groverlab/disintegration-fingerprinting/data/aspirin.png

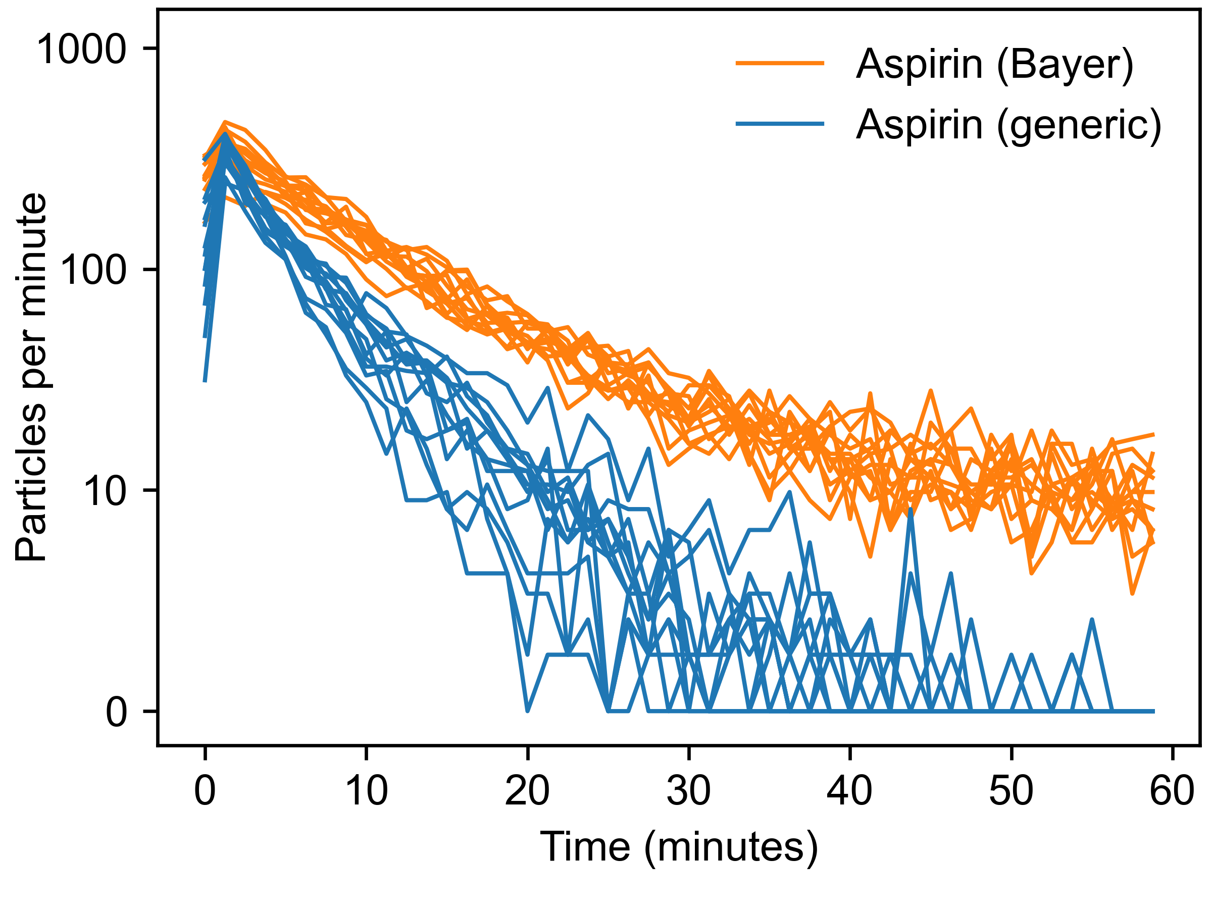
data/aspirin.png
