groverlab/disintegration-fingerprinting/data/aspirin_heatmap.png

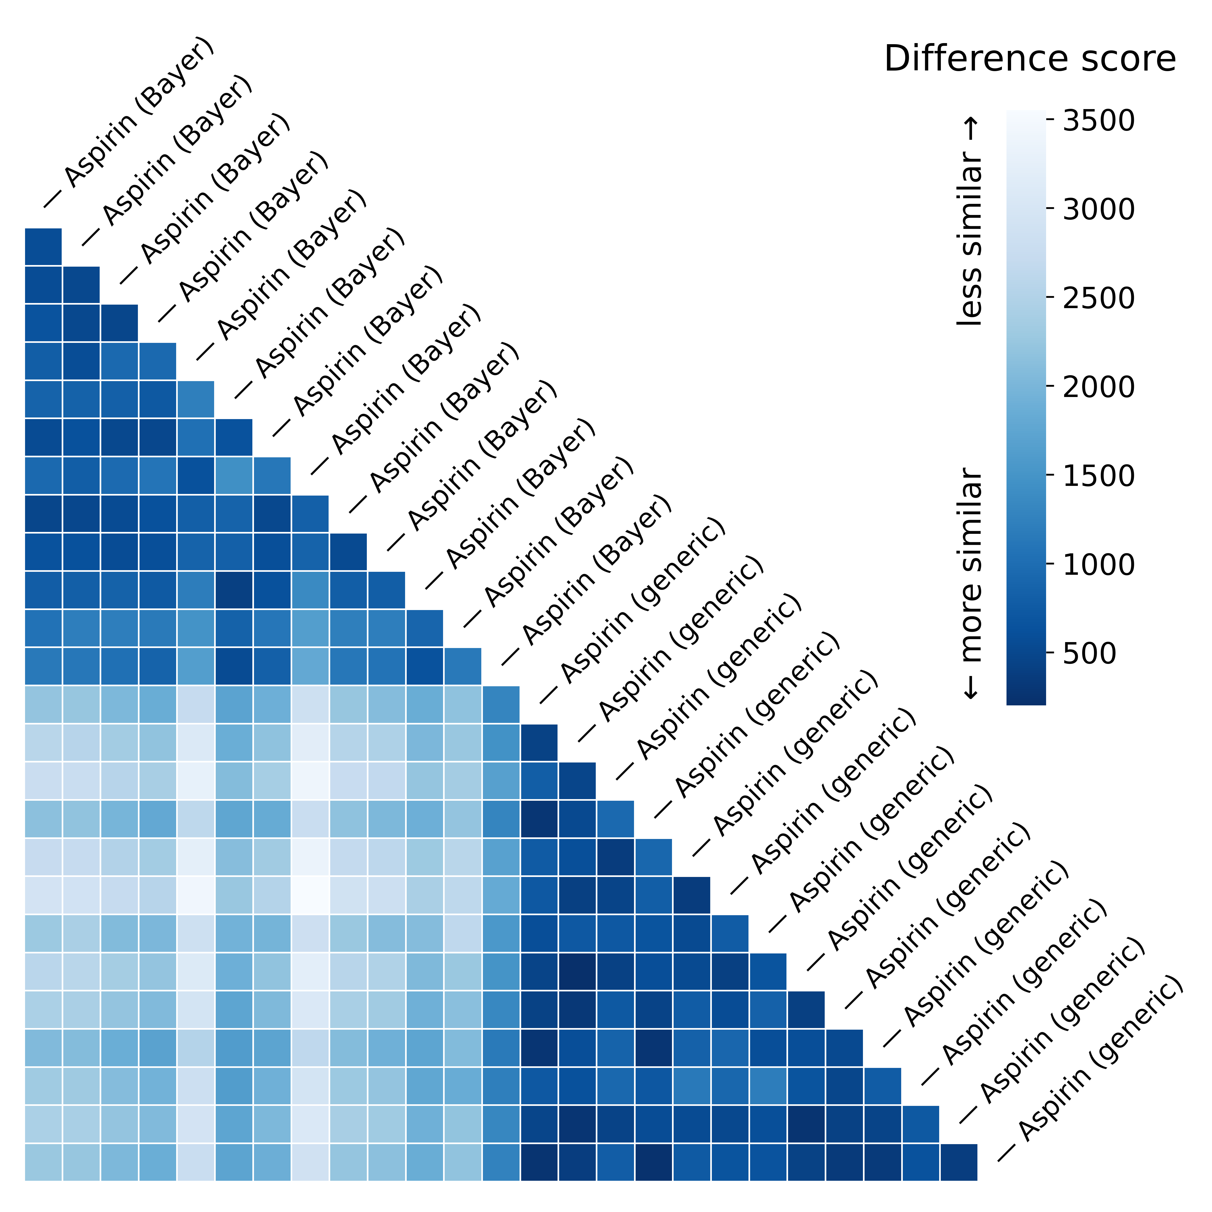
data/aspirin_heatmap.png
