groverlab/disintegration-fingerprinting/data/aspirin_significance.png

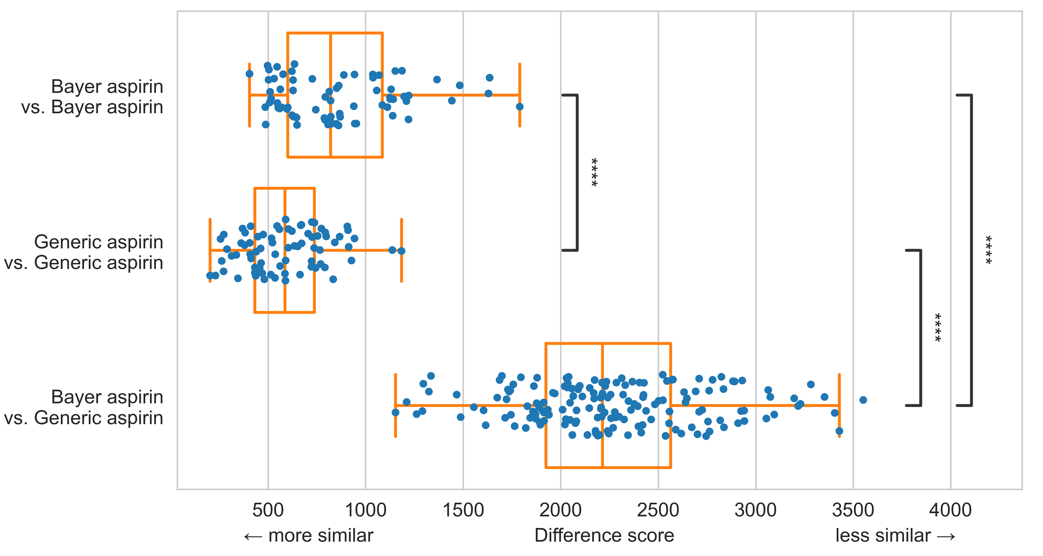
data/aspirin_significance.png
