groverlab/disintegration-fingerprinting/data/bayer_tylenol/101 20251124T124538_T16one TCANADA.json.gz.png

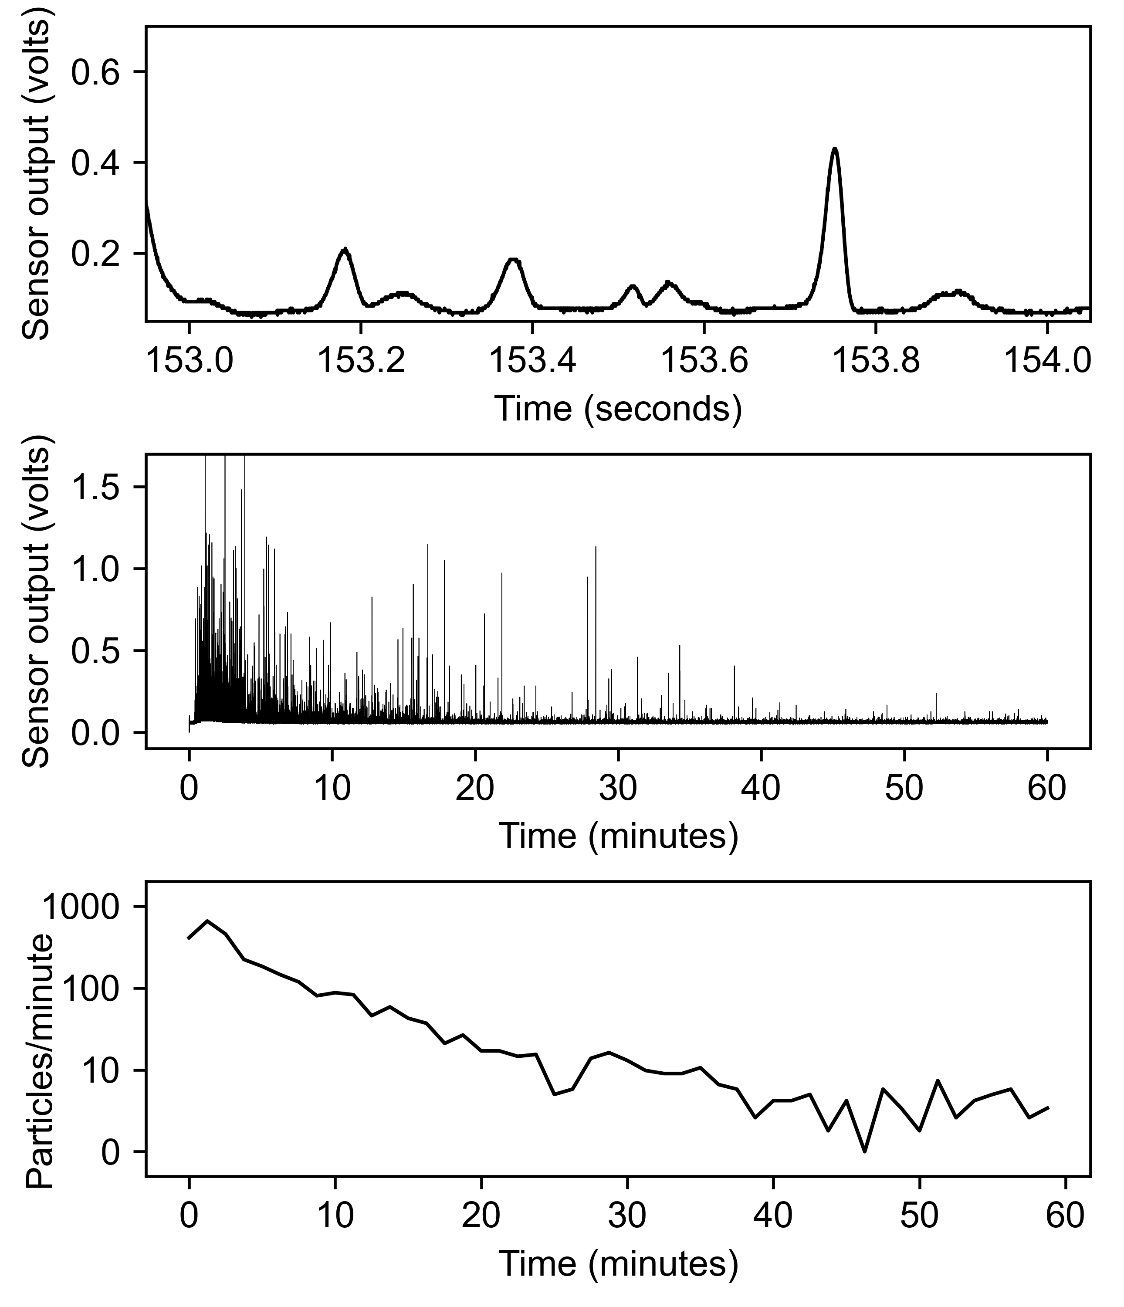
data/bayer_tylenol/101 20251124T124538_T16one TCANADA.json.gz.png
