groverlab/disintegration-fingerprinting/data/bayer_tylenol/102 20251113T170126_T02one TRT.json.gz.png

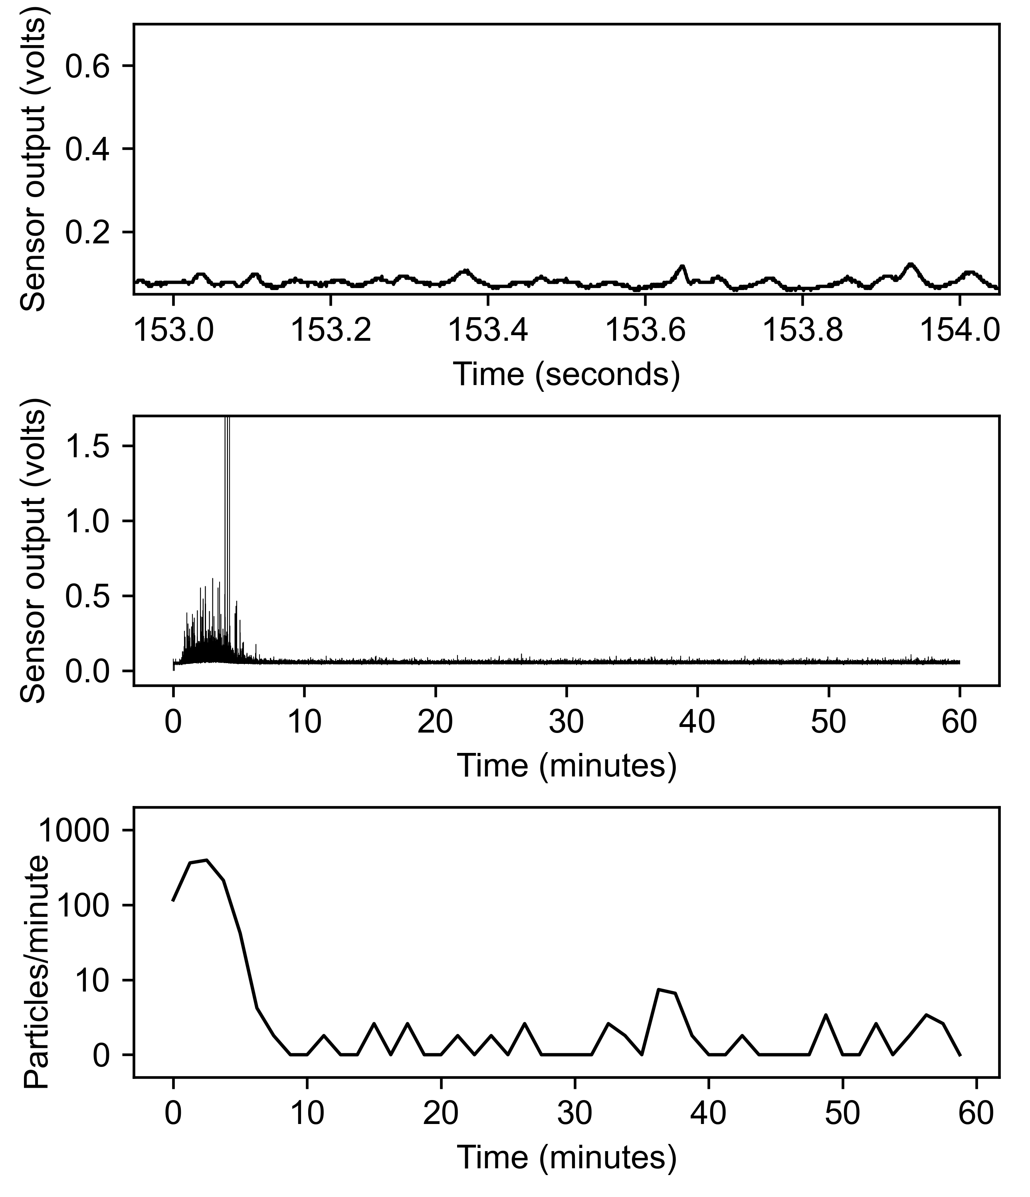
data/bayer_tylenol/102 20251113T170126_T02one TRT.json.gz.png
