groverlab/disintegration-fingerprinting/data/bayer_tylenol/103 20251124T112431_T15one TRT.json.gz.png

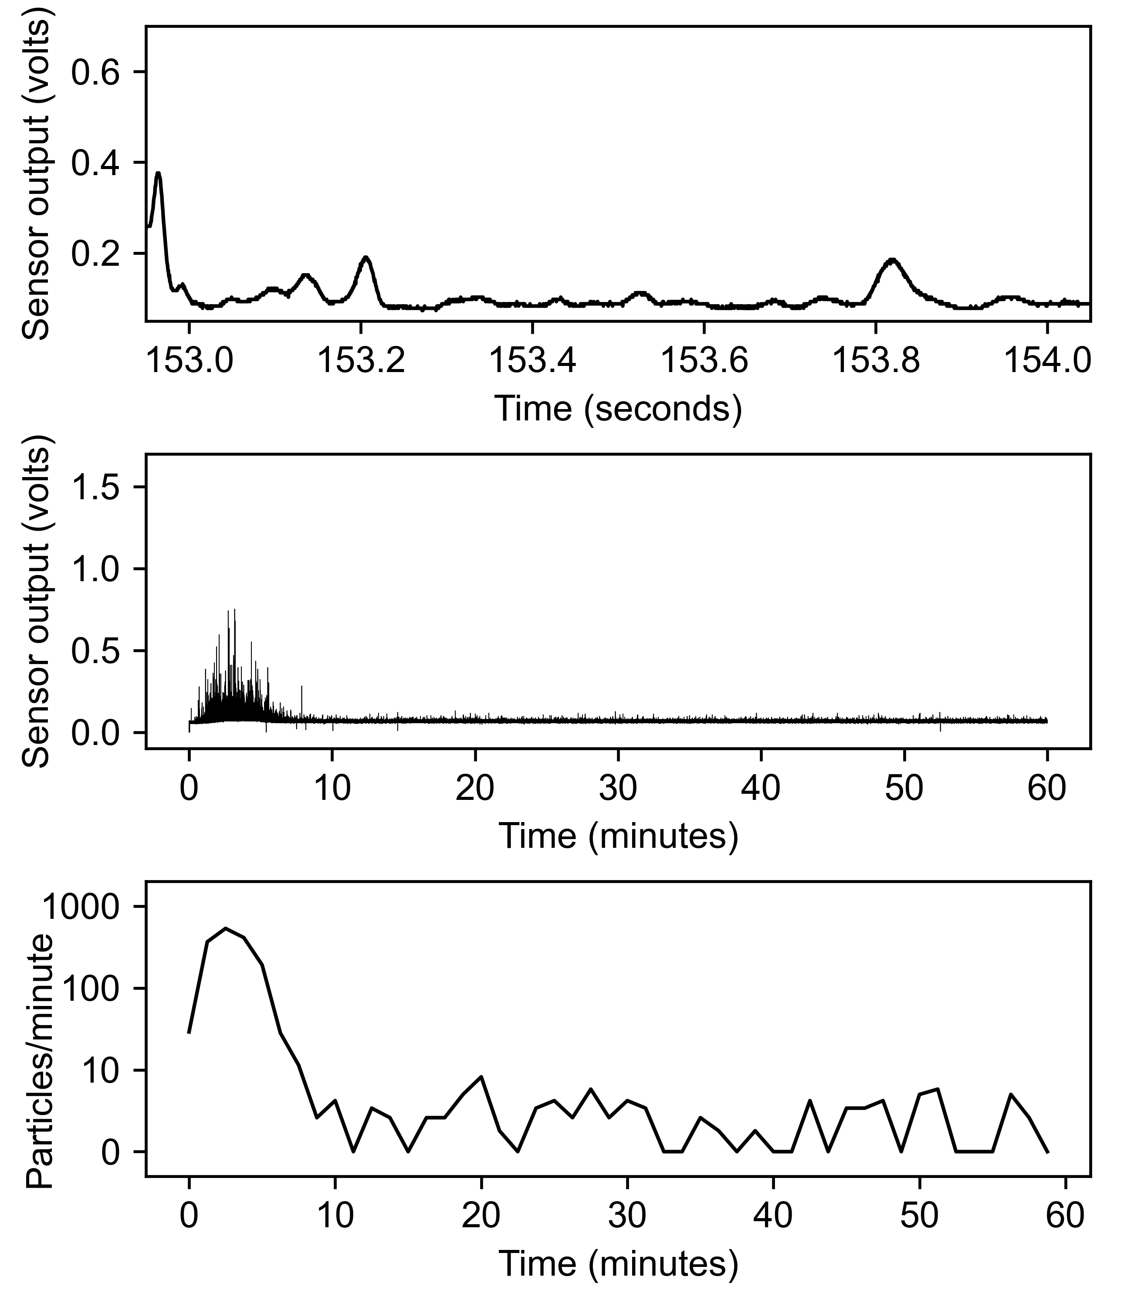
data/bayer_tylenol/103 20251124T112431_T15one TRT.json.gz.png
