groverlab/disintegration-fingerprinting/data/bayer_tylenol/104 20251118T150120_T08one TRT.json.gz.png

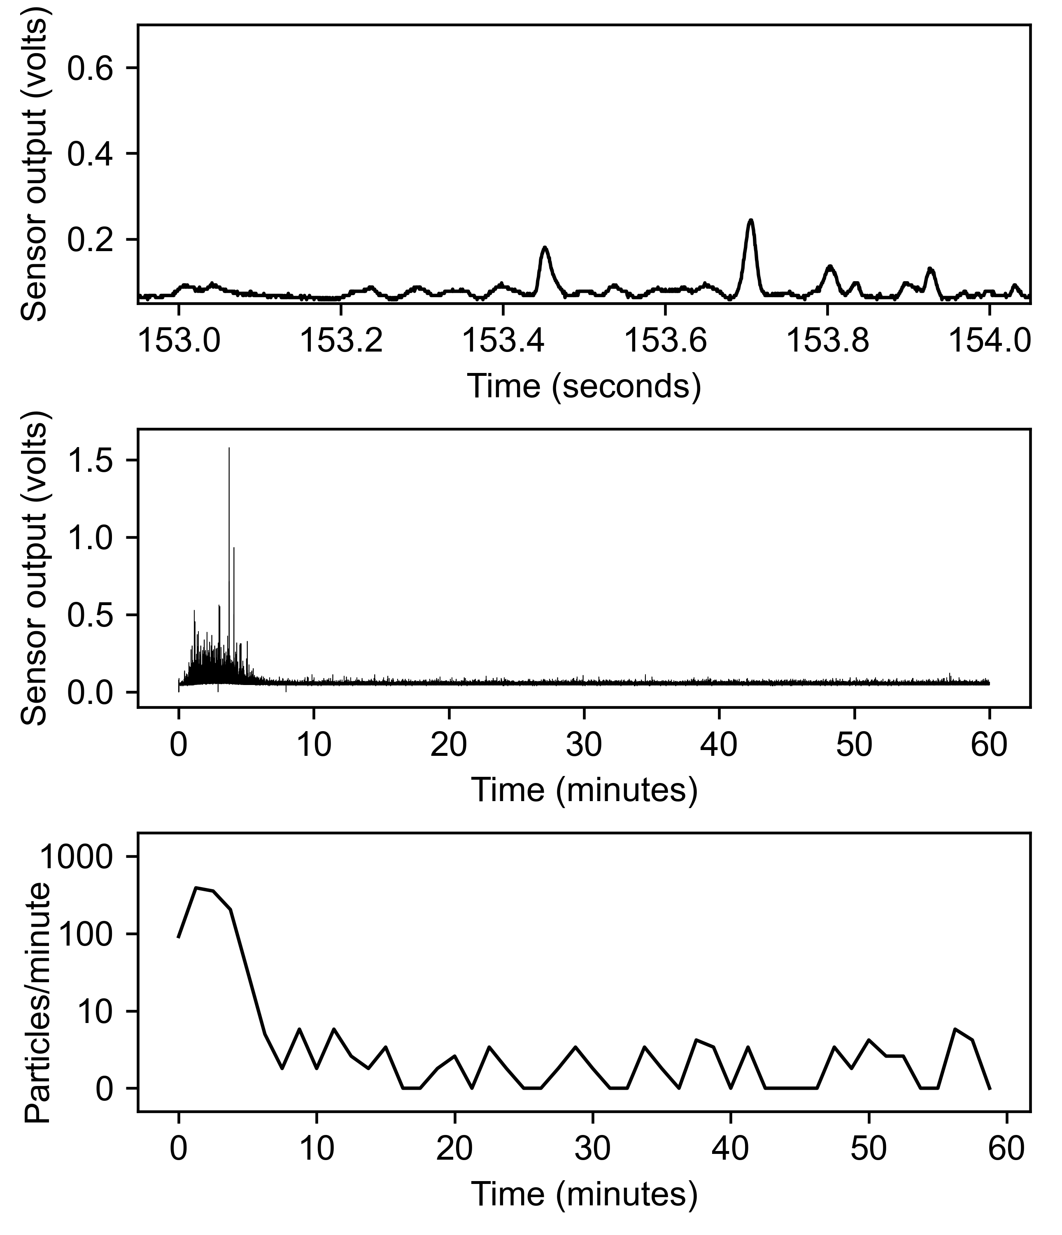
data/bayer_tylenol/104 20251118T150120_T08one TRT.json.gz.png
