groverlab/disintegration-fingerprinting/data/bayer_tylenol/105 20260107T104635_T13two TRT.json.gz.png

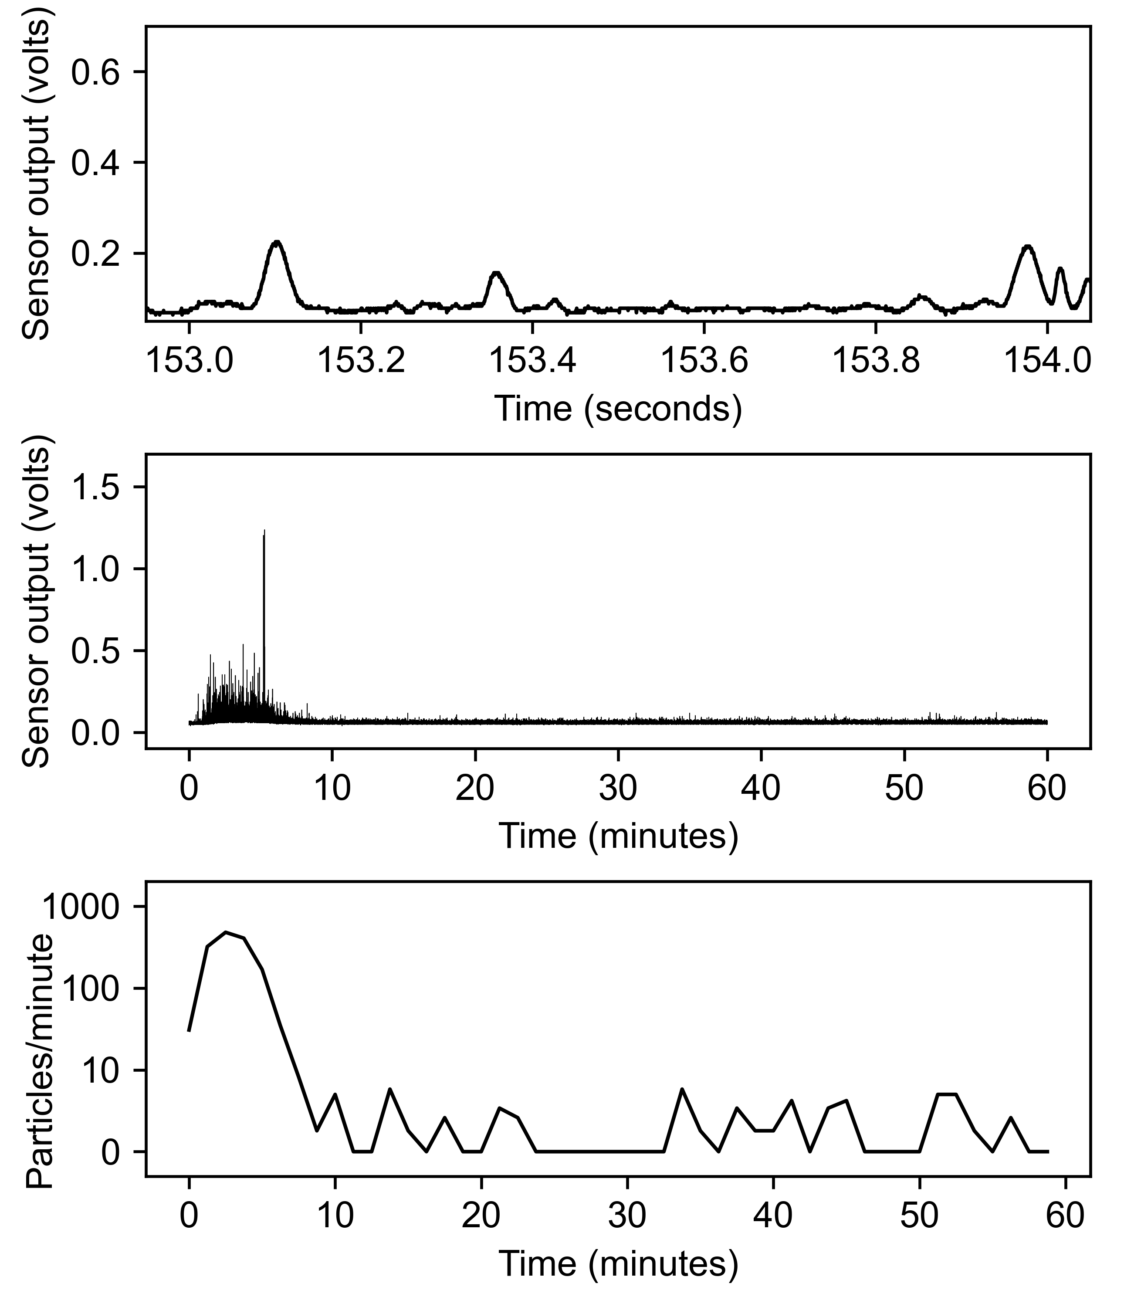
data/bayer_tylenol/105 20260107T104635_T13two TRT.json.gz.png
