groverlab/disintegration-fingerprinting/data/bayer_tylenol/106 20251117T124159_T05one TRT.json.gz.png

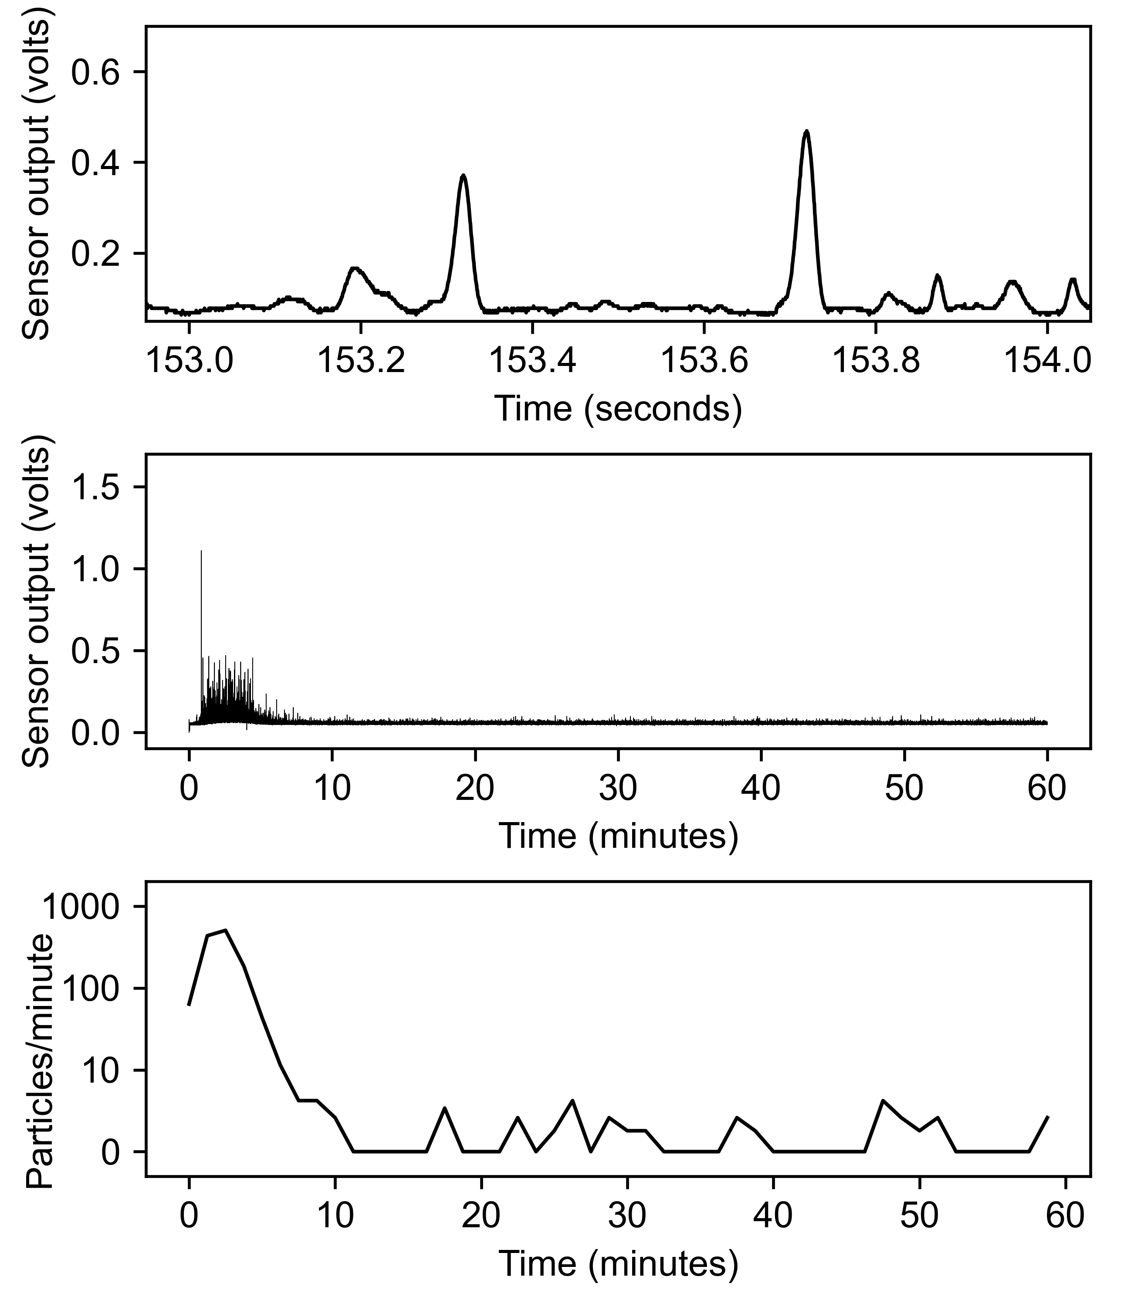
data/bayer_tylenol/106 20251117T124159_T05one TRT.json.gz.png
