groverlab/disintegration-fingerprinting/data/bayer_tylenol/107 20251118T134538_T07one TRT.json.gz.png

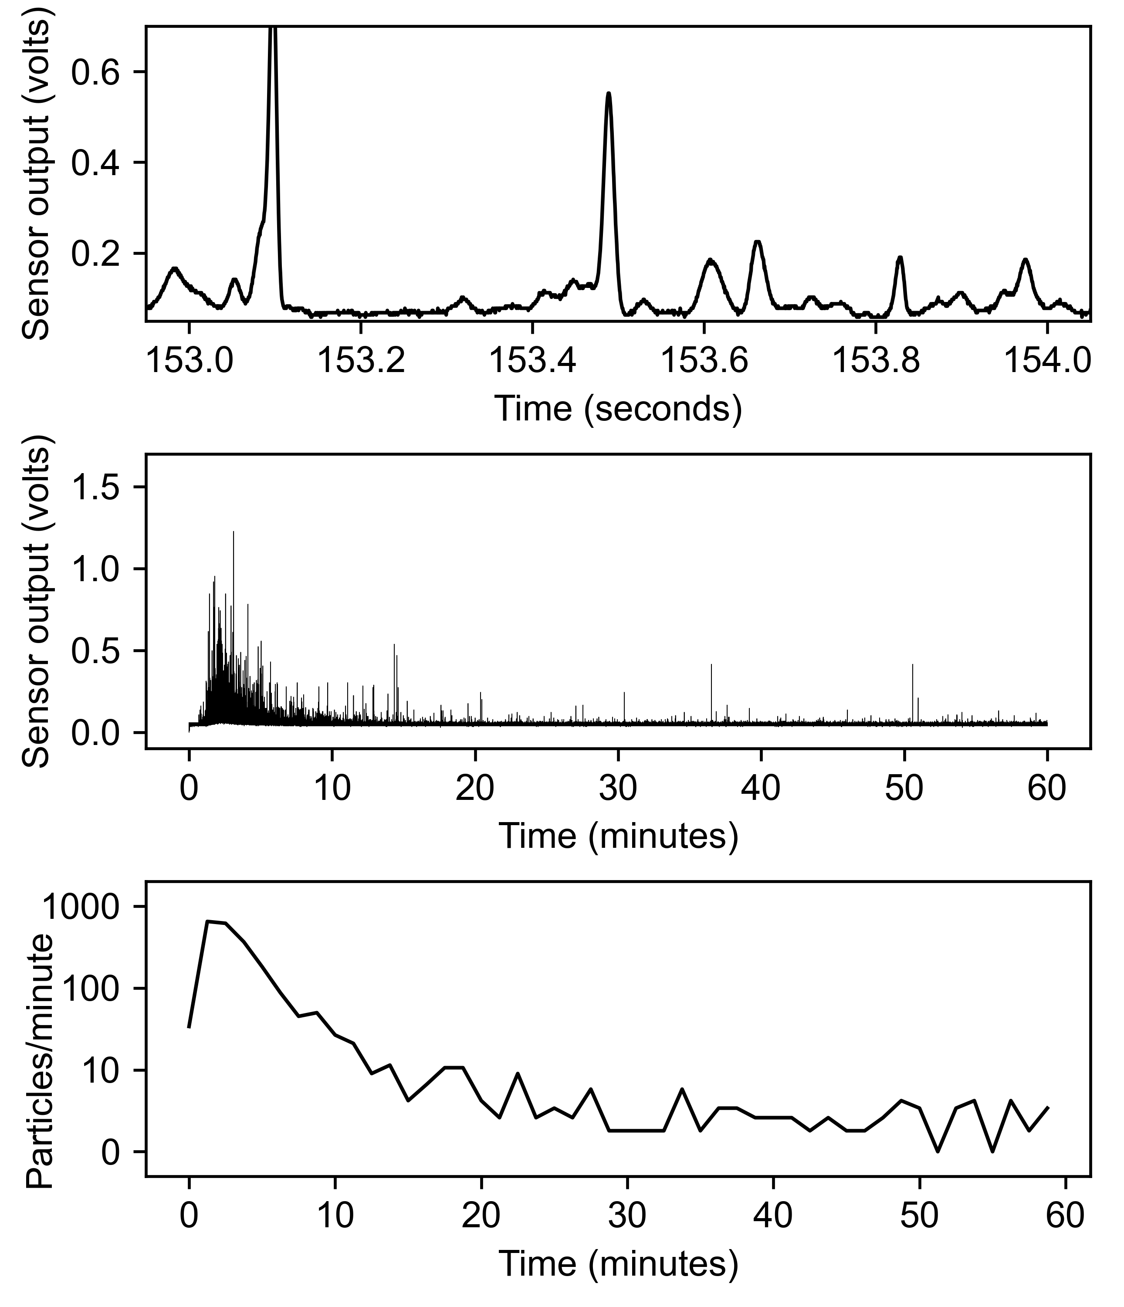
data/bayer_tylenol/107 20251118T134538_T07one TRT.json.gz.png
