groverlab/disintegration-fingerprinting/data/bayer_tylenol/108 20251124T135557_T17one TCANADA.json.gz.png

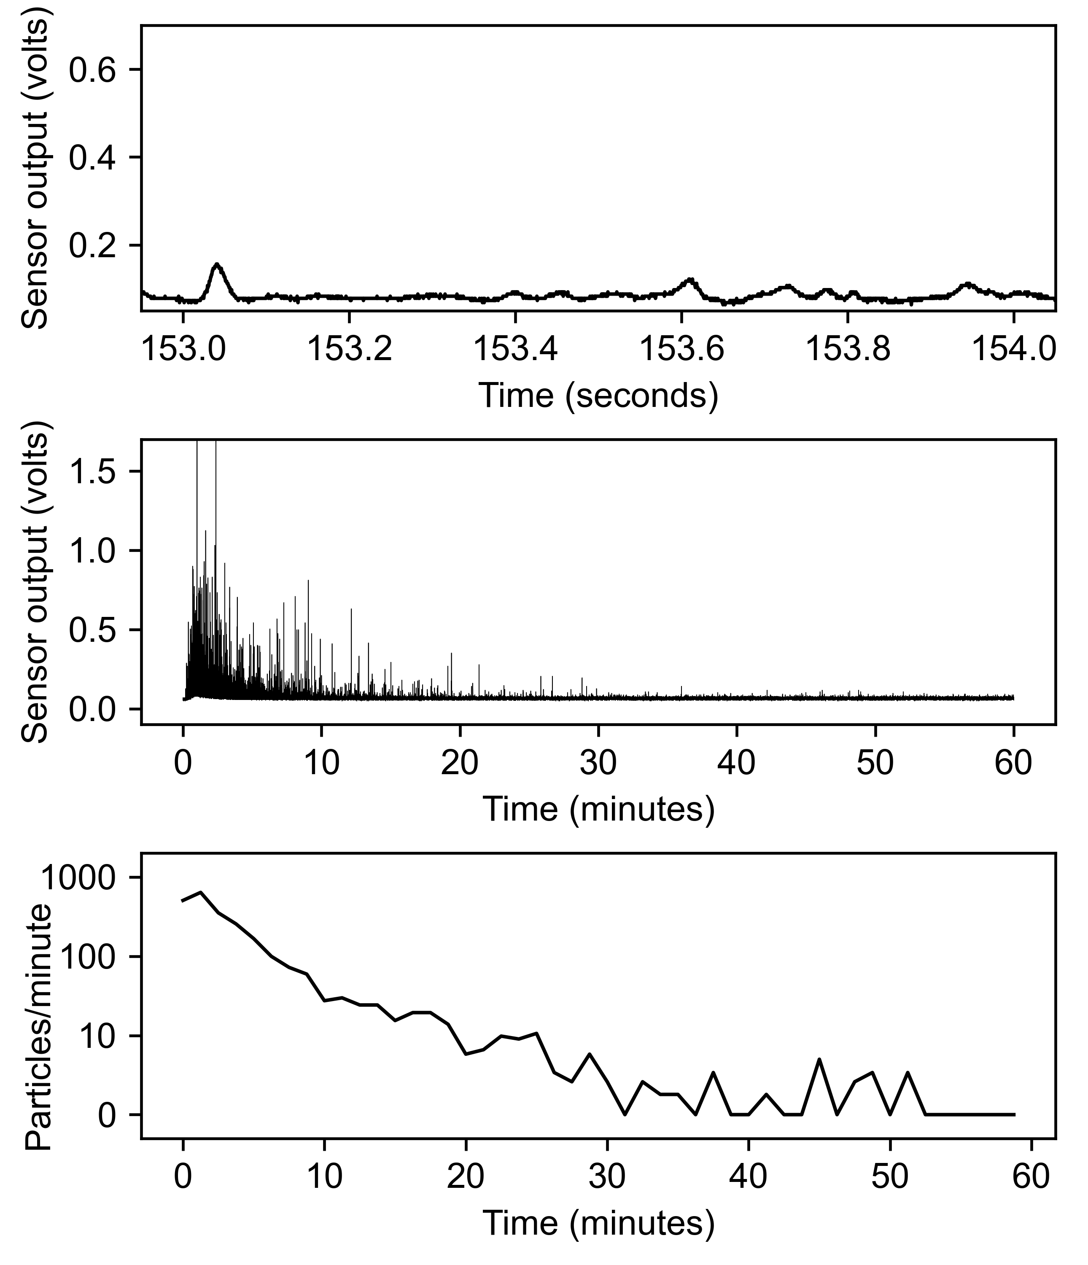
data/bayer_tylenol/108 20251124T135557_T17one TCANADA.json.gz.png
