groverlab/disintegration-fingerprinting/data/bayer_tylenol/109 20251118T123829_T06one TRT.json.gz.png

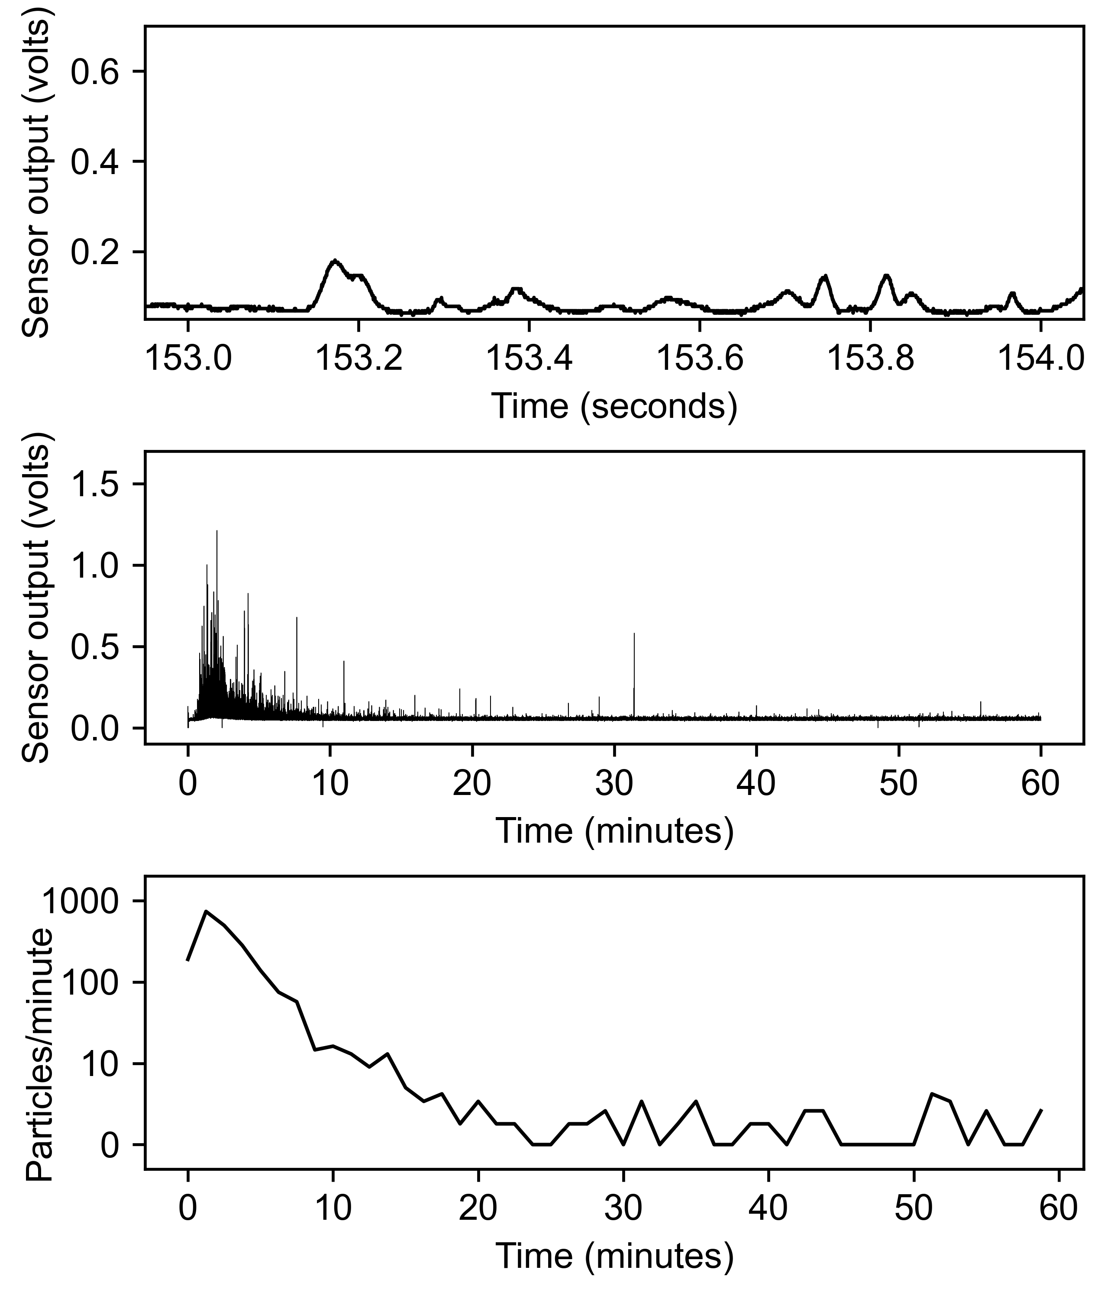
data/bayer_tylenol/109 20251118T123829_T06one TRT.json.gz.png
