groverlab/disintegration-fingerprinting/data/bayer_tylenol/110 20251117T112834_T04one TRT.json.gz.png

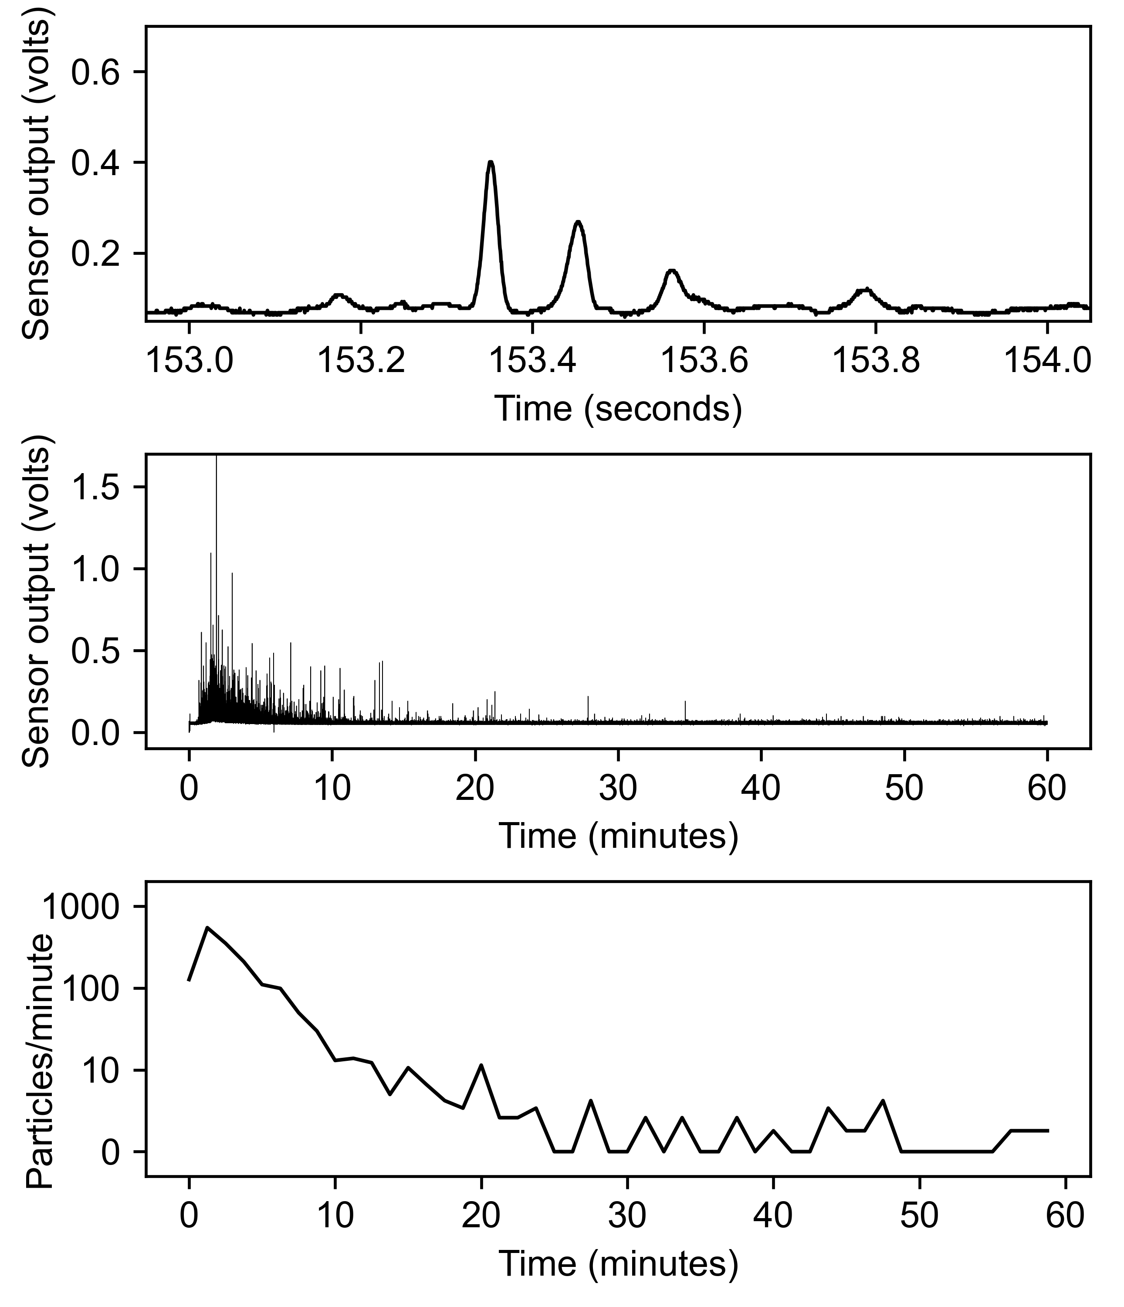
data/bayer_tylenol/110 20251117T112834_T04one TRT.json.gz.png
