groverlab/disintegration-fingerprinting/data/bayer_tylenol/111 20251120T111520_T14one TRT.json.gz.png

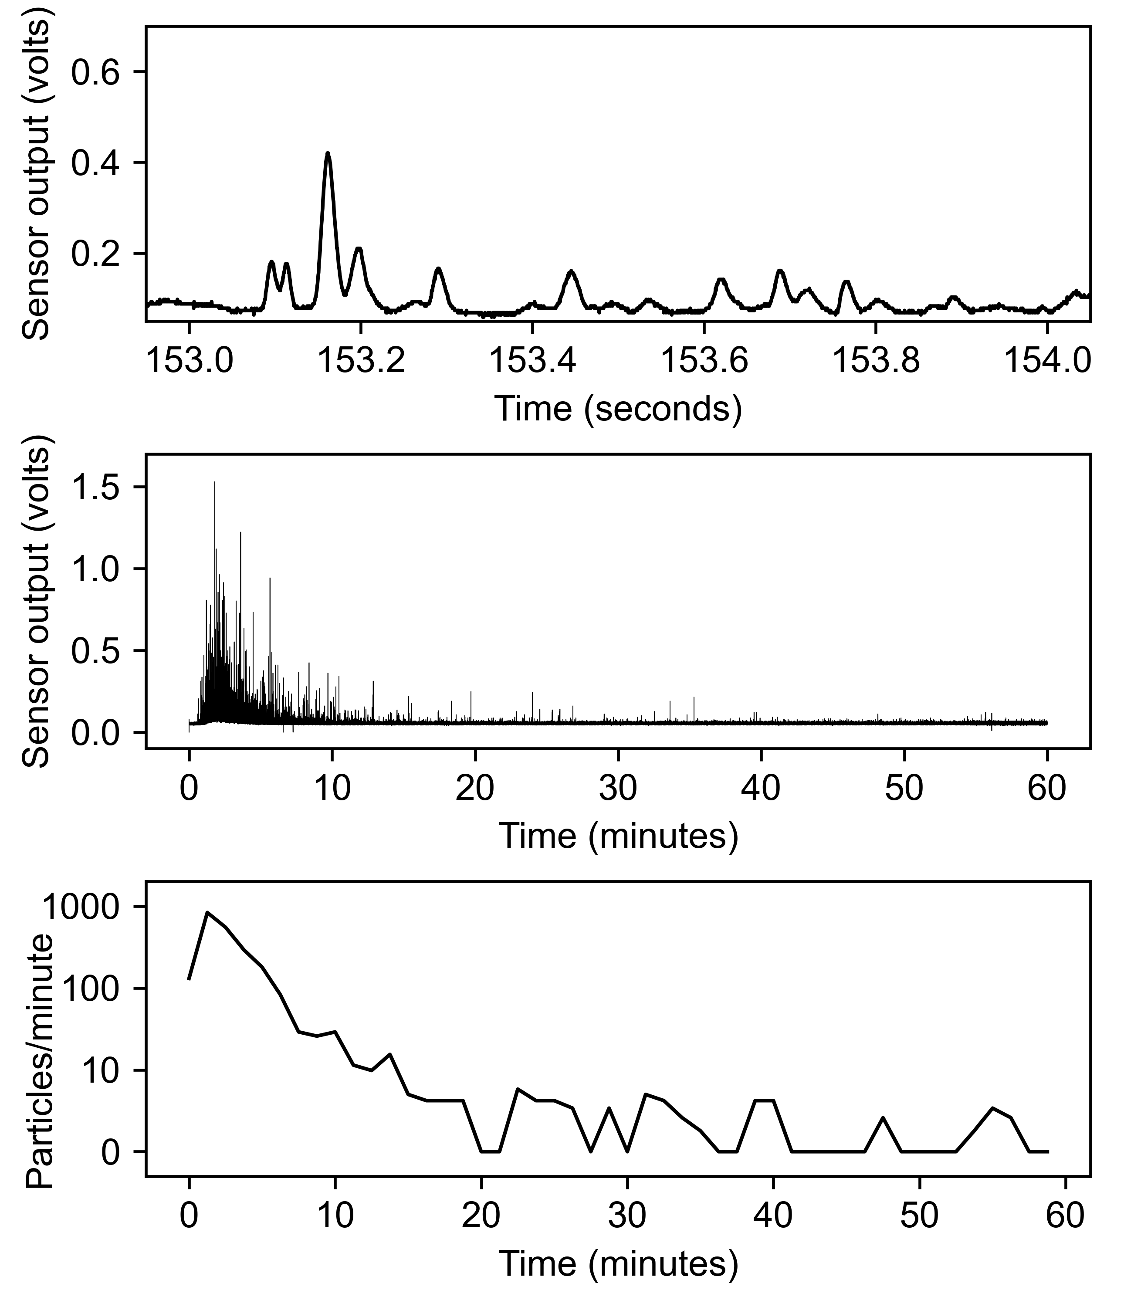
data/bayer_tylenol/111 20251120T111520_T14one TRT.json.gz.png
