groverlab/disintegration-fingerprinting/data/bayer_tylenol/112 20251119T131818_T11one TRT.json.gz.png

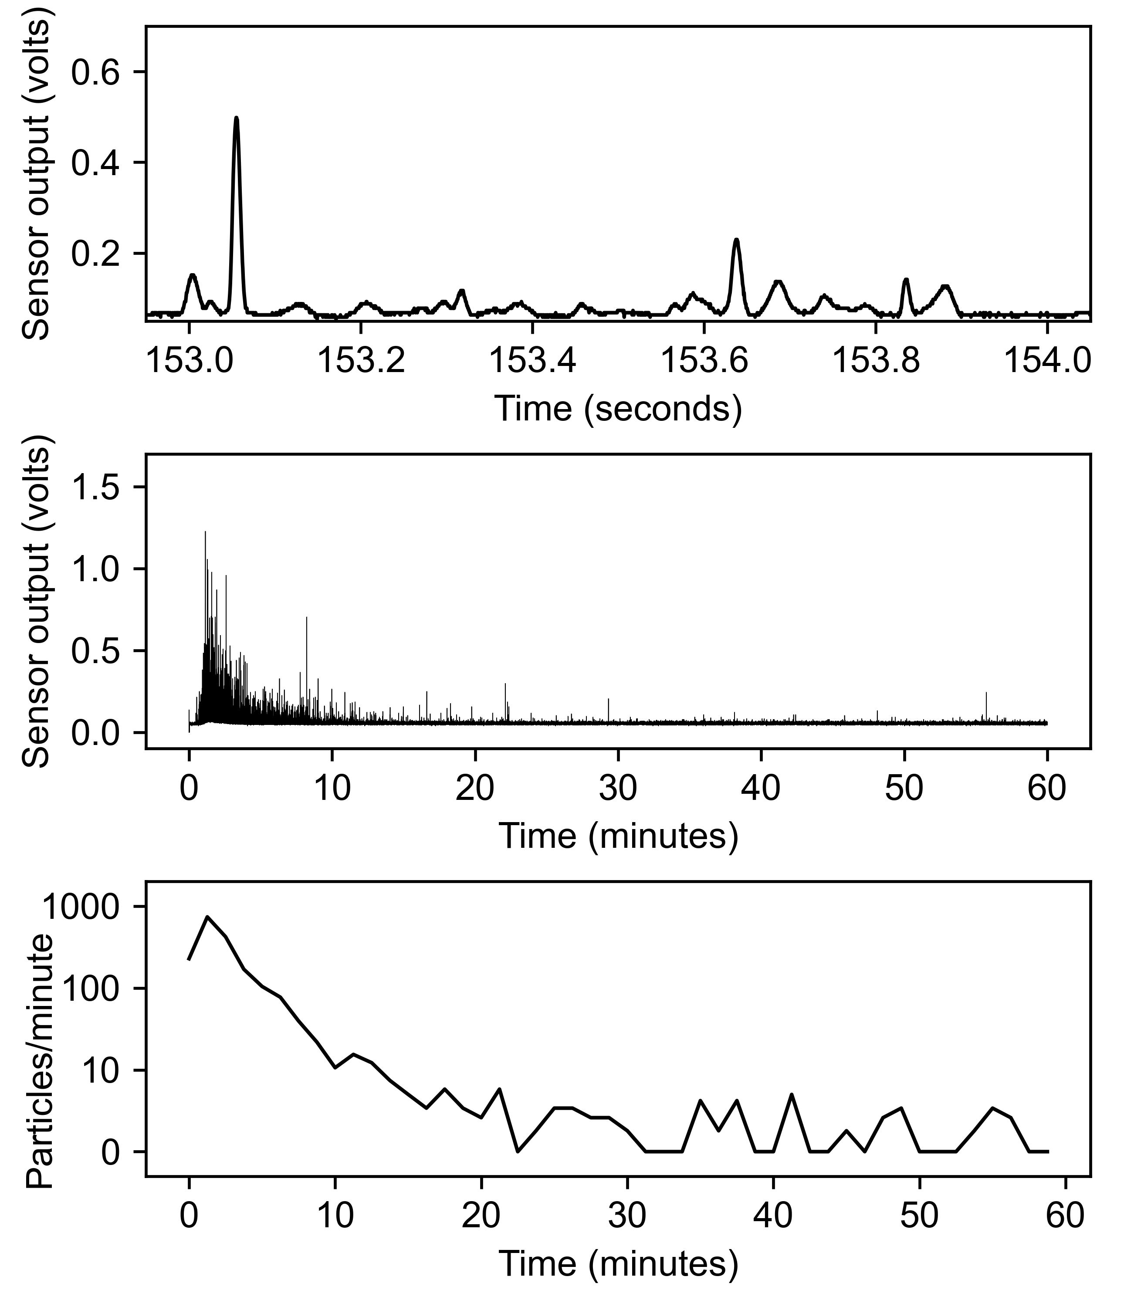
data/bayer_tylenol/112 20251119T131818_T11one TRT.json.gz.png
