groverlab/disintegration-fingerprinting/data/bayer_tylenol/113 20251117T101939_T03one TRT.json.gz.png

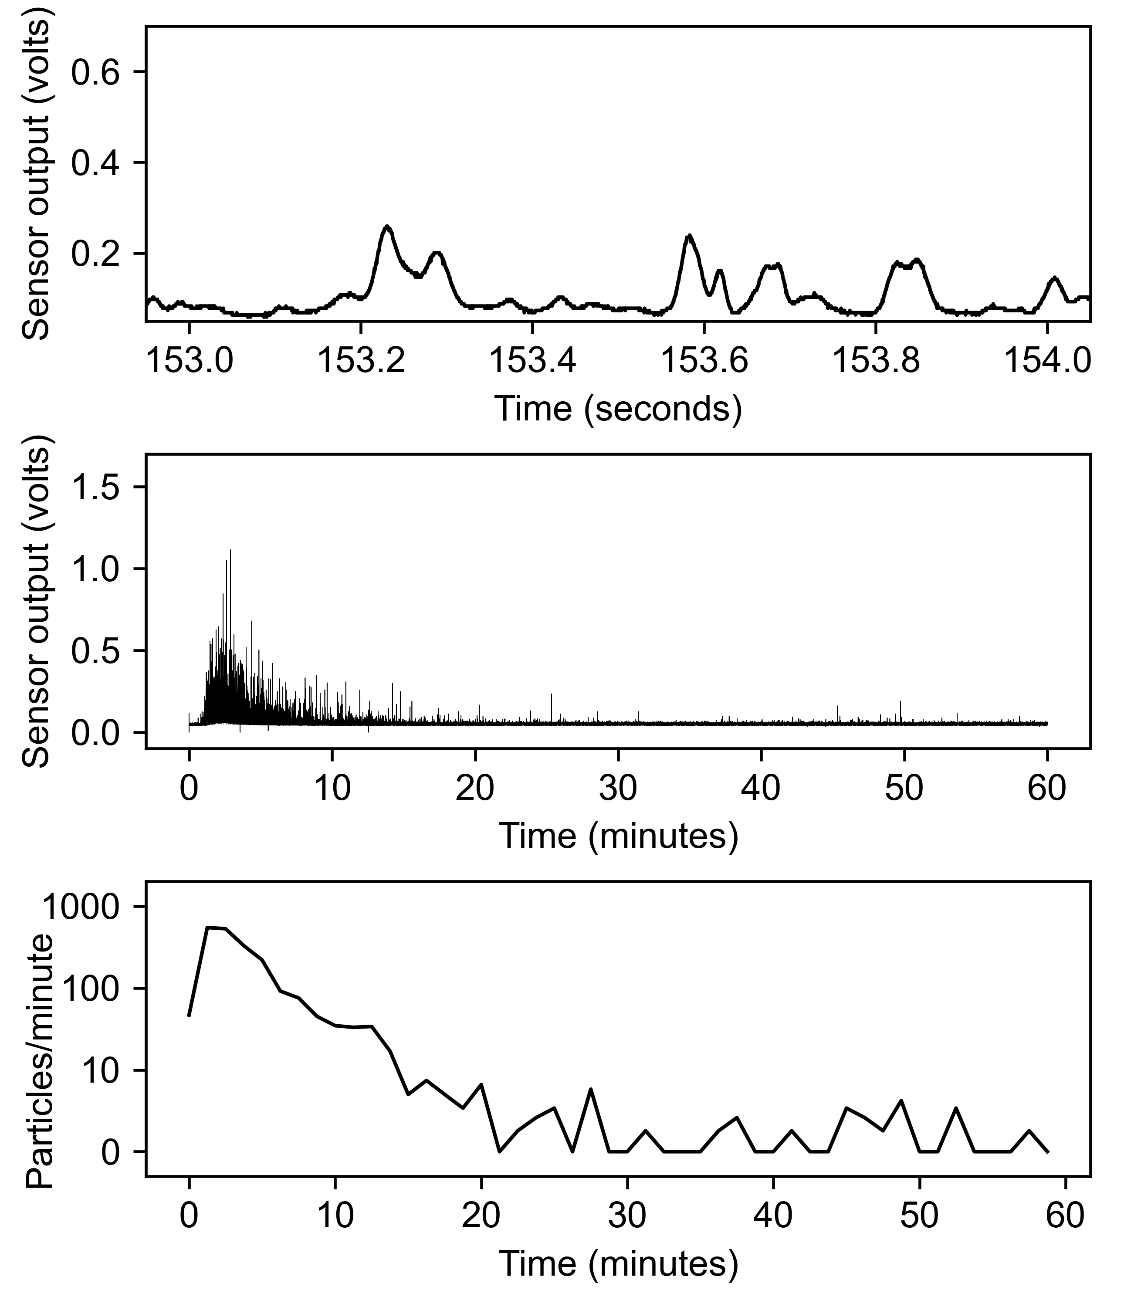
data/bayer_tylenol/113 20251117T101939_T03one TRT.json.gz.png
