groverlab/disintegration-fingerprinting/data/bayer_tylenol/115 20251118T160812_T09one TRT.json.gz.png

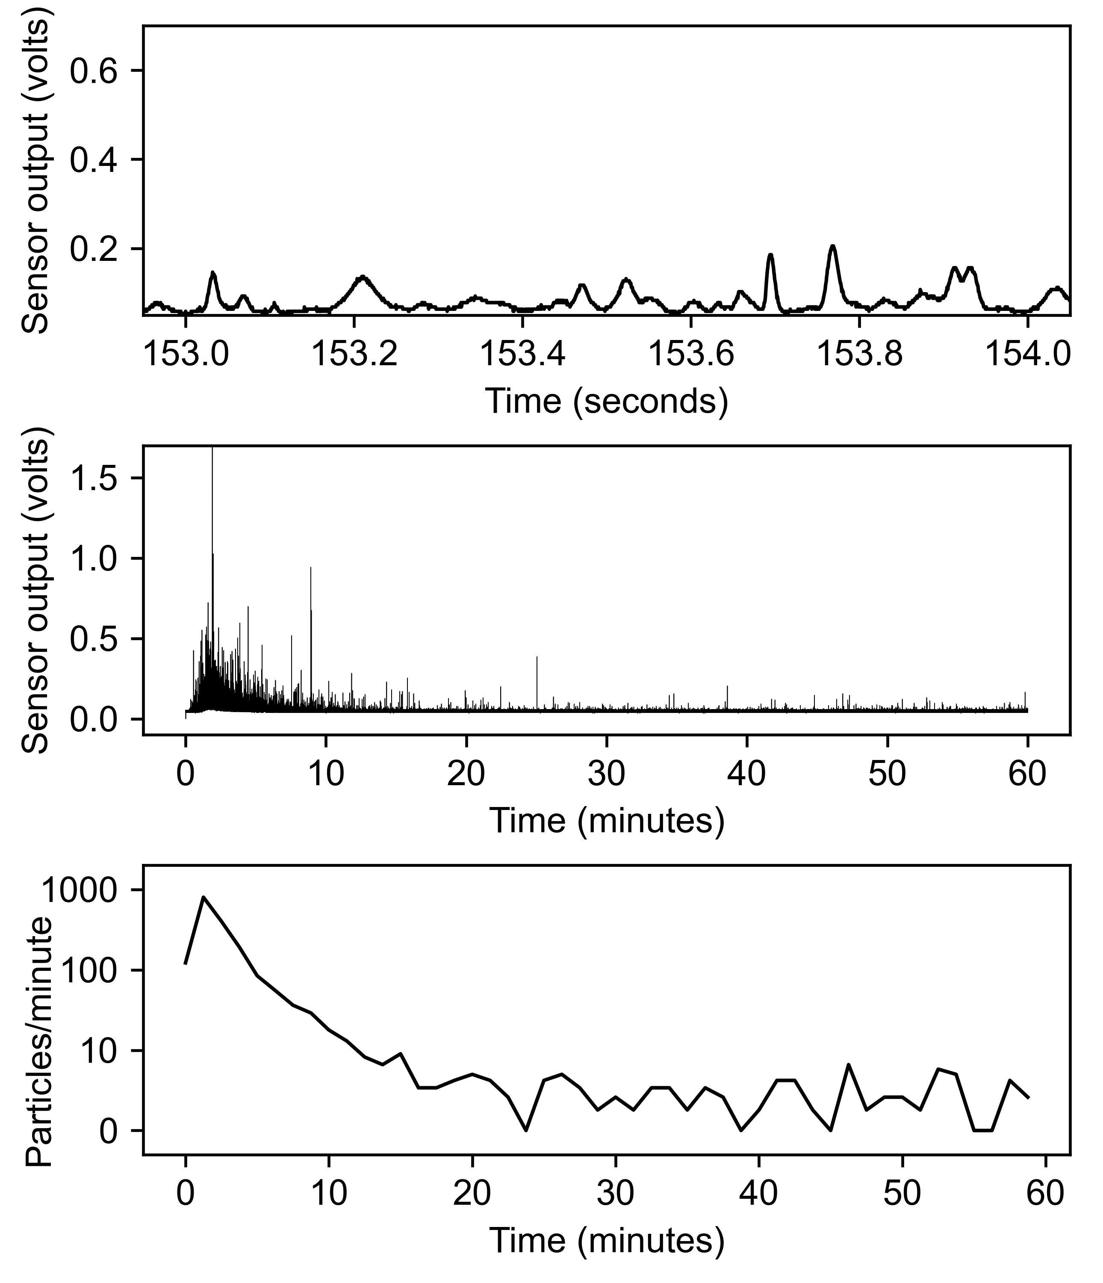
data/bayer_tylenol/115 20251118T160812_T09one TRT.json.gz.png
