groverlab/disintegration-fingerprinting/data/bayer_tylenol/116 20251119T121001_T10one TRT.json.gz.png

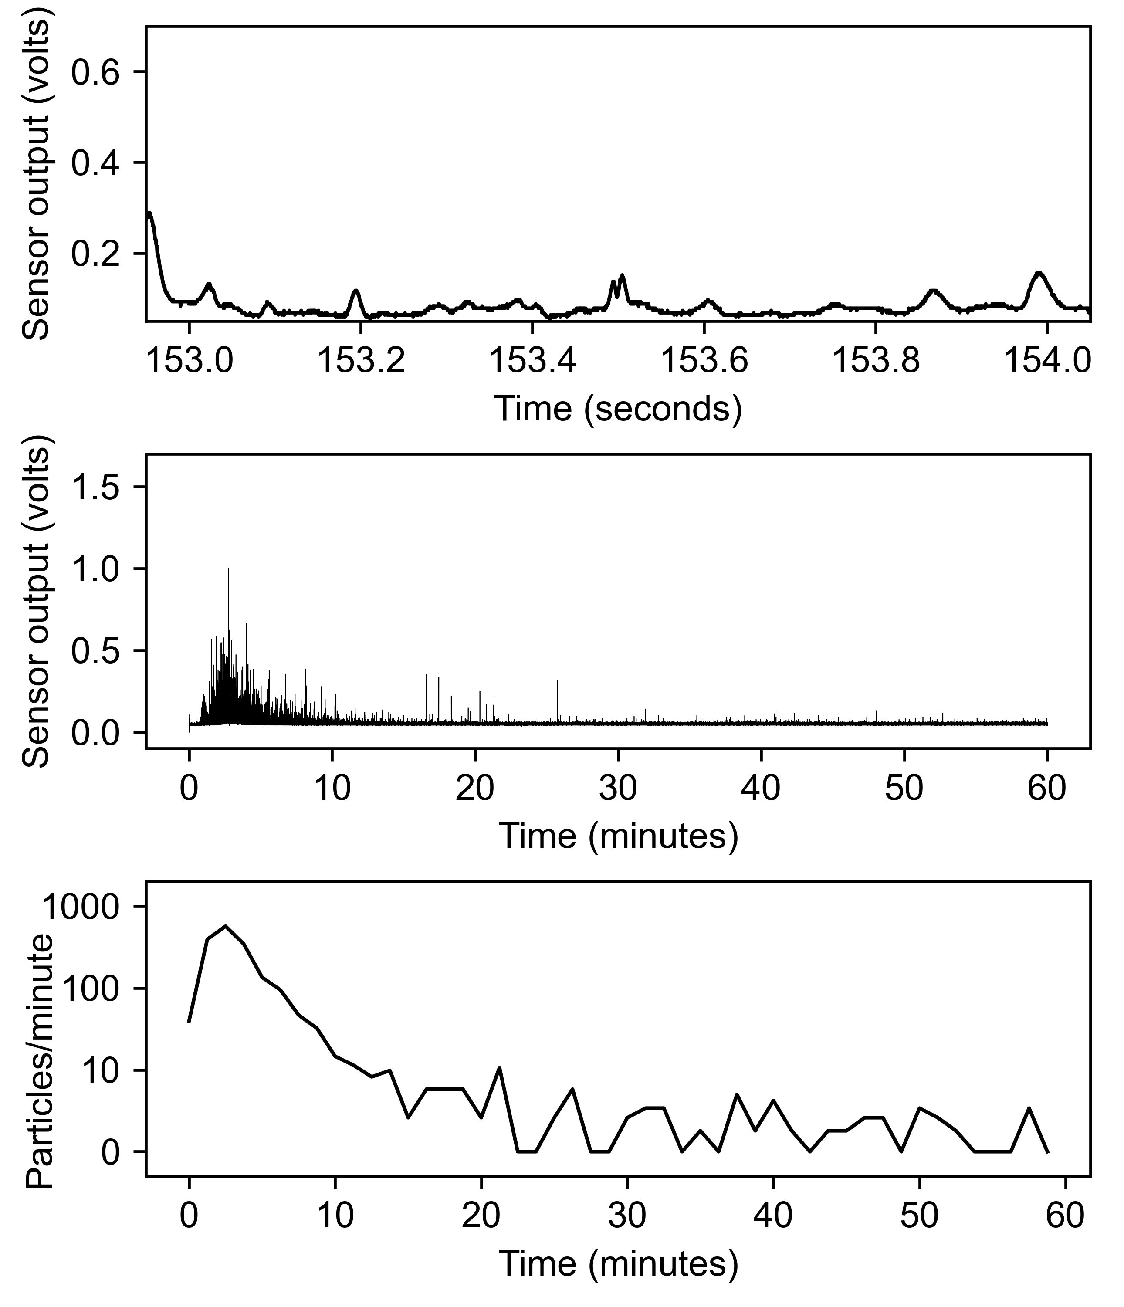
data/bayer_tylenol/116 20251119T121001_T10one TRT.json.gz.png
