groverlab/disintegration-fingerprinting/data/bayer_tylenol/118 20260114T121643_T18one TRT.json.gz.png

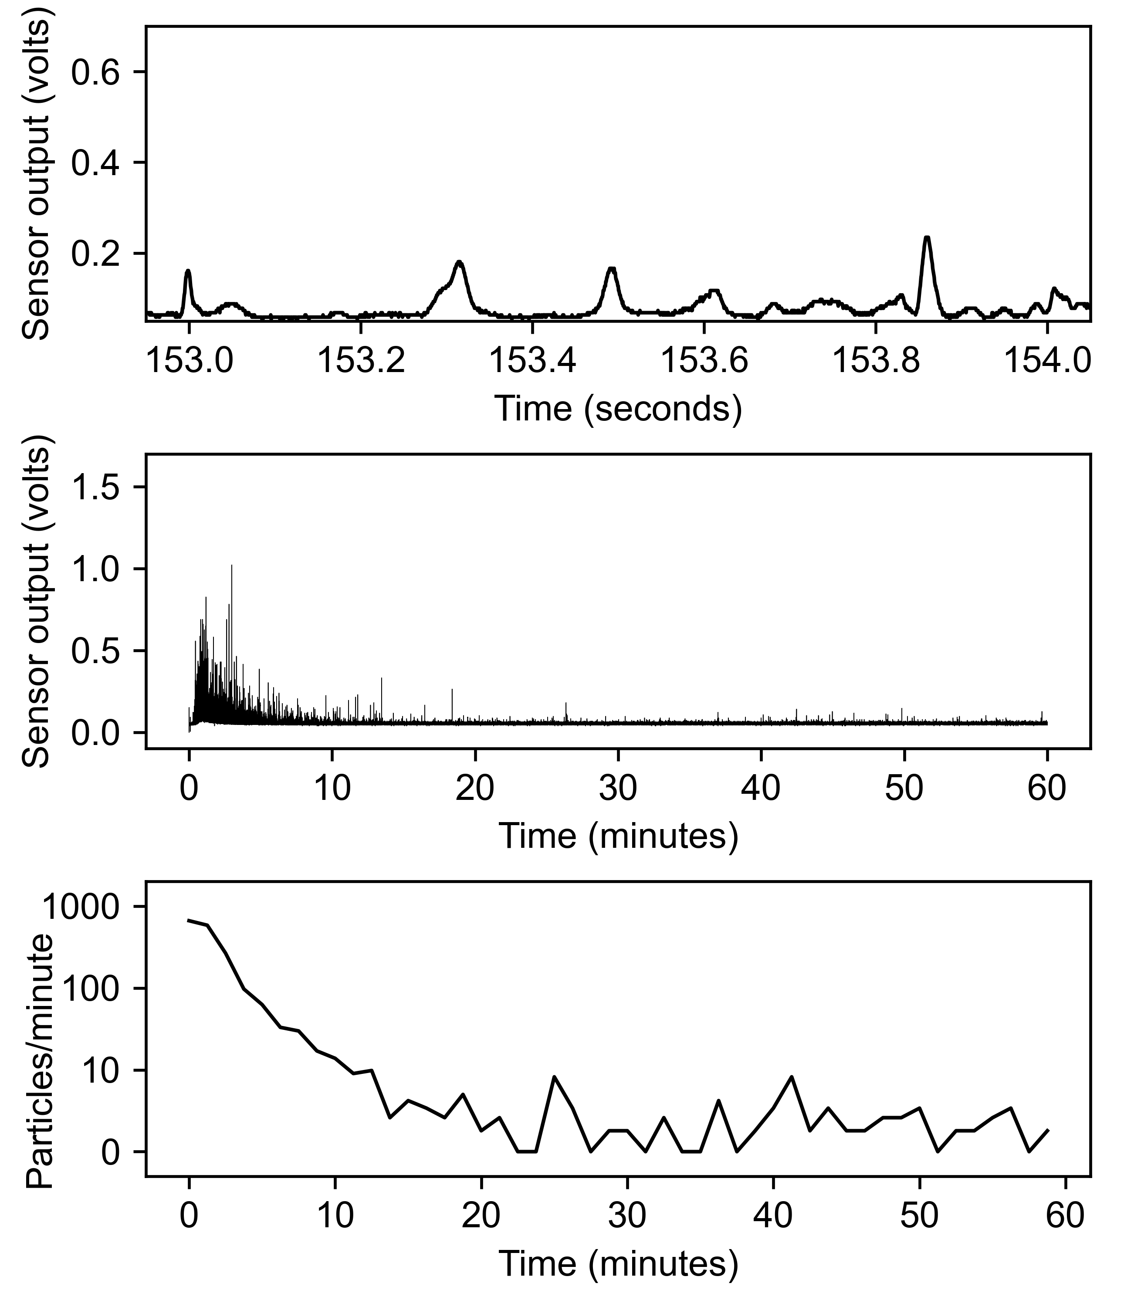
data/bayer_tylenol/118 20260114T121643_T18one TRT.json.gz.png
