groverlab/disintegration-fingerprinting/data/bayer_tylenol/150 20251210T103434_T06 THOT 1.json.gz.png

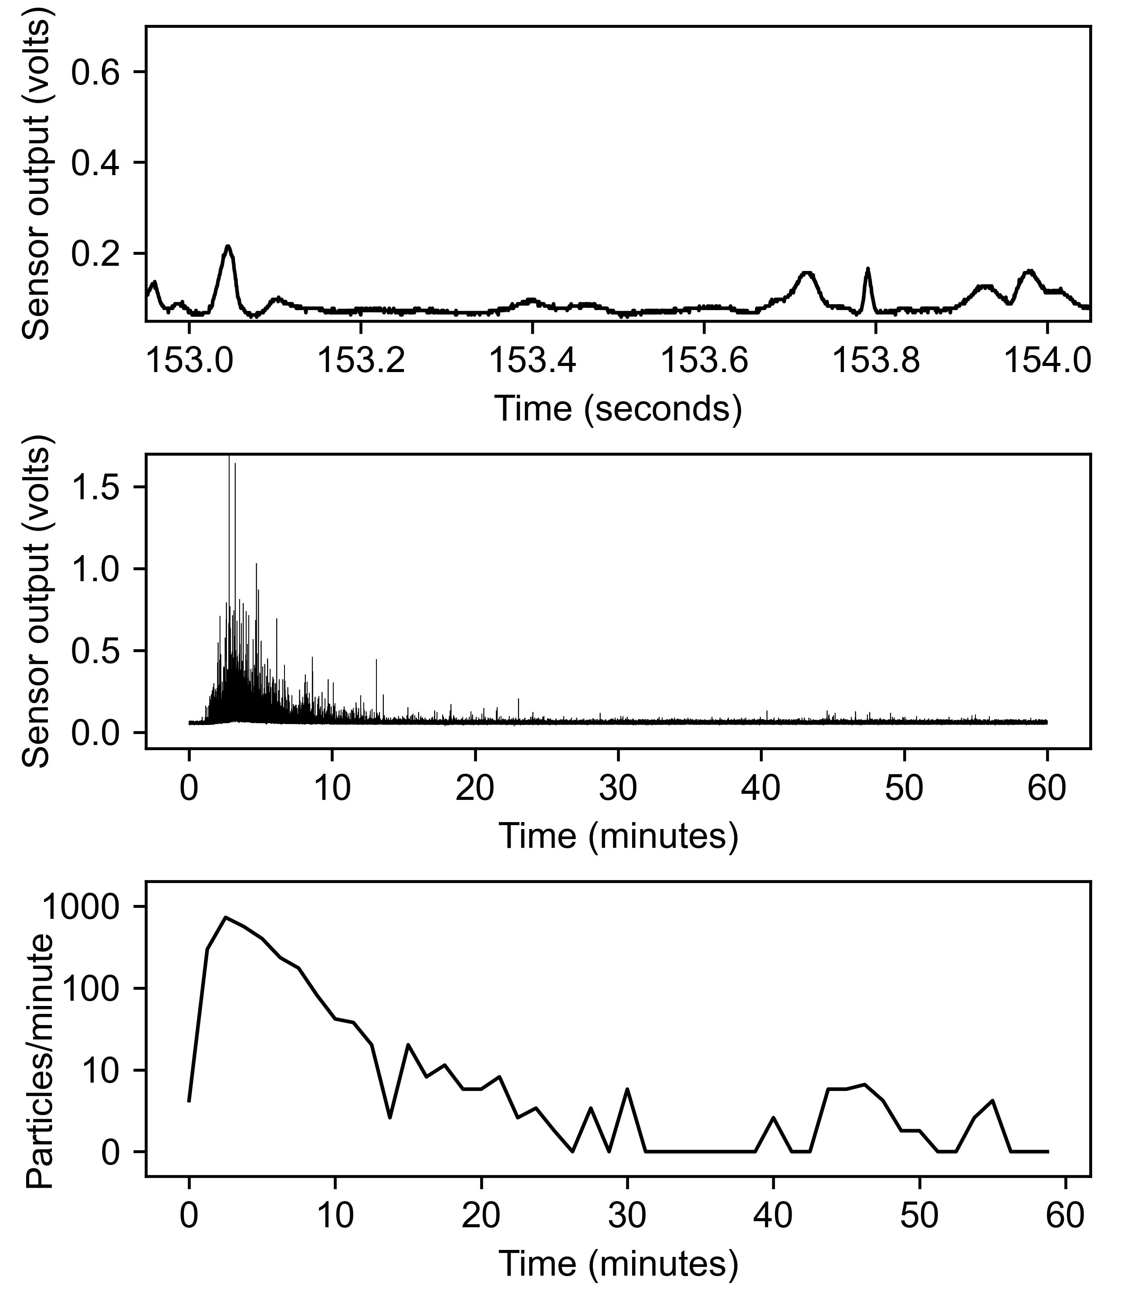
data/bayer_tylenol/150 20251210T103434_T06 THOT 1.json.gz.png
