groverlab/disintegration-fingerprinting/data/bayer_tylenol/151 20251210T114041_T06 THOT 2.json.gz.png

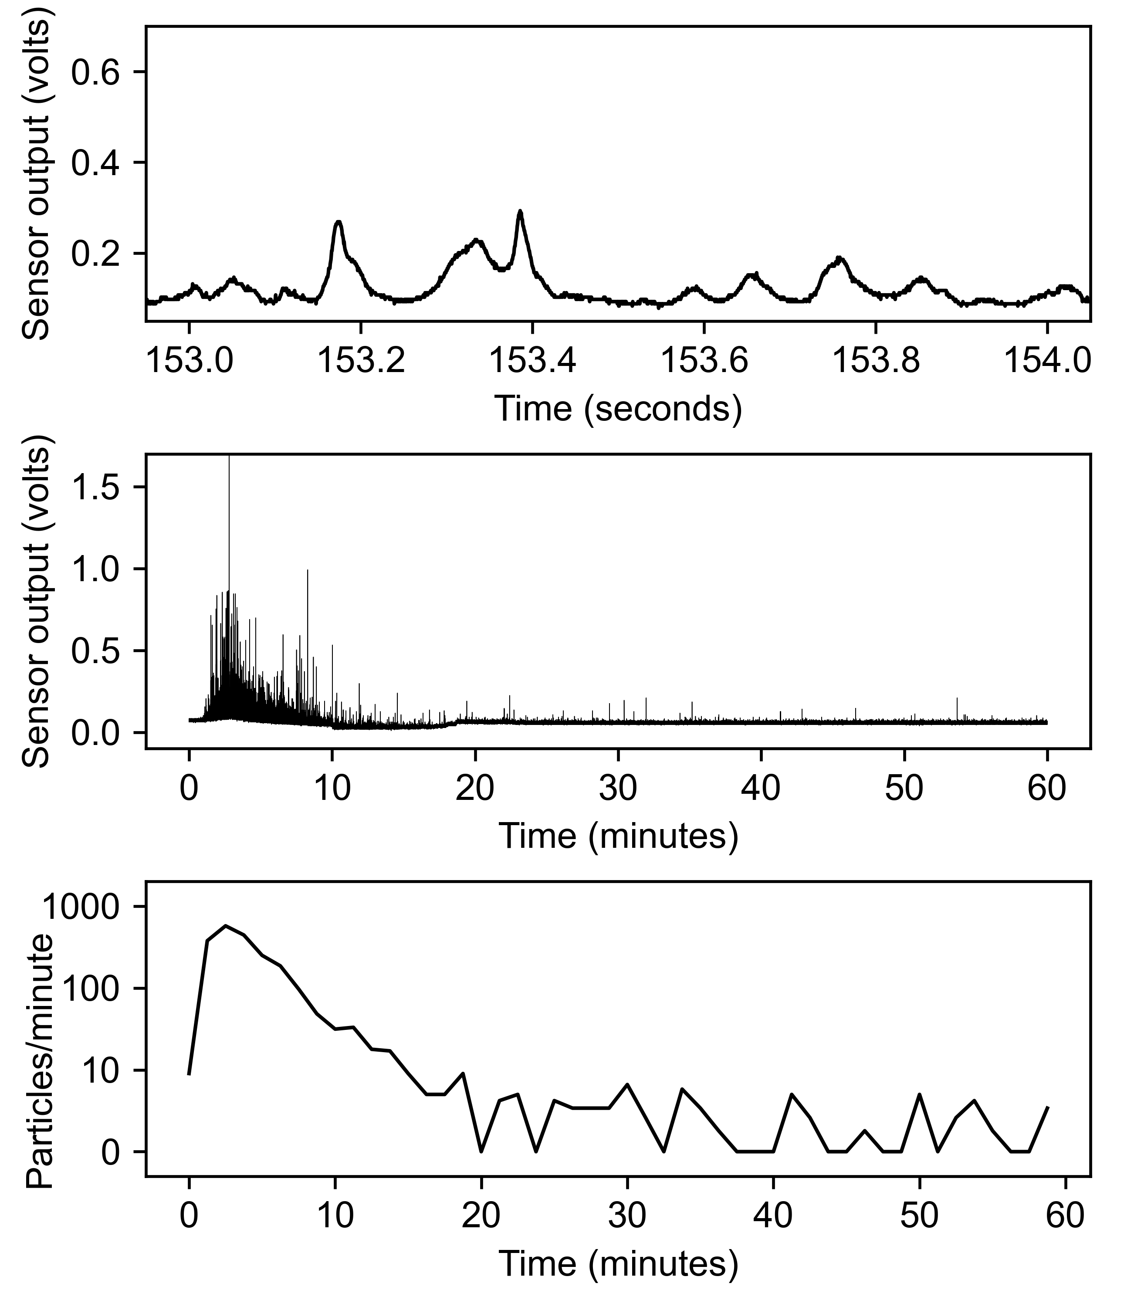
data/bayer_tylenol/151 20251210T114041_T06 THOT 2.json.gz.png
