groverlab/disintegration-fingerprinting/data/bayer_tylenol/152 20251210T124817_T06 THOT 3.json.gz.png

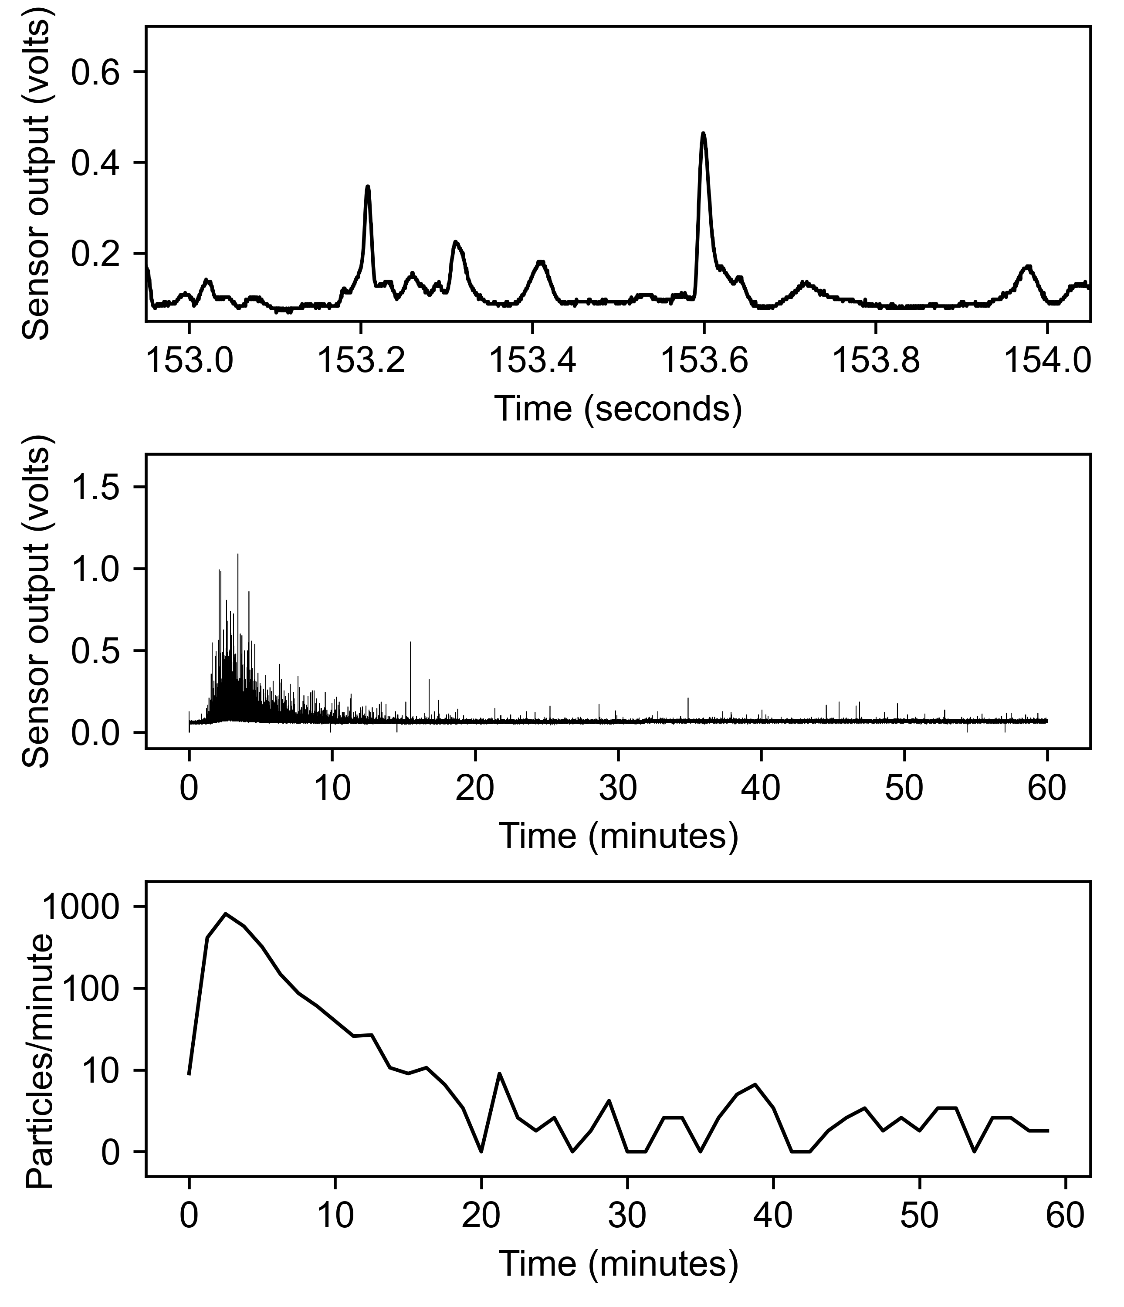
data/bayer_tylenol/152 20251210T124817_T06 THOT 3.json.gz.png
