groverlab/disintegration-fingerprinting/data/bayer_tylenol/153 20251210T135456_T06 TCOLD 1.json.gz.png

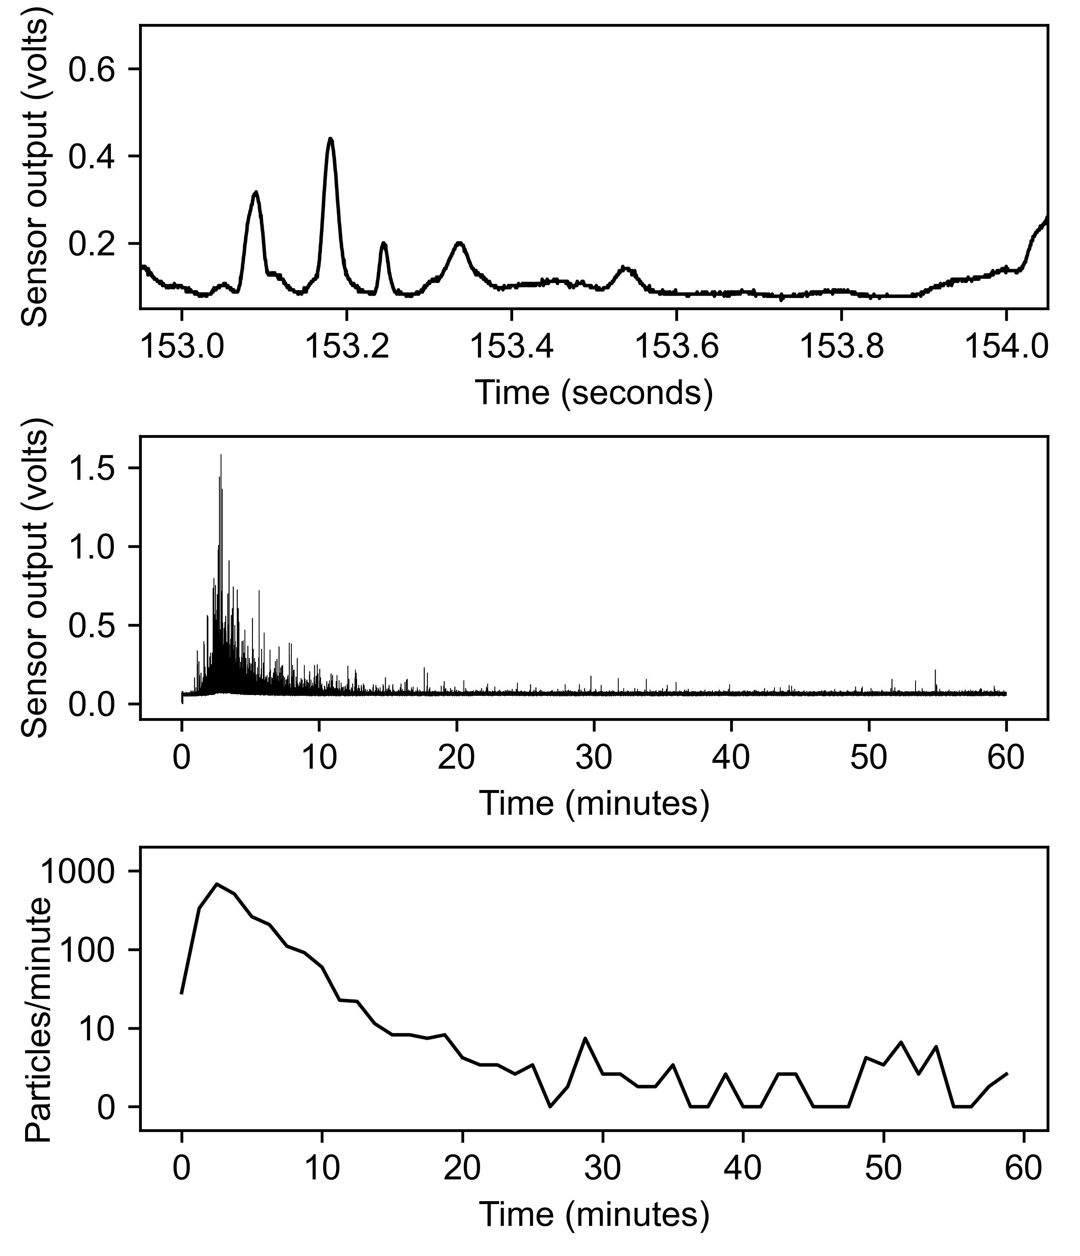
data/bayer_tylenol/153 20251210T135456_T06 TCOLD 1.json.gz.png
