groverlab/disintegration-fingerprinting/data/bayer_tylenol/154 20251210T150122_T06 TCOLD 2.json.gz.png

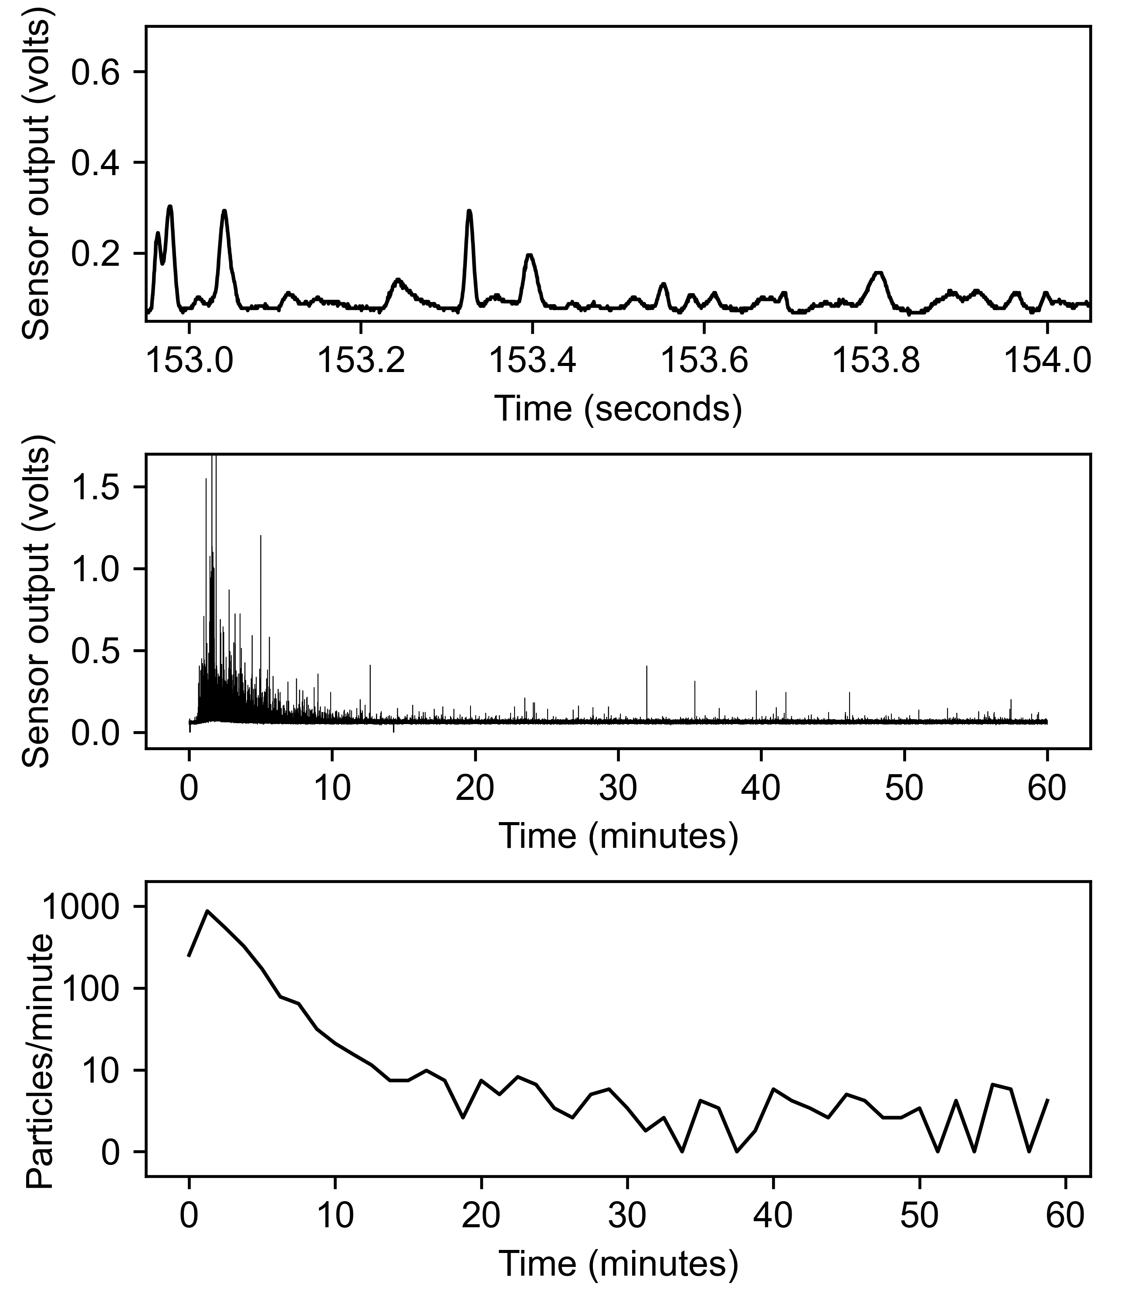
data/bayer_tylenol/154 20251210T150122_T06 TCOLD 2.json.gz.png
