groverlab/disintegration-fingerprinting/data/bayer_tylenol/155 20251210T160747_T06 TCOLD 3.json.gz.png

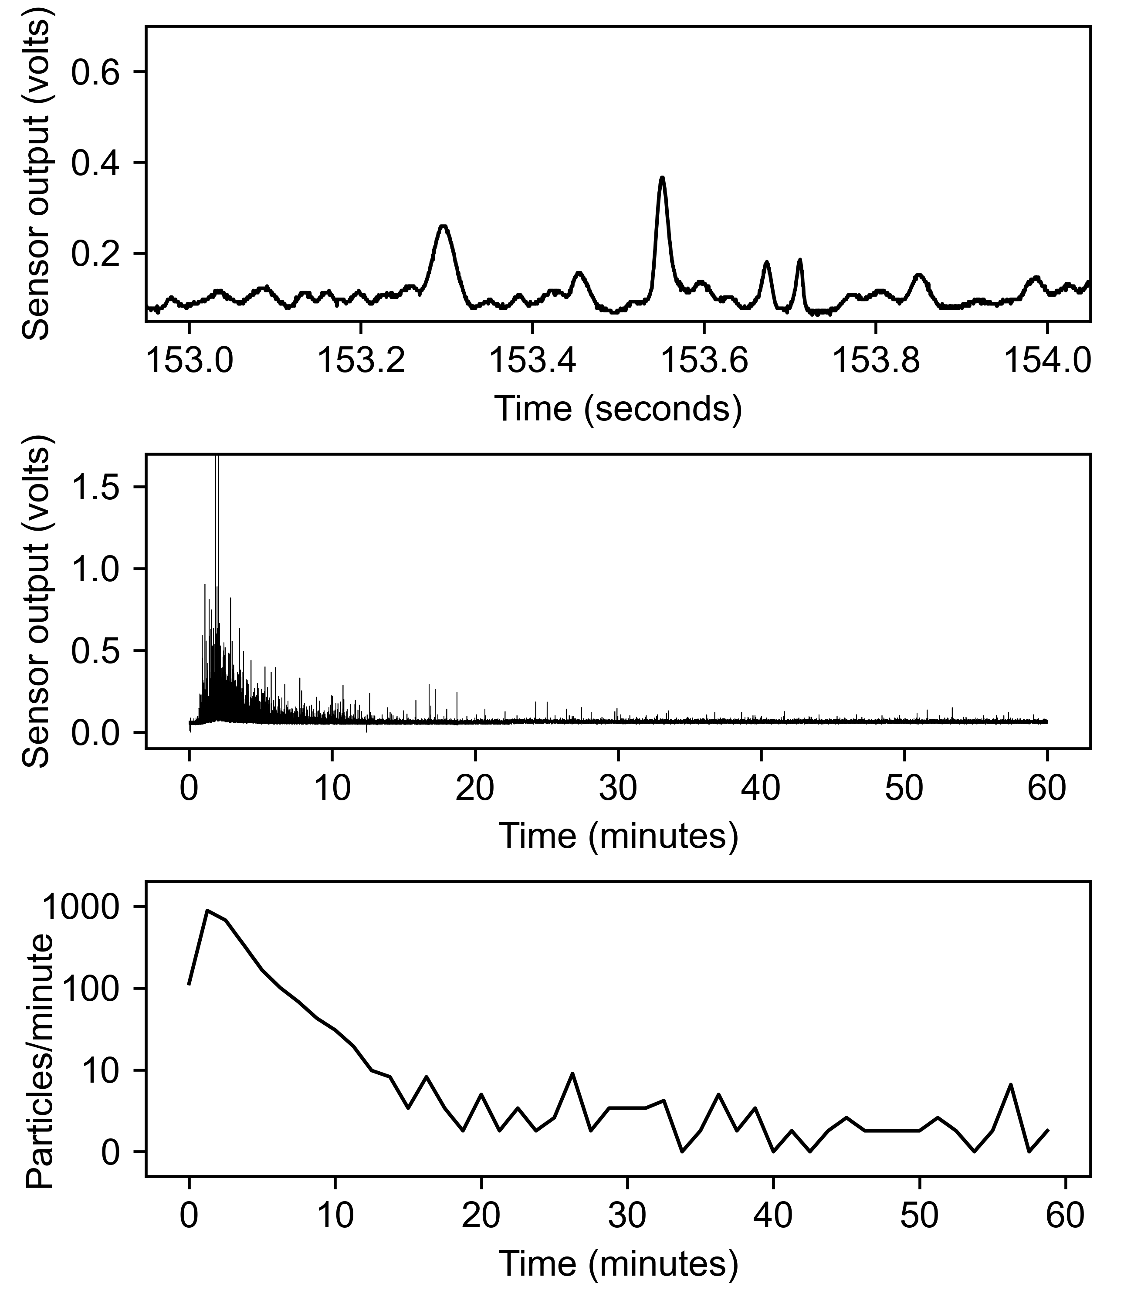
data/bayer_tylenol/155 20251210T160747_T06 TCOLD 3.json.gz.png
