groverlab/disintegration-fingerprinting/data/bayer_tylenol/501 20251112T162420_A12one ART.json.gz.png

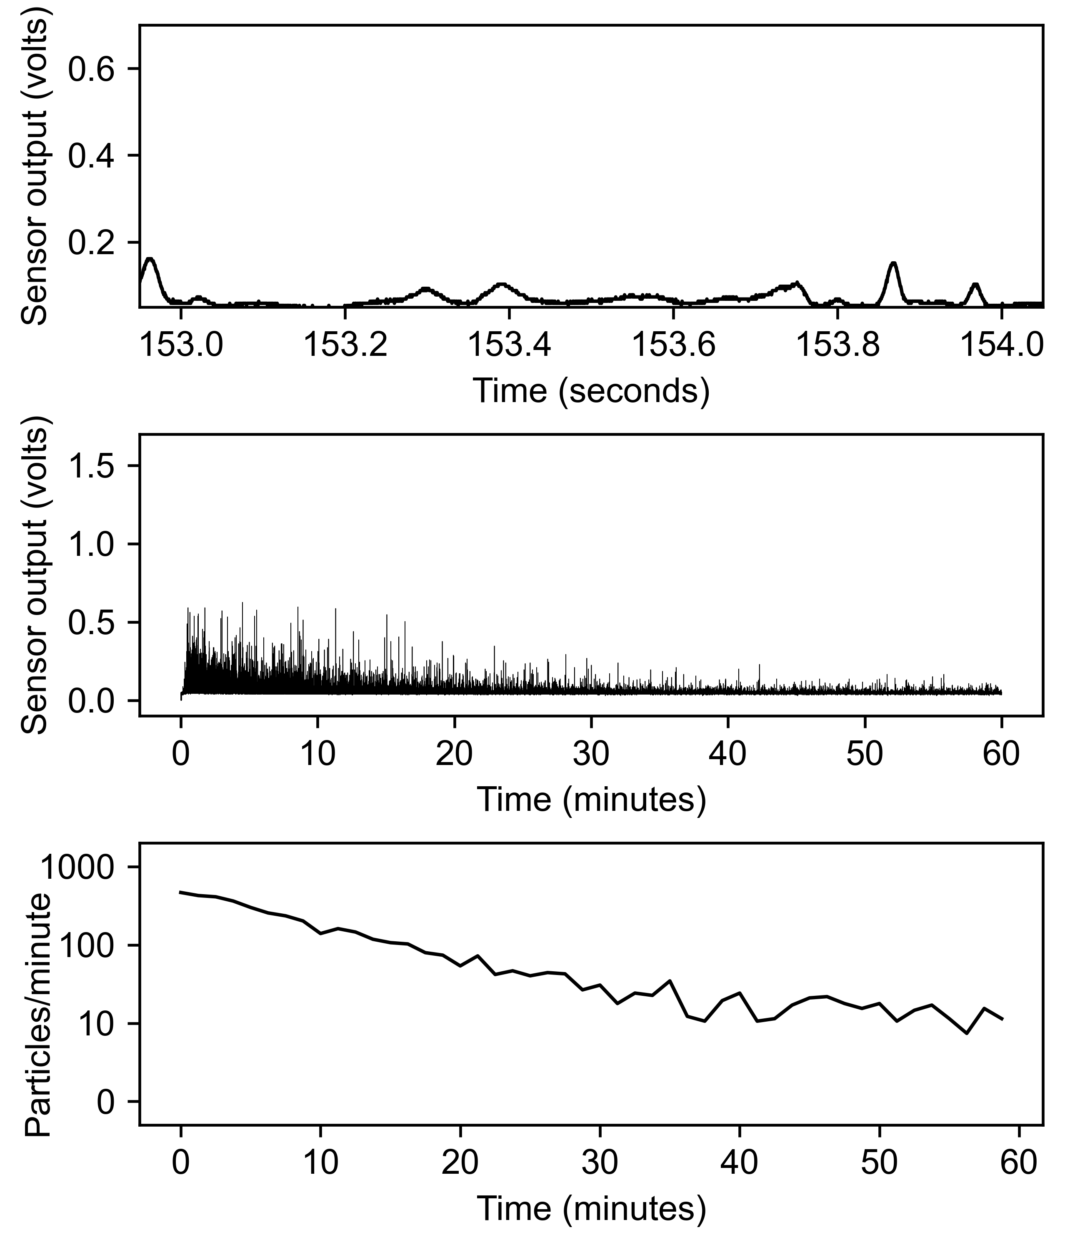
data/bayer_tylenol/501 20251112T162420_A12one ART.json.gz.png
