groverlab/disintegration-fingerprinting/data/bayer_tylenol/502 20251111T121444_A07one ART.json.gz.png

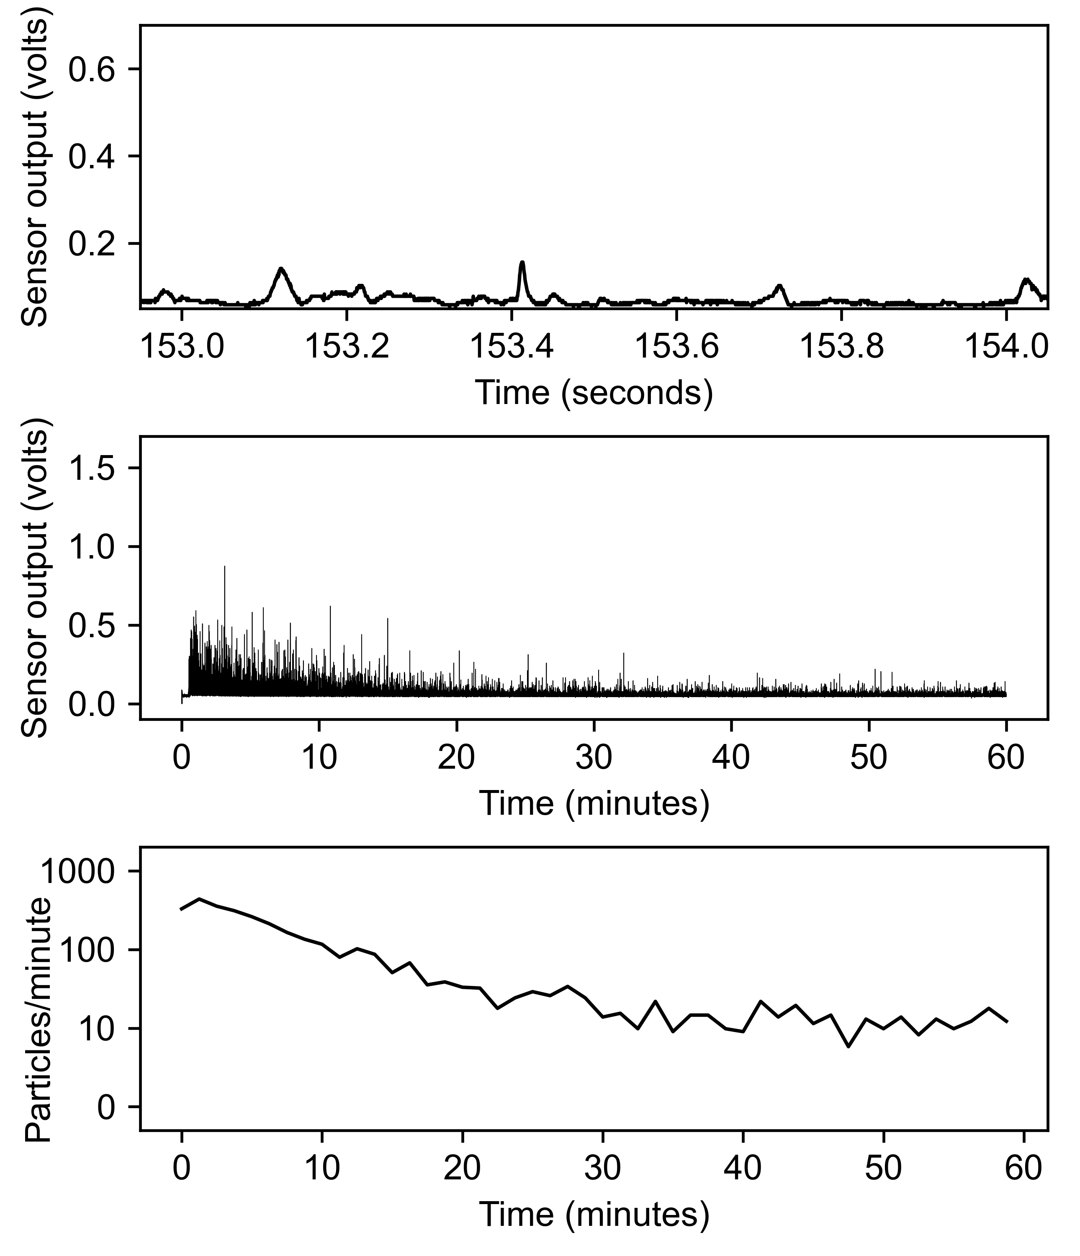
data/bayer_tylenol/502 20251111T121444_A07one ART.json.gz.png
