groverlab/disintegration-fingerprinting/data/bayer_tylenol/503 20251124T150228_A17one ACANADA.json.gz.png

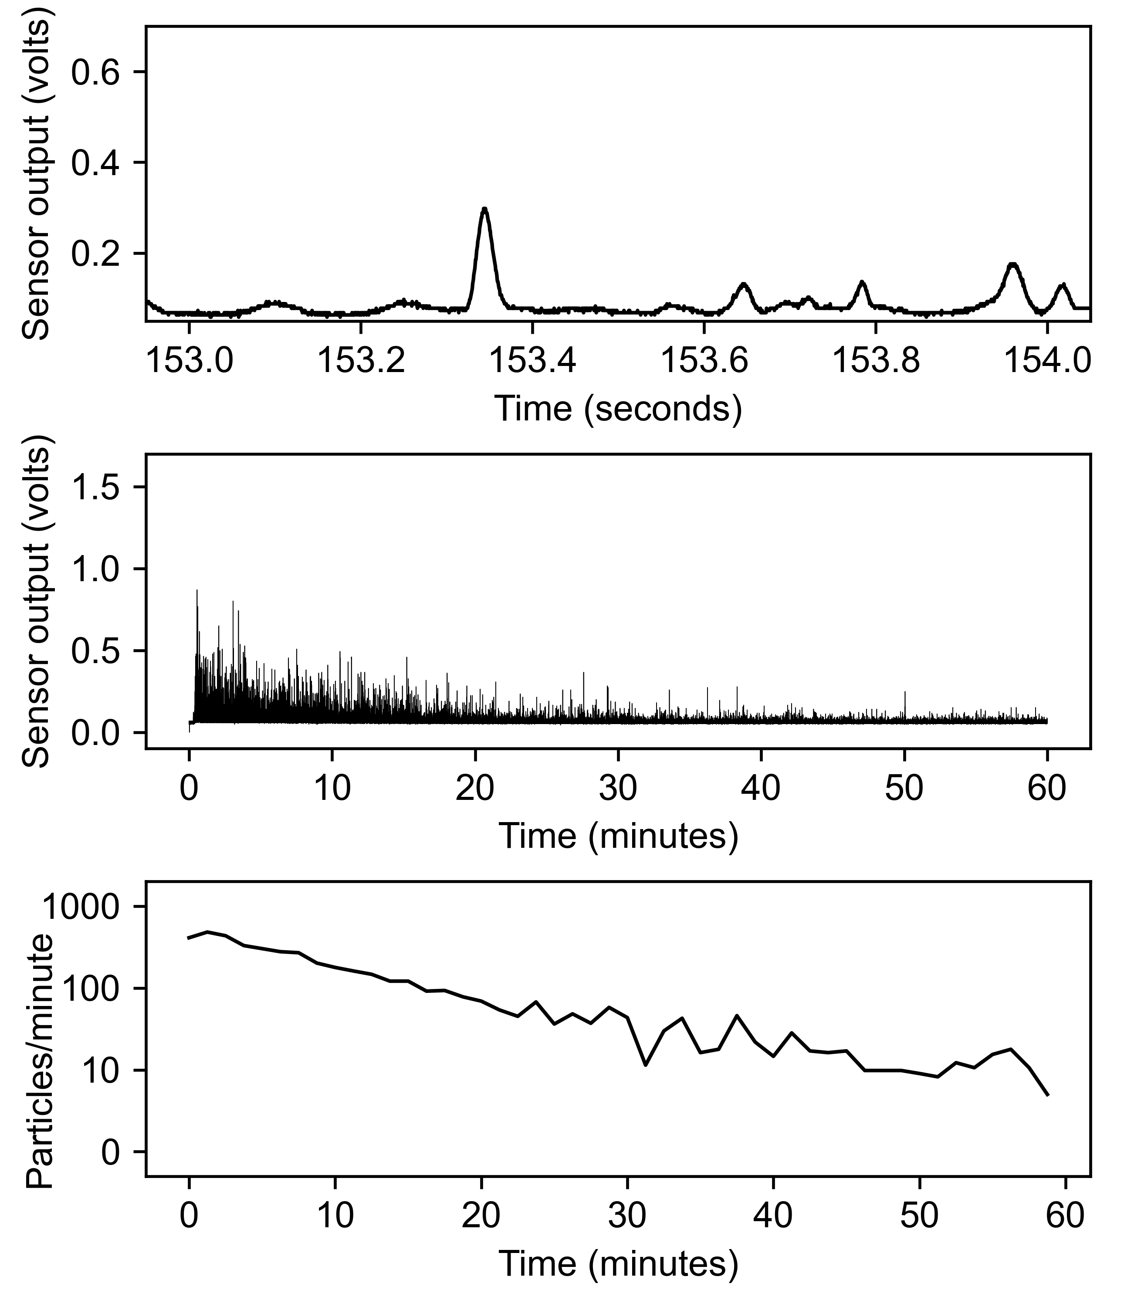
data/bayer_tylenol/503 20251124T150228_A17one ACANADA.json.gz.png
