groverlab/disintegration-fingerprinting/data/bayer_tylenol/505 20251110T134251_A03one ART.json.gz.png

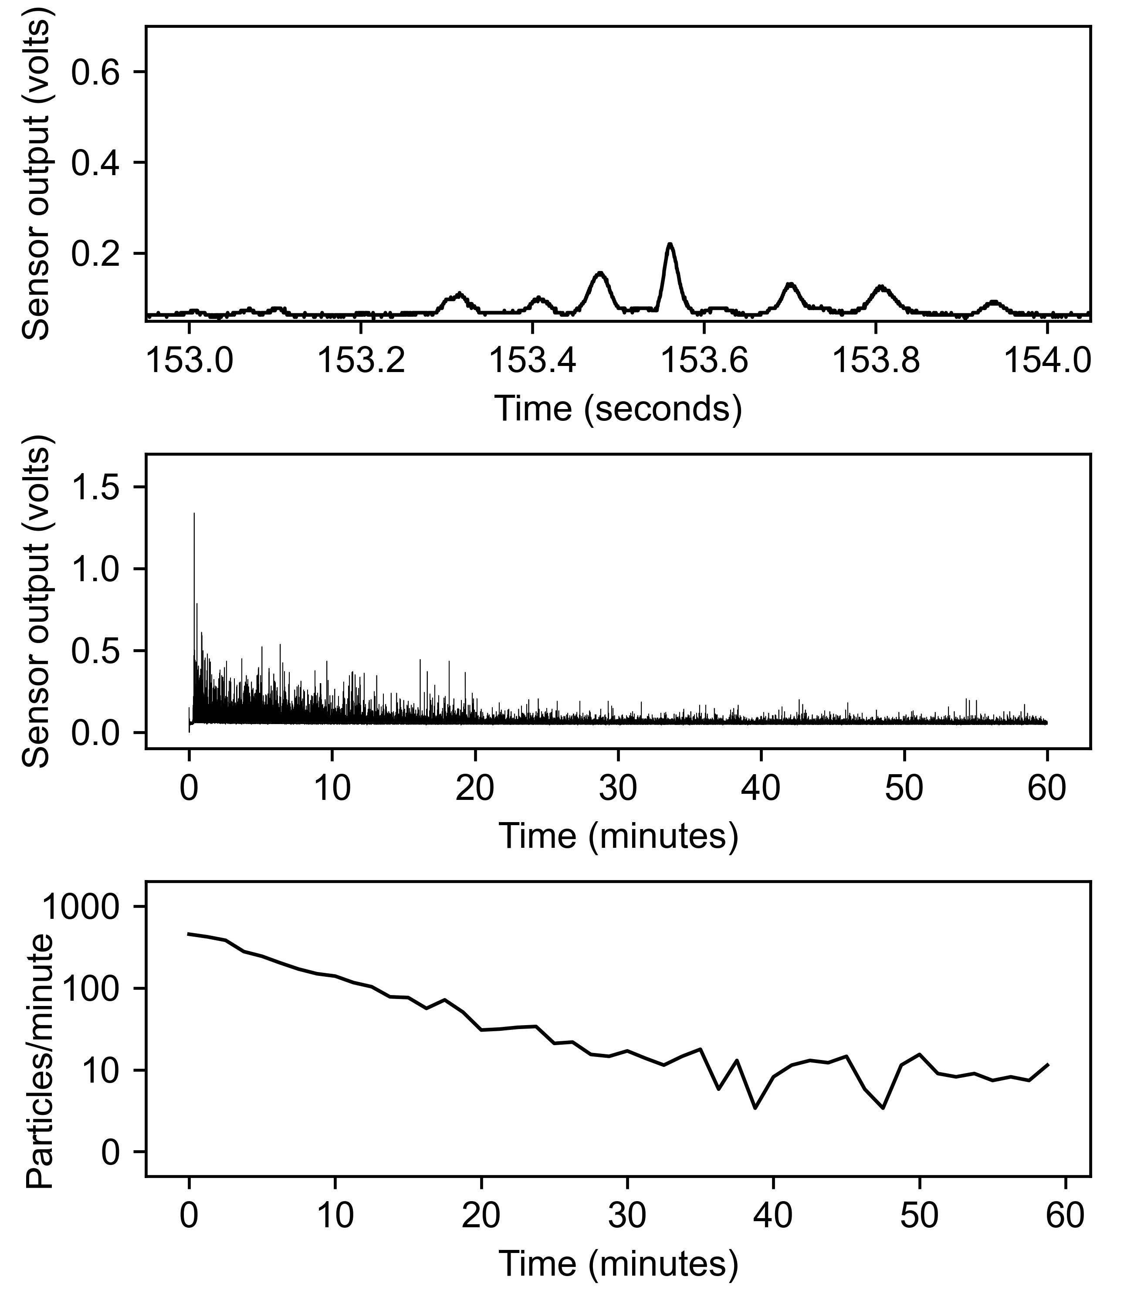
data/bayer_tylenol/505 20251110T134251_A03one ART.json.gz.png
