groverlab/disintegration-fingerprinting/data/bayer_tylenol/506 20251112T151658_A11one ART.json.gz.png

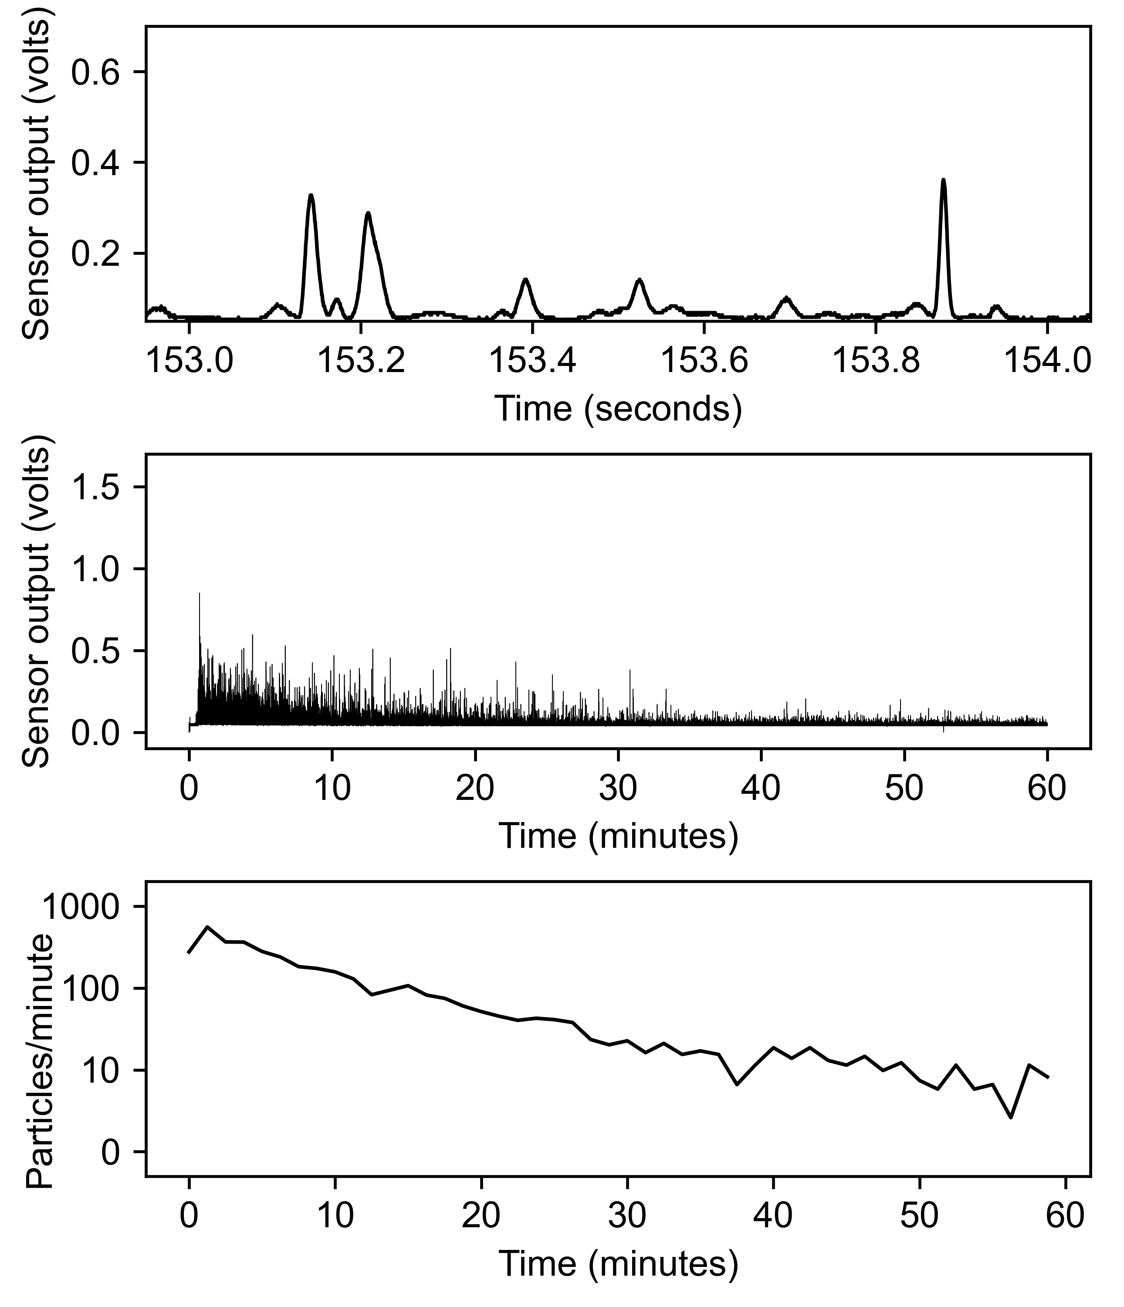
data/bayer_tylenol/506 20251112T151658_A11one ART.json.gz.png
