groverlab/disintegration-fingerprinting/data/bayer_tylenol/507 20251111T110351_A06one ART.json.gz.png

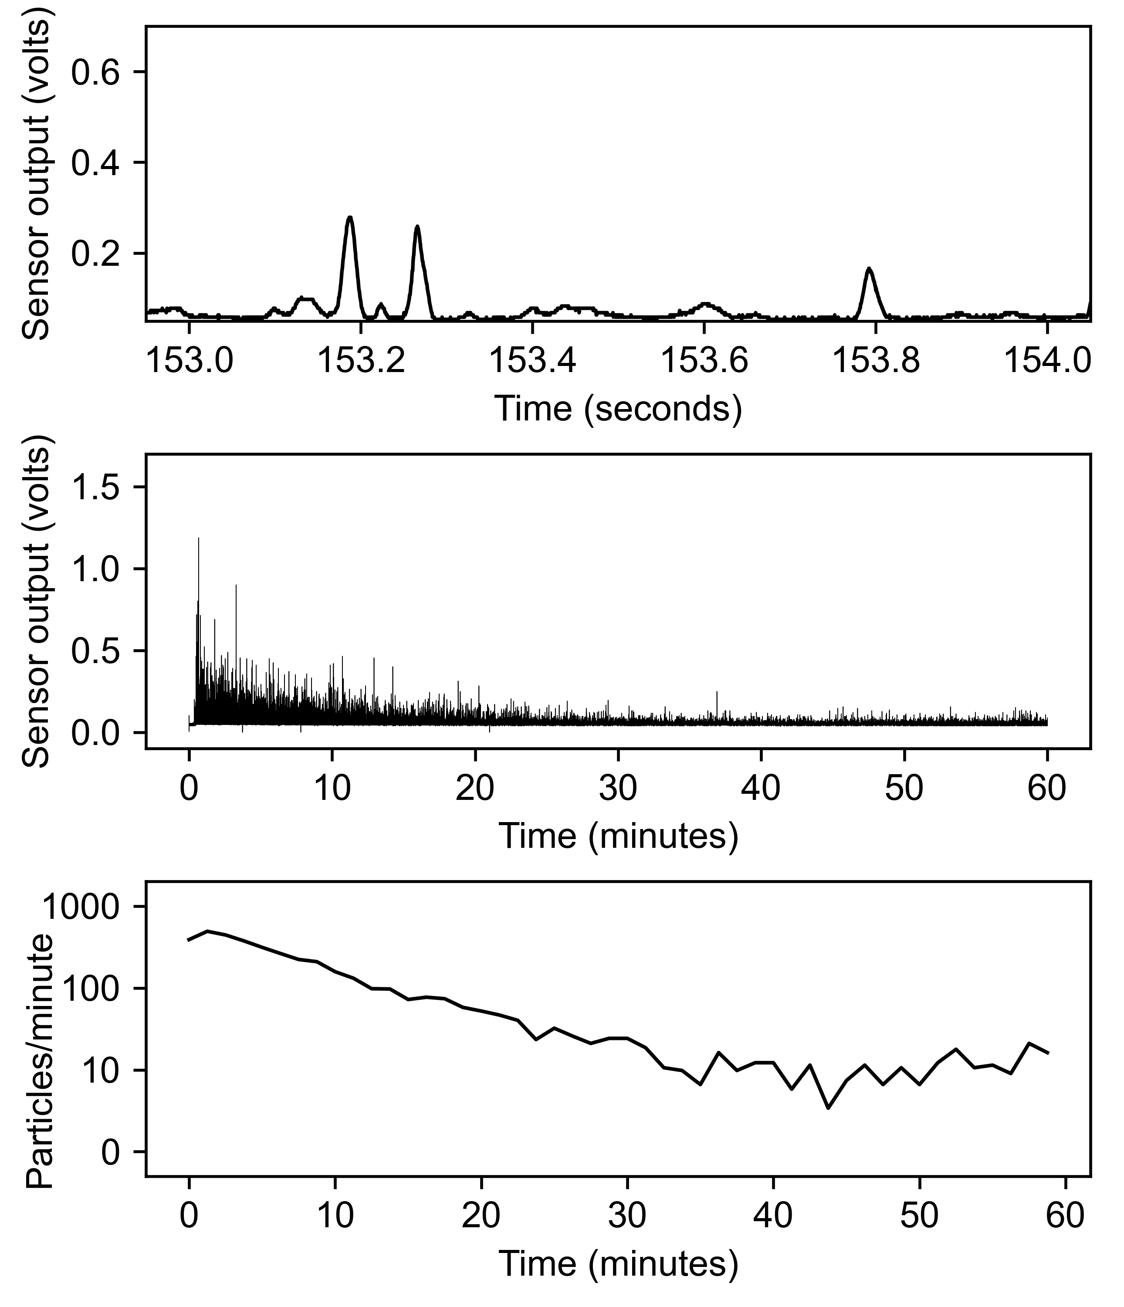
data/bayer_tylenol/507 20251111T110351_A06one ART.json.gz.png
