groverlab/disintegration-fingerprinting/data/bayer_tylenol/508 20251125T104844_A19one ACANADA.json.gz.png

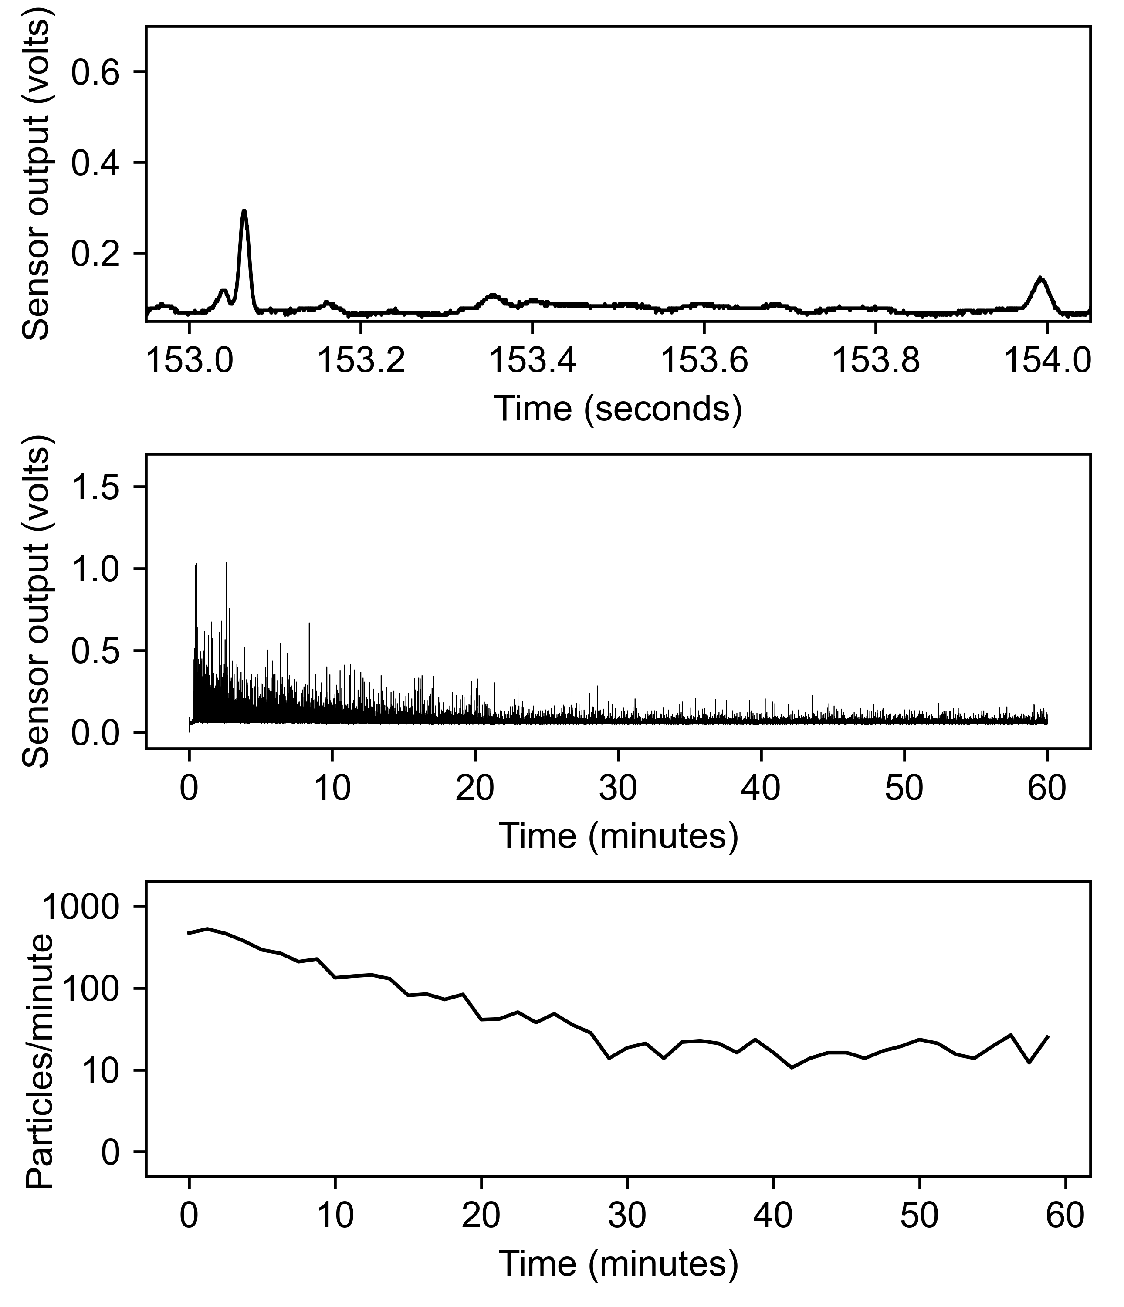
data/bayer_tylenol/508 20251125T104844_A19one ACANADA.json.gz.png
