groverlab/disintegration-fingerprinting/data/bayer_tylenol/509 20251110T161145_A04one ART.json.gz.png

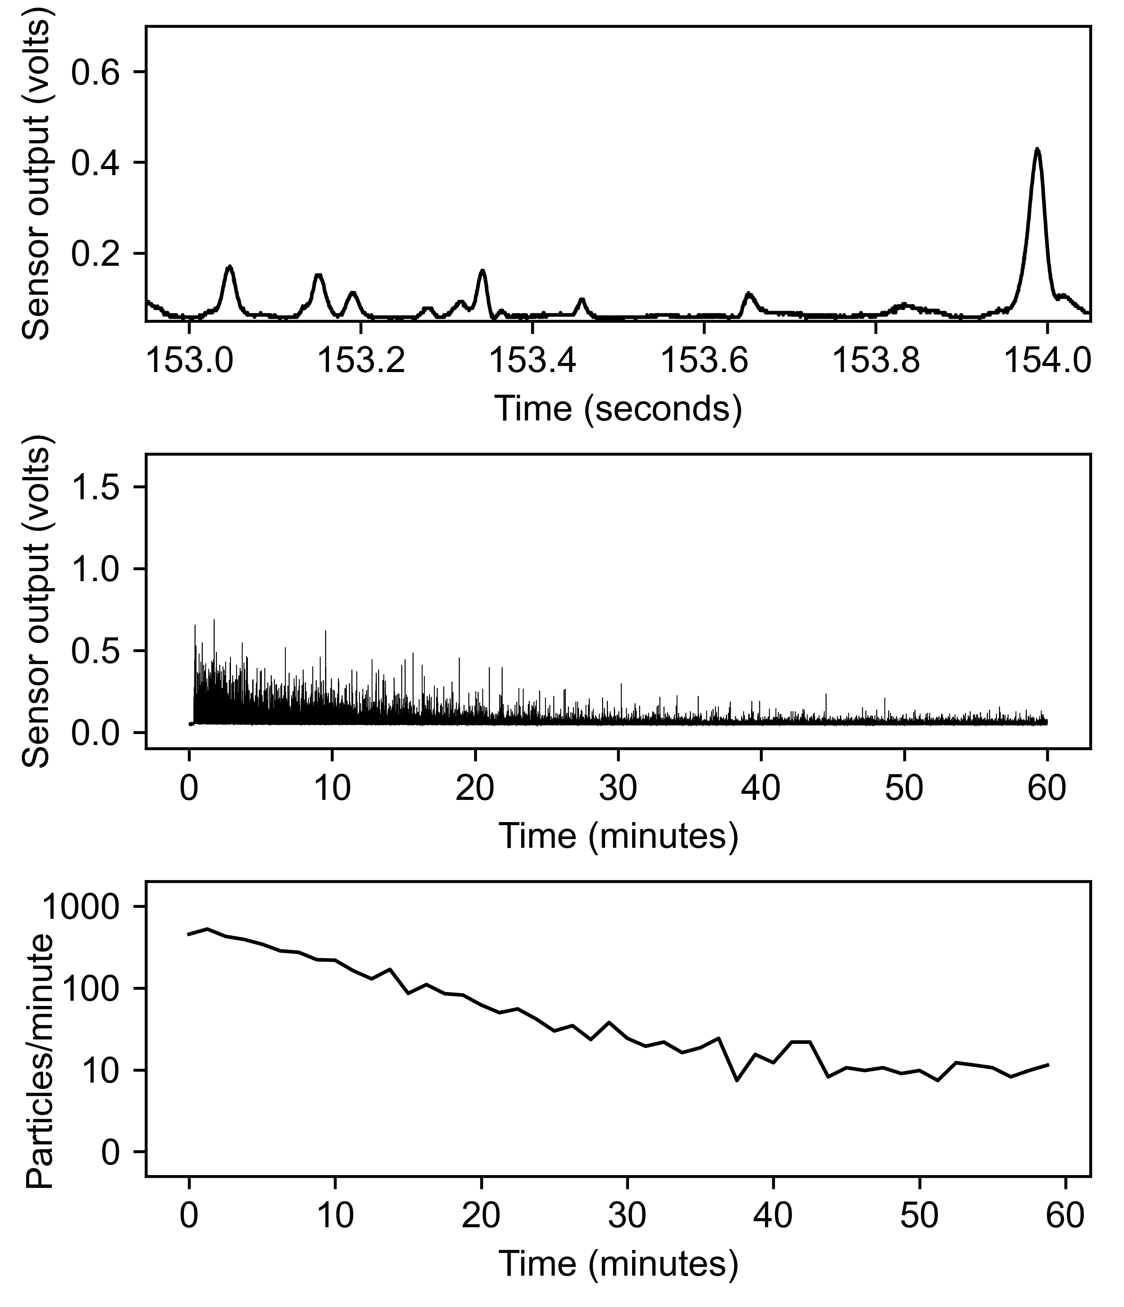
data/bayer_tylenol/509 20251110T161145_A04one ART.json.gz.png
