groverlab/disintegration-fingerprinting/data/bayer_tylenol/510 20251112T114510_A08one ART.json.gz.png

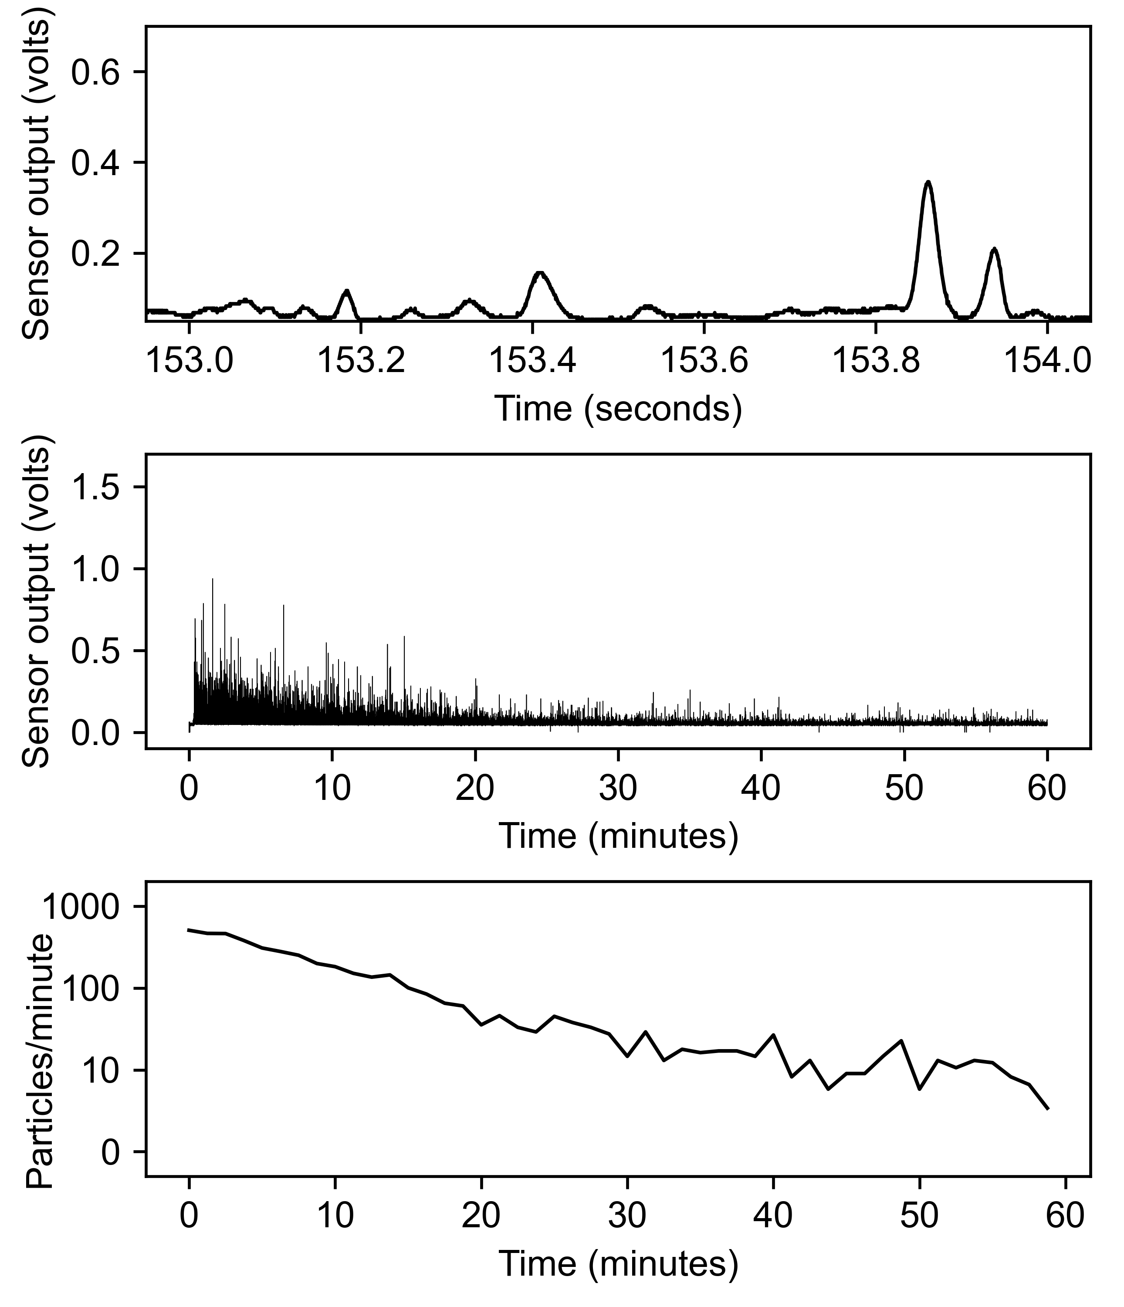
data/bayer_tylenol/510 20251112T114510_A08one ART.json.gz.png
