groverlab/disintegration-fingerprinting/data/bayer_tylenol/511 20251113T132033_A15one ART.json.gz.png

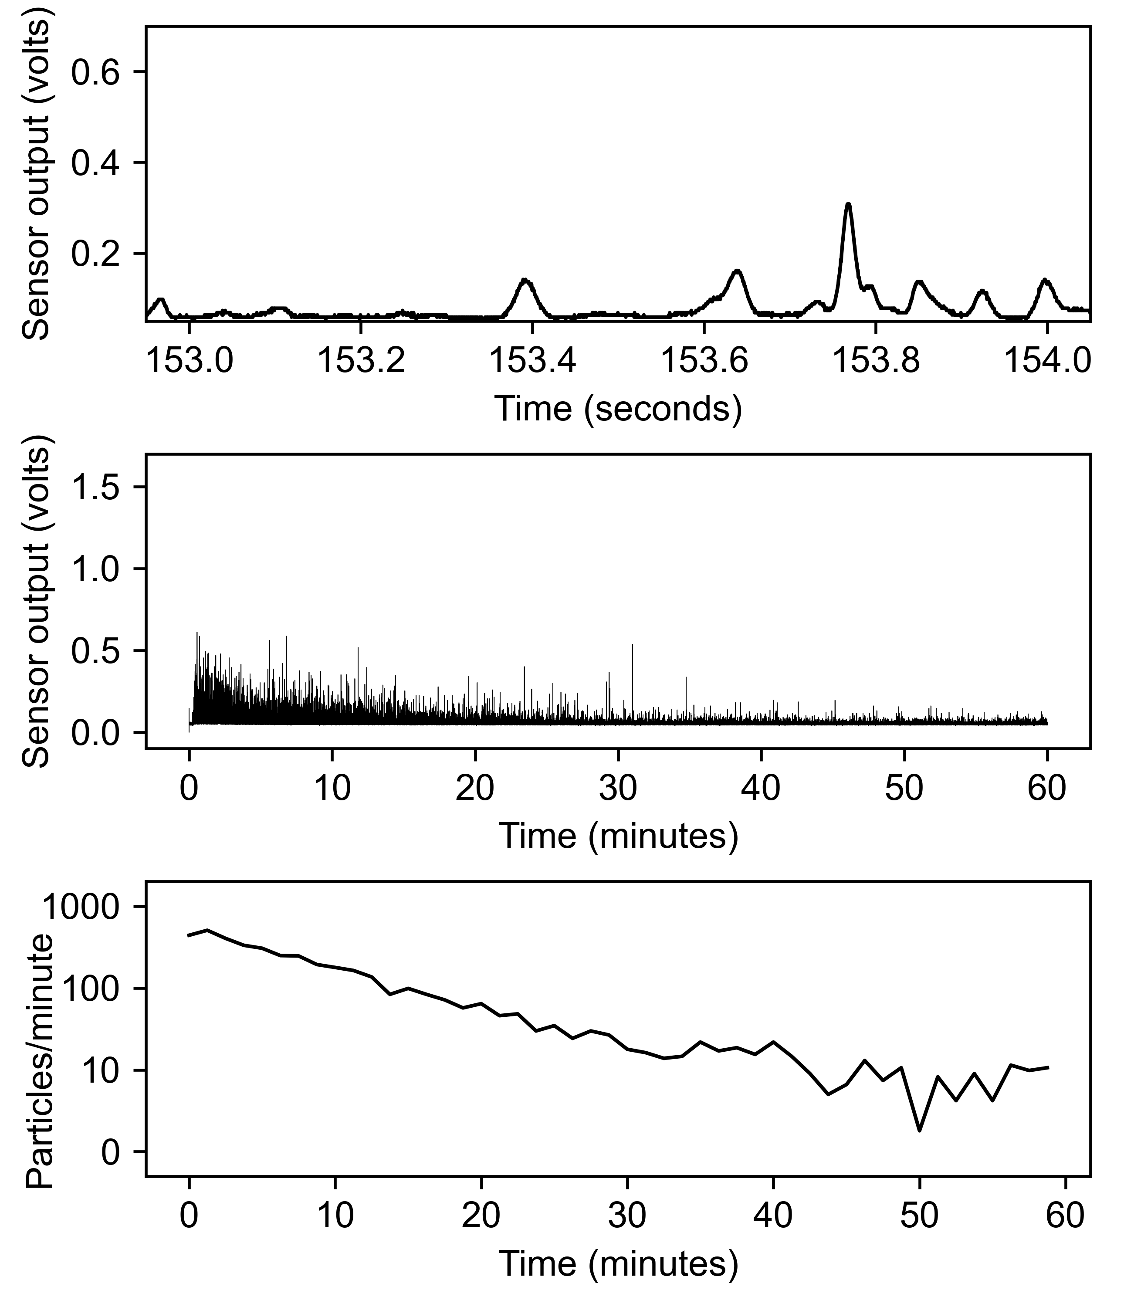
data/bayer_tylenol/511 20251113T132033_A15one ART.json.gz.png
