groverlab/disintegration-fingerprinting/data/bayer_tylenol/512 20251125T093826_A18one ART.json.gz.png

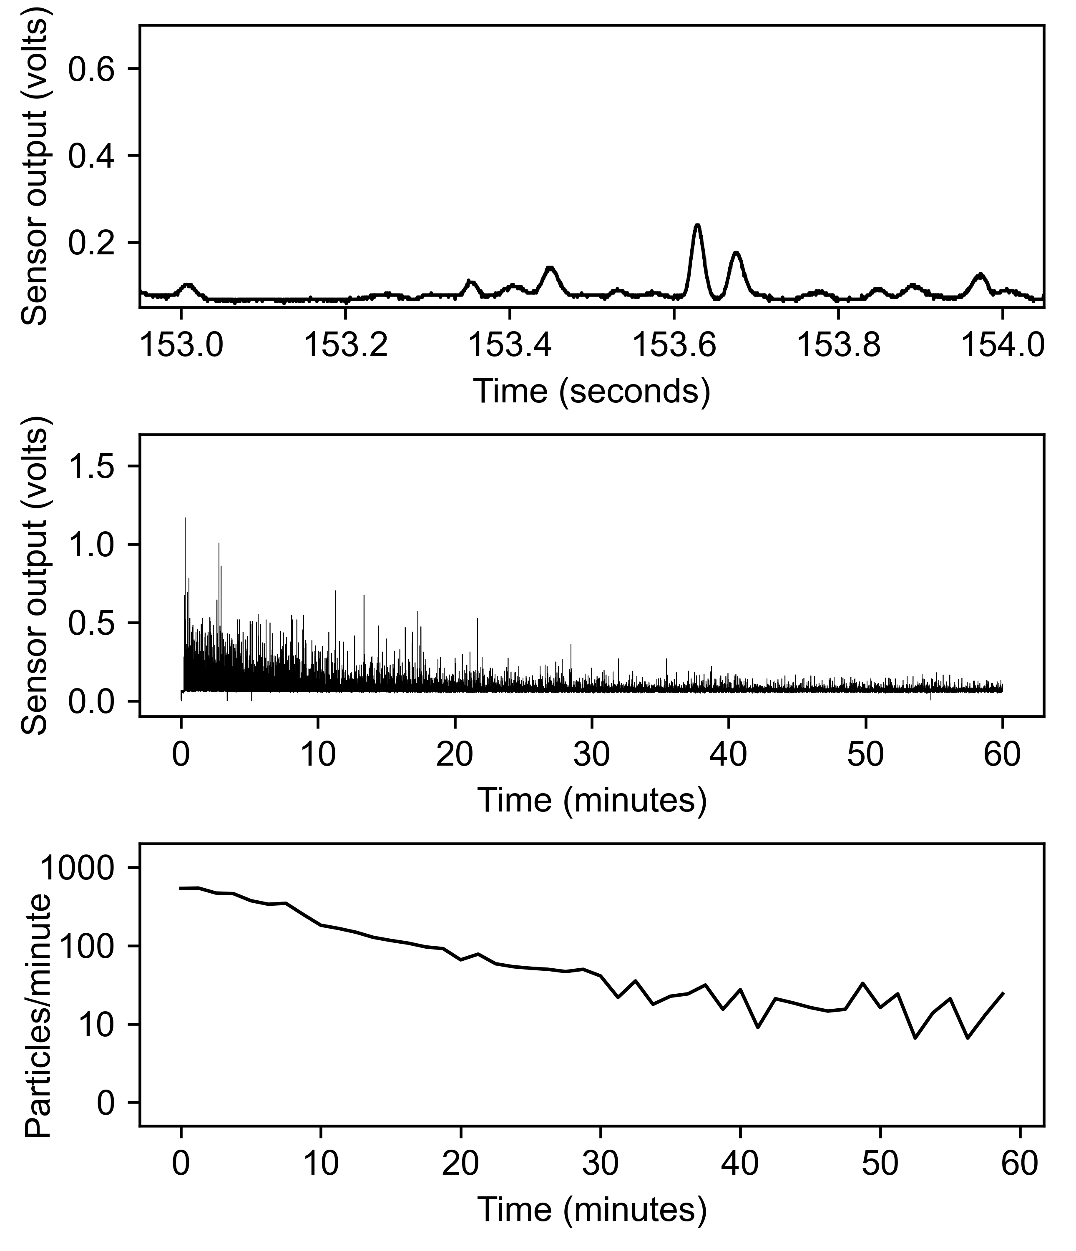
data/bayer_tylenol/512 20251125T093826_A18one ART.json.gz.png
