groverlab/disintegration-fingerprinting/data/bayer_tylenol/519 20251027T133114_A01one ART.json.gz.png

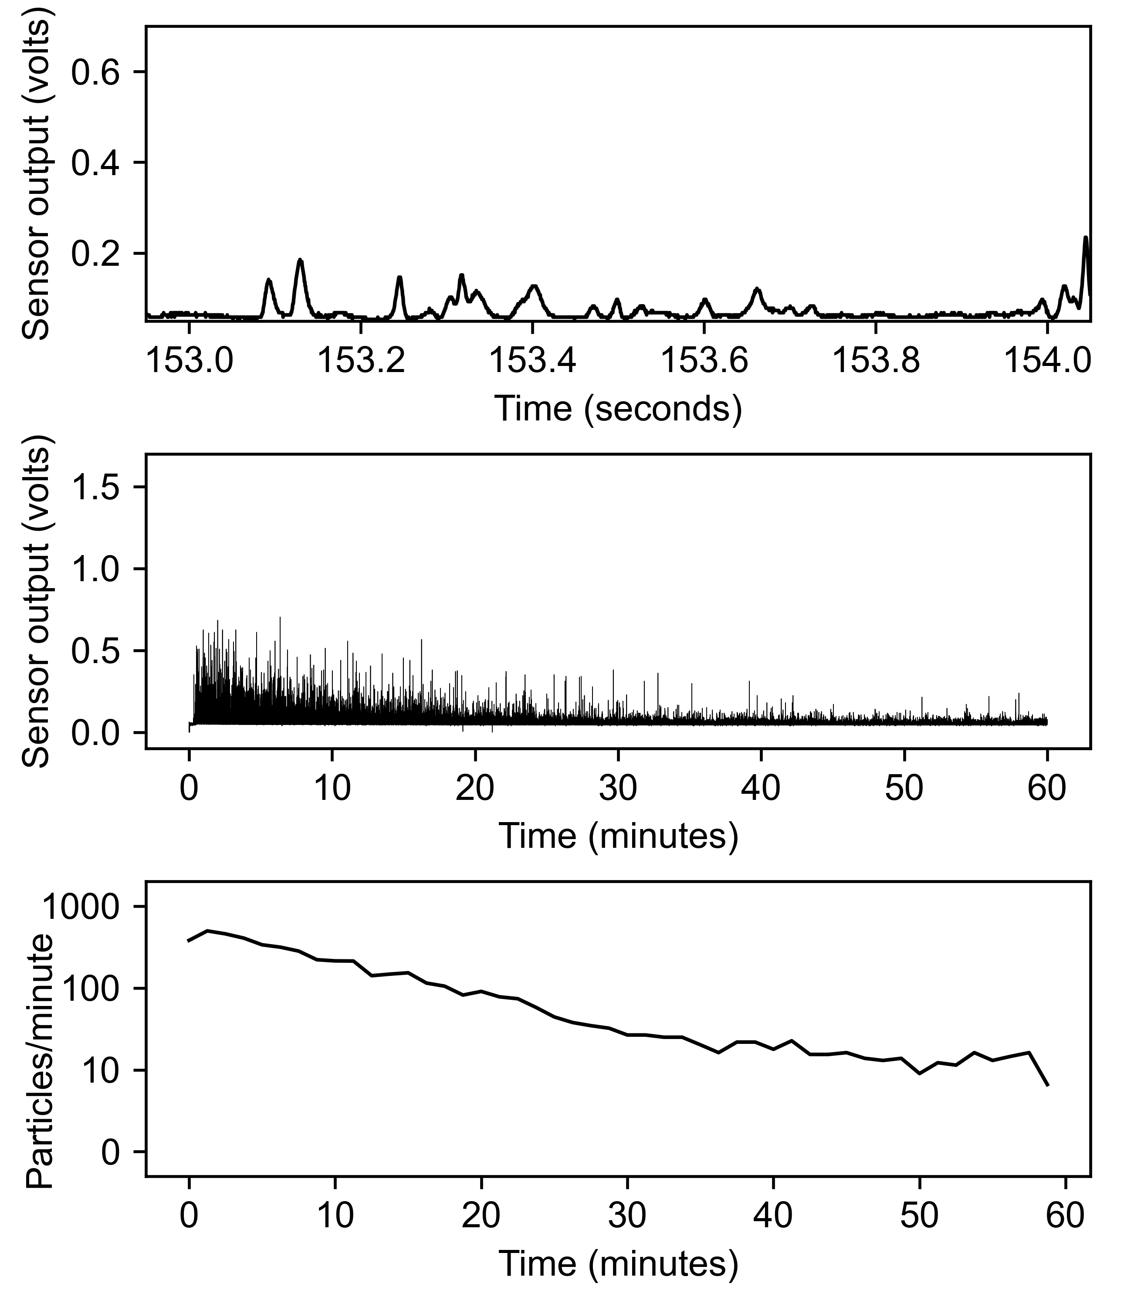
data/bayer_tylenol/519 20251027T133114_A01one ART.json.gz.png
