groverlab/disintegration-fingerprinting/data/bayer_tylenol/550 20251203T093716_A01 AHOT 1.json.gz.png

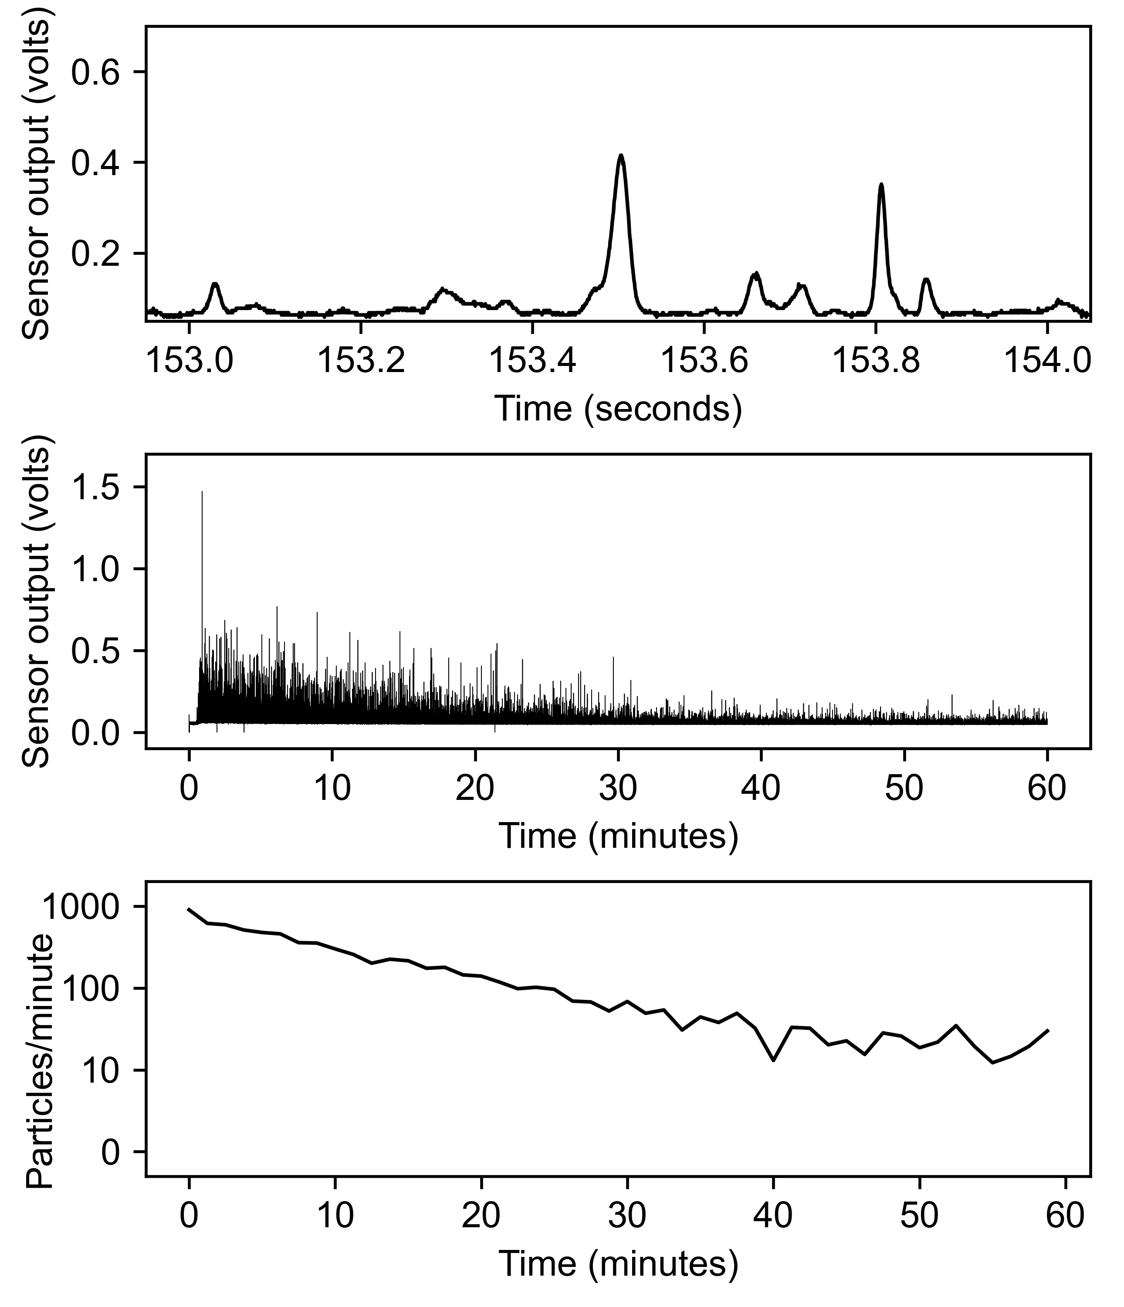
data/bayer_tylenol/550 20251203T093716_A01 AHOT 1.json.gz.png
