groverlab/disintegration-fingerprinting/data/bayer_tylenol/552 20251203T120239_A01 AHOT 3.json.gz.png

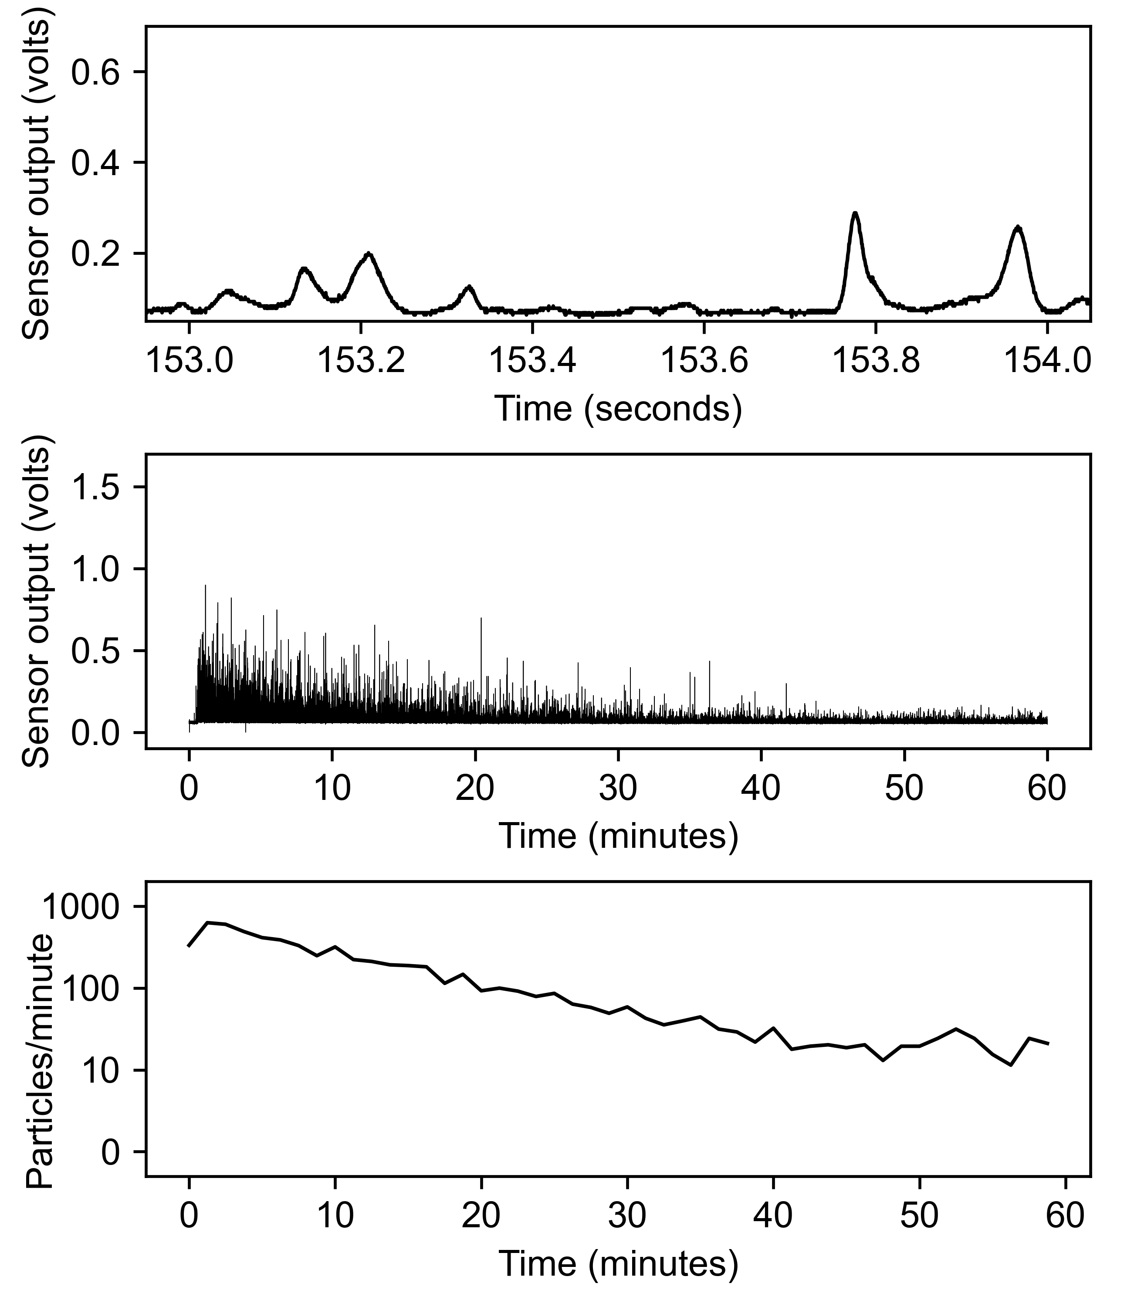
data/bayer_tylenol/552 20251203T120239_A01 AHOT 3.json.gz.png
