groverlab/disintegration-fingerprinting/data/bayer_tylenol/553 20251203T131110_A01 ACOLD 1.json.gz.png

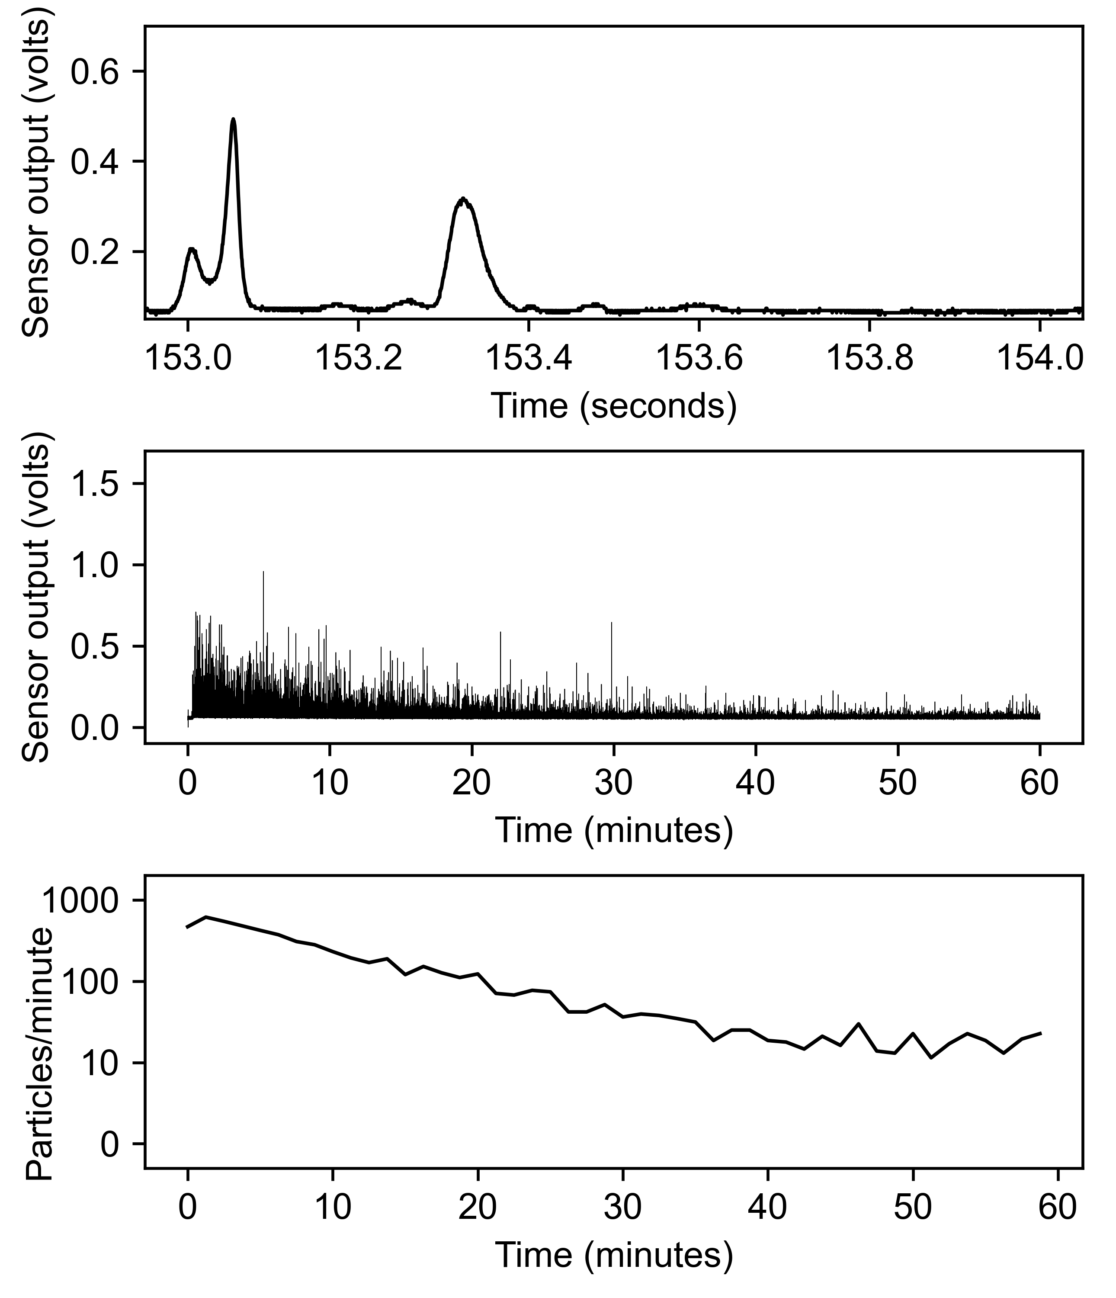
data/bayer_tylenol/553 20251203T131110_A01 ACOLD 1.json.gz.png
