groverlab/disintegration-fingerprinting/data/bayer_tylenol/554 20251203T143126_A01 ACOLD 2.json.gz.png

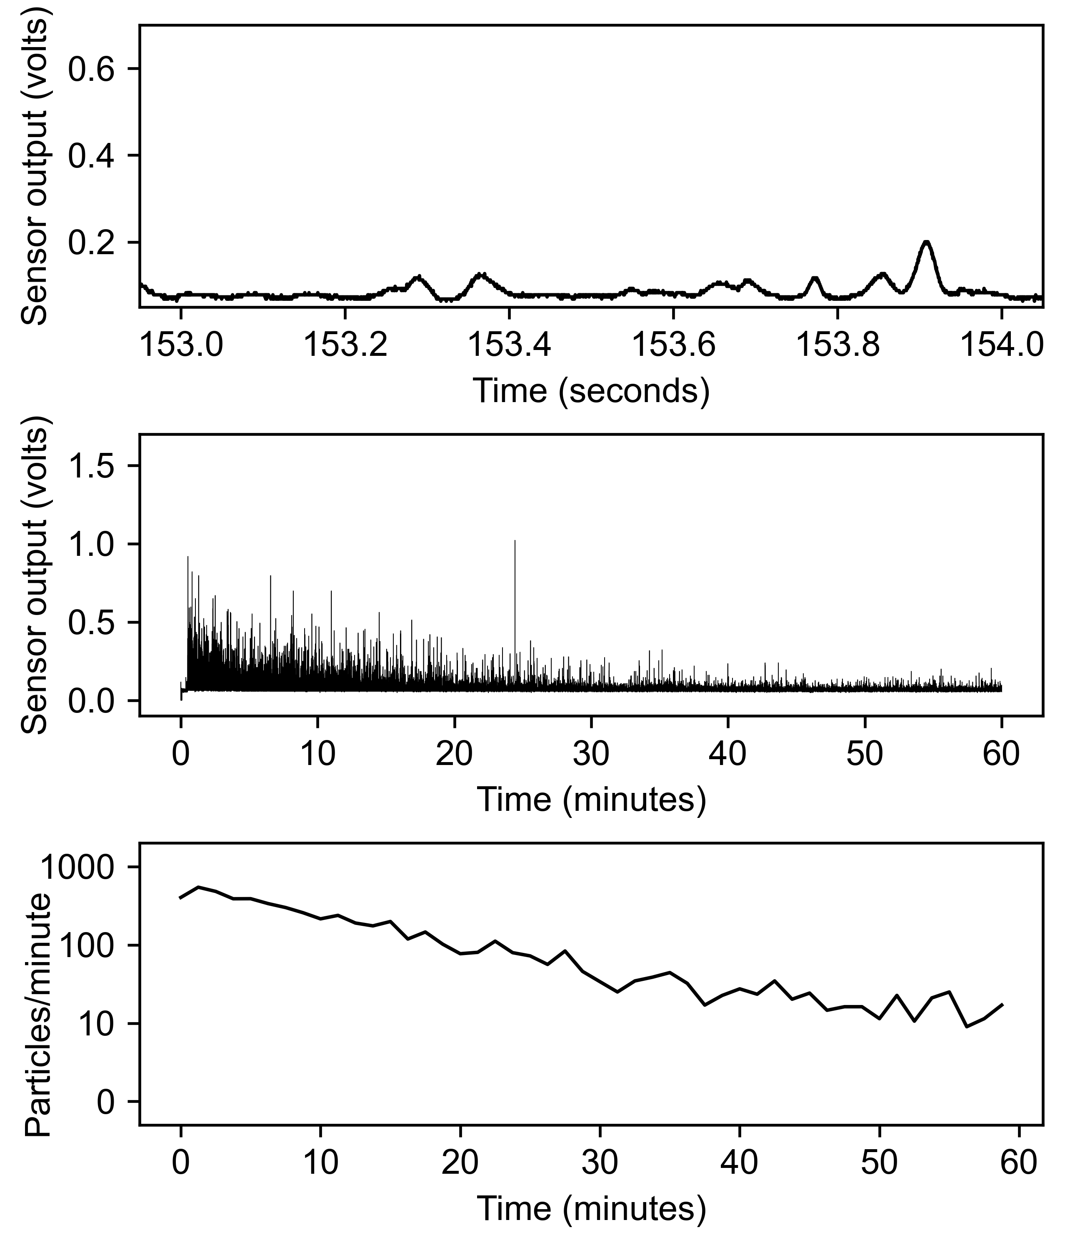
data/bayer_tylenol/554 20251203T143126_A01 ACOLD 2.json.gz.png
