groverlab/disintegration-fingerprinting/data/bayer_tylenol/20241112T125840_Bayer_Aspirin BAYERBOTTLE.json.gz.png

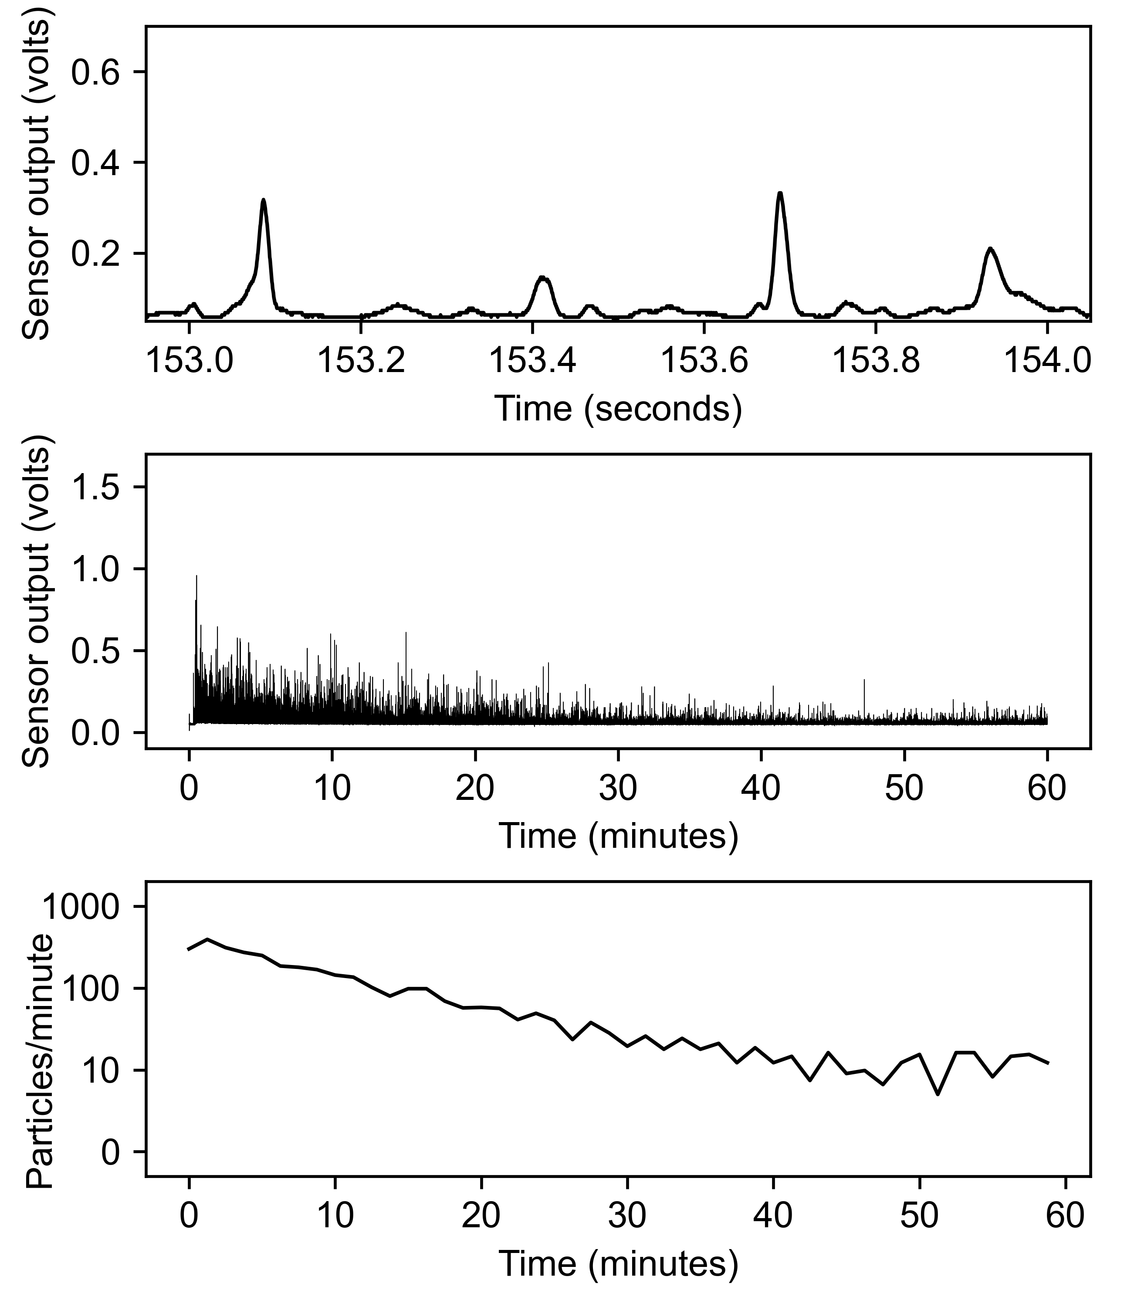
data/bayer_tylenol/20241112T125840_Bayer_Aspirin BAYERBOTTLE.json.gz.png
