groverlab/disintegration-fingerprinting/data/bayer_tylenol/20241113T120447_Generic_Aspirin GENERICBOTTLE.json.gz.png

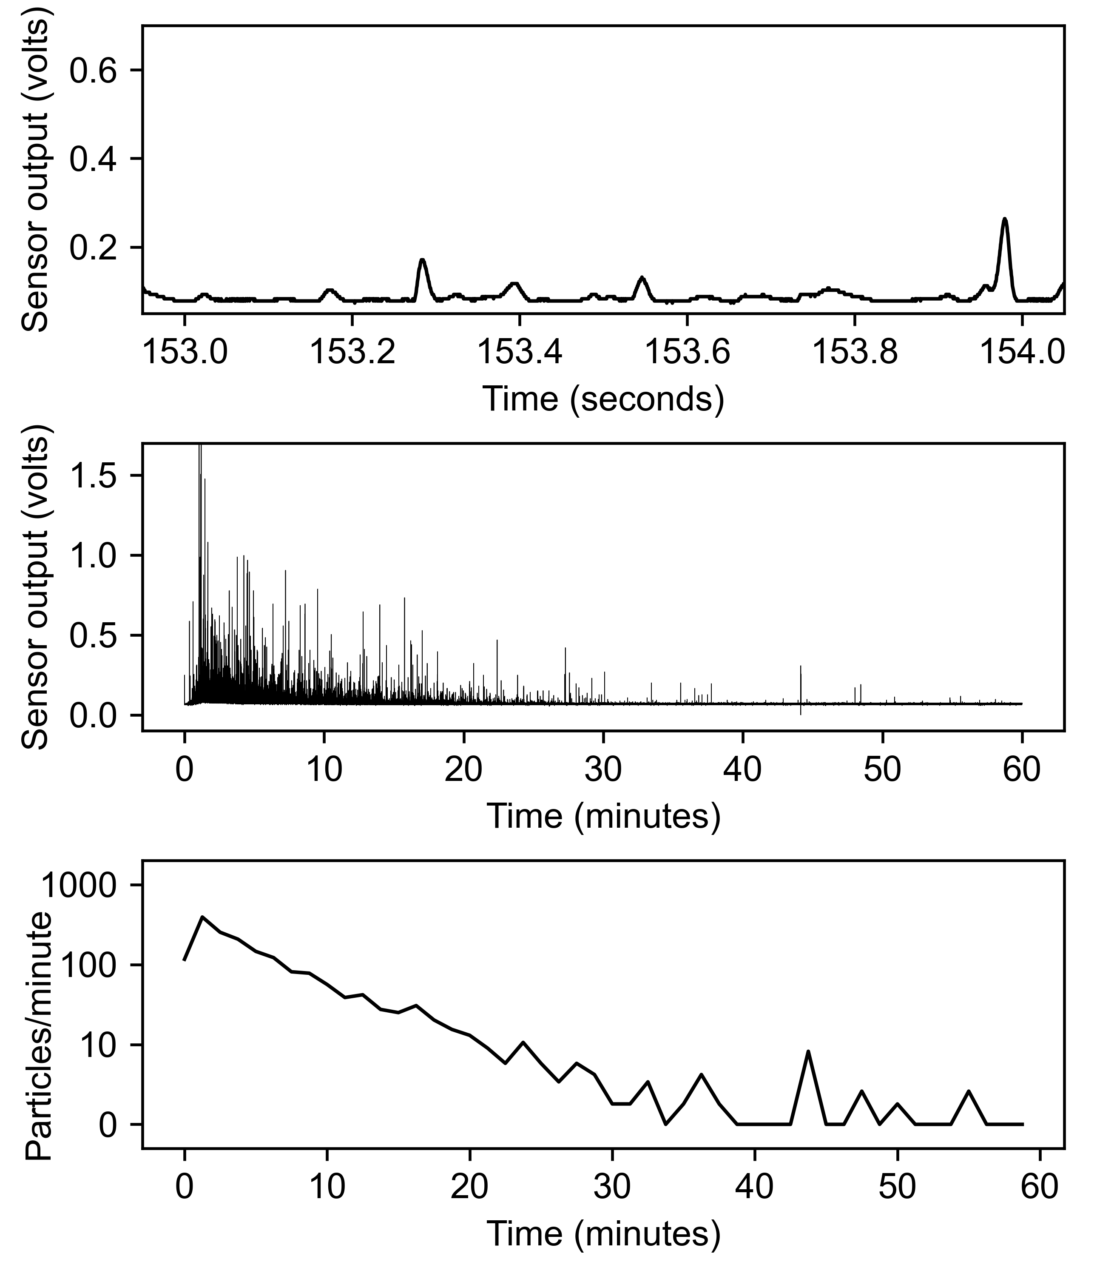
data/bayer_tylenol/20241113T120447_Generic_Aspirin GENERICBOTTLE.json.gz.png
