groverlab/disintegration-fingerprinting/data/bayer_tylenol/20241113T120556_Generic_Aspirin GENERICBOTTLE.json.gz.png

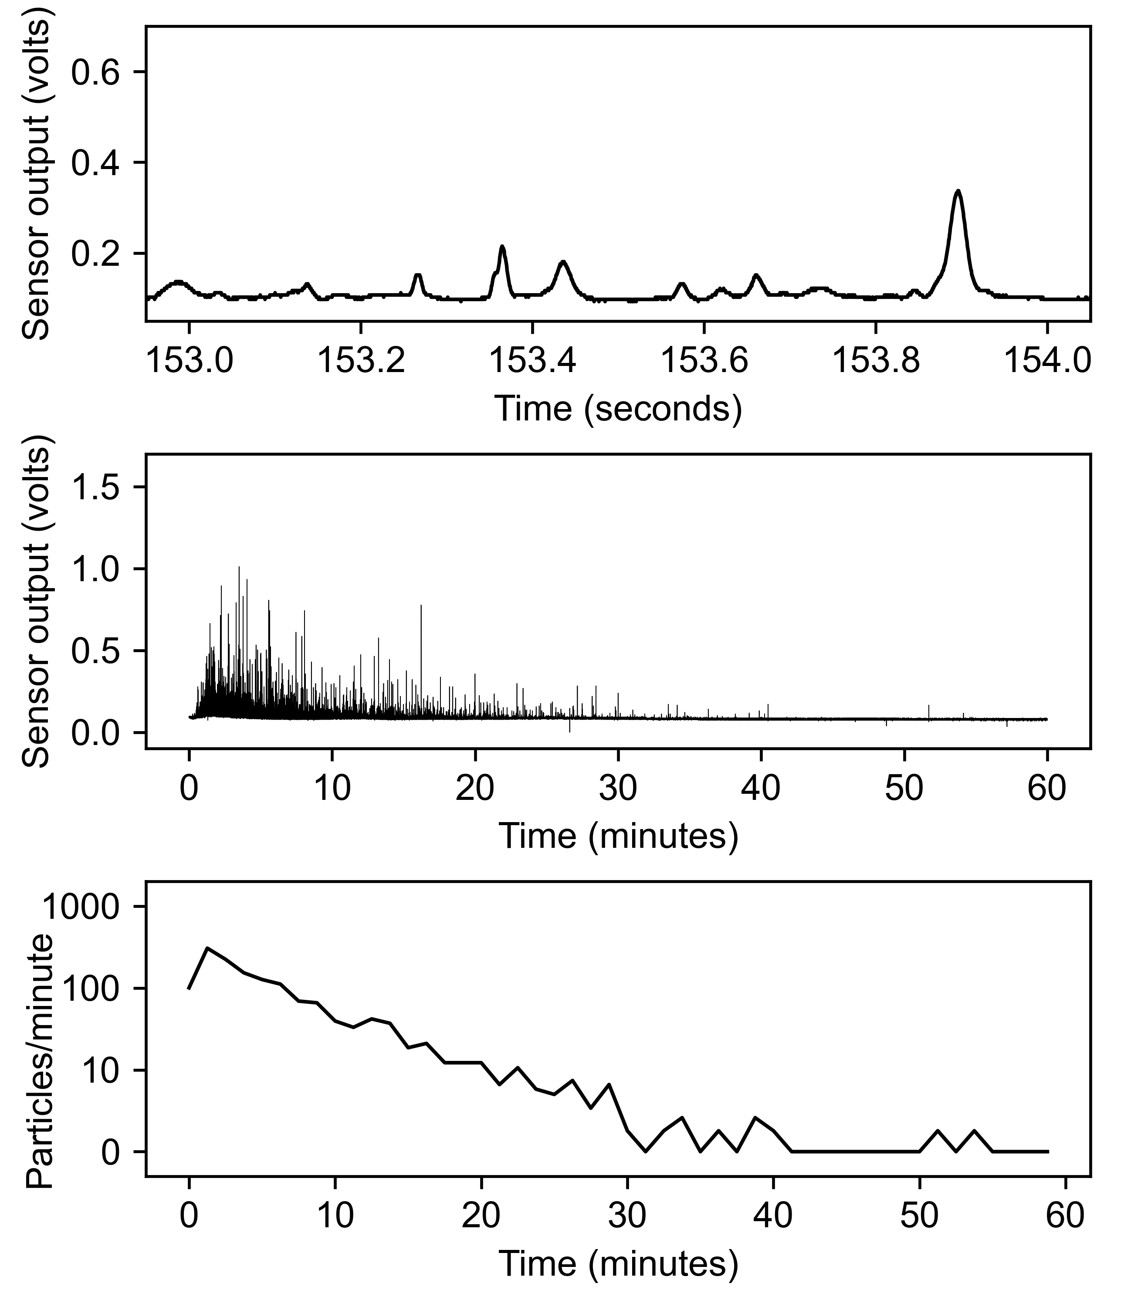
data/bayer_tylenol/20241113T120556_Generic_Aspirin GENERICBOTTLE.json.gz.png
