groverlab/disintegration-fingerprinting/data/bayer_tylenol/20241114T143102_Generic_Aspirin GENERICBOTTLE.json.gz.png

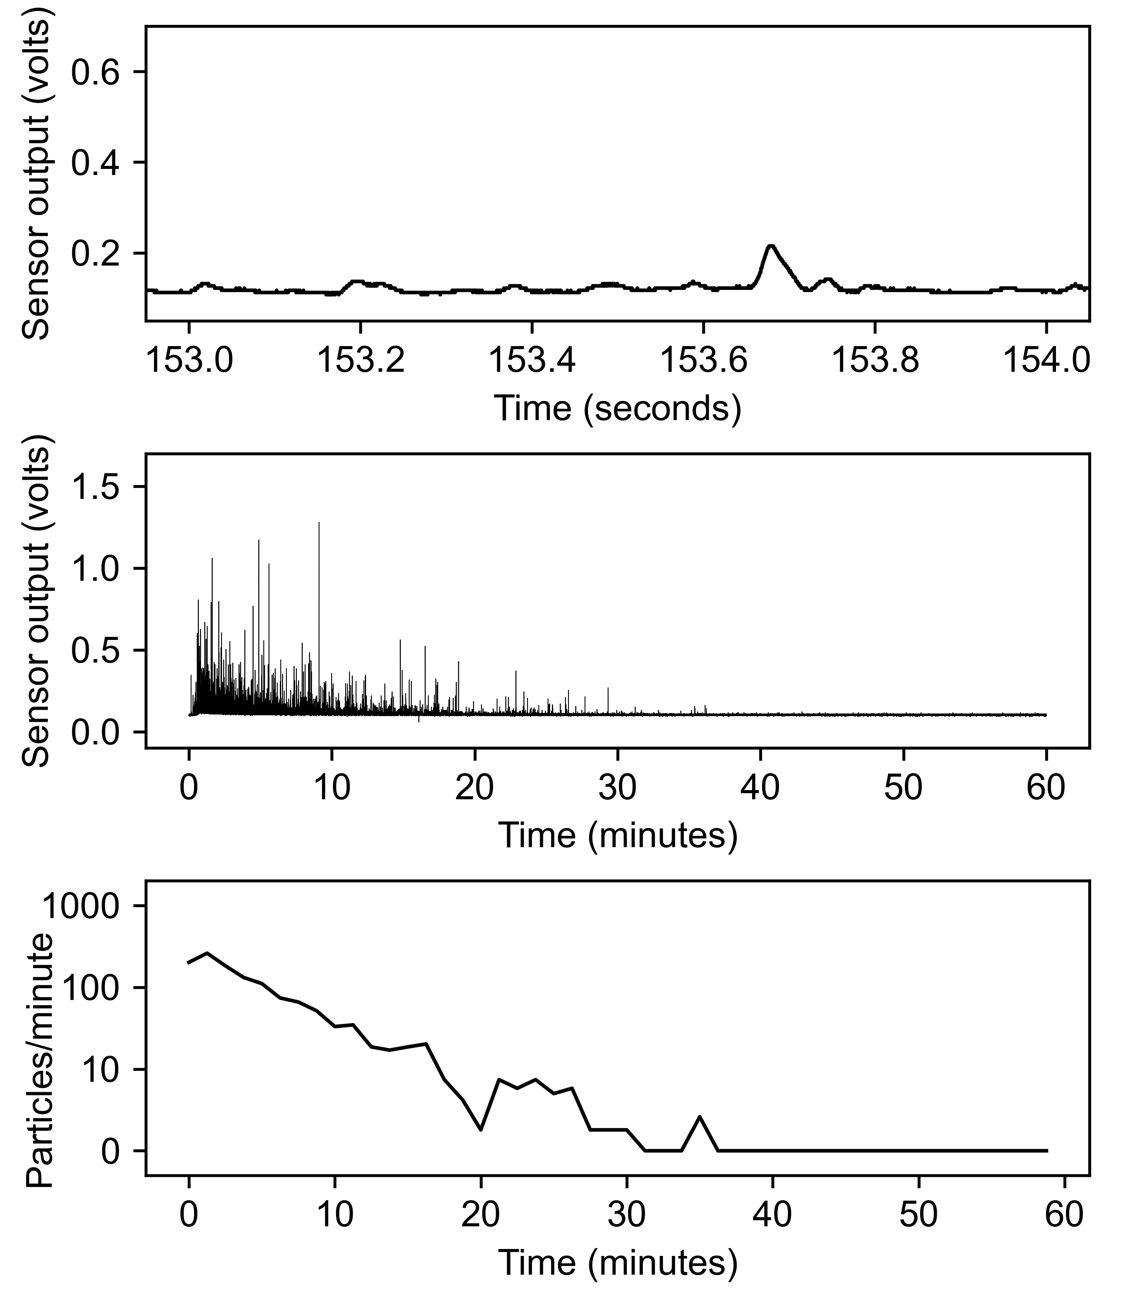
data/bayer_tylenol/20241114T143102_Generic_Aspirin GENERICBOTTLE.json.gz.png
