groverlab/disintegration-fingerprinting/data/bayer_tylenol/20241114T201703_generic_aspirin GENERICBOTTLE.json.gz.png

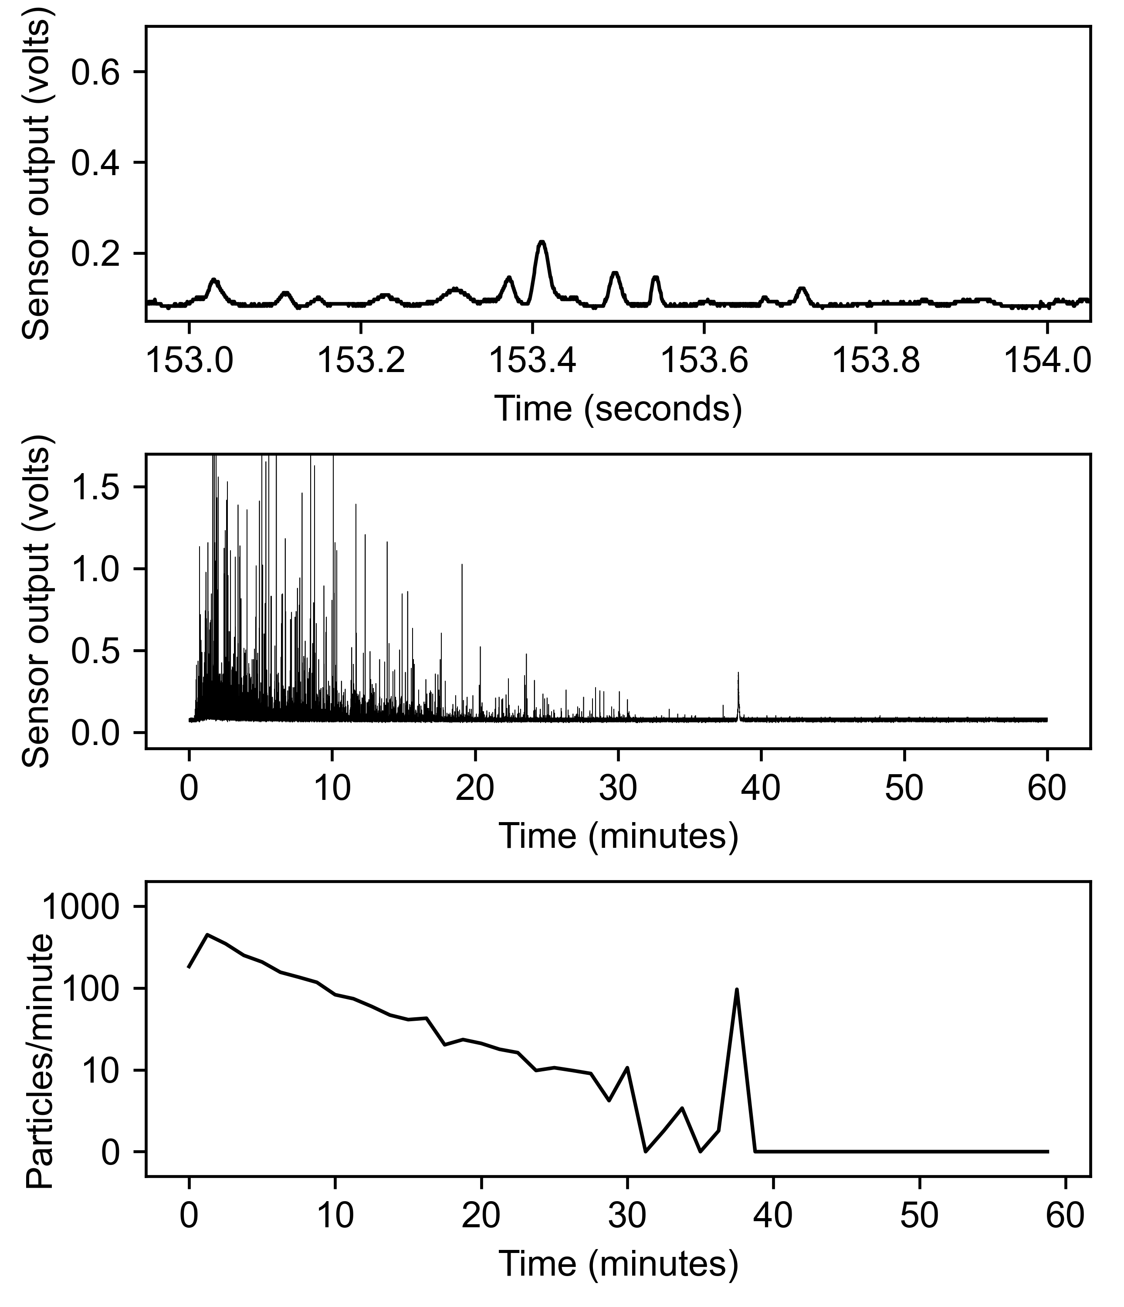
data/bayer_tylenol/20241114T201703_generic_aspirin GENERICBOTTLE.json.gz.png
