groverlab/disintegration-fingerprinting/data/bayer_tylenol/20241115T140108_generic_aspirin GENERICBOTTLE.json.gz.png

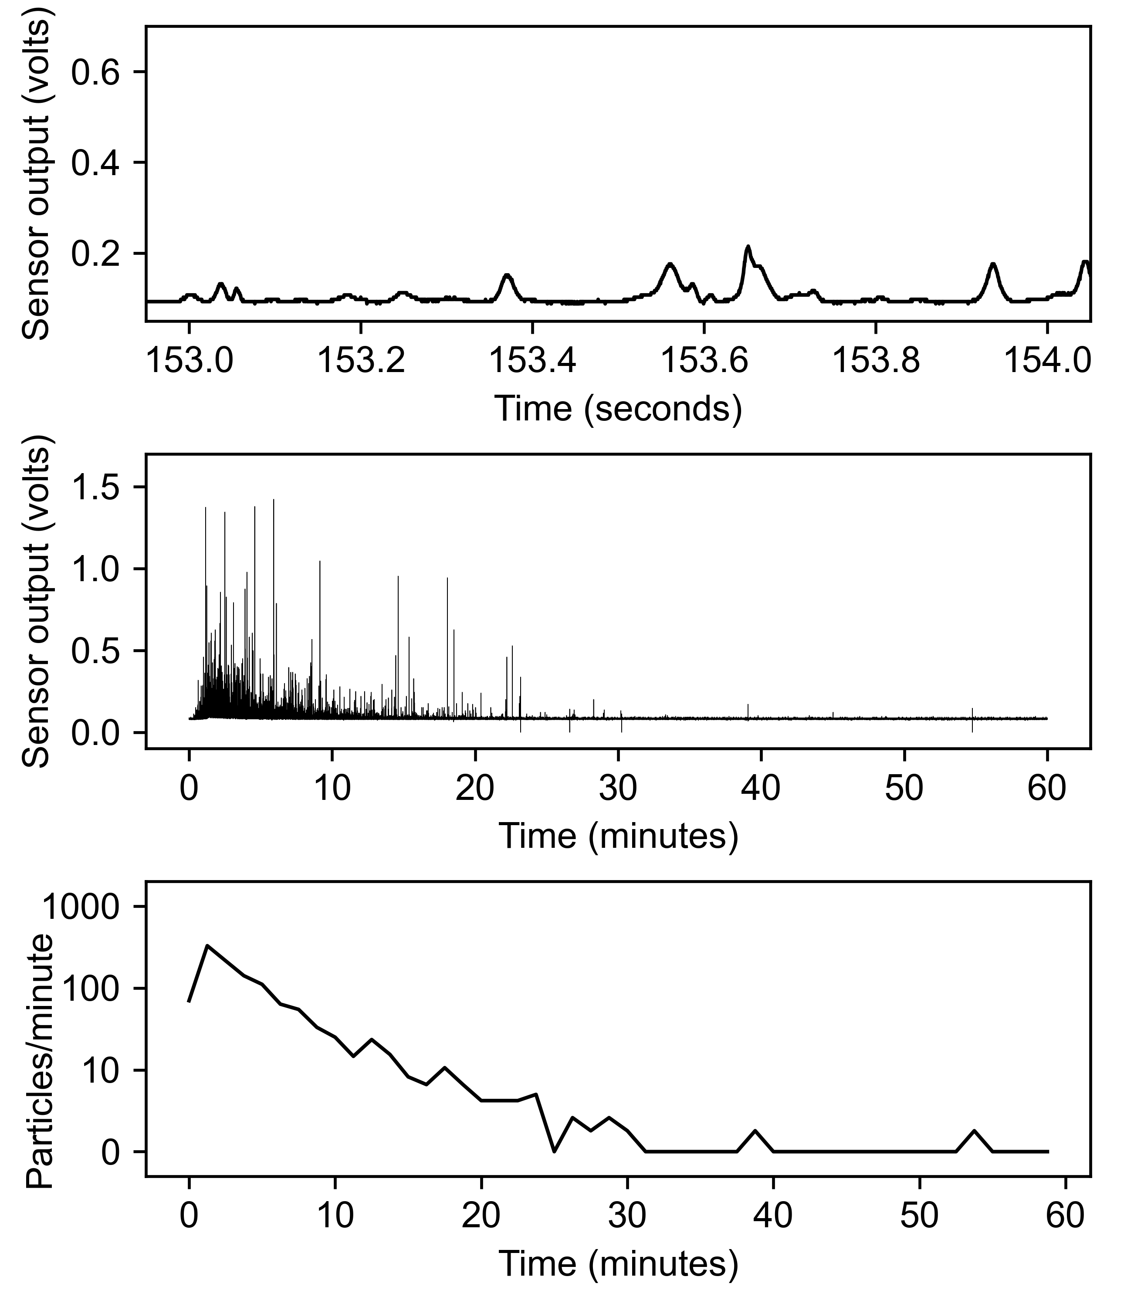
data/bayer_tylenol/20241115T140108_generic_aspirin GENERICBOTTLE.json.gz.png
