groverlab/disintegration-fingerprinting/data/bayer_tylenol/20241119T123655_generic_aspirin GENERICBOTTLE.json.gz.png

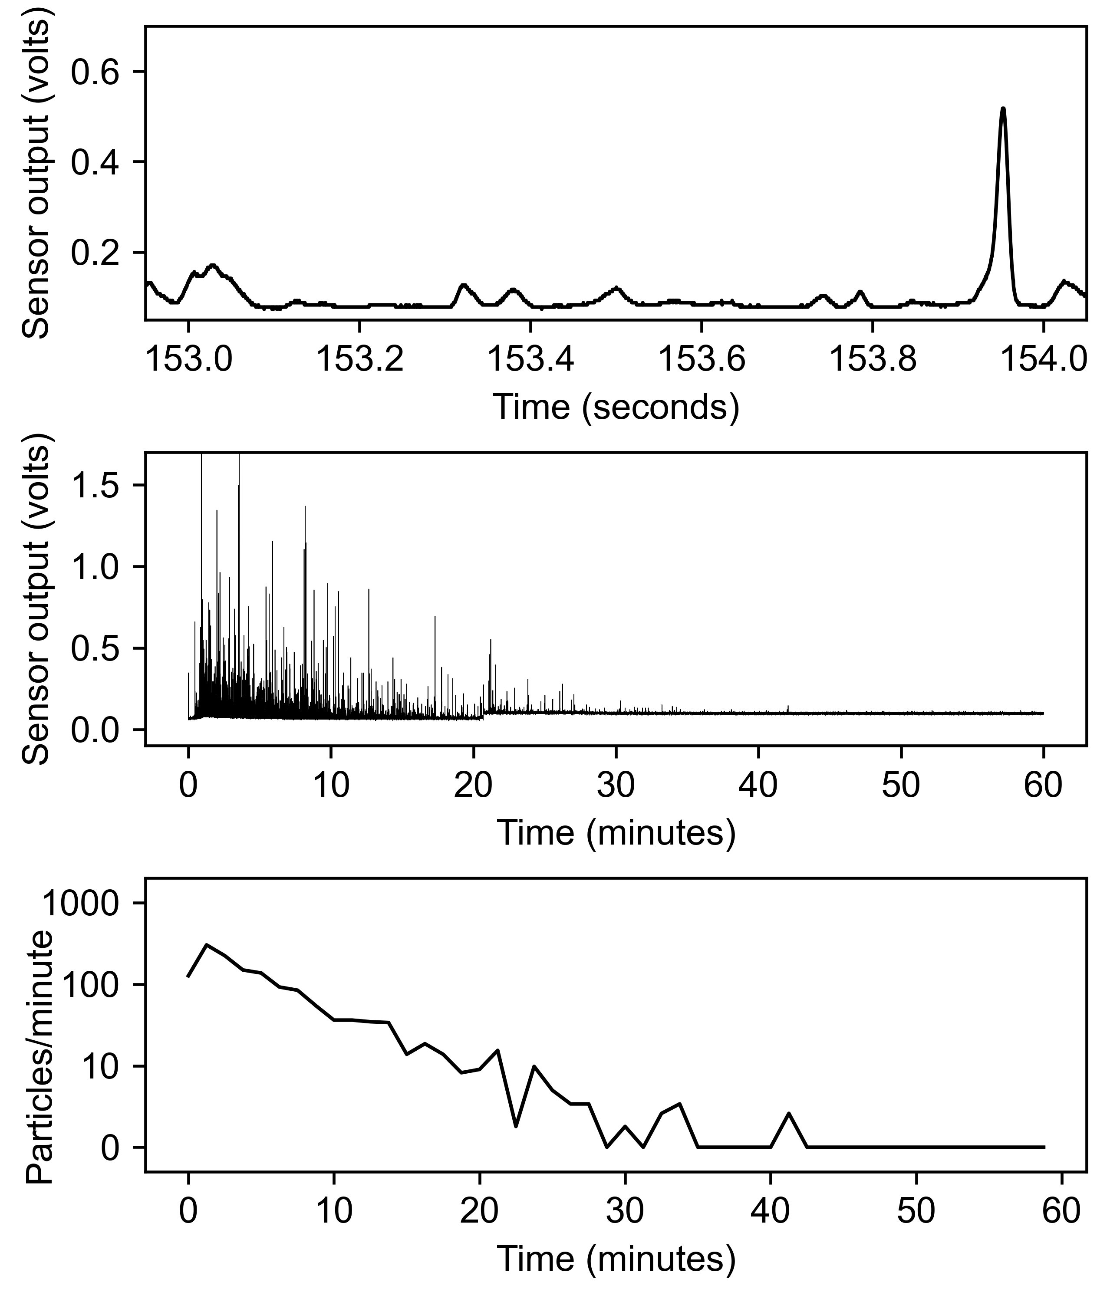
data/bayer_tylenol/20241119T123655_generic_aspirin GENERICBOTTLE.json.gz.png
