groverlab/disintegration-fingerprinting/data/bayer_tylenol/20241119T140627_Bayer_Aspirin BAYERBOTTLE.json.gz.png

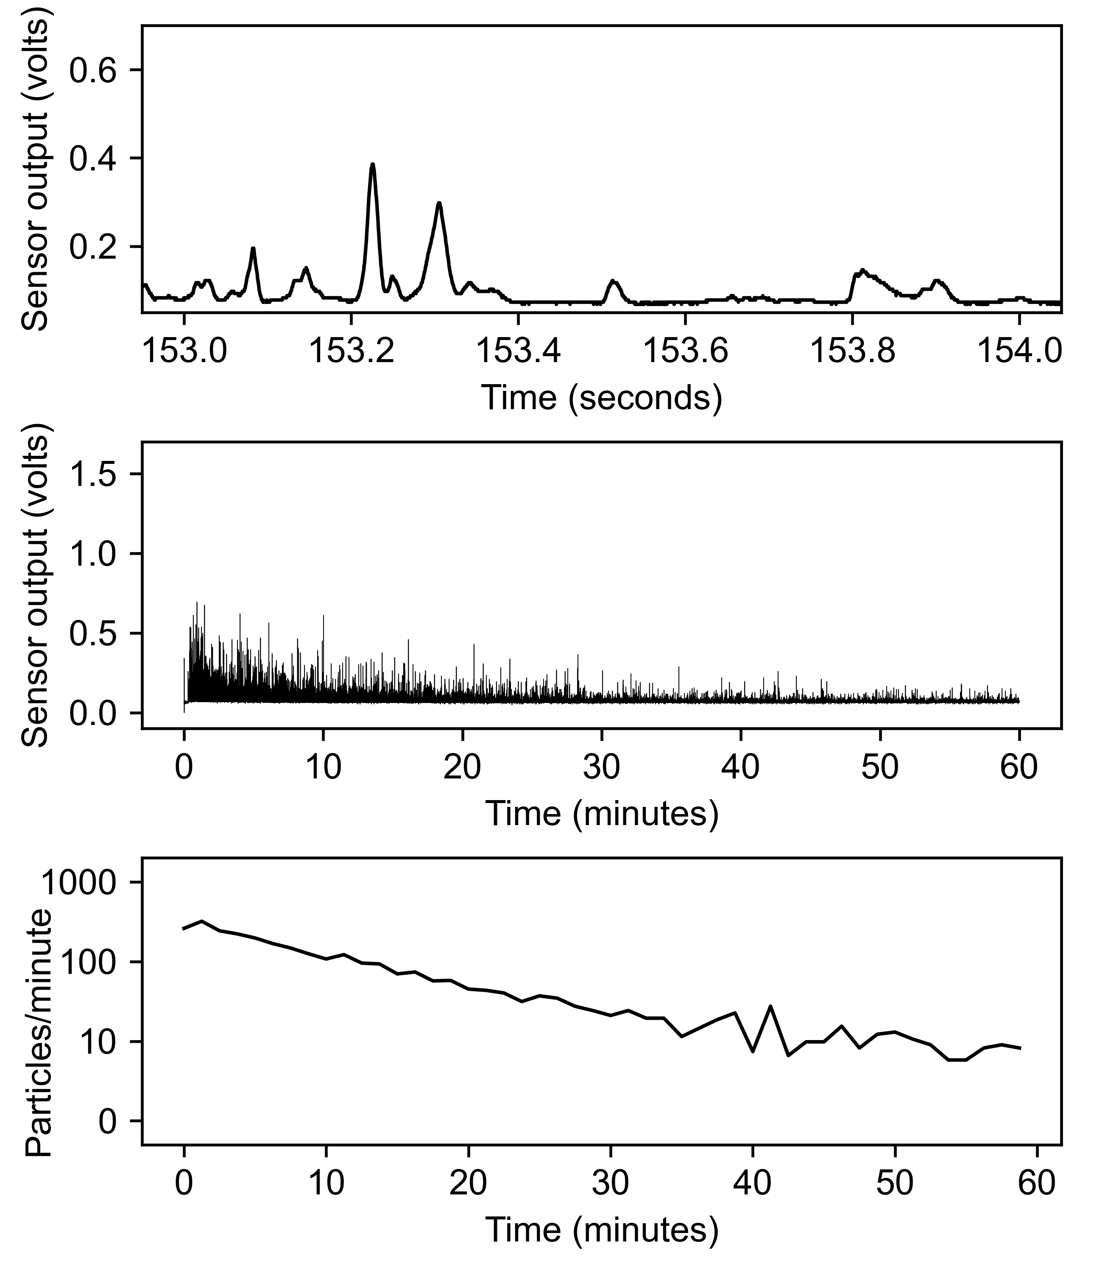
data/bayer_tylenol/20241119T140627_Bayer_Aspirin BAYERBOTTLE.json.gz.png
