groverlab/disintegration-fingerprinting/data/bayer_tylenol/20241119T153203_Generic_Aspirin GENERICBOTTLE.json.gz.png

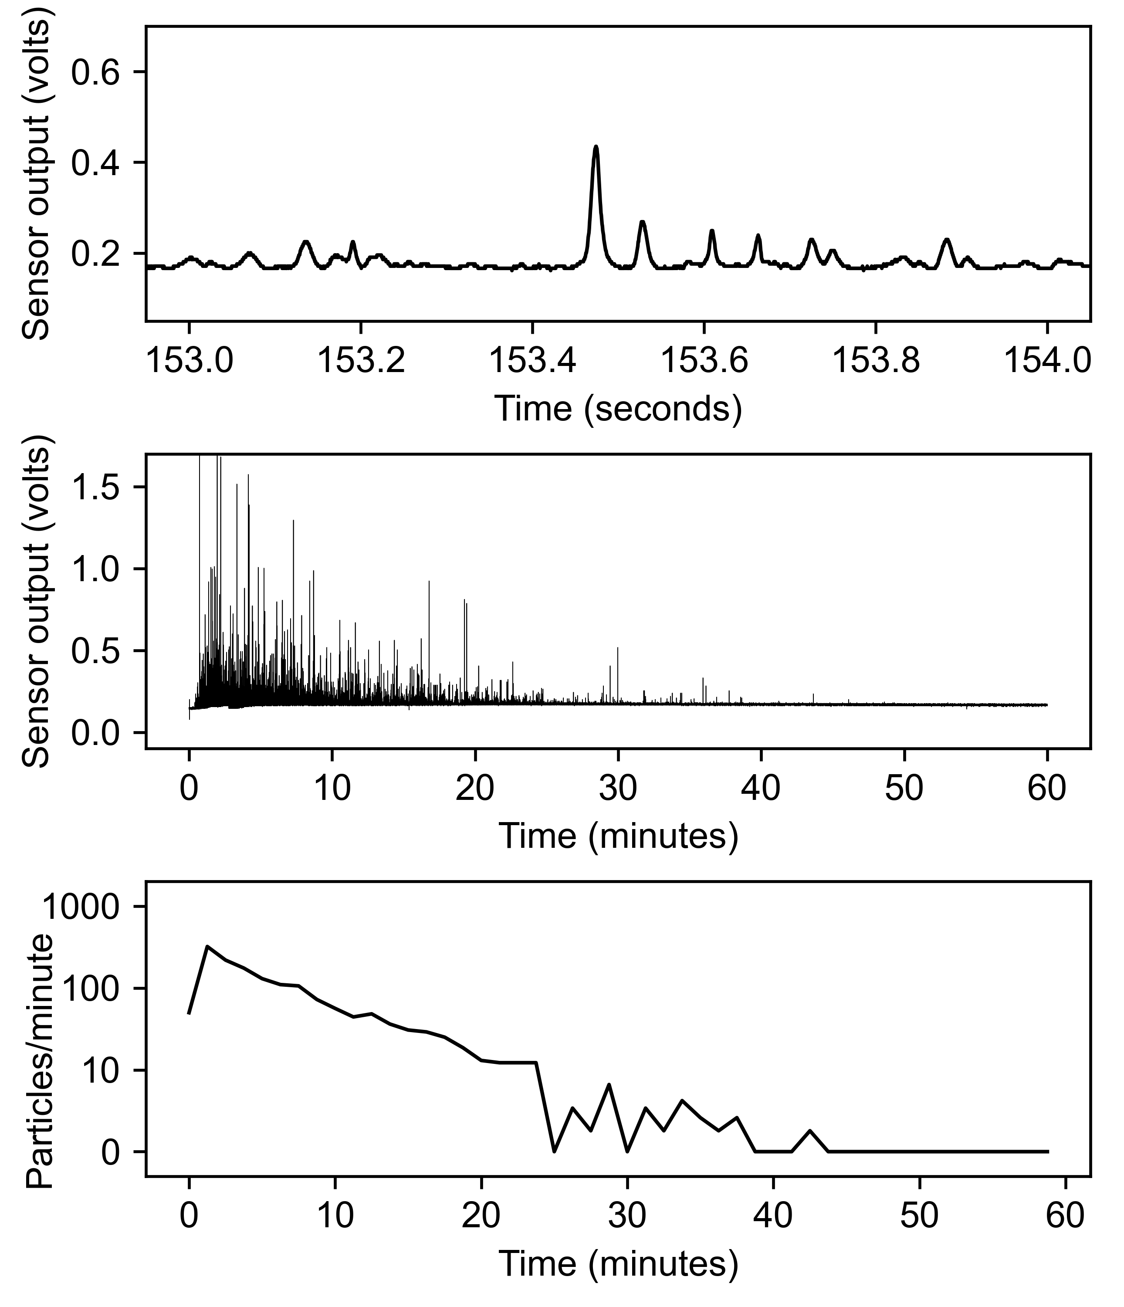
data/bayer_tylenol/20241119T153203_Generic_Aspirin GENERICBOTTLE.json.gz.png
