groverlab/disintegration-fingerprinting/data/bayer_tylenol/20241121T135122_Bayer_Aspirin BAYERBOTTLE.json.gz.png

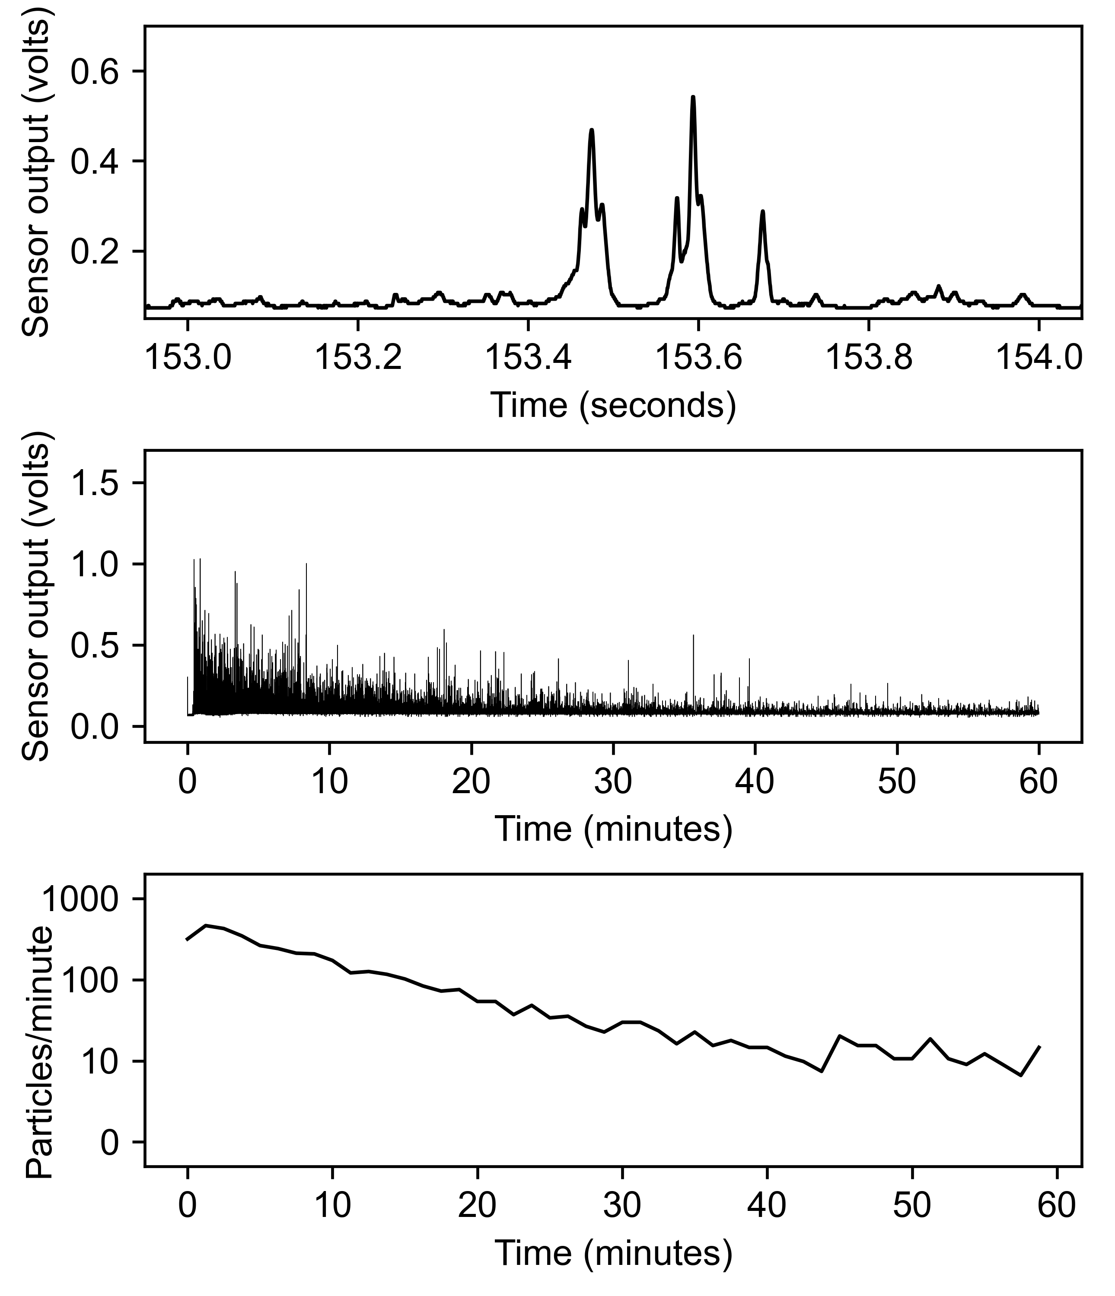
data/bayer_tylenol/20241121T135122_Bayer_Aspirin BAYERBOTTLE.json.gz.png
