groverlab/disintegration-fingerprinting/data/bayer_tylenol/20241121T150345_Generic_Aspirin GENERICBOTTLE.json.gz.png

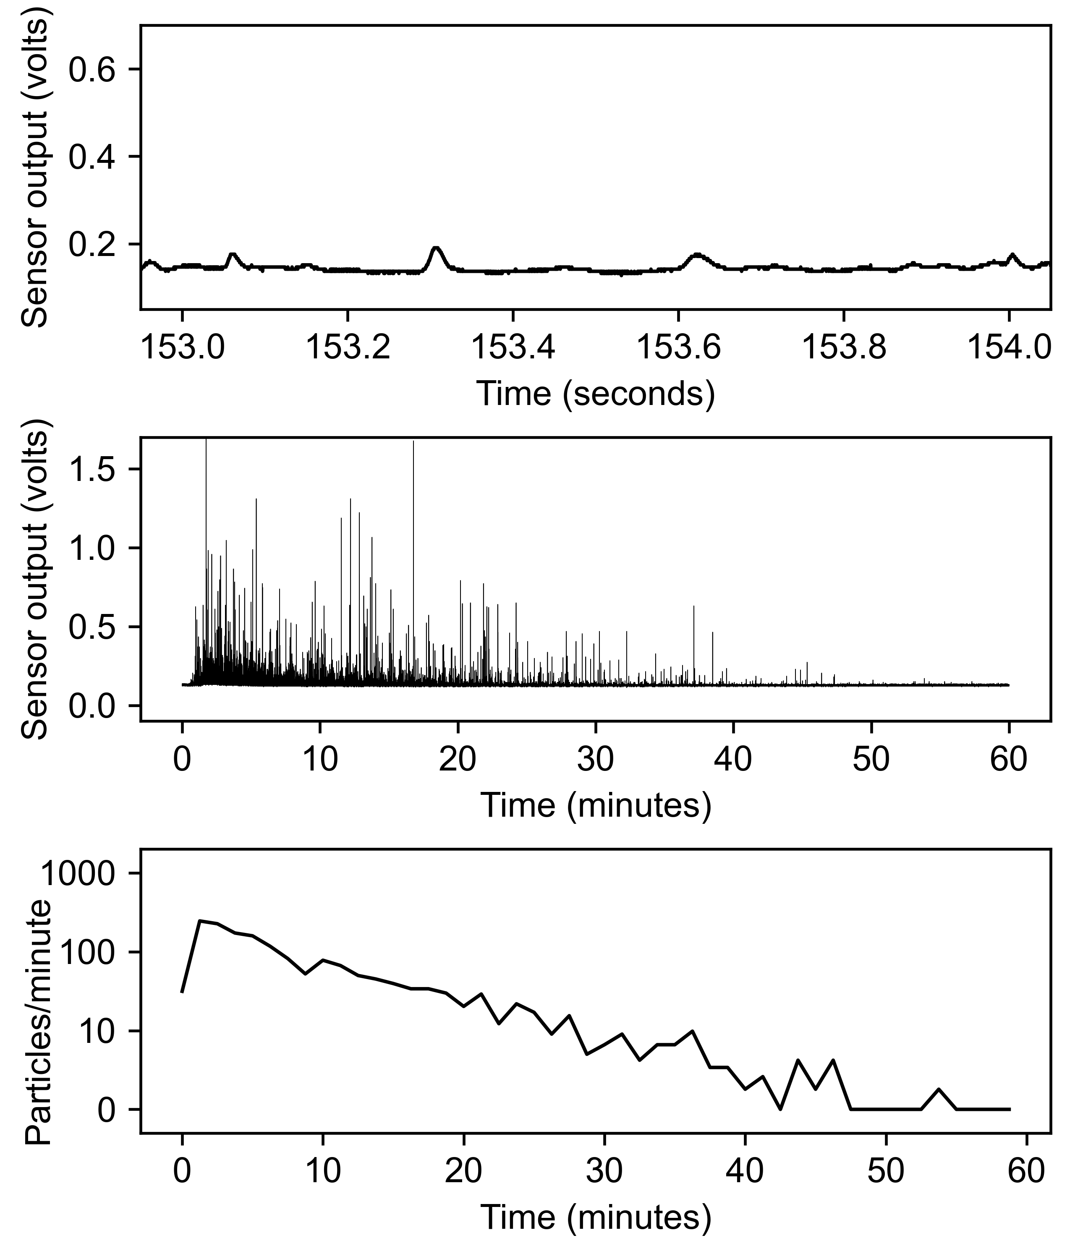
data/bayer_tylenol/20241121T150345_Generic_Aspirin GENERICBOTTLE.json.gz.png
