groverlab/disintegration-fingerprinting/data/bayer_tylenol/20241126T114333_Bayer_Aspirin BAYERBOTTLE.json.gz.png

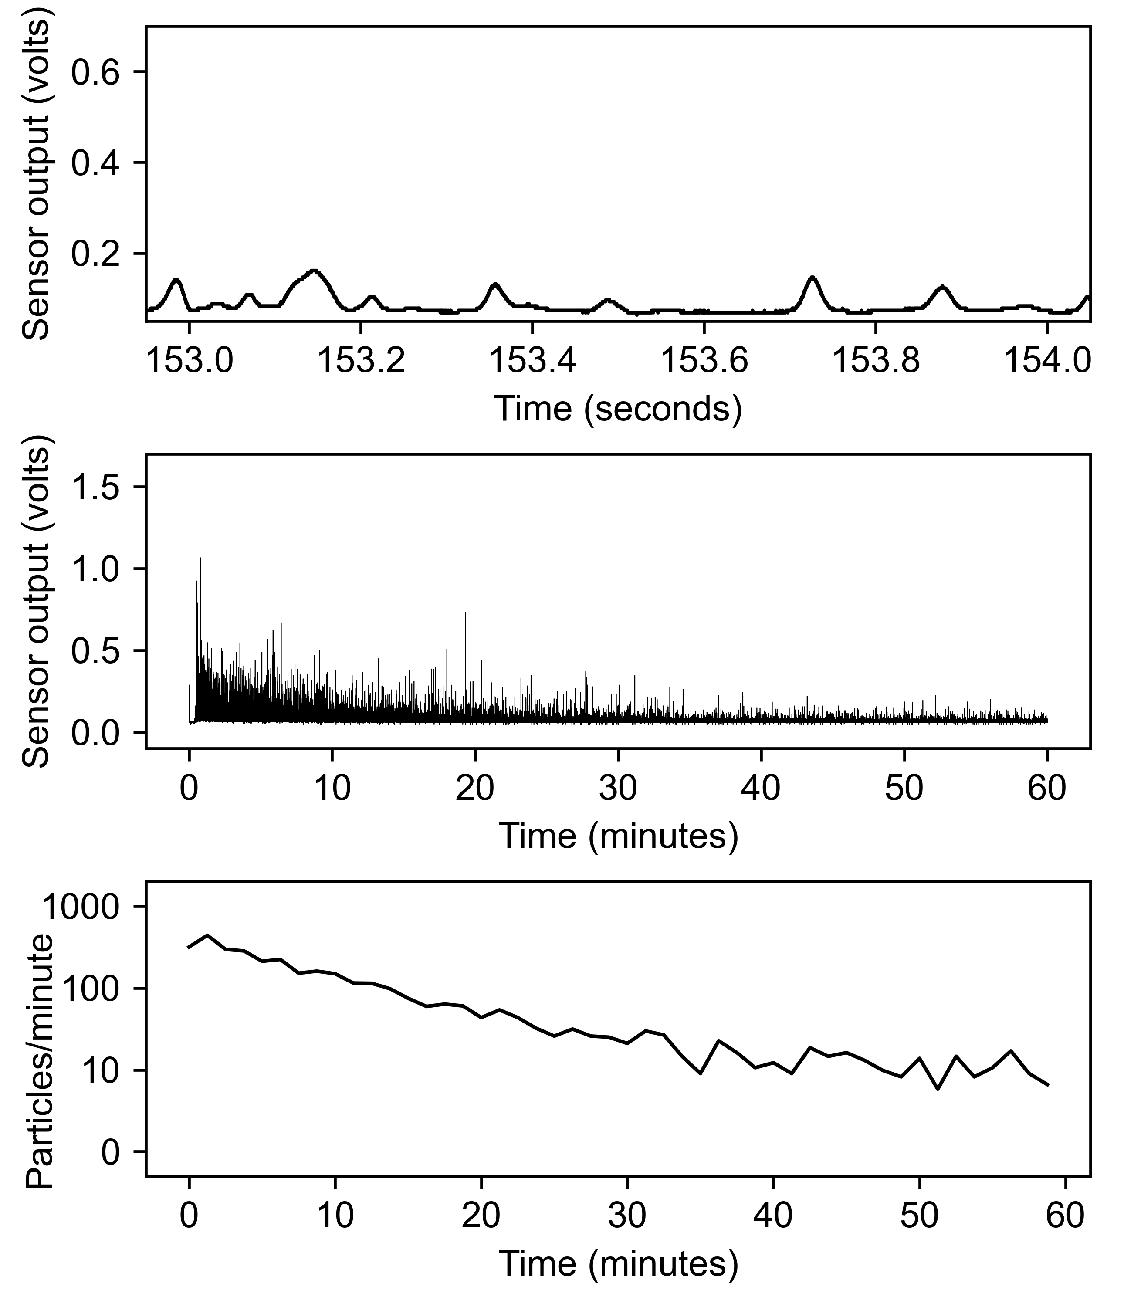
data/bayer_tylenol/20241126T114333_Bayer_Aspirin BAYERBOTTLE.json.gz.png
