groverlab/disintegration-fingerprinting/data/bayer_tylenol/20241203T115929_generic_aspirin GENERICBOTTLE.json.gz.png

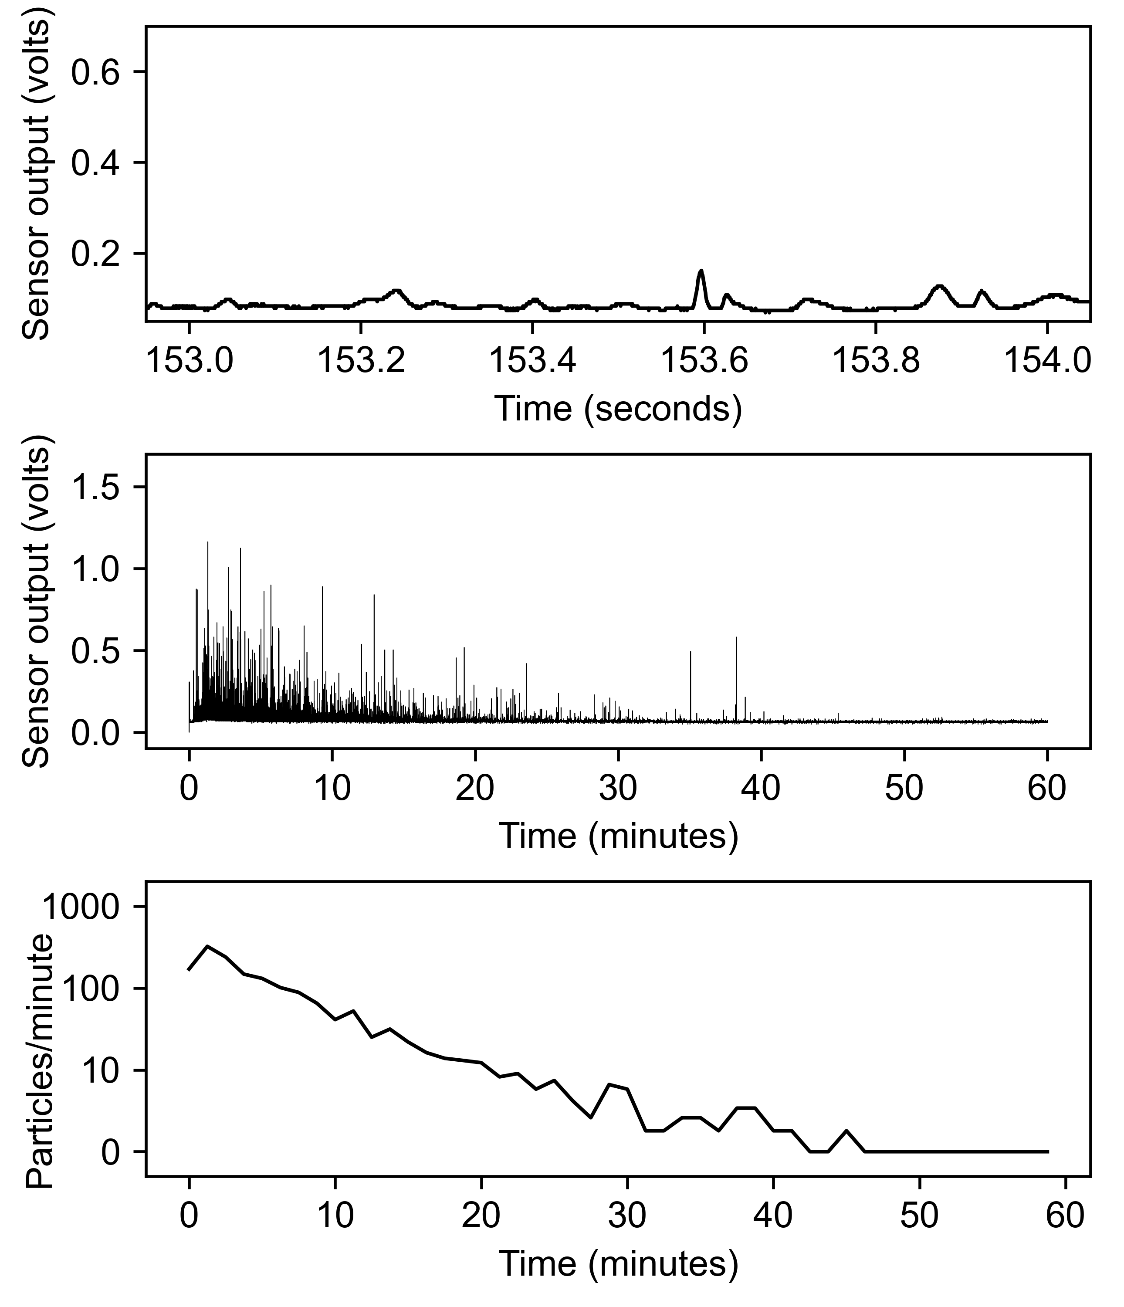
data/bayer_tylenol/20241203T115929_generic_aspirin GENERICBOTTLE.json.gz.png
