groverlab/disintegration-fingerprinting/data/bayer_tylenol/20241203T115945_Generic_Aspirin GENERICBOTTLE.json.gz.png

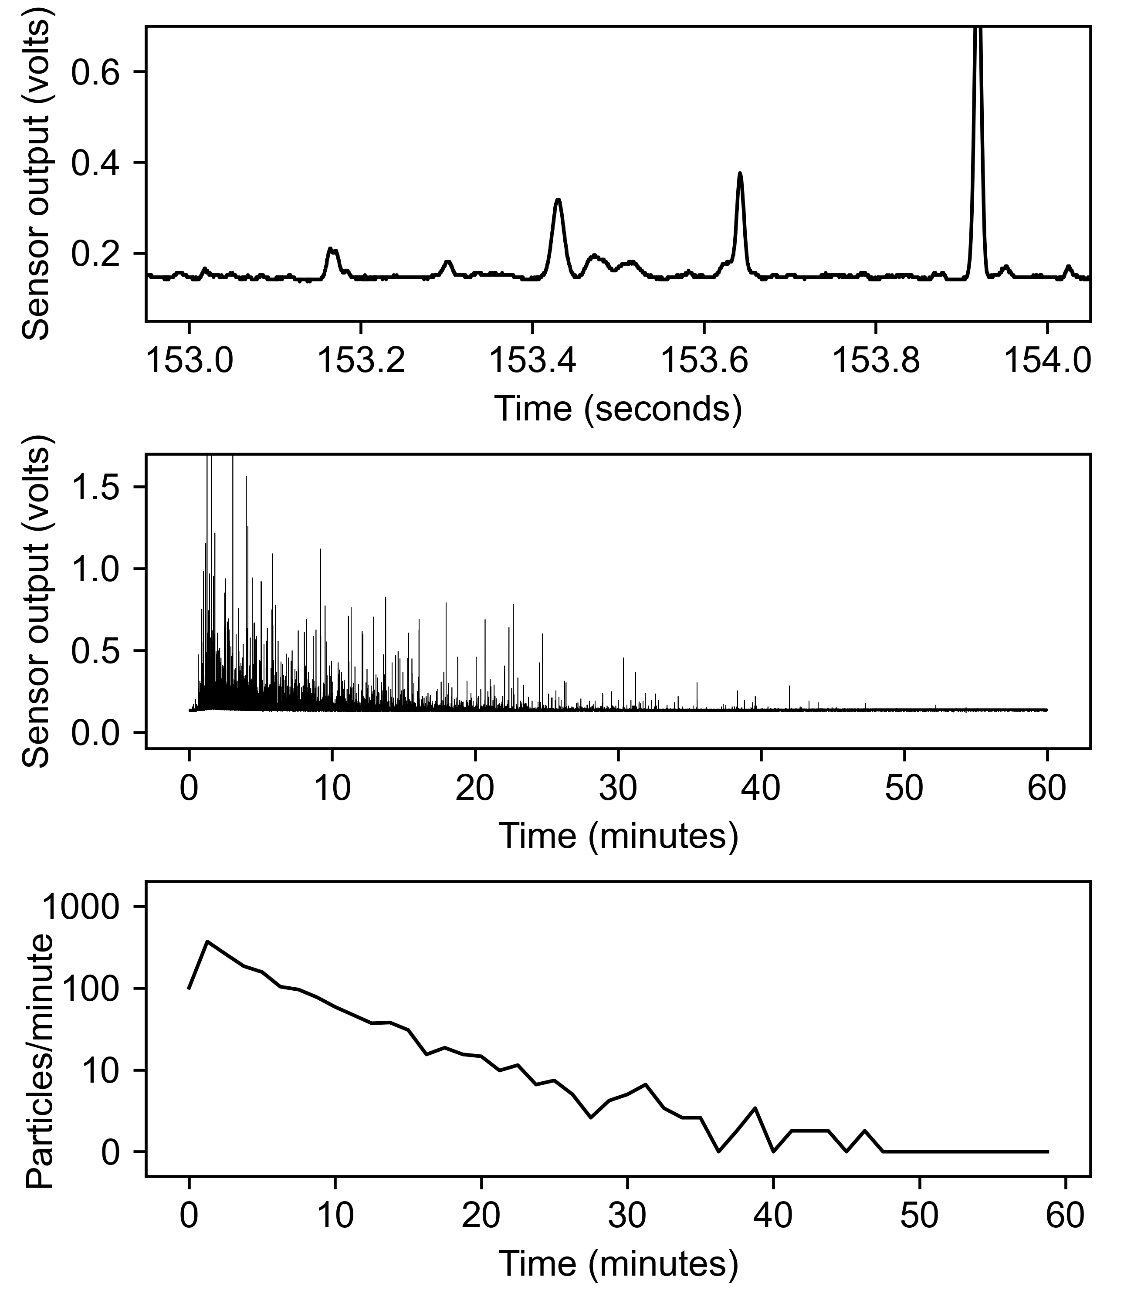
data/bayer_tylenol/20241203T115945_Generic_Aspirin GENERICBOTTLE.json.gz.png
