groverlab/disintegration-fingerprinting/data/bayer_tylenol/20241203T131113_Bayer_Aspirin BAYERBOTTLE.json.gz.png

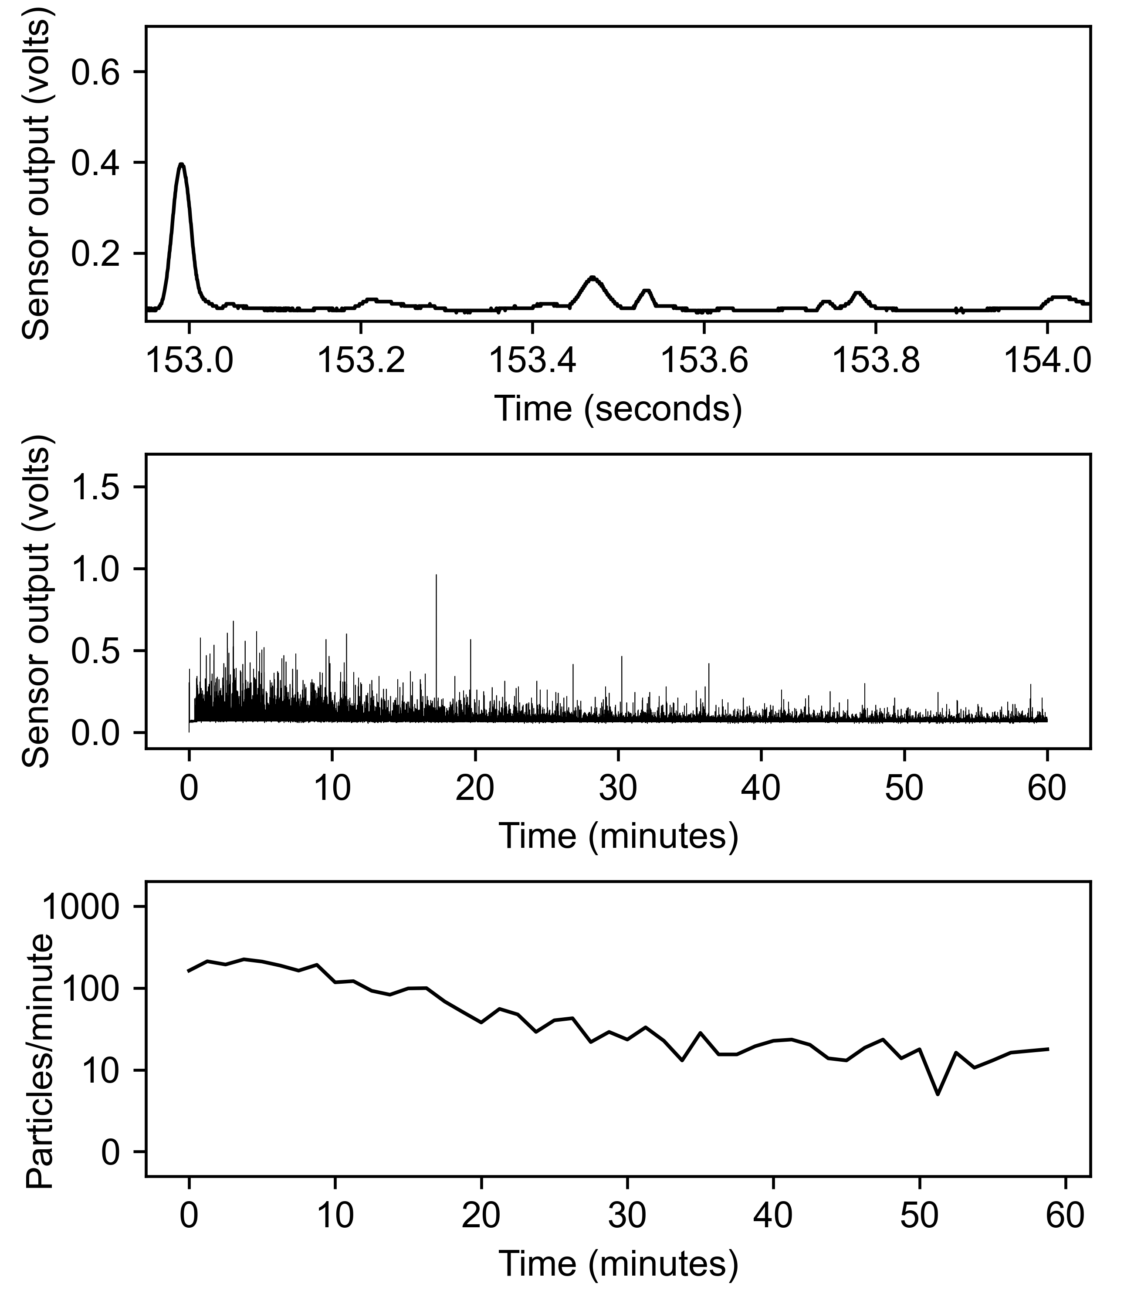
data/bayer_tylenol/20241203T131113_Bayer_Aspirin BAYERBOTTLE.json.gz.png
