groverlab/disintegration-fingerprinting/data/bayer_tylenol_only_heatmap.png

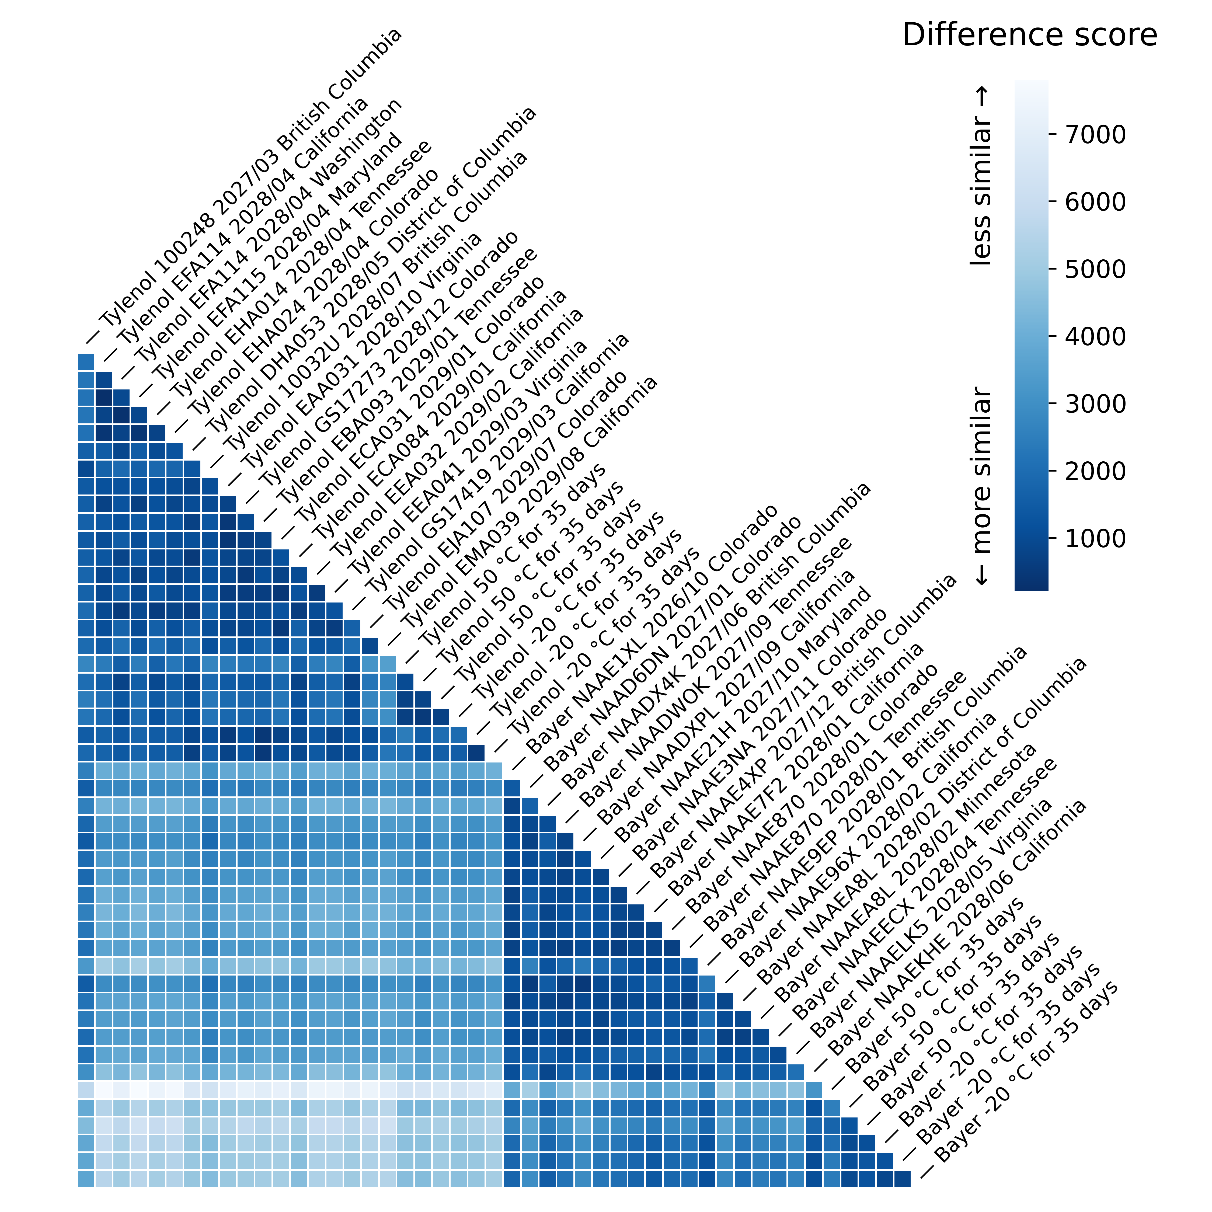
data/bayer_tylenol_only_heatmap.png
