groverlab/disintegration-fingerprinting/data/bayer_tylenol_only_subdirs.png

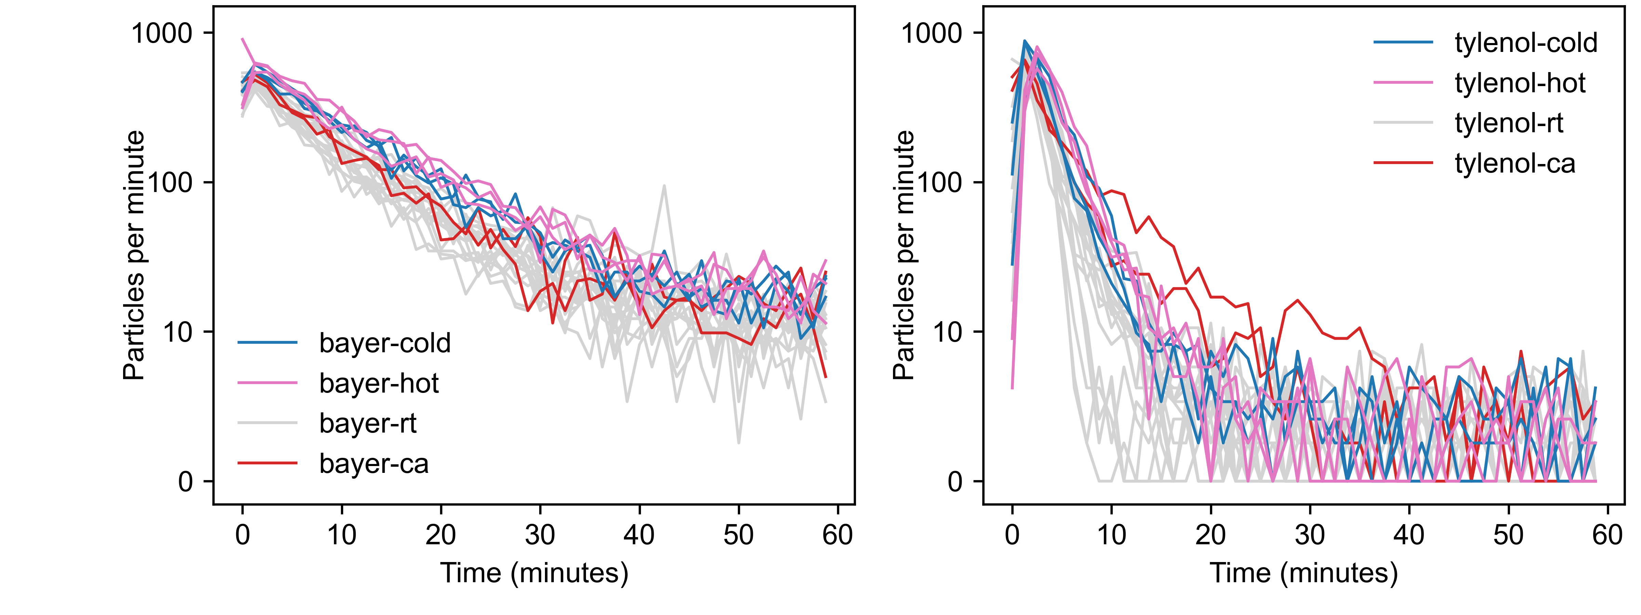
data/bayer_tylenol_only_subdirs.png
