groverlab/disintegration-fingerprinting/data/bayer_tylenol_only_subdirs/ART/518 20251112T125208_A09one ART.json.gz.png

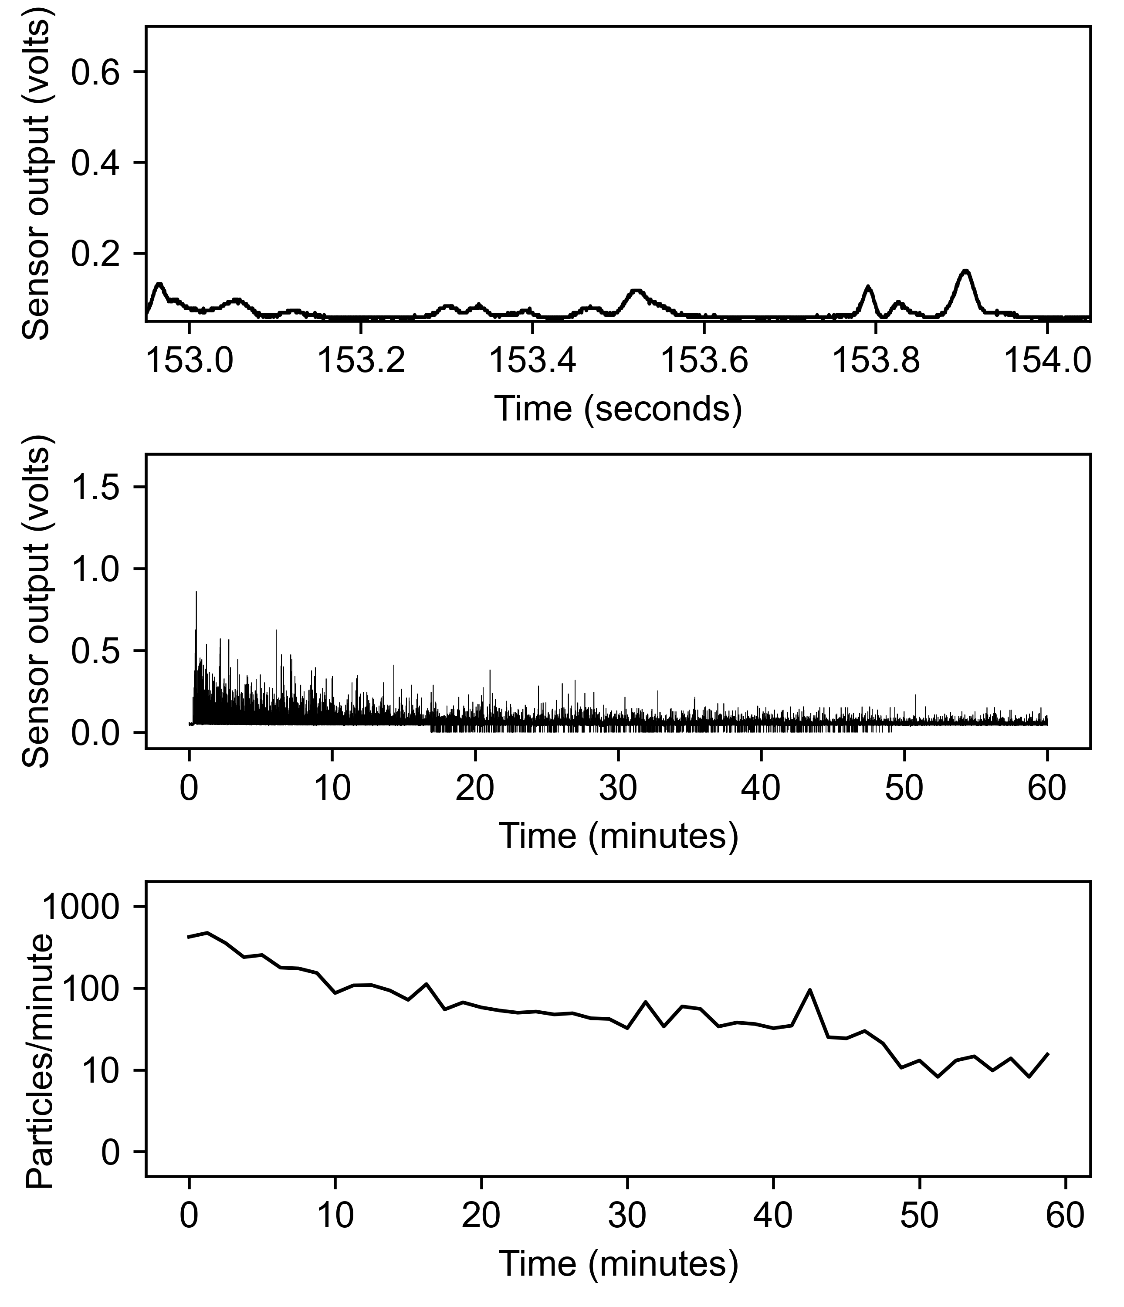
data/bayer_tylenol_only_subdirs/ART/518 20251112T125208_A09one ART.json.gz.png
