groverlab/disintegration-fingerprinting/data/bayer_tylenol_only_subdirs_bigplot.png

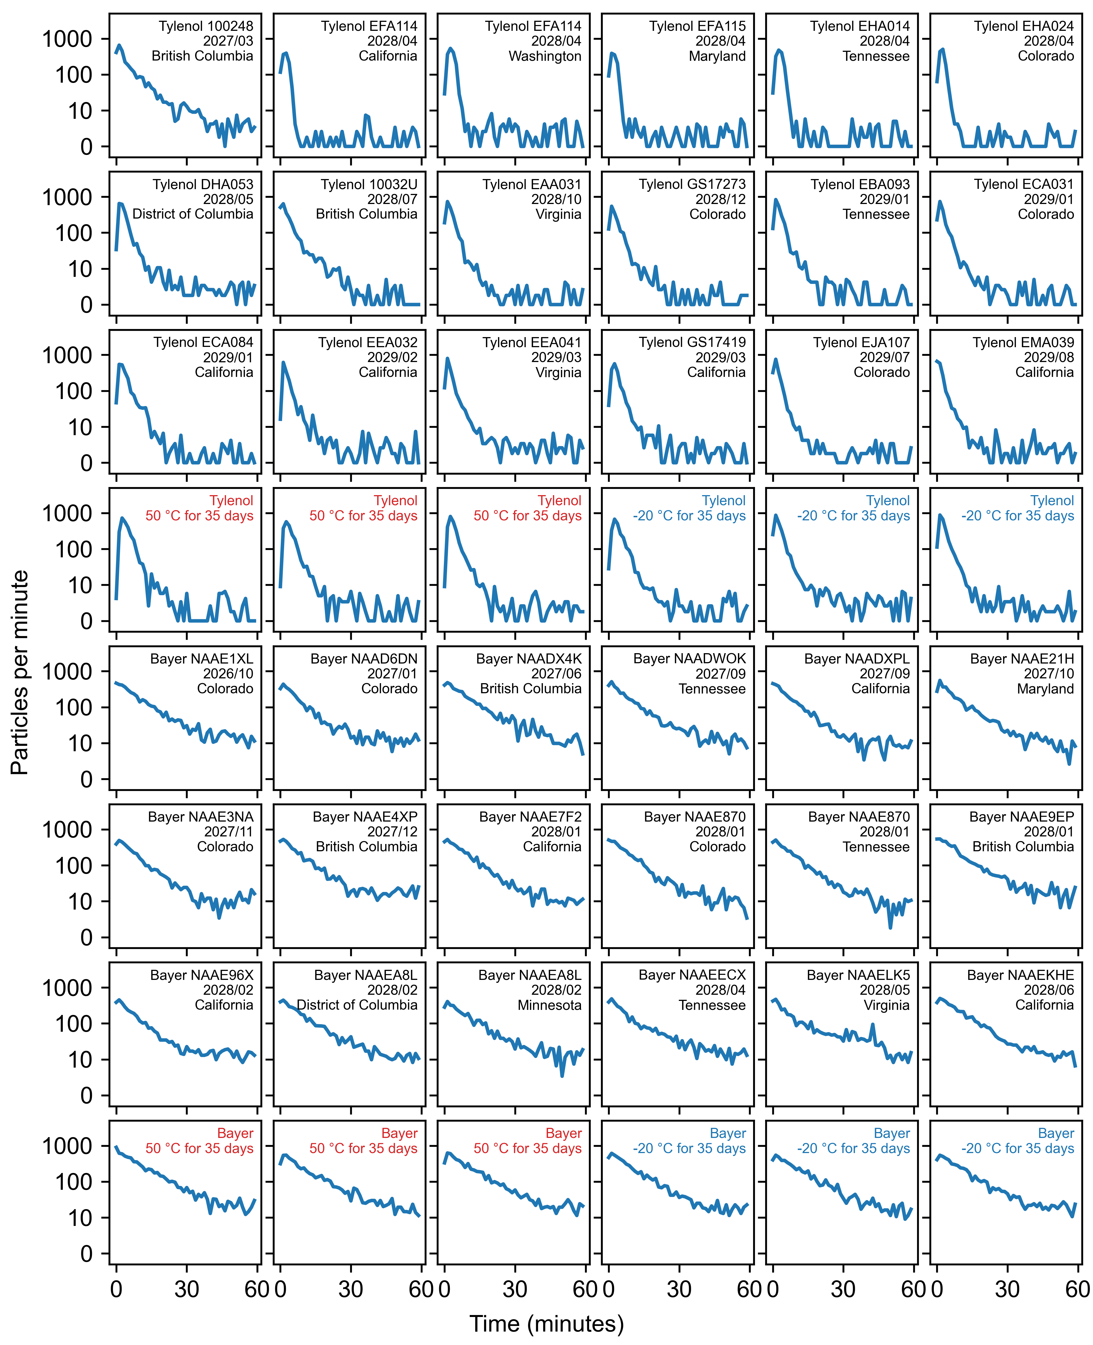
data/bayer_tylenol_only_subdirs_bigplot.png
