groverlab/disintegration-fingerprinting/data/bayer_tylenol_significance.png

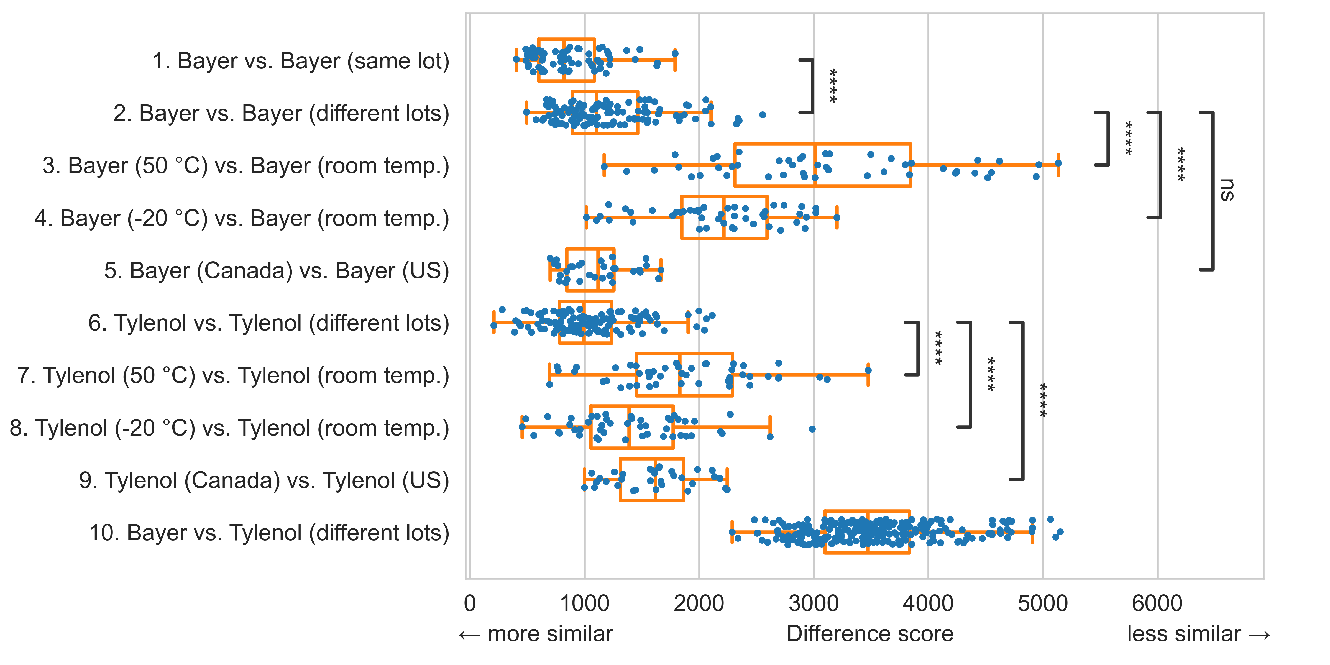
data/bayer_tylenol_significance.png
