groverlab/disintegration-fingerprinting/data/beads.png

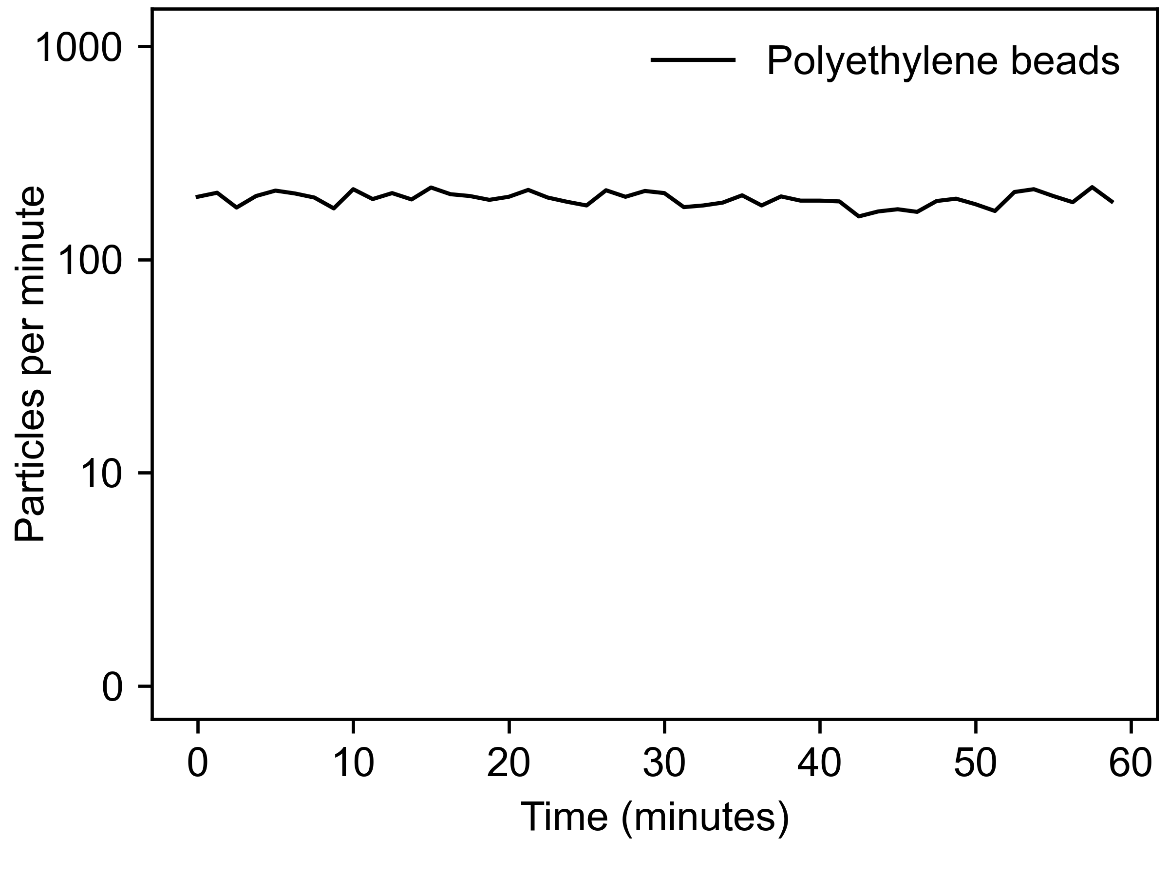
data/beads.png
