groverlab/disintegration-fingerprinting/data/beads/20250412T082900_425-500_um_red_polyethylene_beads_NaCl_detergent.json.gz.png

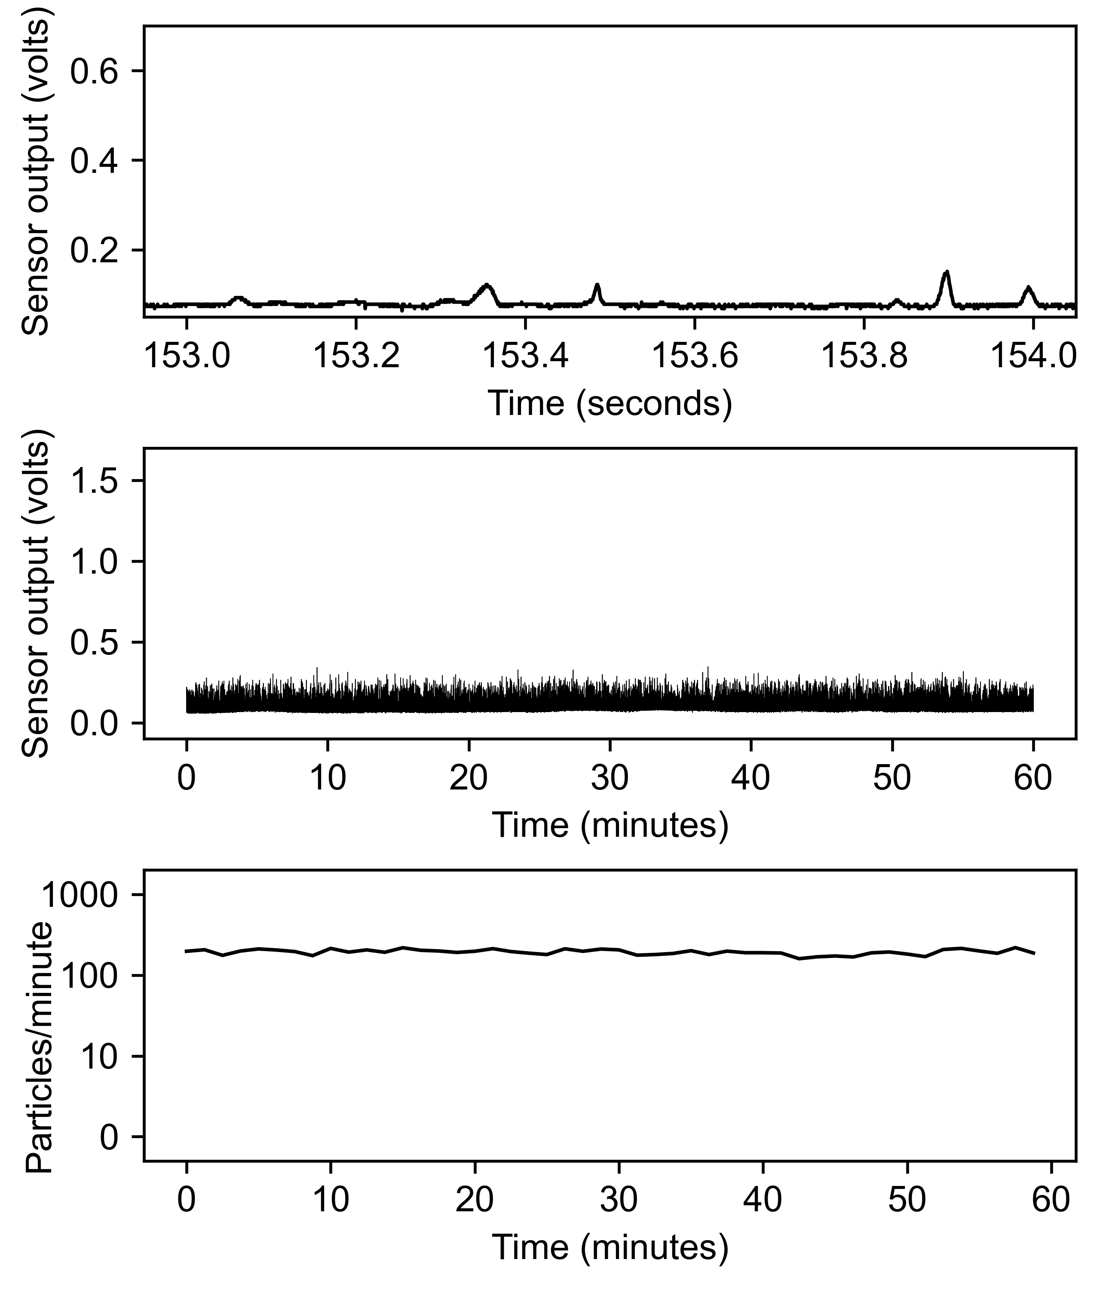
data/beads/20250412T082900_425-500_um_red_polyethylene_beads_NaCl_detergent.json.gz.png
