groverlab/disintegration-fingerprinting/data/difference_score.png

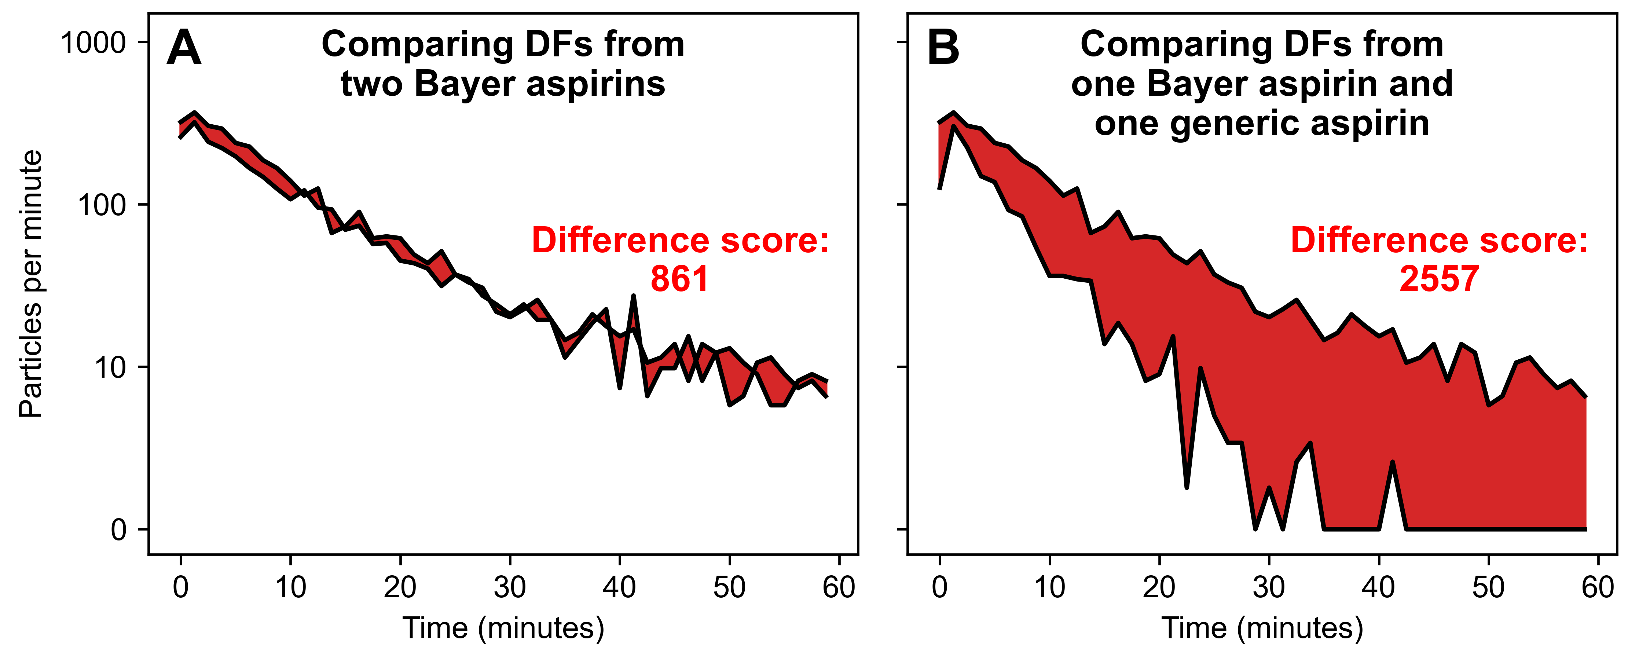
data/difference_score.png
