groverlab/disintegration-fingerprinting/data/long.png

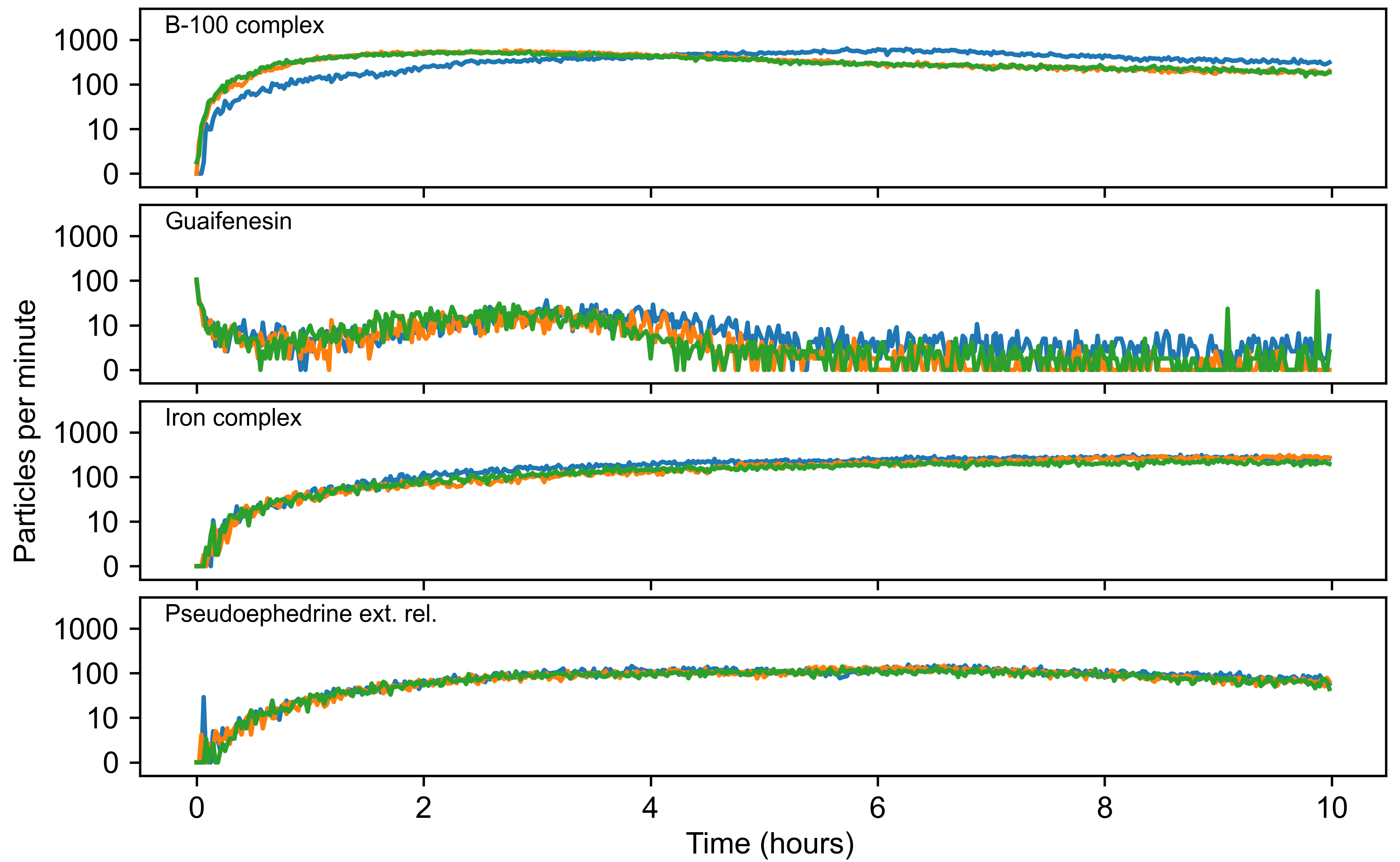
data/long.png
