groverlab/disintegration-fingerprinting/data/long/B-100 complex/20241126T093349_b-100_complex_long.json.gz.png

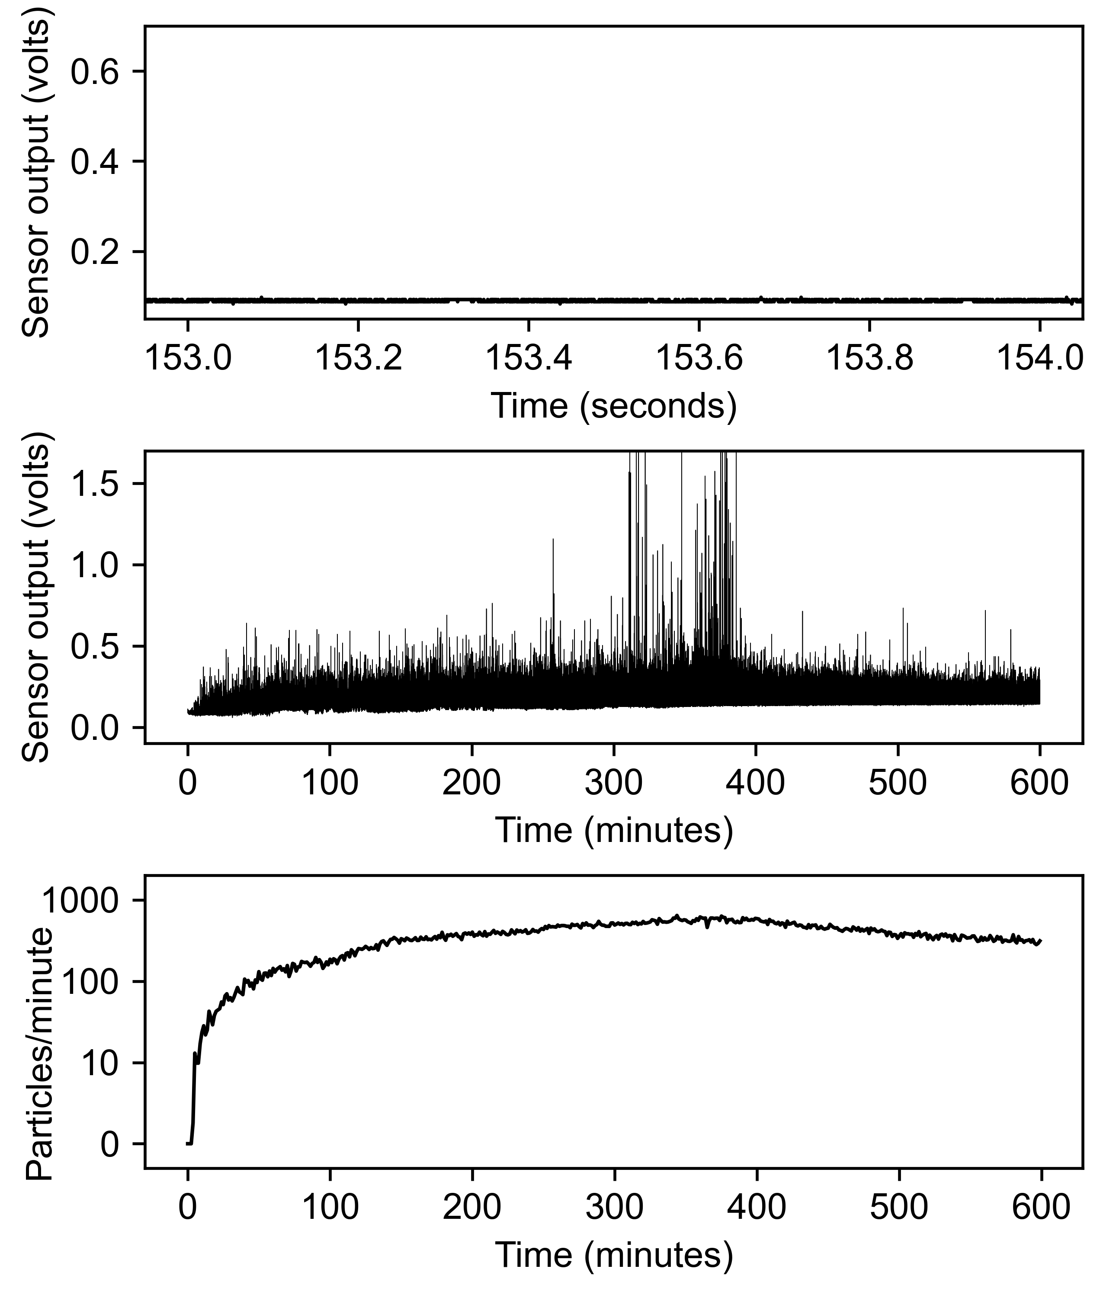
data/long/B-100 complex/20241126T093349_b-100_complex_long.json.gz.png
