groverlab/disintegration-fingerprinting/data/long/Guaifenesin/20241117T211932_guaifenesin_generic_12_hours.json.gz.png

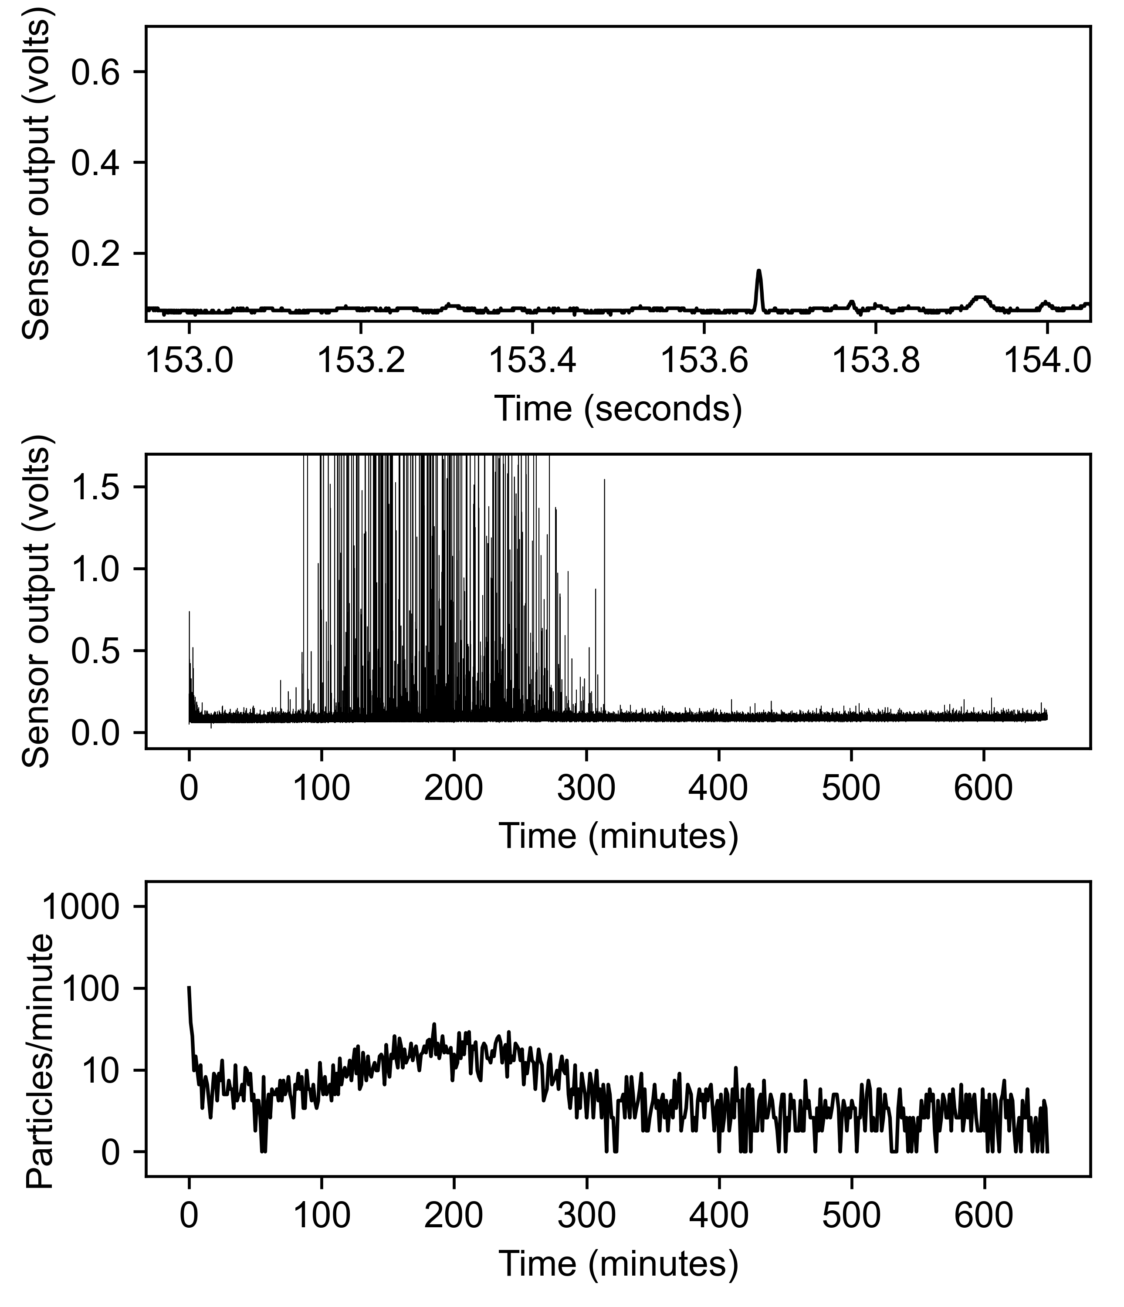
data/long/Guaifenesin/20241117T211932_guaifenesin_generic_12_hours.json.gz.png
