groverlab/disintegration-fingerprinting/data/long/Guaifenesin/20241209T211352_guaifenesin_generic_12_hours.json.gz.png

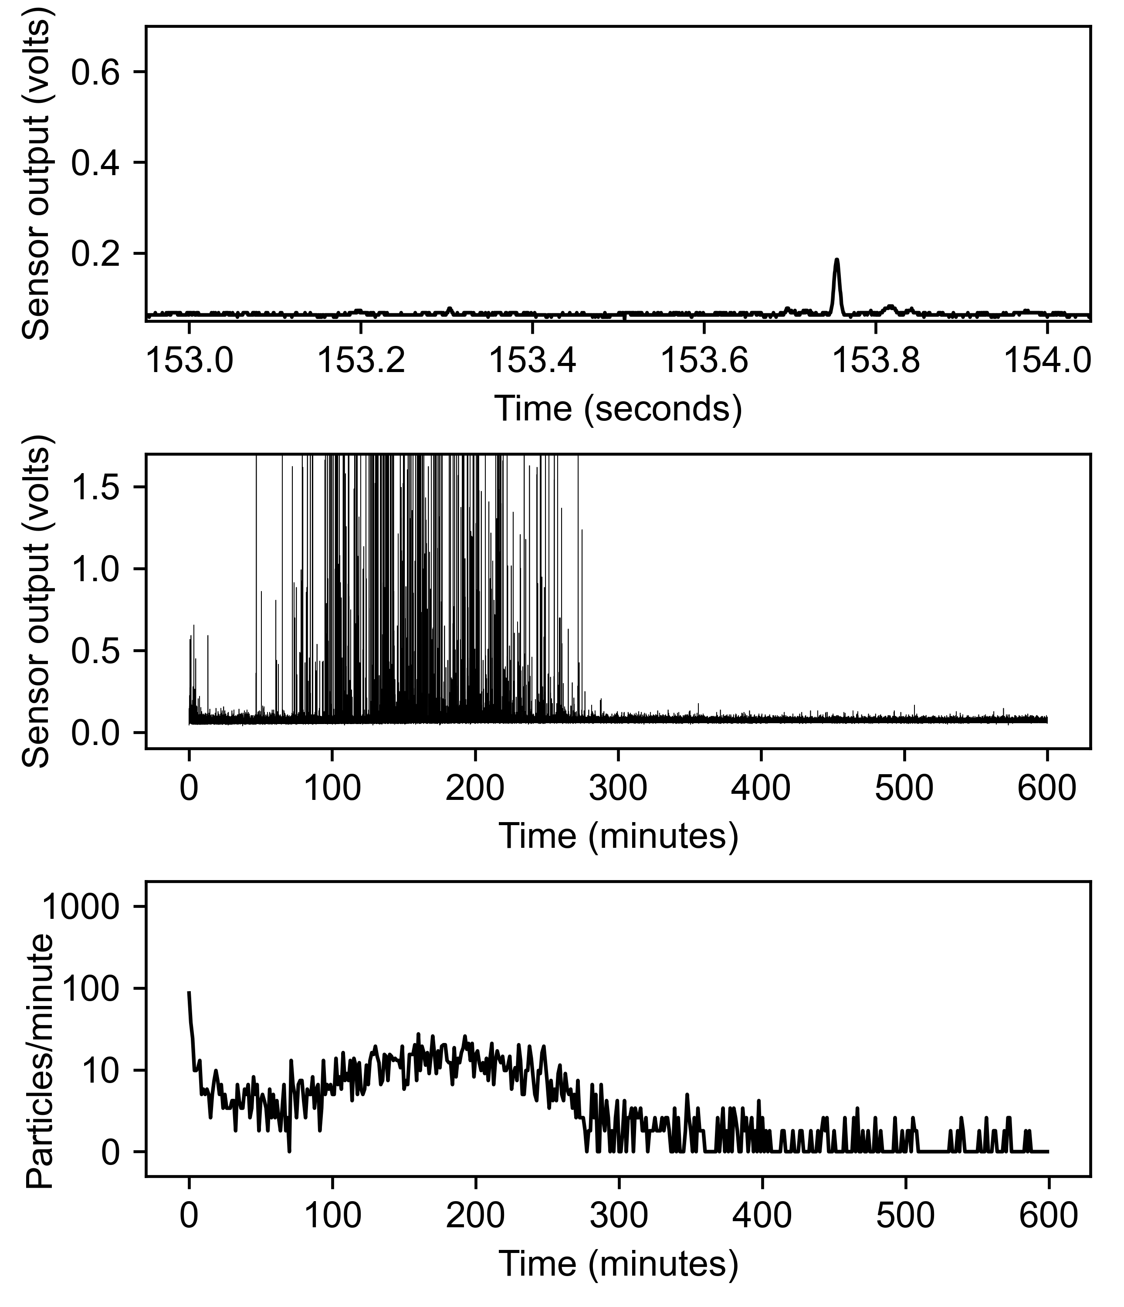
data/long/Guaifenesin/20241209T211352_guaifenesin_generic_12_hours.json.gz.png
