groverlab/disintegration-fingerprinting/data/long/Guaifenesin/20241210T215931_guaifenesin_generic_12_hours.json.gz.png

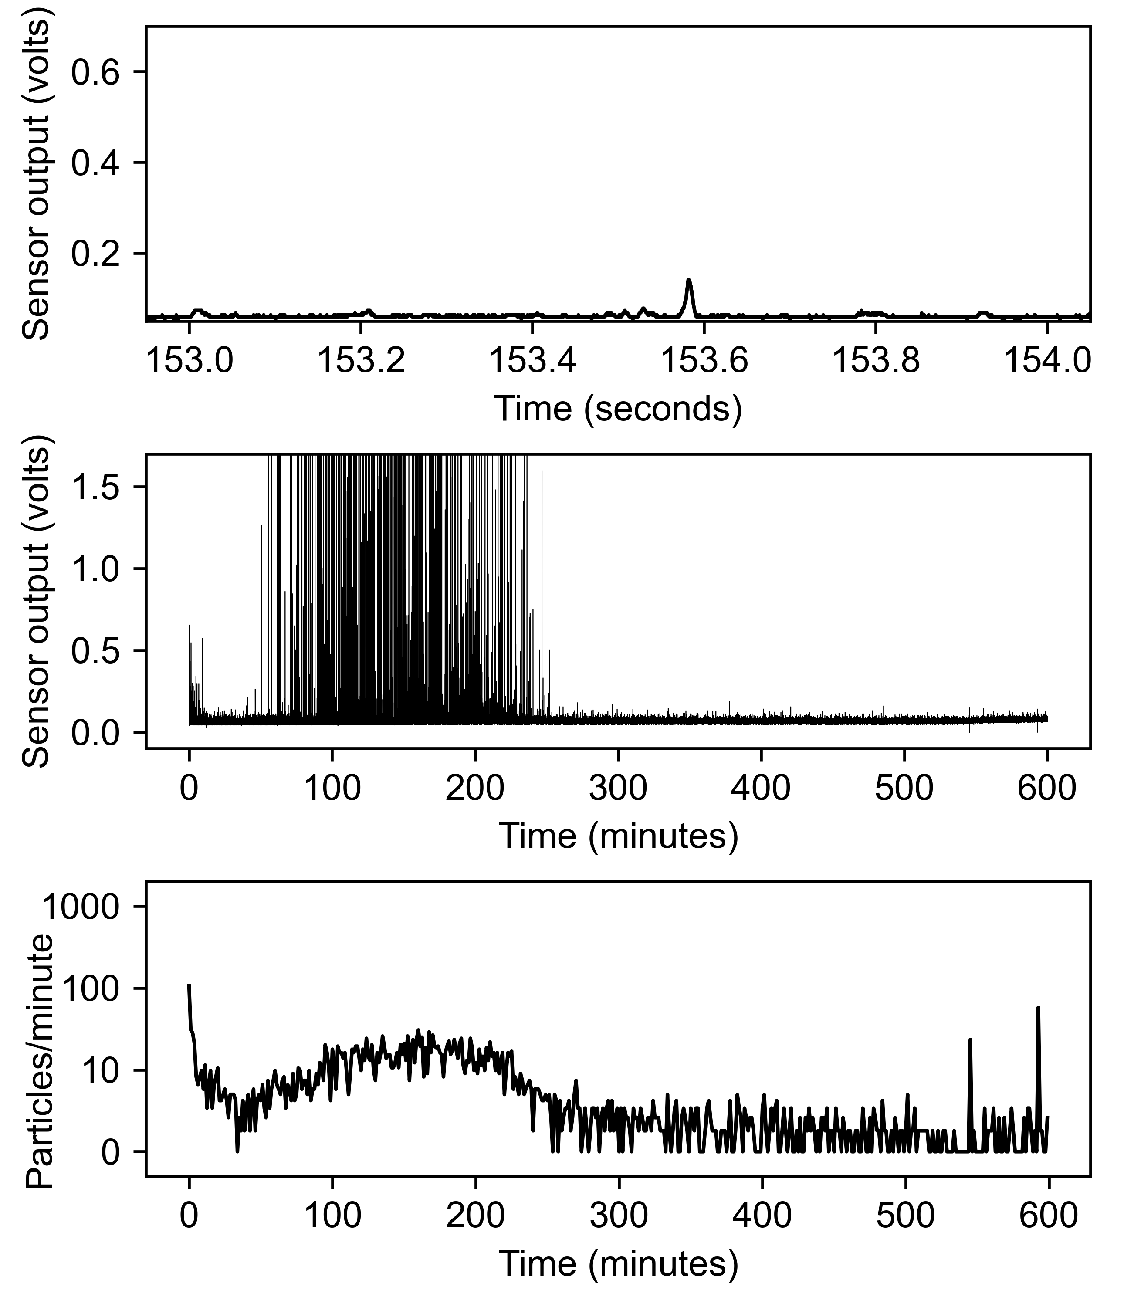
data/long/Guaifenesin/20241210T215931_guaifenesin_generic_12_hours.json.gz.png
