groverlab/disintegration-fingerprinting/data/long/Iron complex/20241125T220916_iron_complex_long.json.gz.png

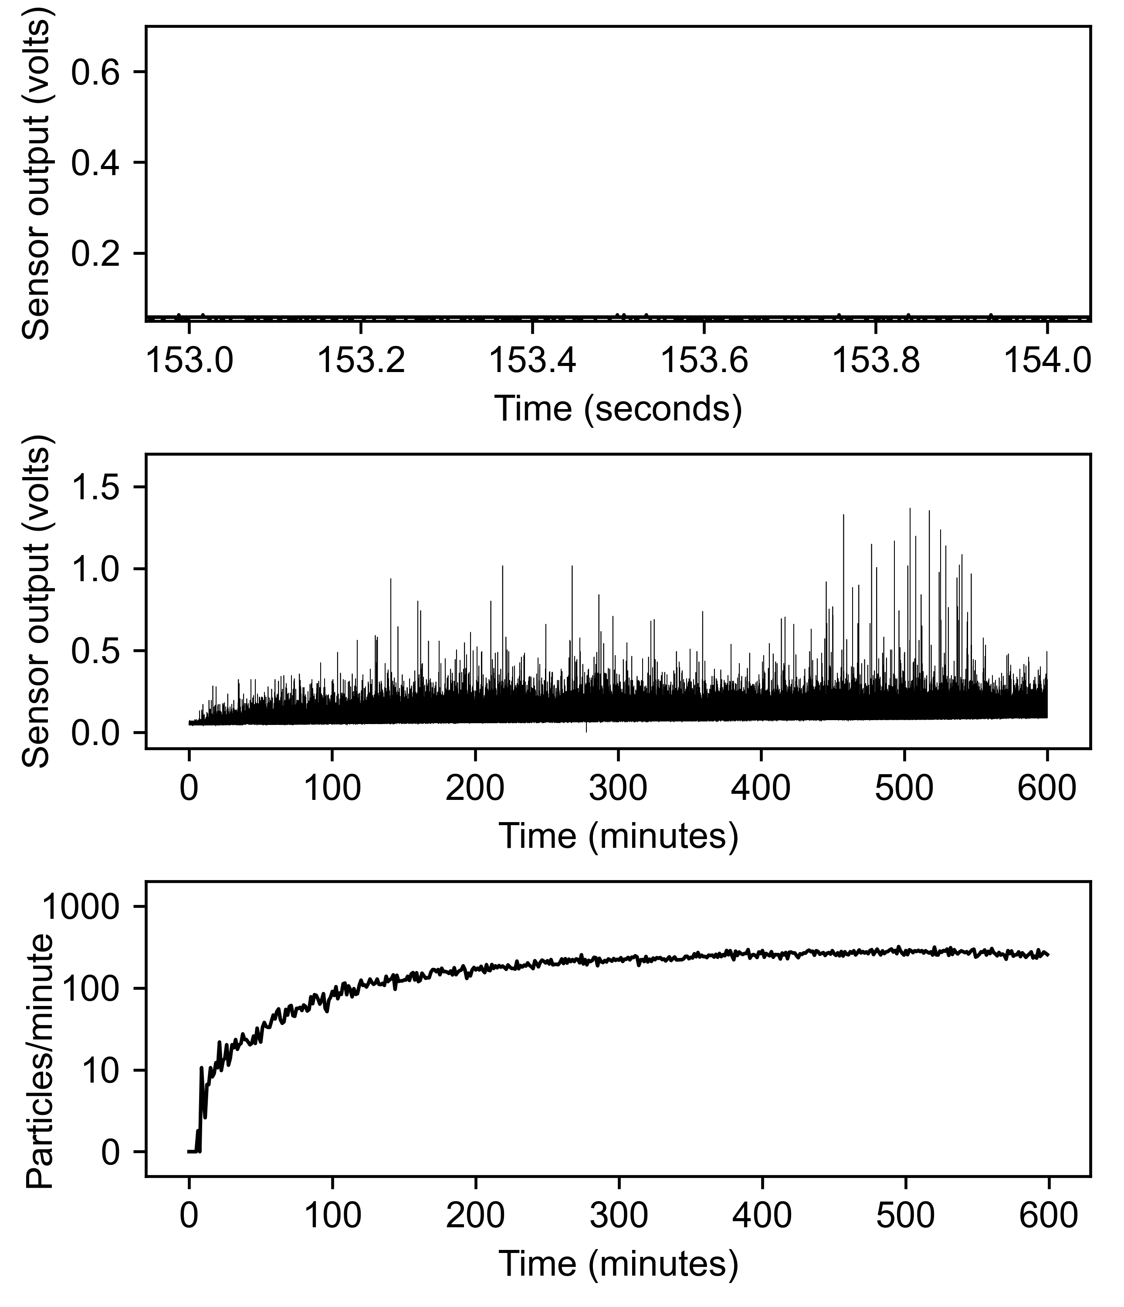
data/long/Iron complex/20241125T220916_iron_complex_long.json.gz.png
