groverlab/disintegration-fingerprinting/data/long/Iron complex/20241211T221002_iron_complex_long.json.gz.png

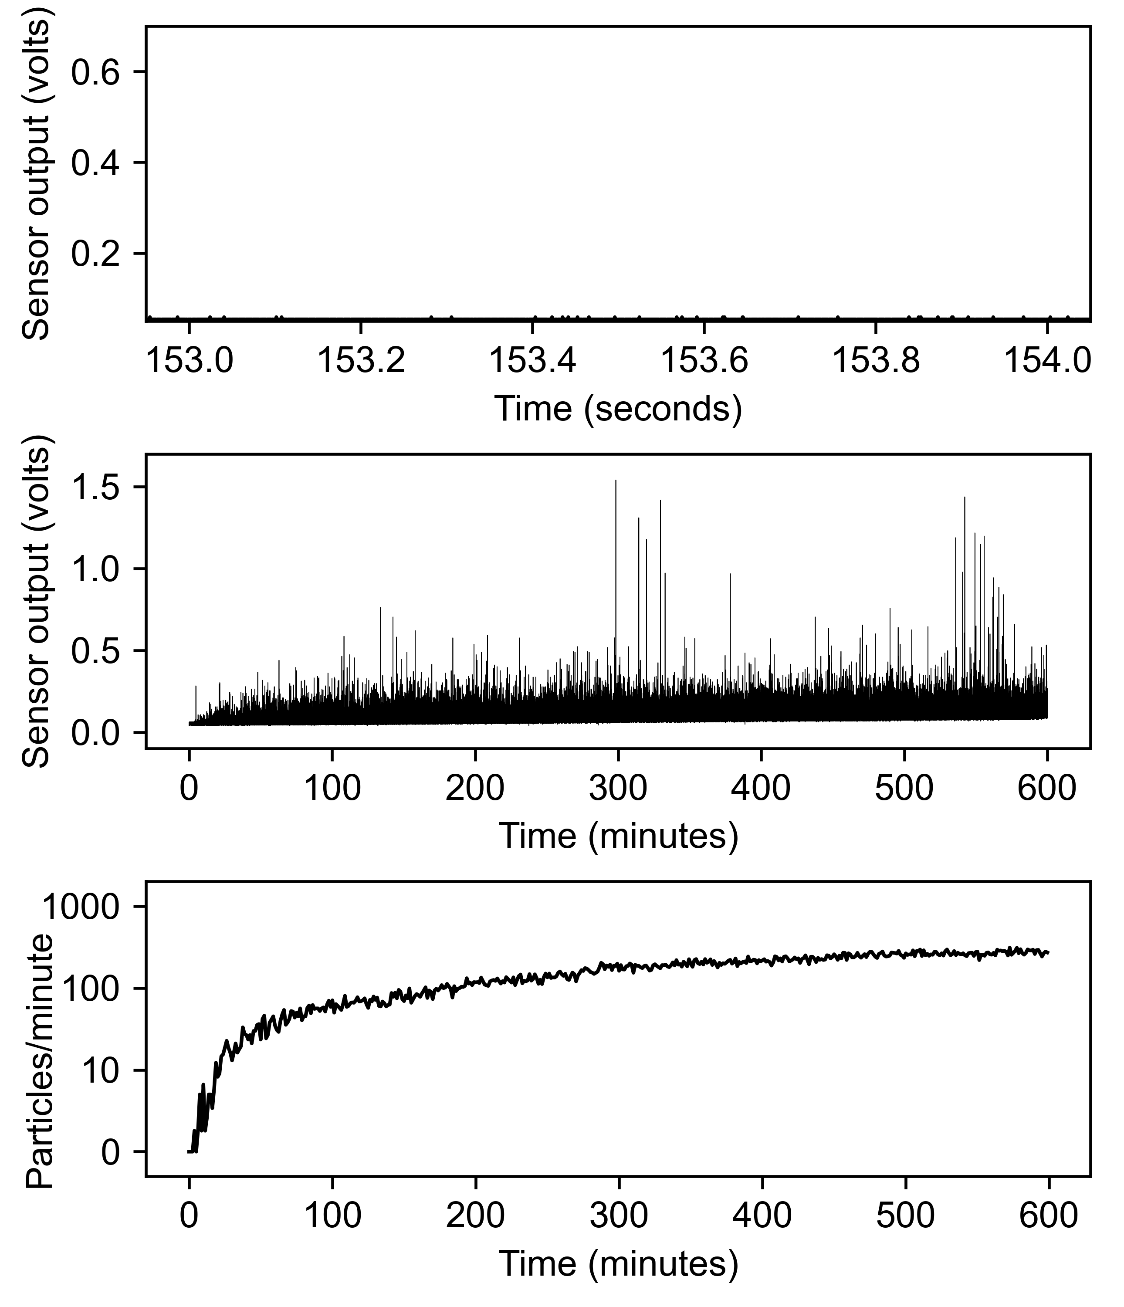
data/long/Iron complex/20241211T221002_iron_complex_long.json.gz.png
