groverlab/disintegration-fingerprinting/data/long/Iron complex/20241212T193348_iron_complex_long.json.gz.png

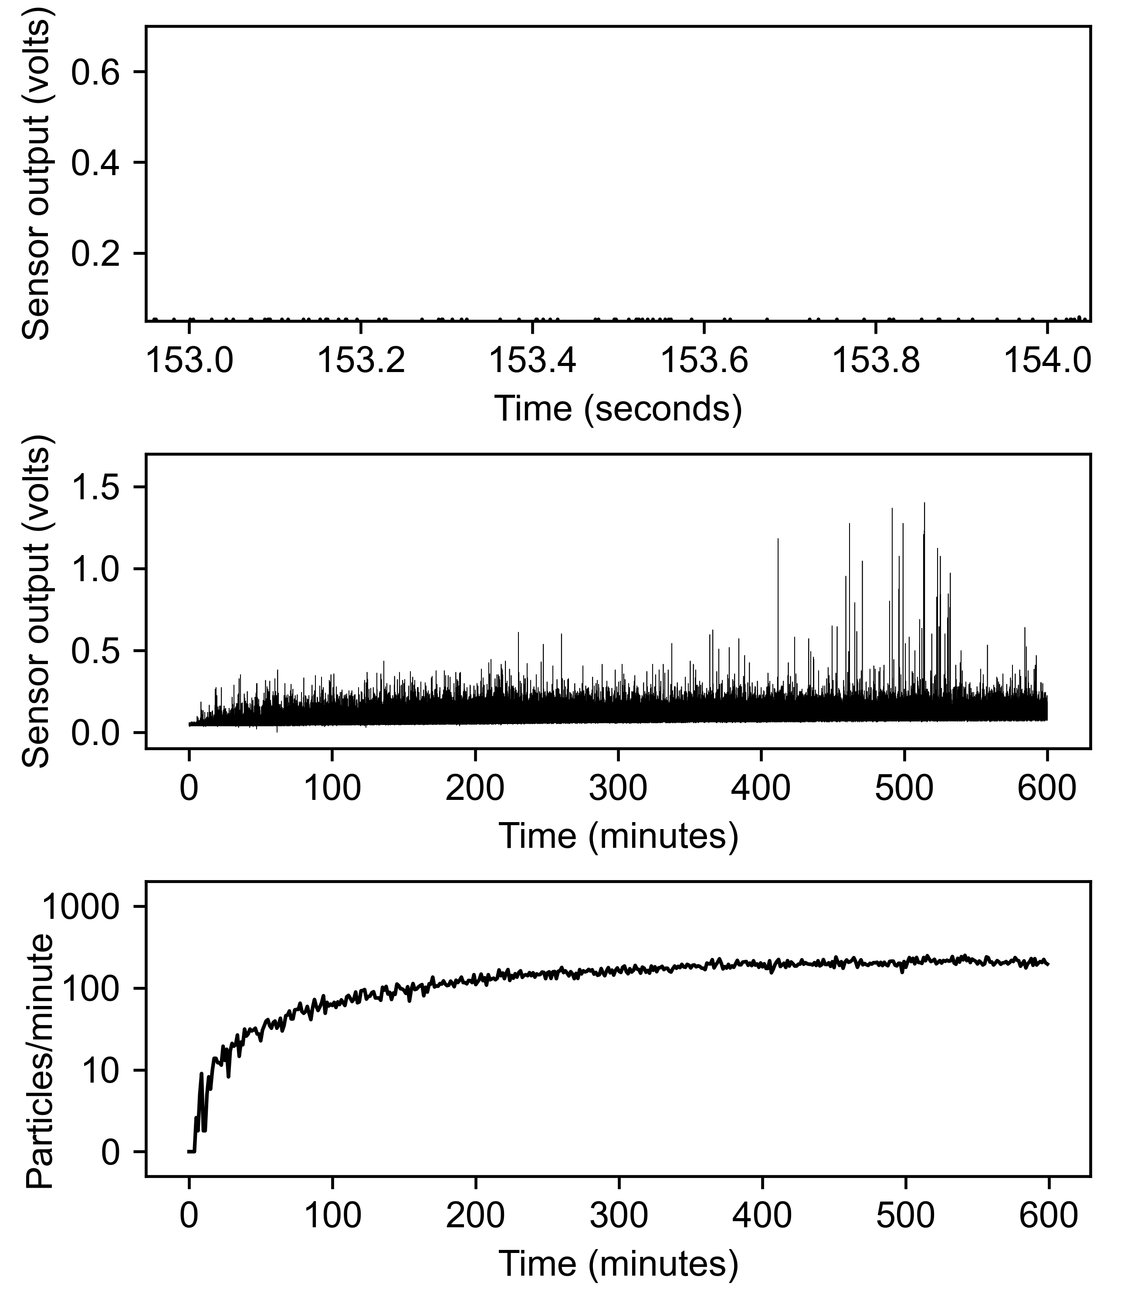
data/long/Iron complex/20241212T193348_iron_complex_long.json.gz.png
