groverlab/disintegration-fingerprinting/data/long/Pseudoephedrine ext. rel./20241123T221406_sudafed_sinus_long.json.gz.png

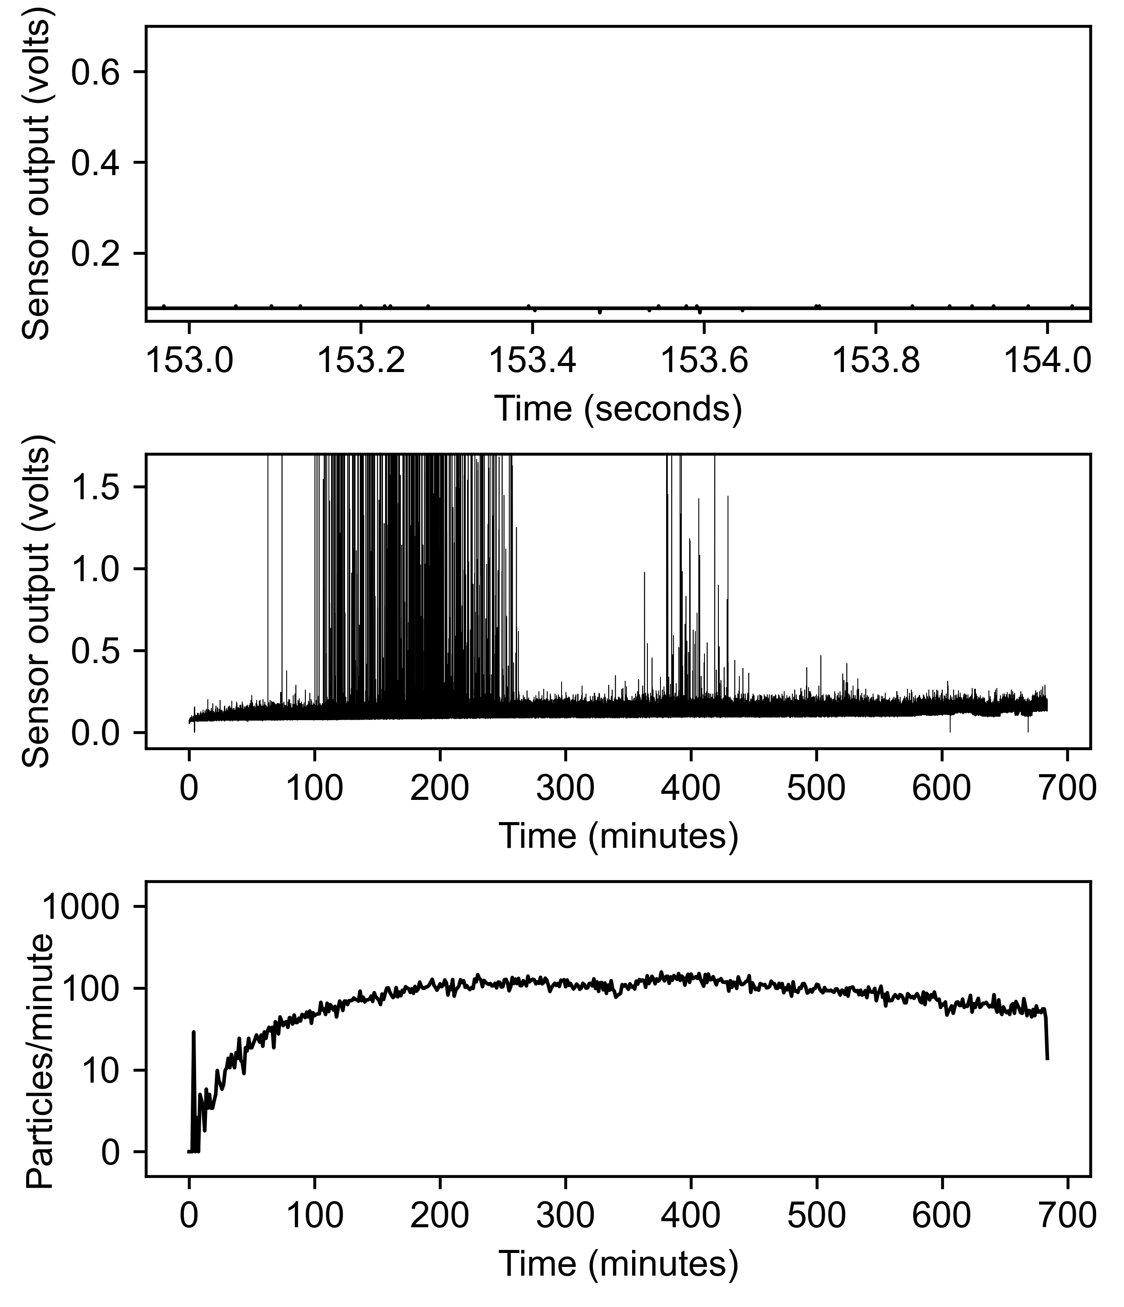
data/long/Pseudoephedrine ext. rel./20241123T221406_sudafed_sinus_long.json.gz.png
