groverlab/disintegration-fingerprinting/data/long/Pseudoephedrine ext. rel./20241124T101120_sudafed_sinus_long.json.gz.png

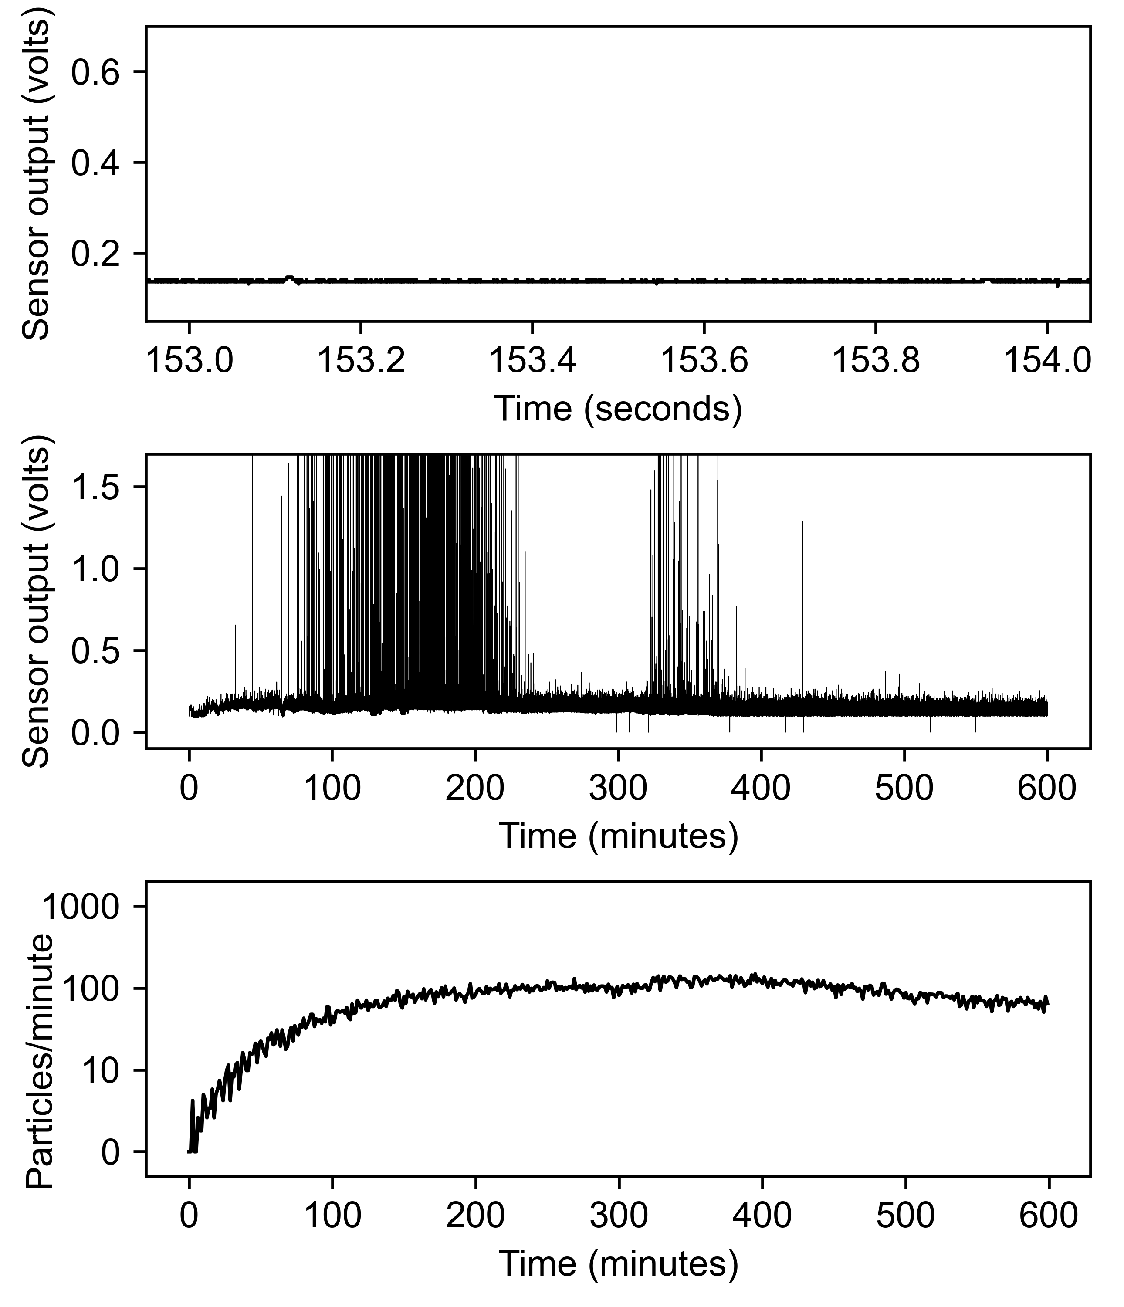
data/long/Pseudoephedrine ext. rel./20241124T101120_sudafed_sinus_long.json.gz.png
