groverlab/disintegration-fingerprinting/data/long/Pseudoephedrine ext. rel./20241124T202013_sudafed_sinus_long.json.gz.png

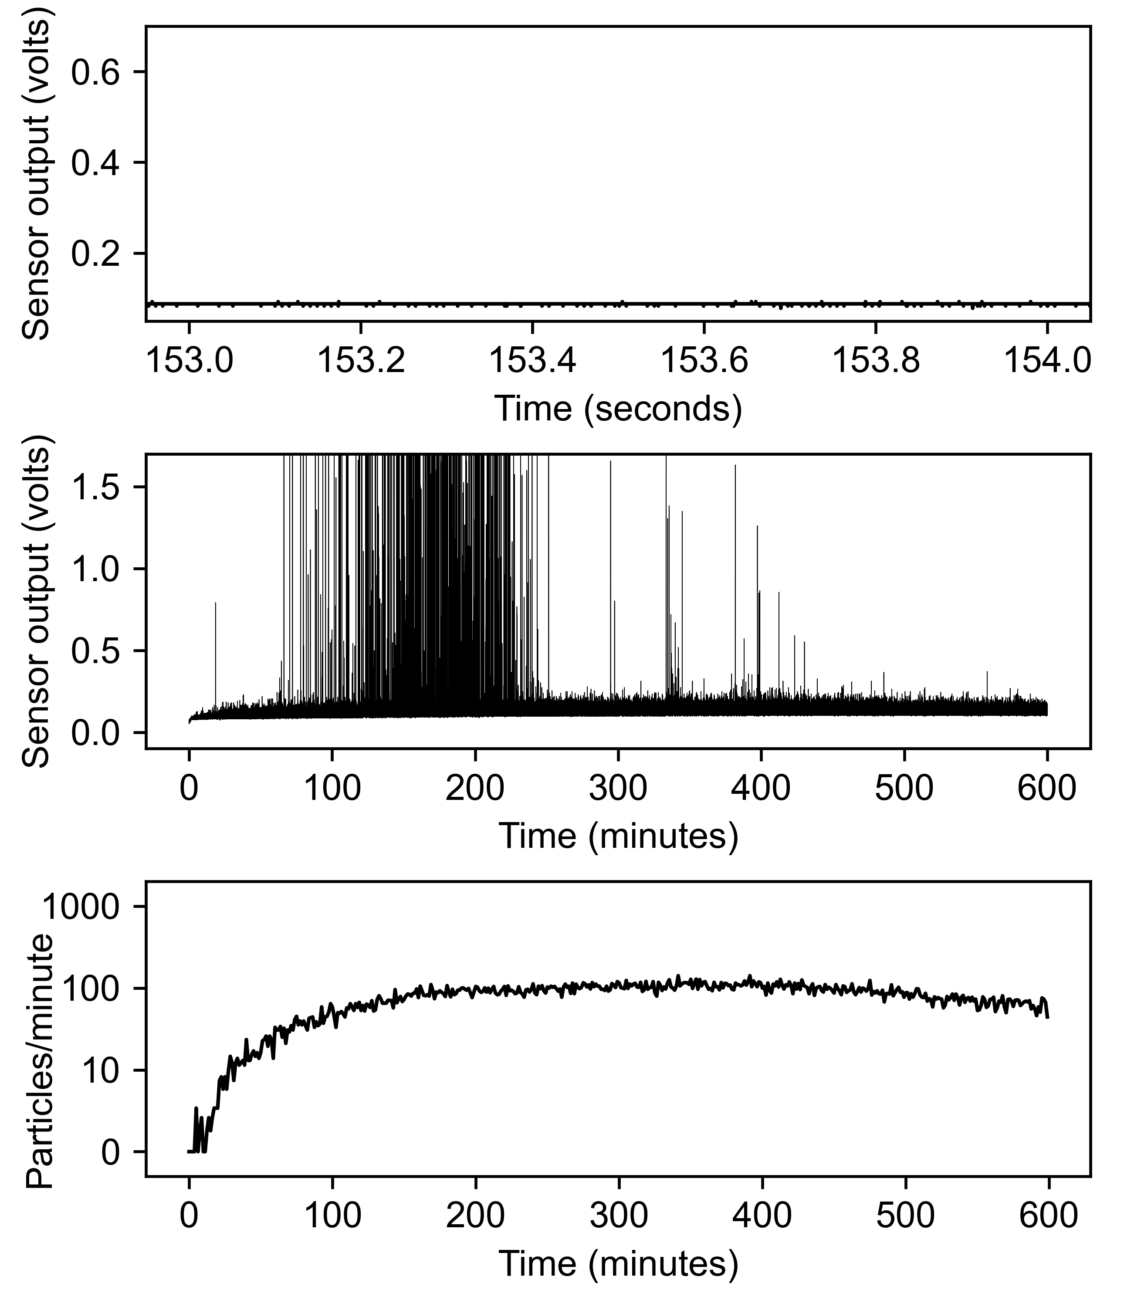
data/long/Pseudoephedrine ext. rel./20241124T202013_sudafed_sinus_long.json.gz.png
