groverlab/disintegration-fingerprinting/data/variety averages.png

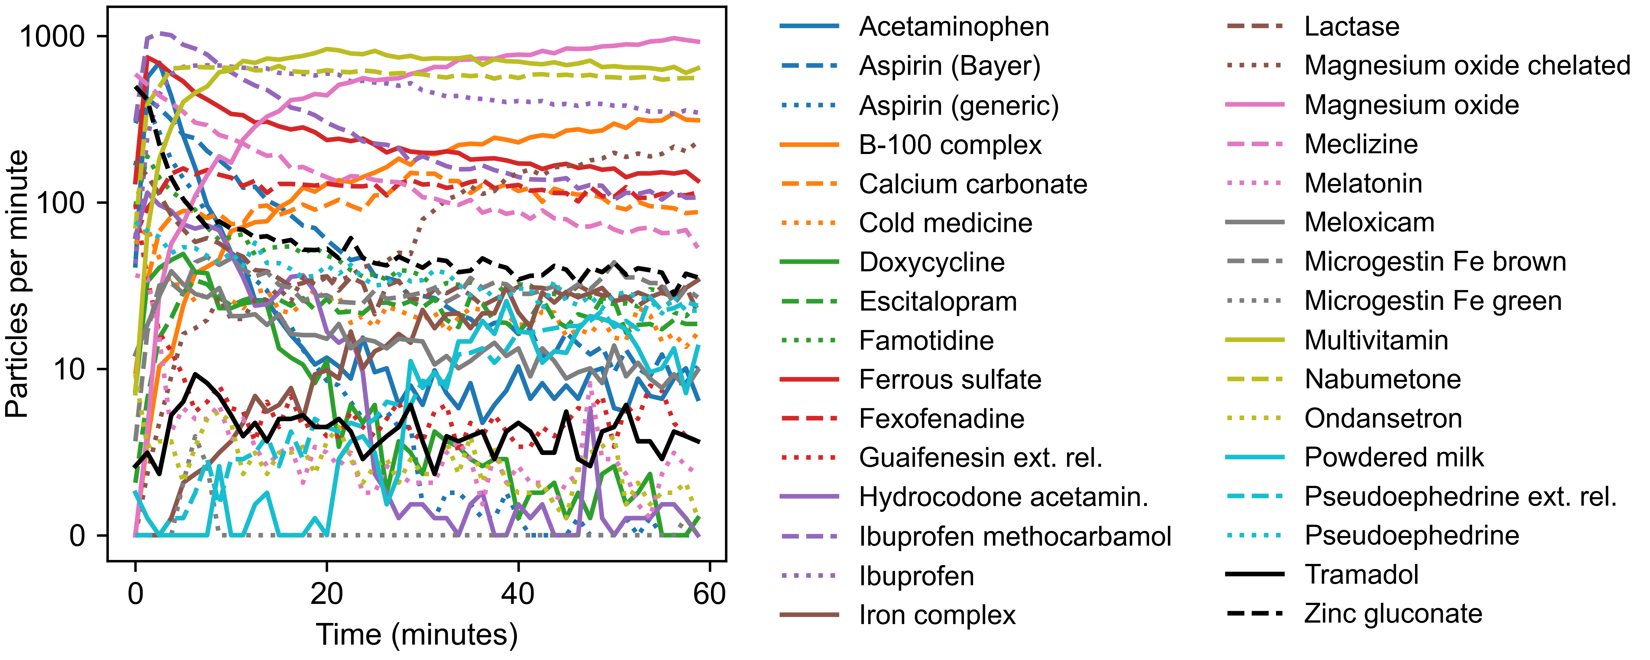
data/variety averages.png
