groverlab/disintegration-fingerprinting/data/variety.png

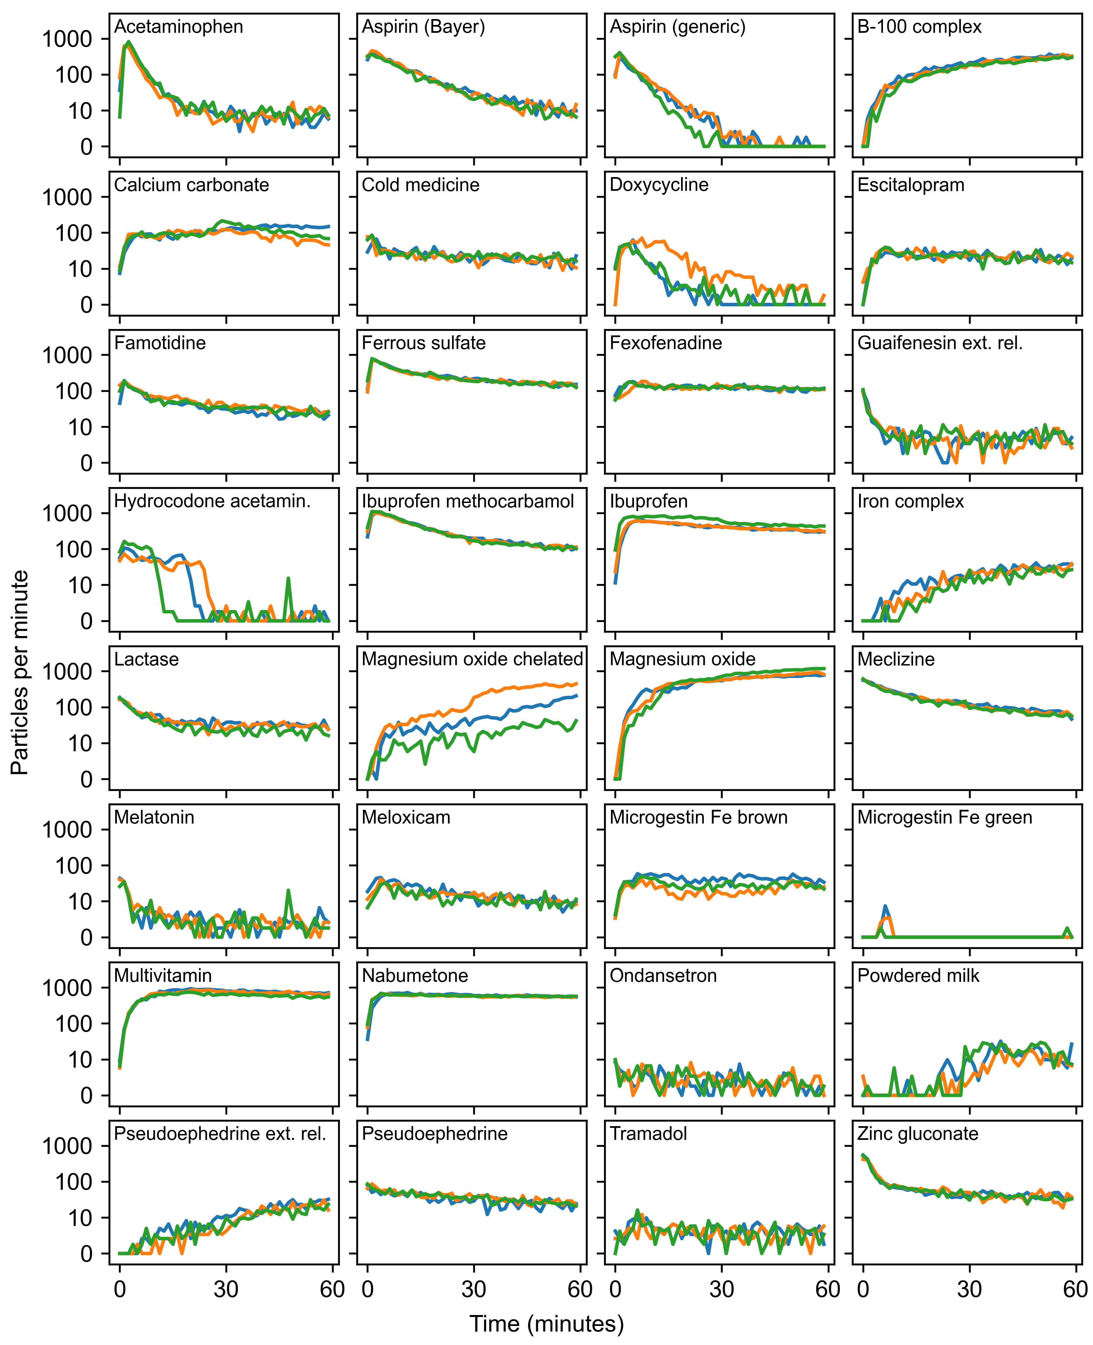
data/variety.png
