groverlab/disintegration-fingerprinting/data/variety/Acetaminophen/20241210T135025_tylenol_extra_strength.json.gz.png

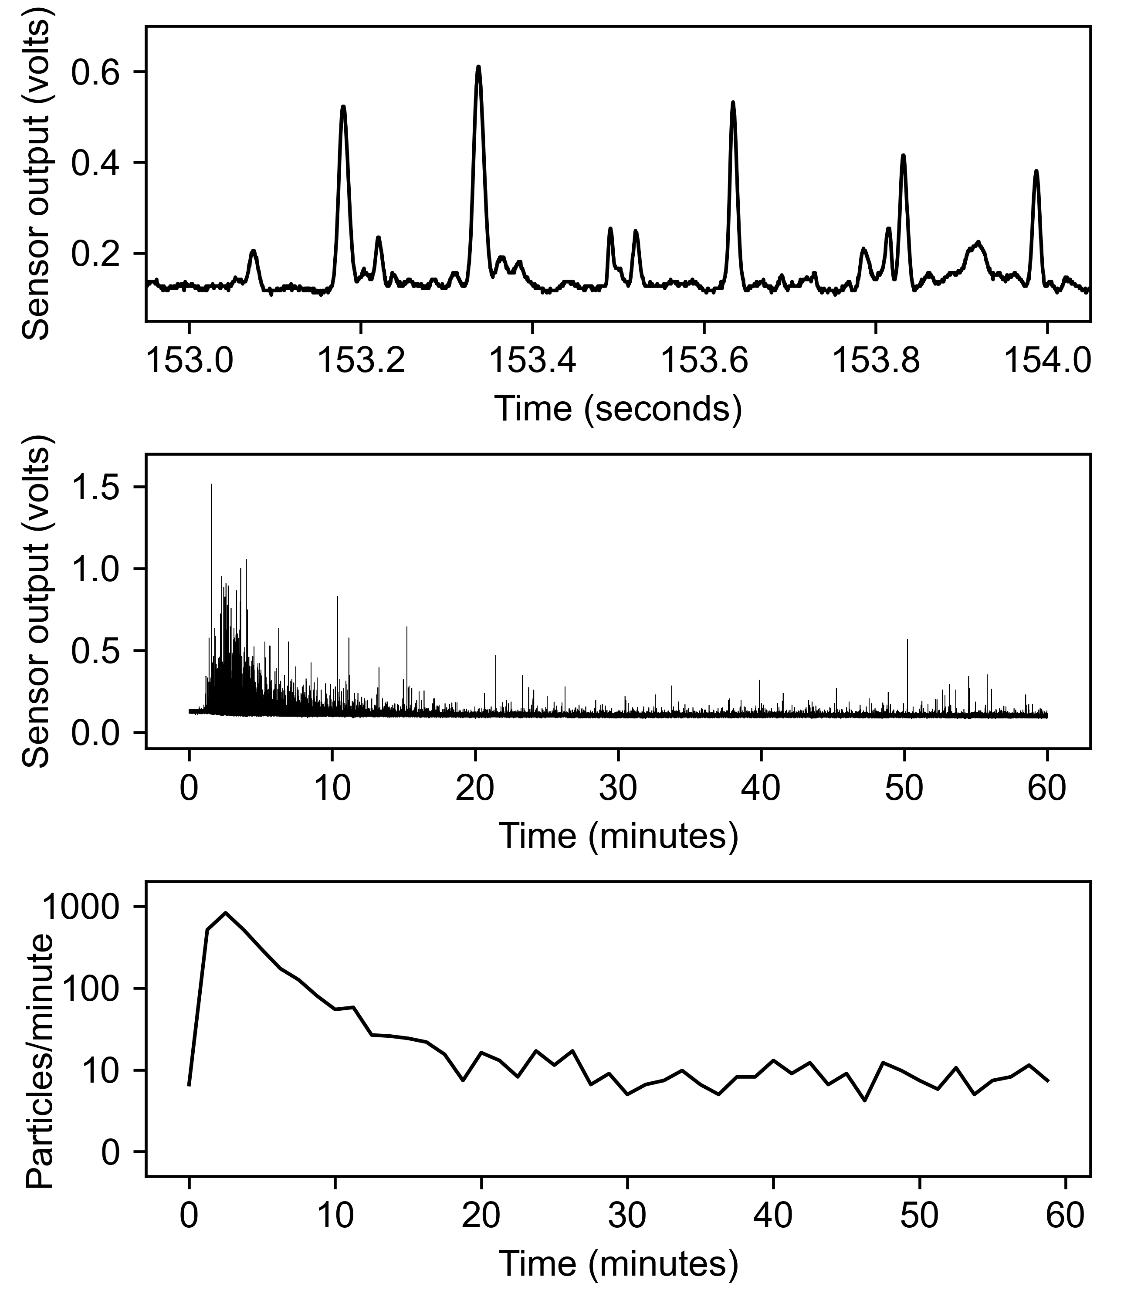
data/variety/Acetaminophen/20241210T135025_tylenol_extra_strength.json.gz.png
