groverlab/disintegration-fingerprinting/data/variety/B-100 complex/20241126T081726_b-100_complex.json.gz.png

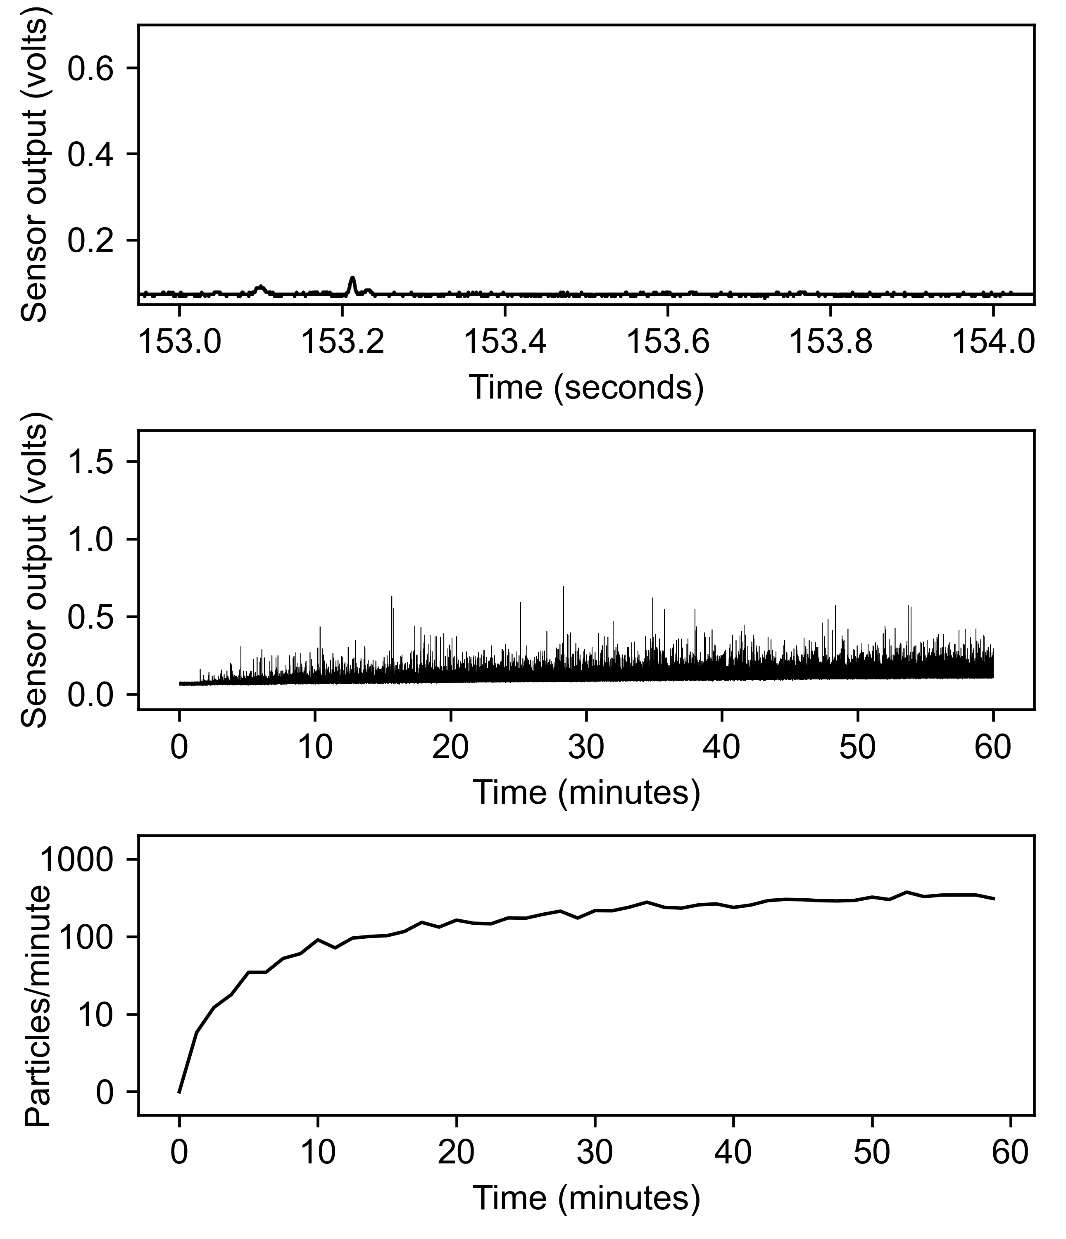
data/variety/B-100 complex/20241126T081726_b-100_complex.json.gz.png
