groverlab/disintegration-fingerprinting/data/variety/Calcium carbonate/20241121T060930_antacid_generic.json.gz.png

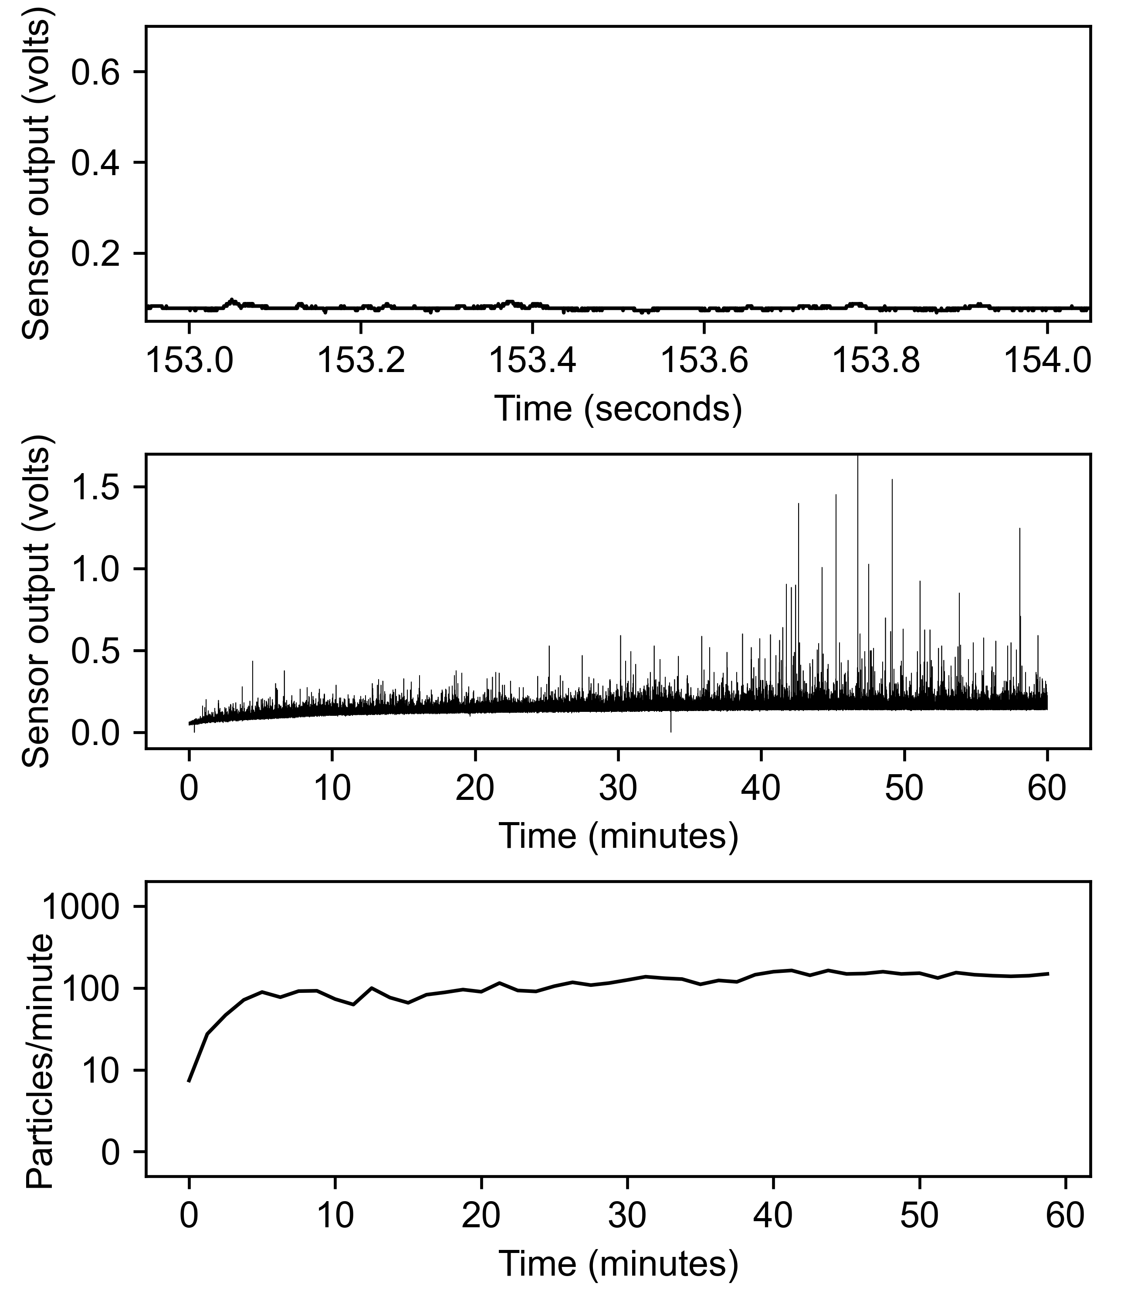
data/variety/Calcium carbonate/20241121T060930_antacid_generic.json.gz.png
