groverlab/disintegration-fingerprinting/data/variety/Calcium carbonate/20241121T085719_antacid_generic.json.gz.png

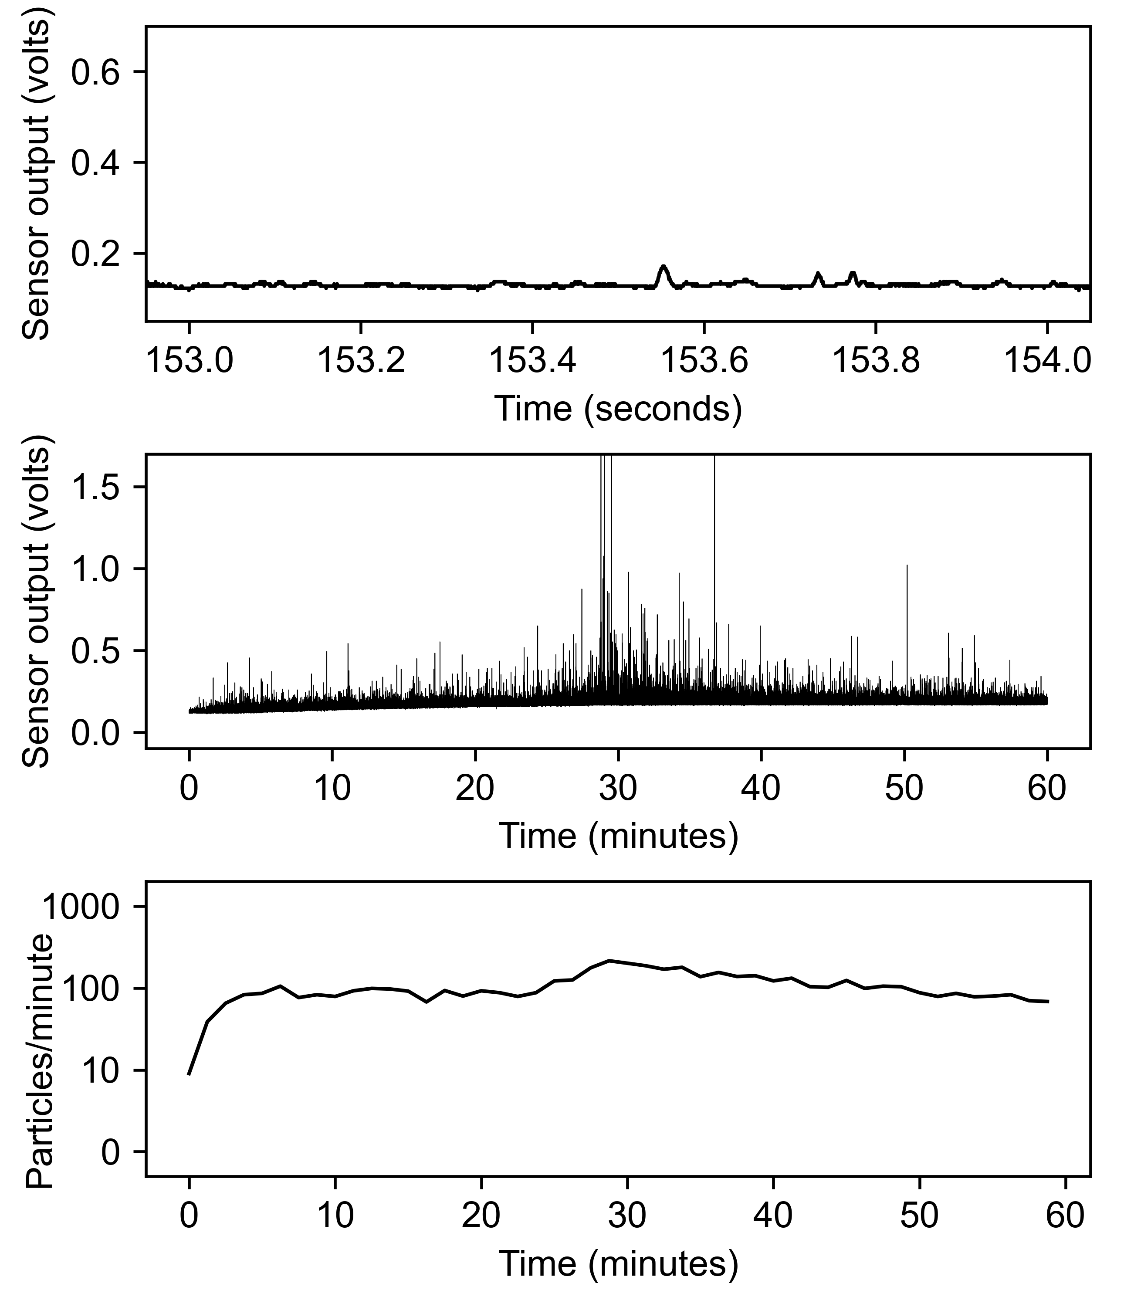
data/variety/Calcium carbonate/20241121T085719_antacid_generic.json.gz.png
