groverlab/disintegration-fingerprinting/data/variety/Doxycycline/20241128T125419_doxycycline.json.gz.png

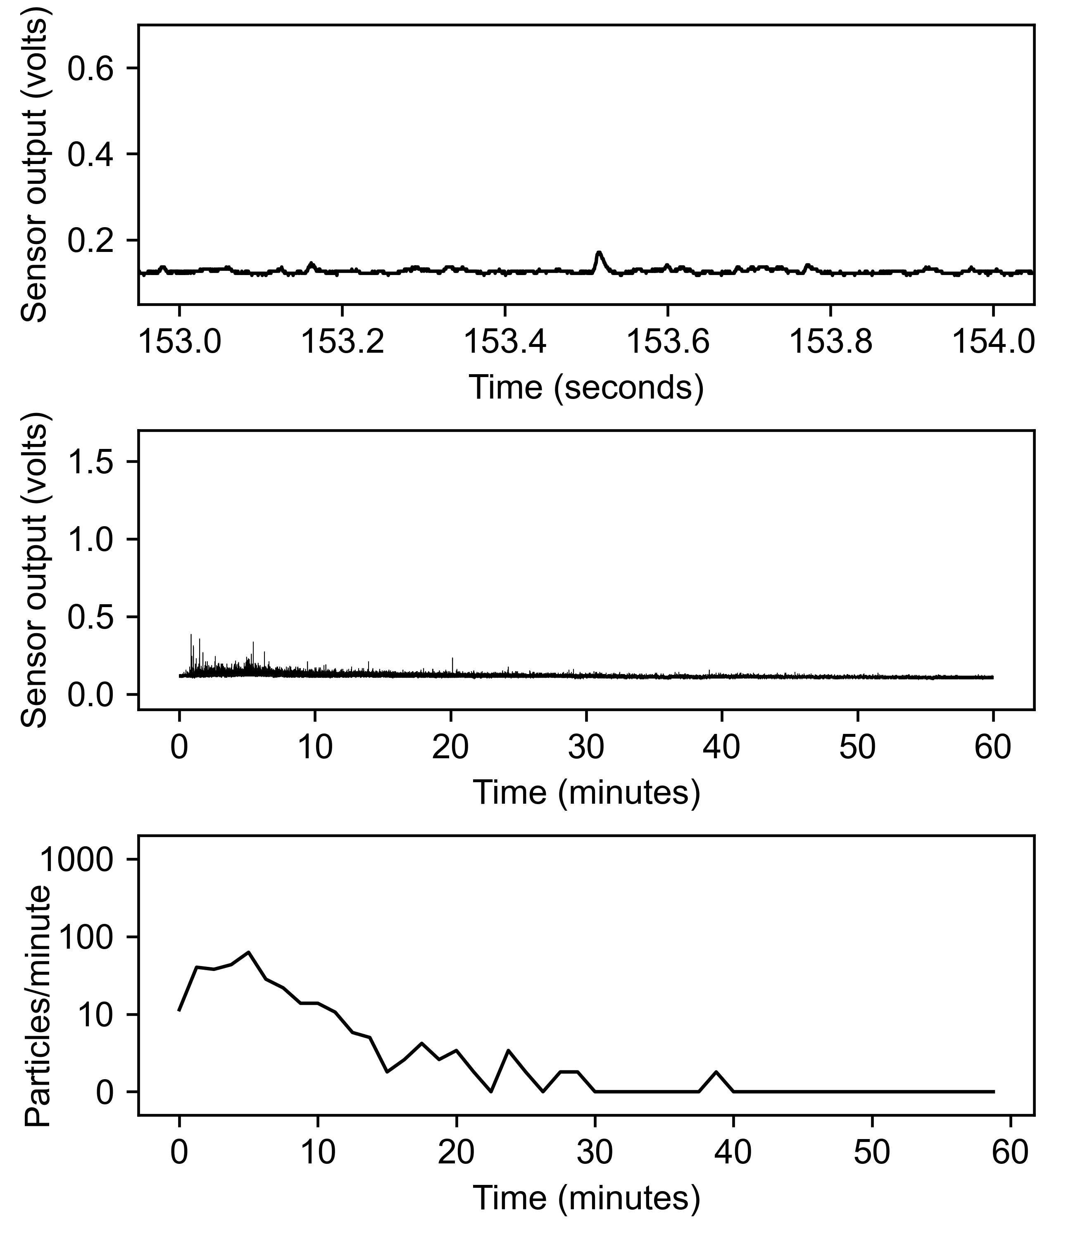
data/variety/Doxycycline/20241128T125419_doxycycline.json.gz.png
