groverlab/disintegration-fingerprinting/data/variety/Doxycycline/20250421T161441_doxycycline.json.gz.png

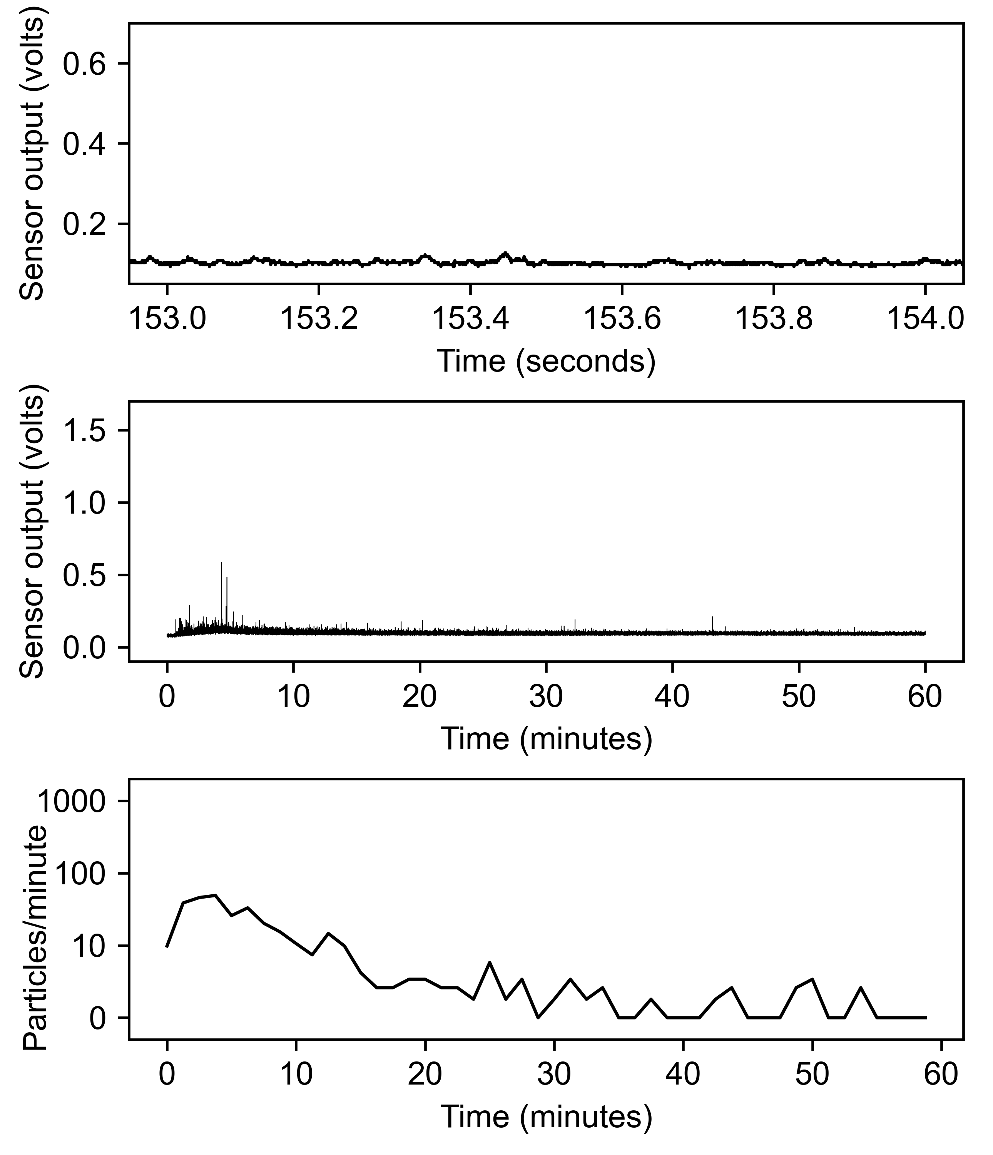
data/variety/Doxycycline/20250421T161441_doxycycline.json.gz.png
