groverlab/disintegration-fingerprinting/data/variety/Escitalopram/20241122T055616_escitalopram.json.gz.png

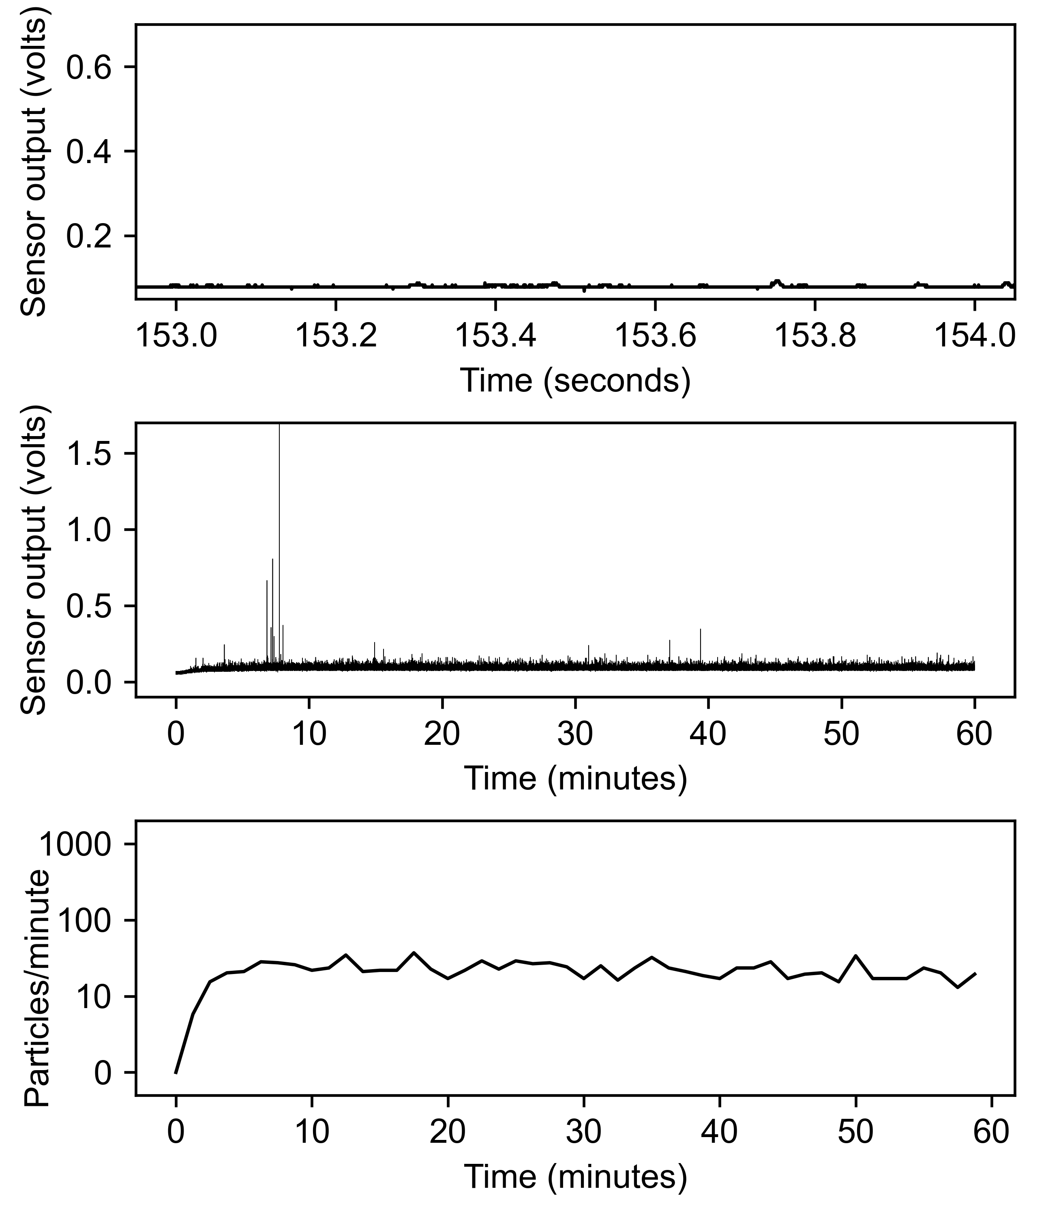
data/variety/Escitalopram/20241122T055616_escitalopram.json.gz.png
