groverlab/disintegration-fingerprinting/data/variety/Escitalopram/20241122T070300_escitalopram.json.gz.png

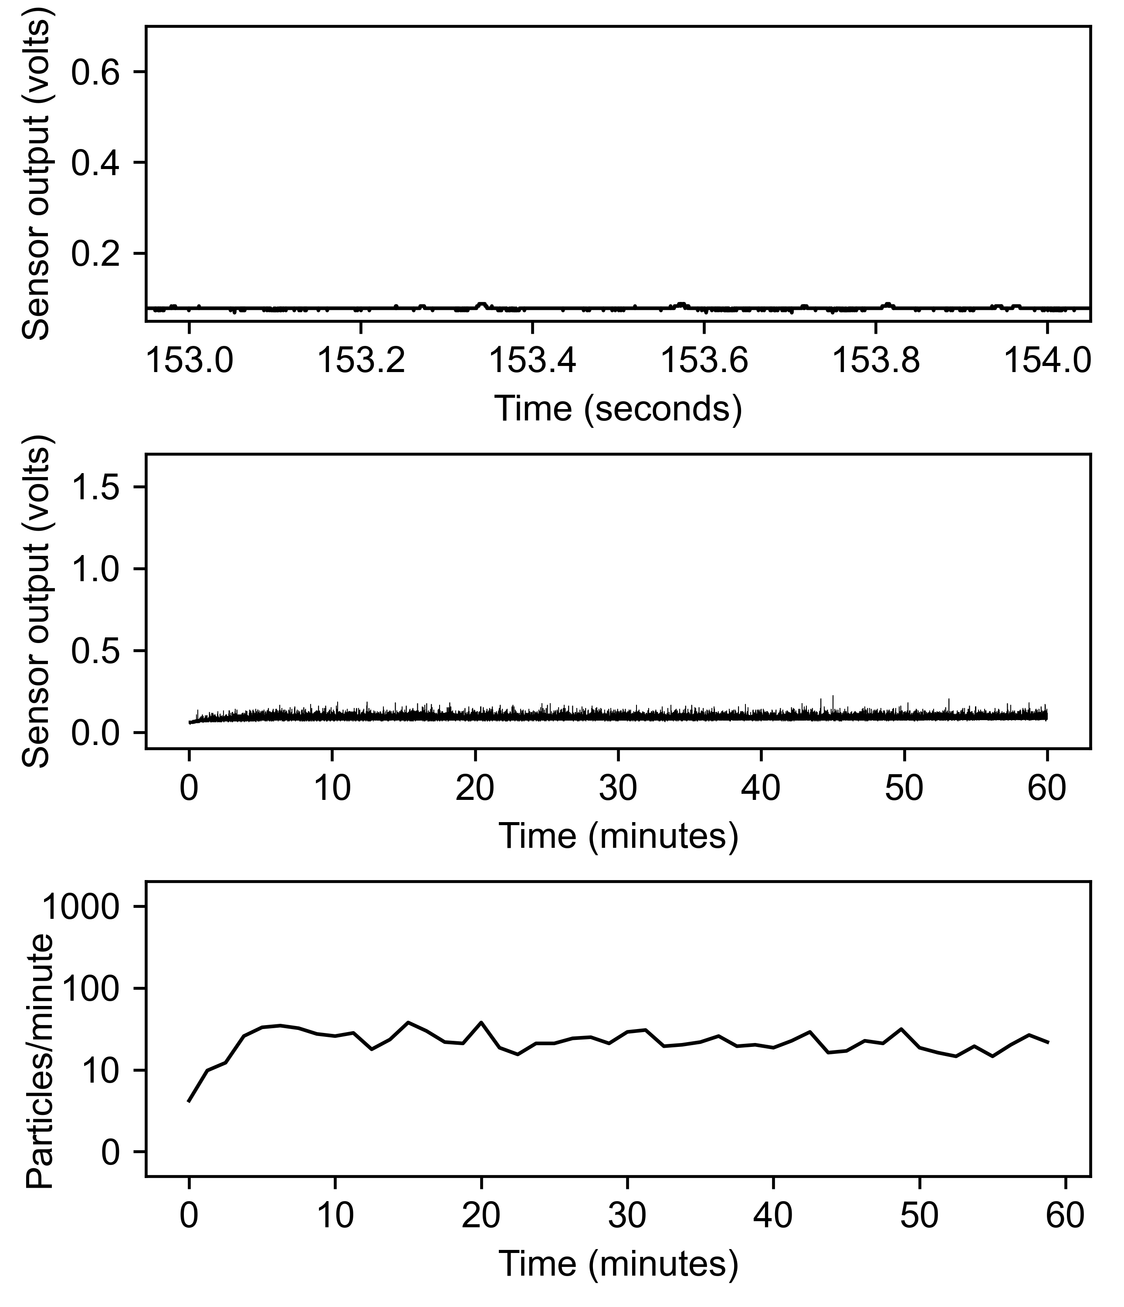
data/variety/Escitalopram/20241122T070300_escitalopram.json.gz.png
