groverlab/disintegration-fingerprinting/data/variety/Escitalopram/20241122T080857_escitalopram.json.gz.png

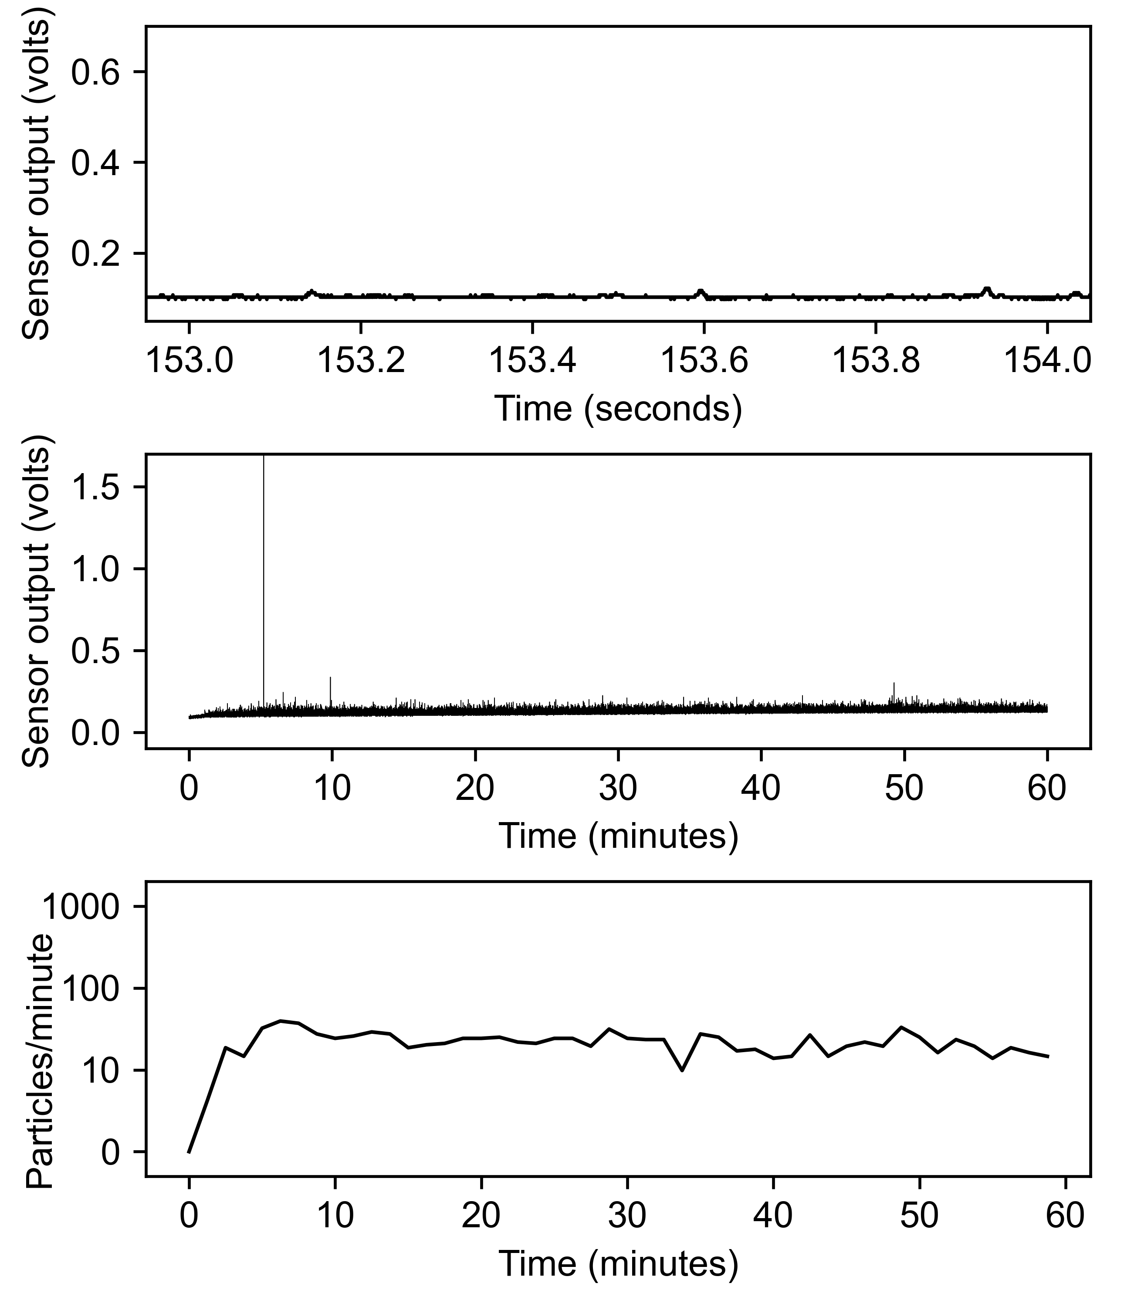
data/variety/Escitalopram/20241122T080857_escitalopram.json.gz.png
