groverlab/disintegration-fingerprinting/data/variety/Ferrous sulfate/20241127T194917_iron_65_mg.json.gz.png

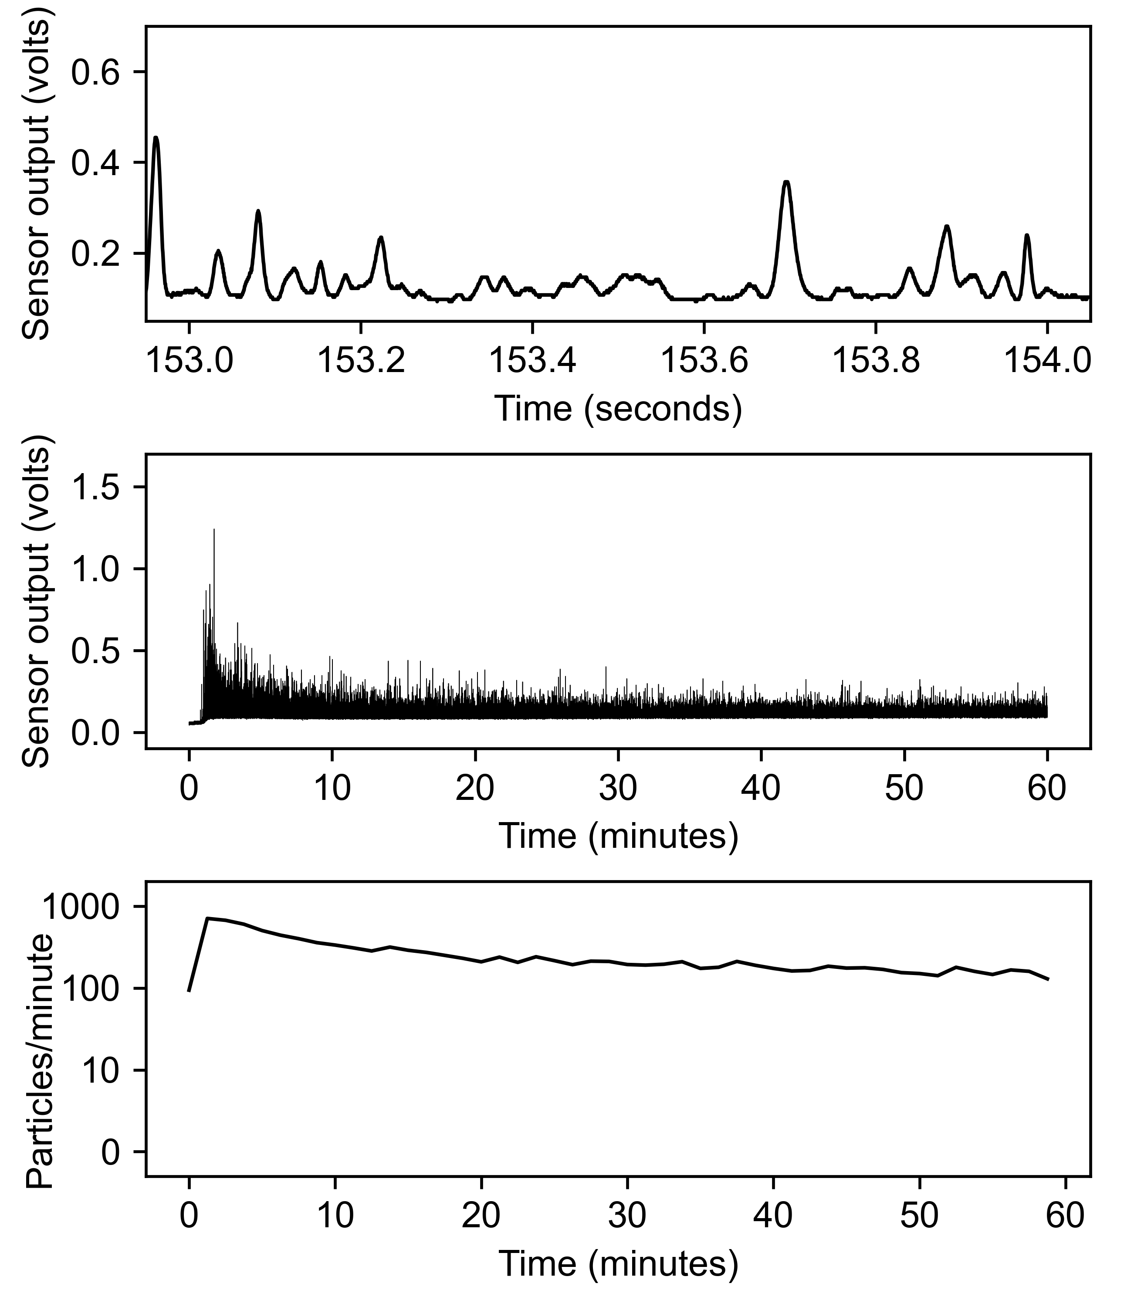
data/variety/Ferrous sulfate/20241127T194917_iron_65_mg.json.gz.png
