groverlab/disintegration-fingerprinting/data/variety/Fexofenadine/20241122T091604_fexofenadine.json.gz.png

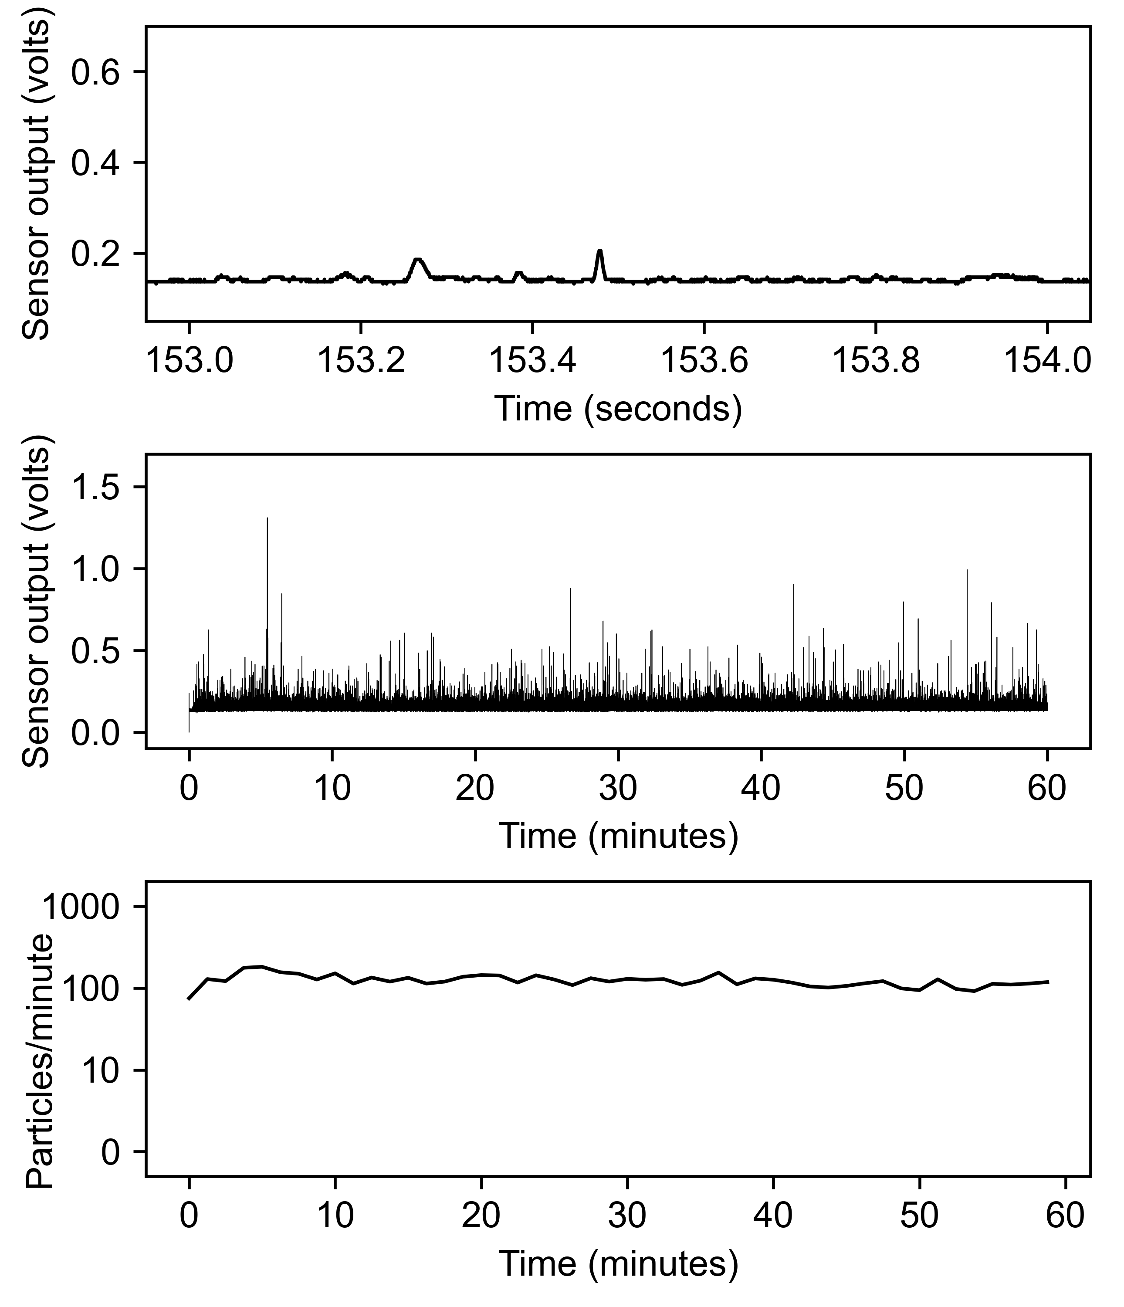
data/variety/Fexofenadine/20241122T091604_fexofenadine.json.gz.png
