groverlab/disintegration-fingerprinting/data/variety/Fexofenadine/20241122T102749_fexofenadine.json.gz.png

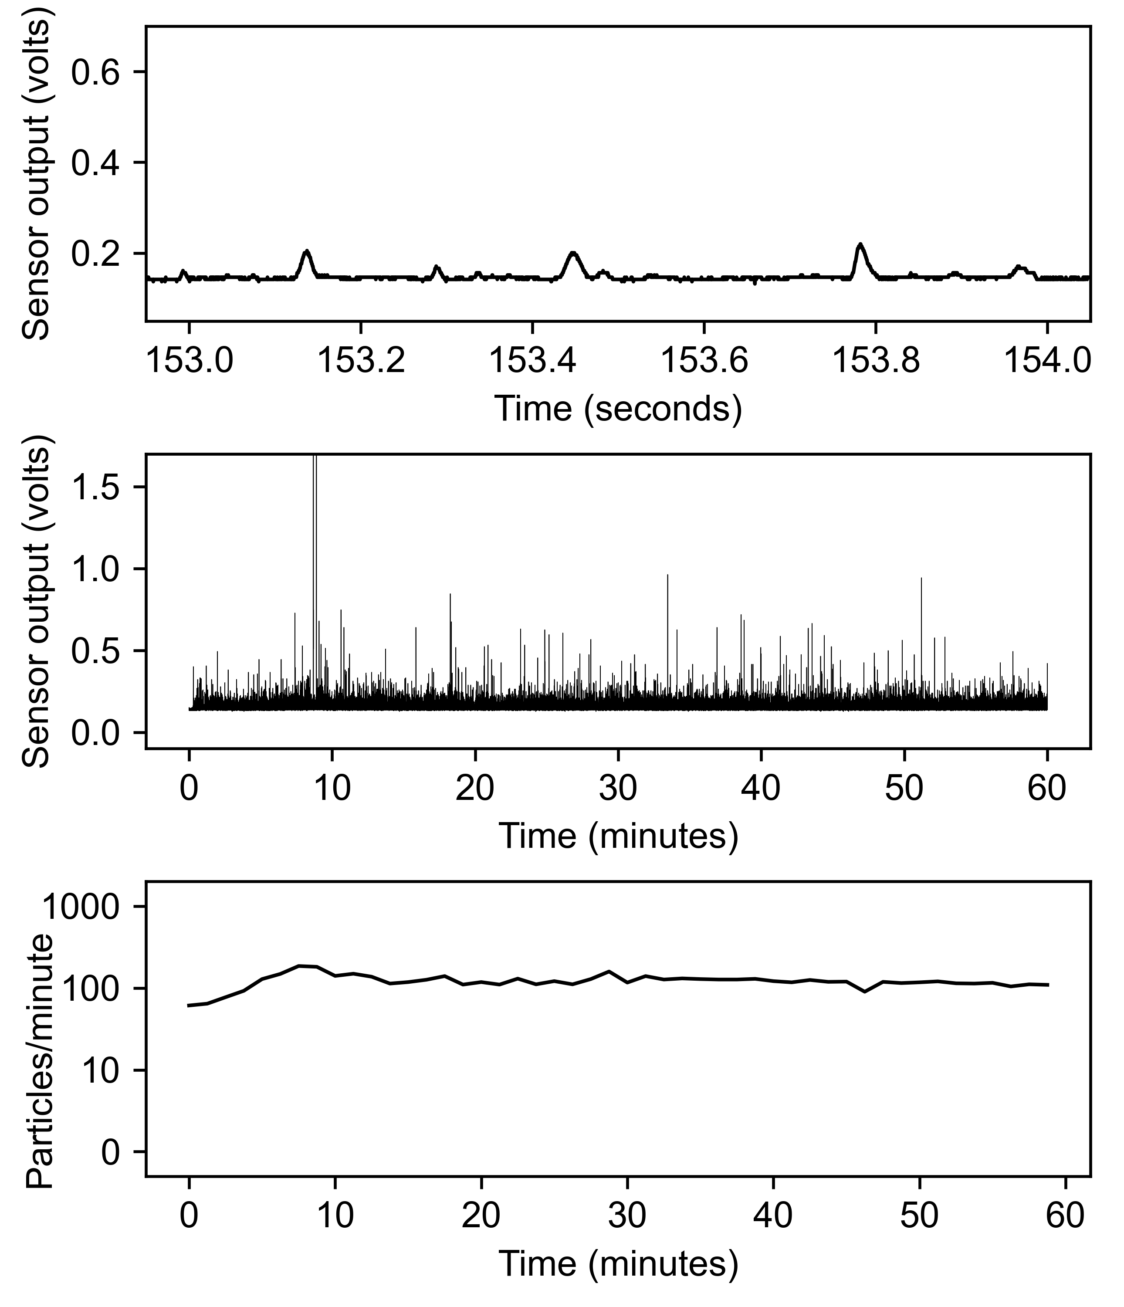
data/variety/Fexofenadine/20241122T102749_fexofenadine.json.gz.png
