groverlab/disintegration-fingerprinting/data/variety/Guaifenesin ext. rel./20241117T105249_guaifenesin_generic.json.gz.png

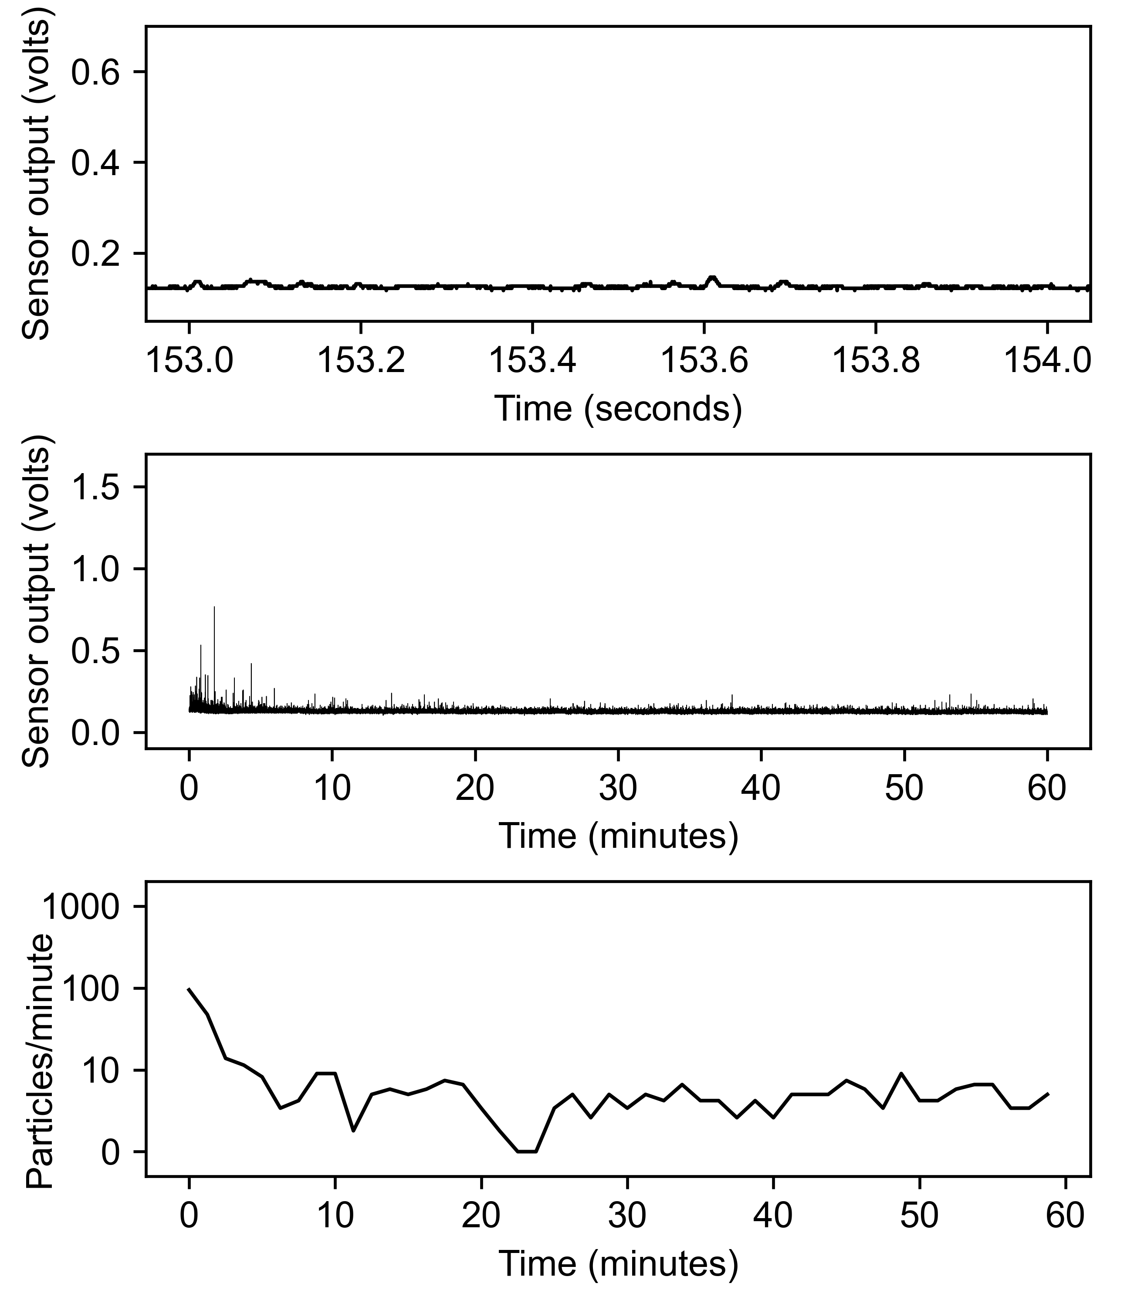
data/variety/Guaifenesin ext. rel./20241117T105249_guaifenesin_generic.json.gz.png
