groverlab/disintegration-fingerprinting/data/variety/Guaifenesin ext. rel./20241117T130908_guaifenesin_generic.json.gz.png

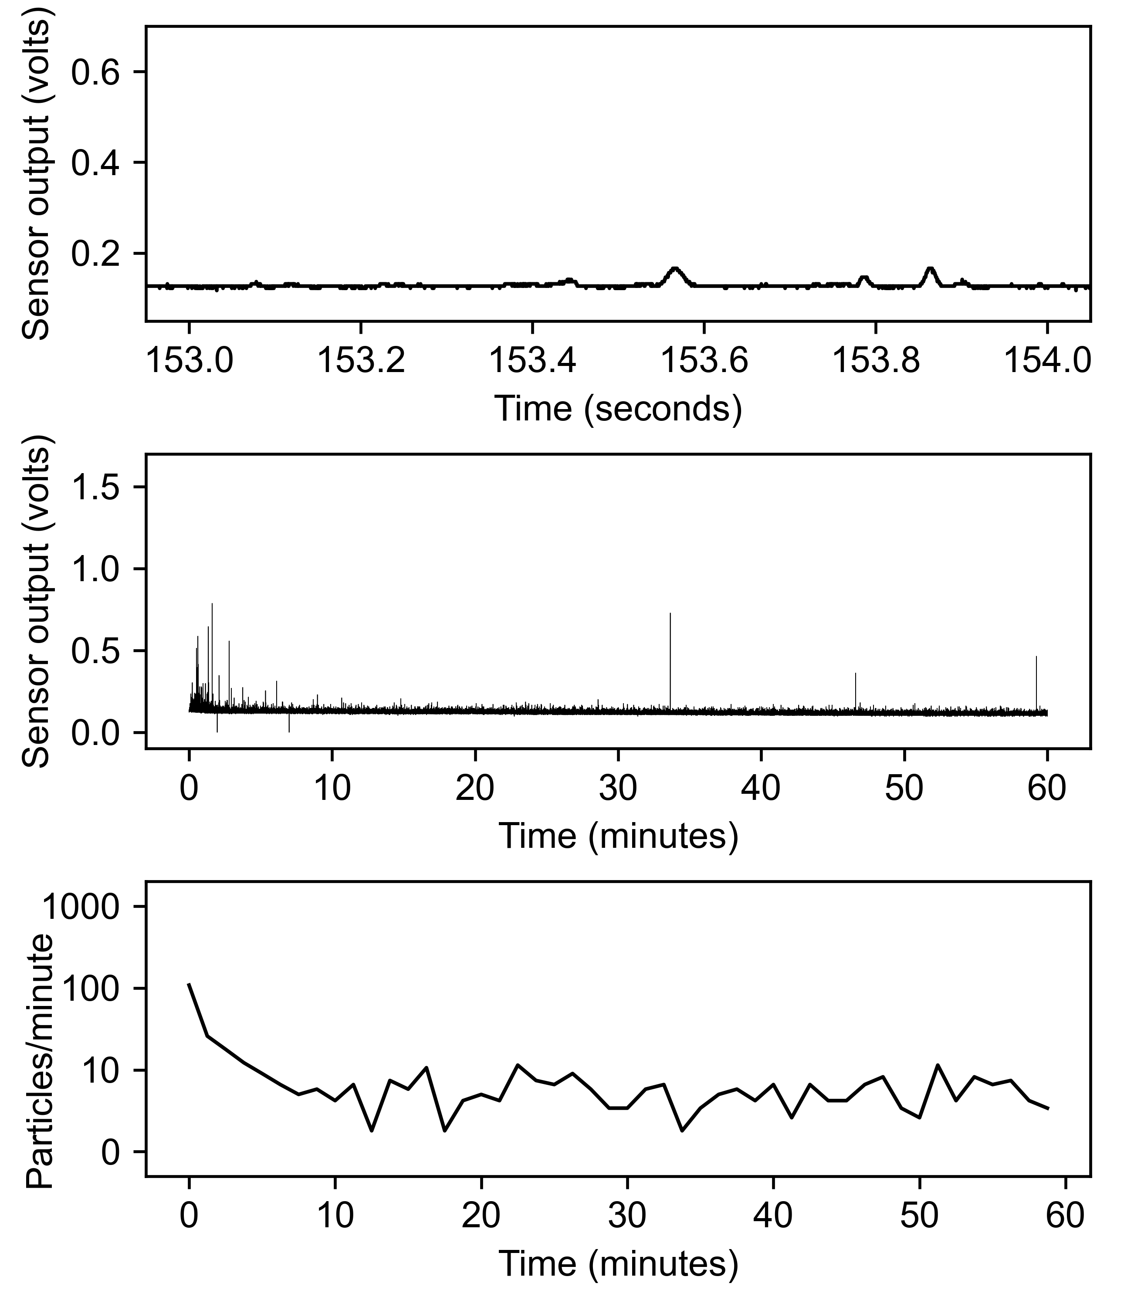
data/variety/Guaifenesin ext. rel./20241117T130908_guaifenesin_generic.json.gz.png
