groverlab/disintegration-fingerprinting/data/variety/Hydrocodone acetamin./20241119T162222_hydrocodone_acetaminophen.json.gz.png

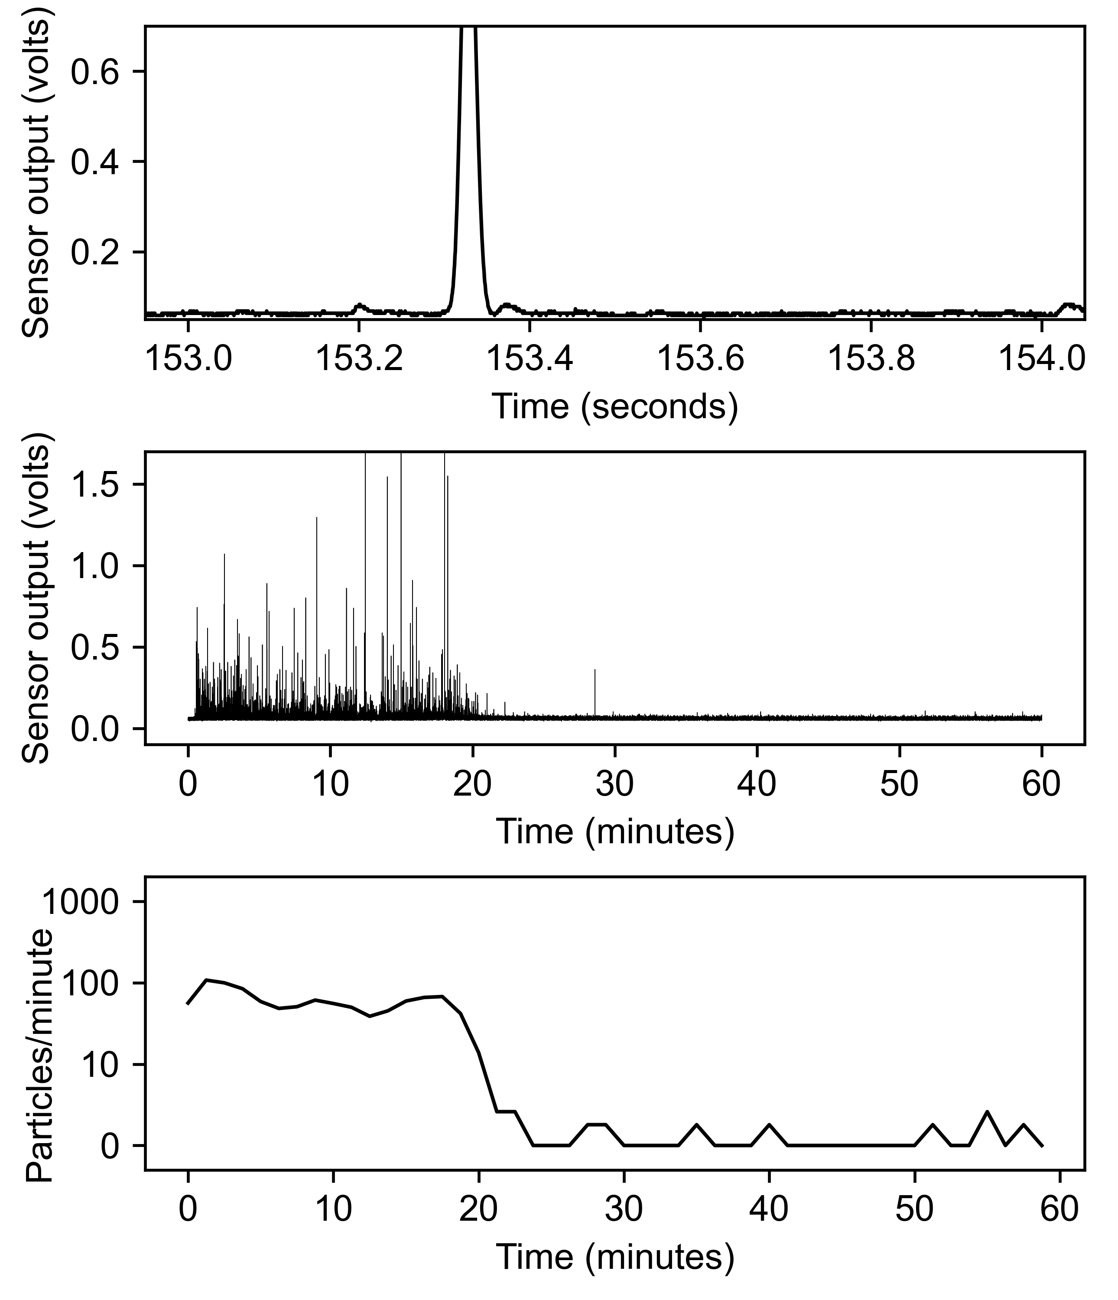
data/variety/Hydrocodone acetamin./20241119T162222_hydrocodone_acetaminophen.json.gz.png
