groverlab/disintegration-fingerprinting/data/variety/Hydrocodone acetamin./20241119T192545_hydrocodone_acetaminophen.json.gz.png

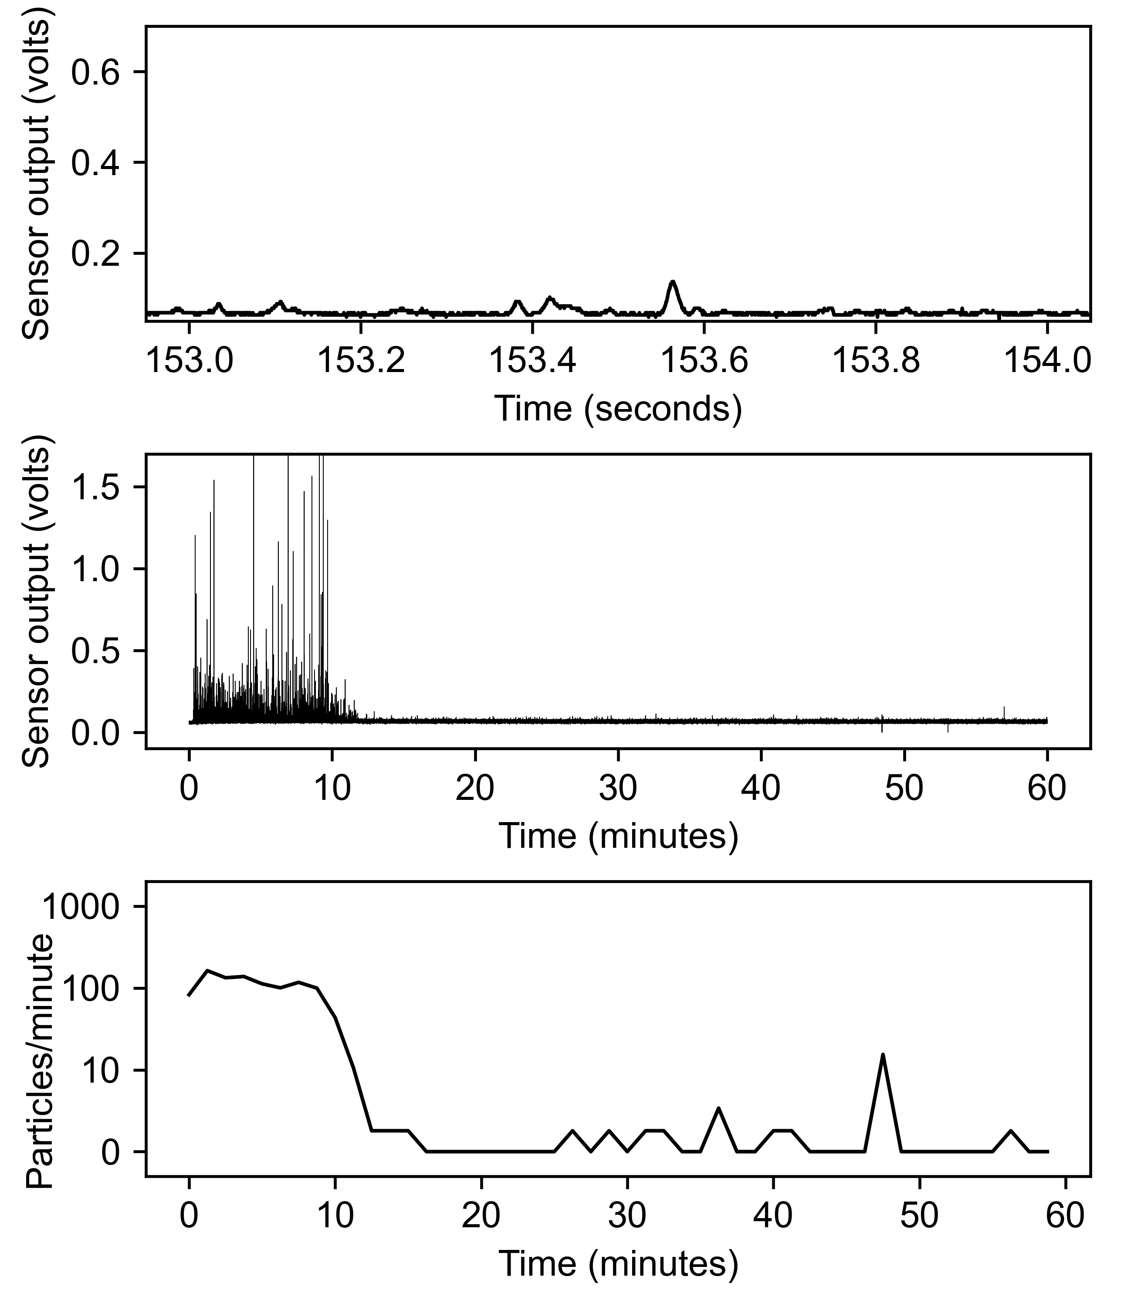
data/variety/Hydrocodone acetamin./20241119T192545_hydrocodone_acetaminophen.json.gz.png
