groverlab/disintegration-fingerprinting/data/variety/Ibuprofen methocarbamol/20241121T194719_ibuprofen_methocarbamol.json.gz.png

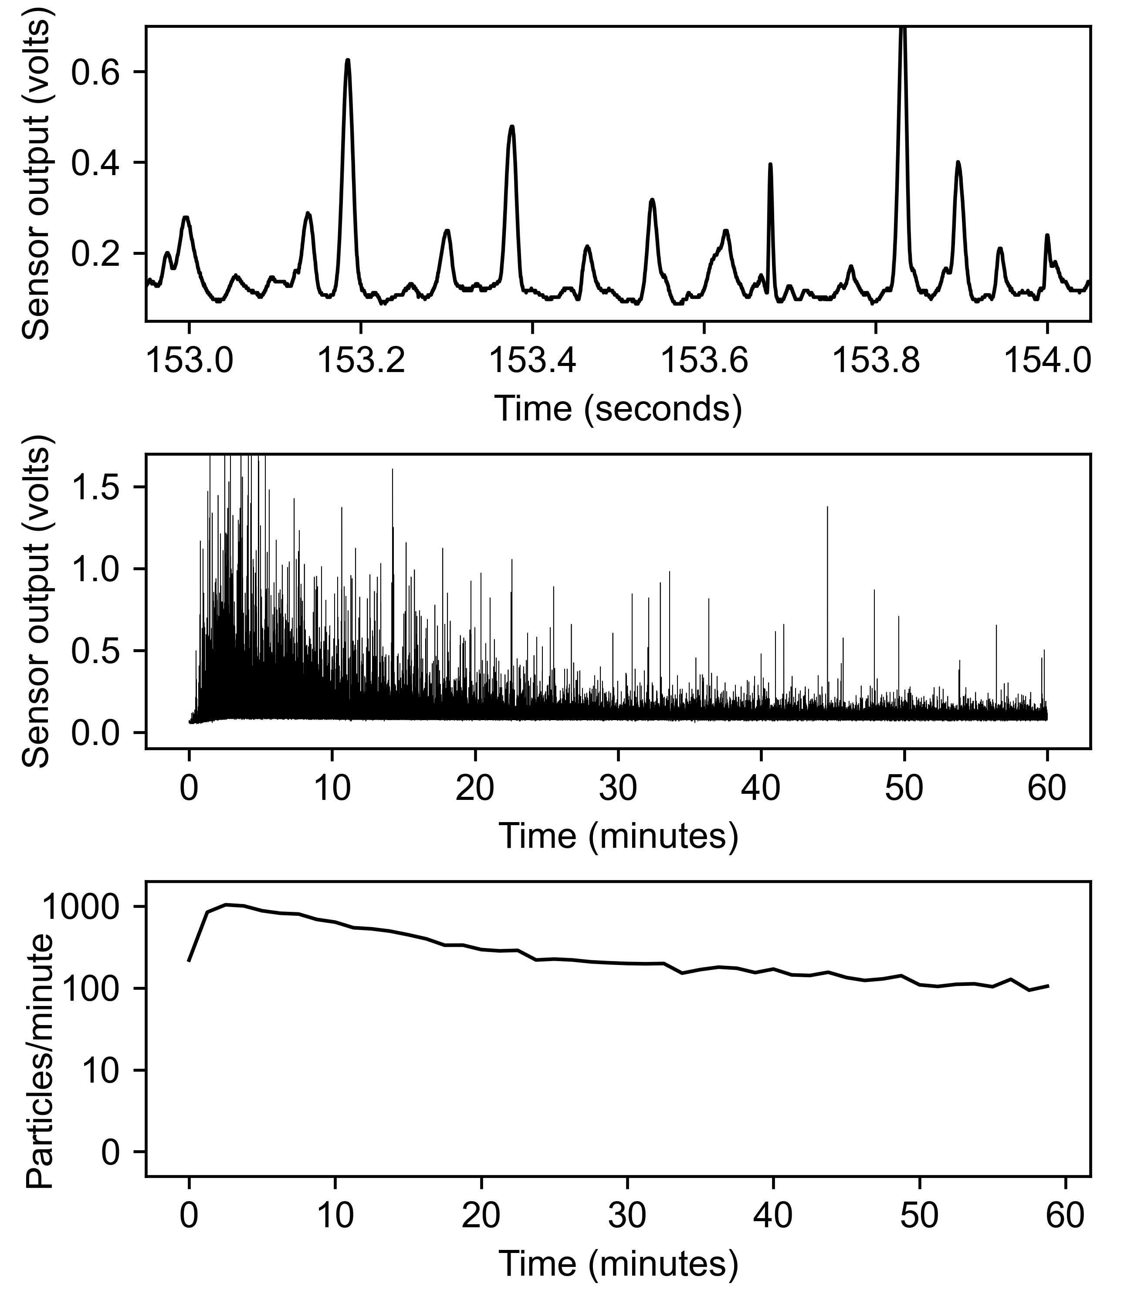
data/variety/Ibuprofen methocarbamol/20241121T194719_ibuprofen_methocarbamol.json.gz.png
