groverlab/disintegration-fingerprinting/data/variety/Ibuprofen methocarbamol/20241121T220440_ibuprofen_methocarbamol.json.gz.png

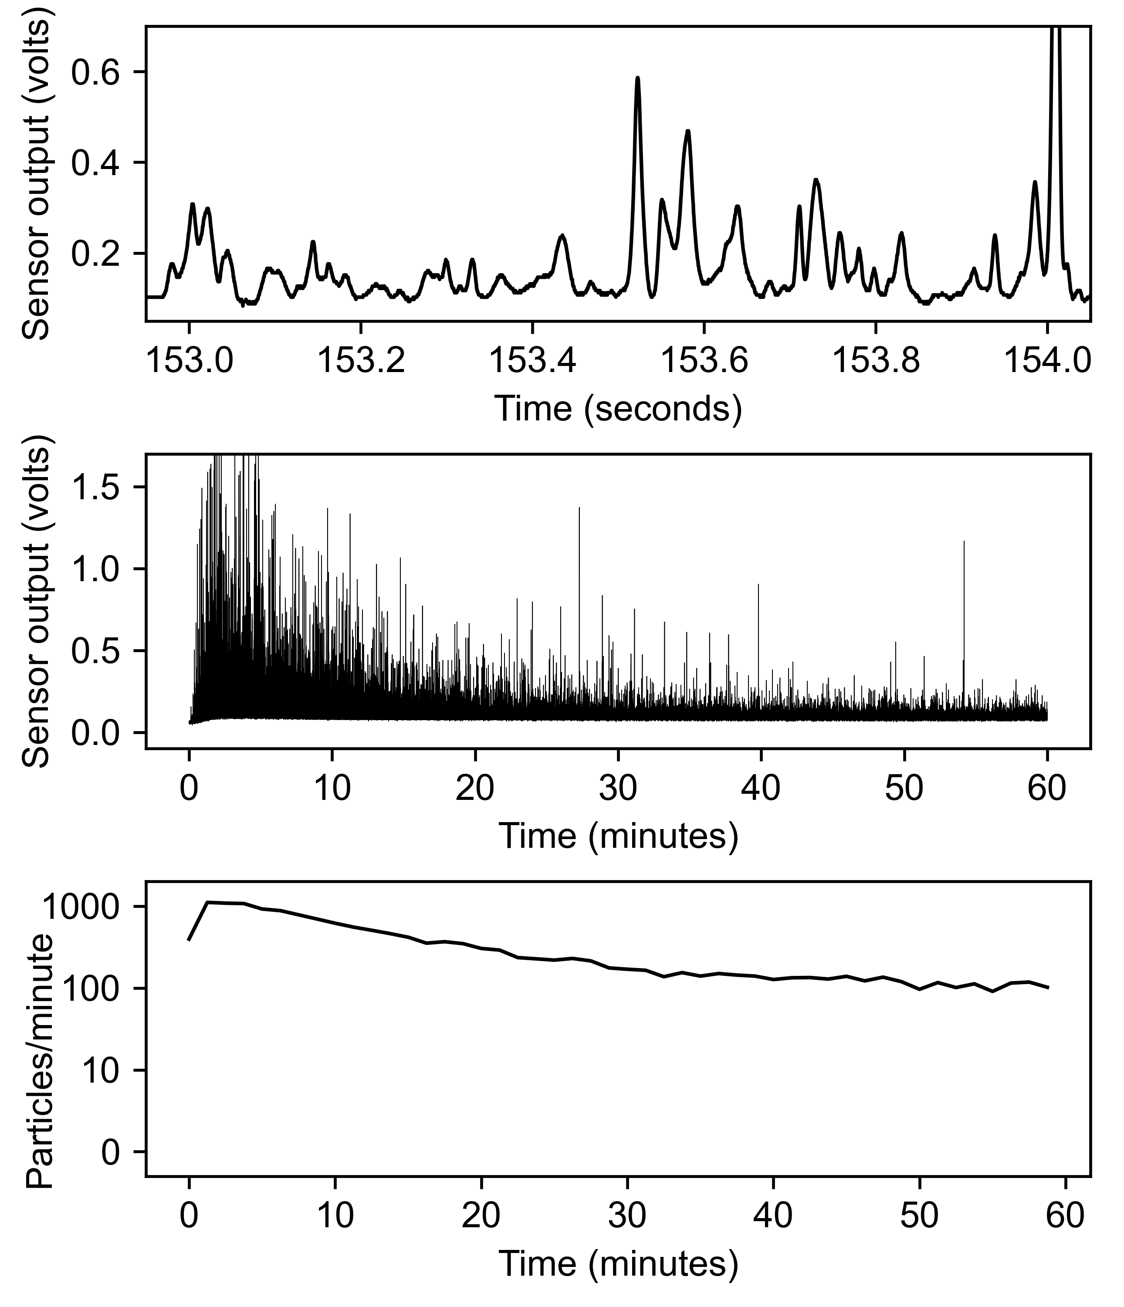
data/variety/Ibuprofen methocarbamol/20241121T220440_ibuprofen_methocarbamol.json.gz.png
