groverlab/disintegration-fingerprinting/data/variety/Ibuprofen/20241117T195410_ibuprofen_600mg_generic.json.gz.png

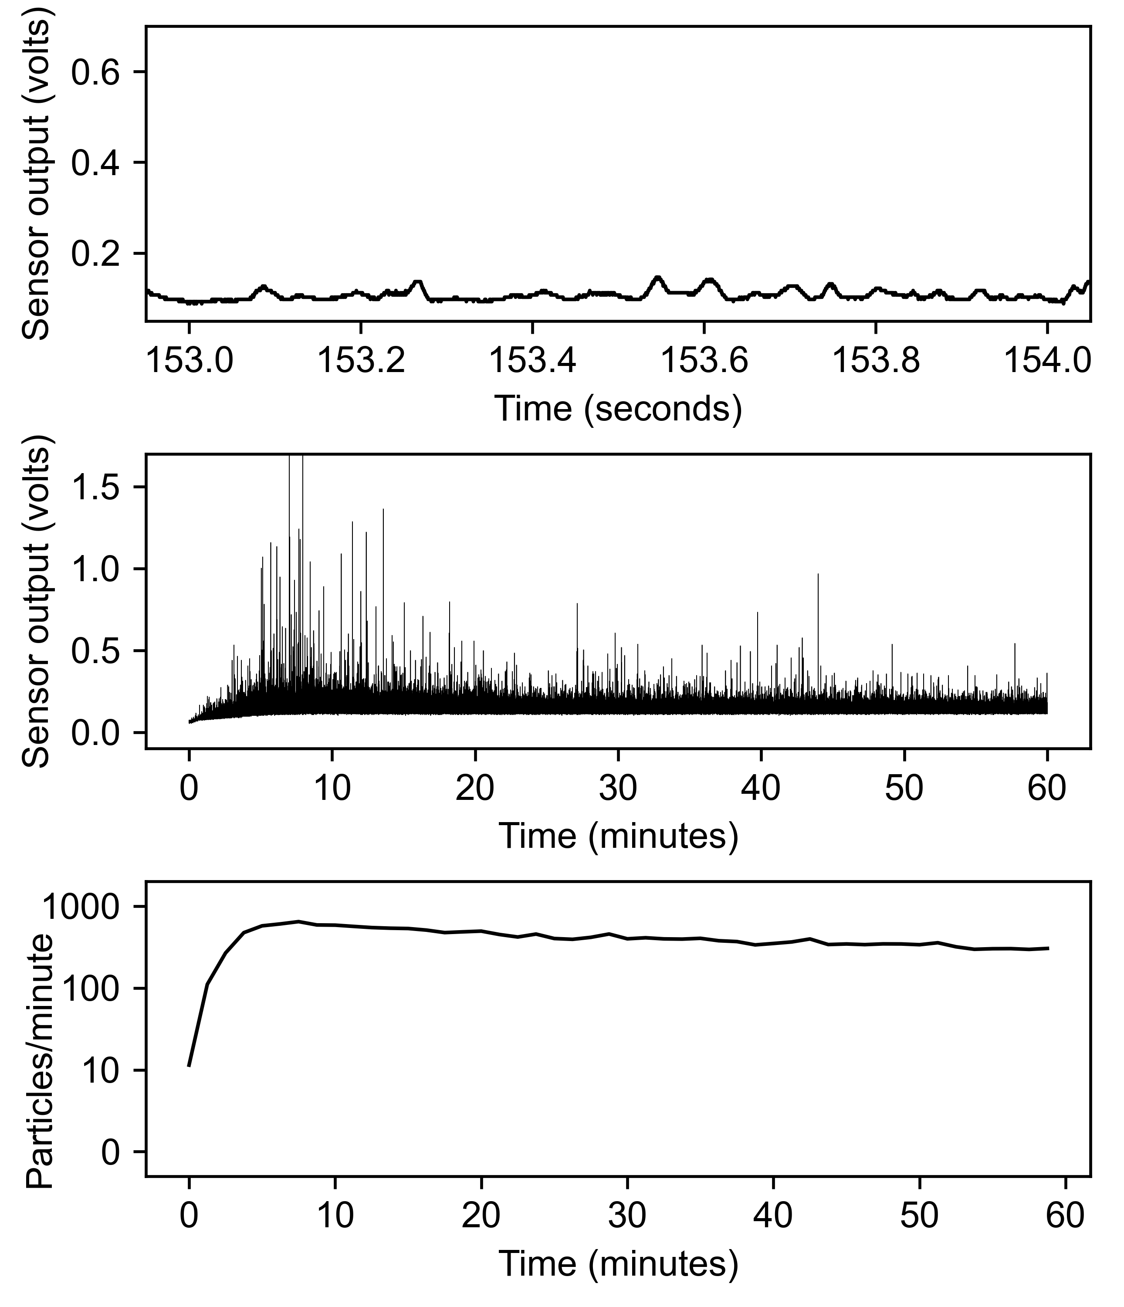
data/variety/Ibuprofen/20241117T195410_ibuprofen_600mg_generic.json.gz.png
