groverlab/disintegration-fingerprinting/data/variety/Ibuprofen/20241118T081627_ibuprofen_600mg_generic.json.gz.png

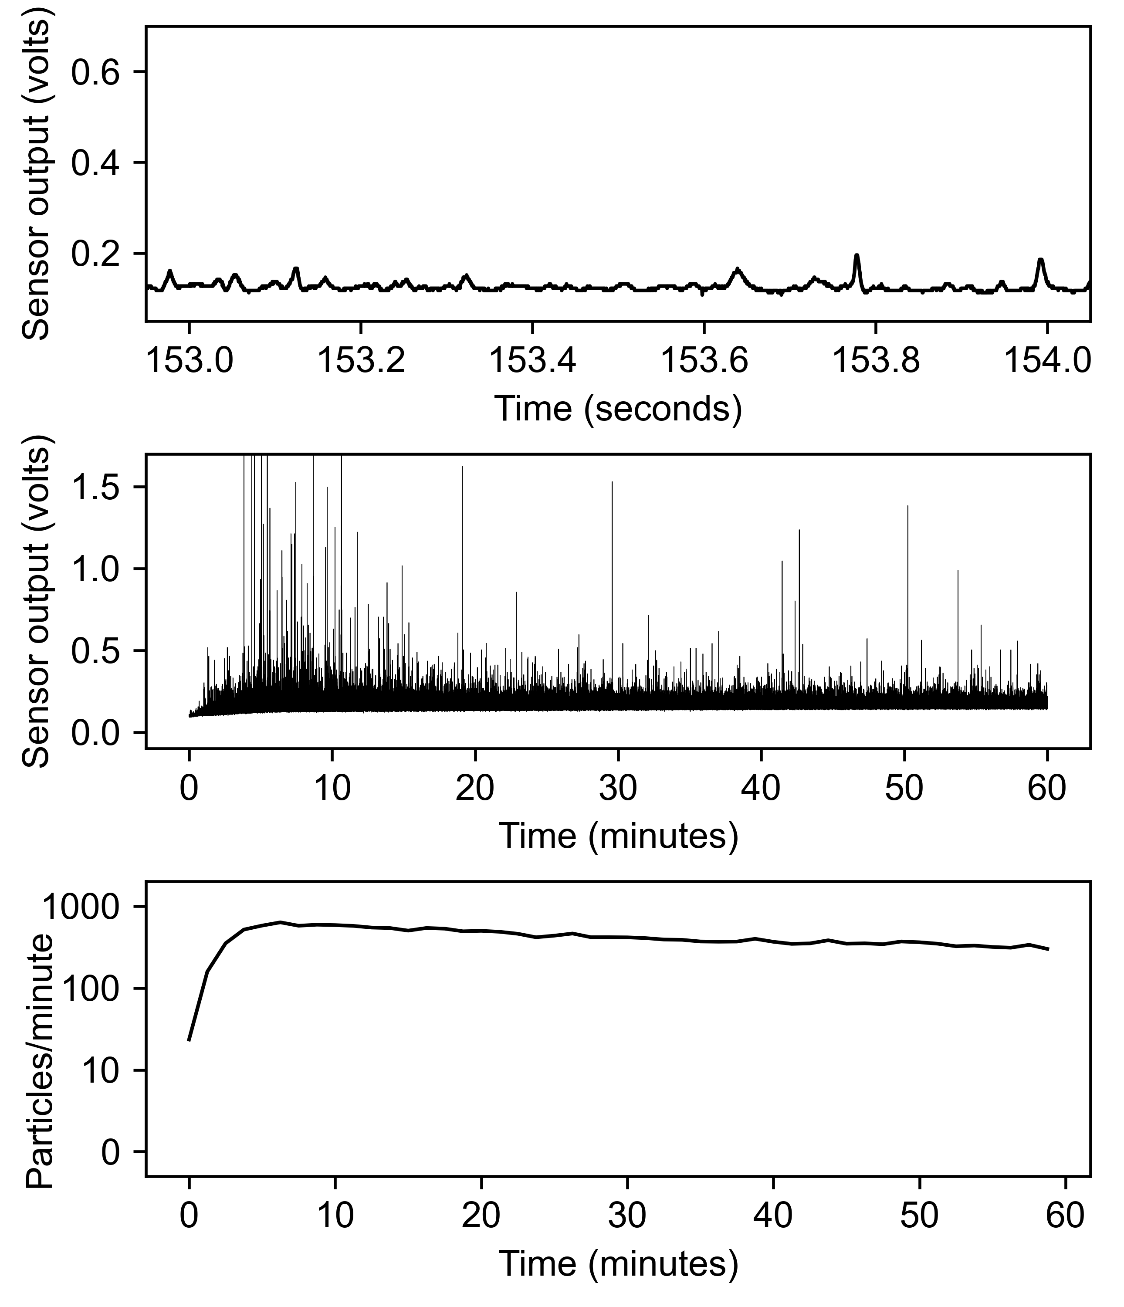
data/variety/Ibuprofen/20241118T081627_ibuprofen_600mg_generic.json.gz.png
