groverlab/disintegration-fingerprinting/data/variety/Ibuprofen/20241118T092825_ibuprofen_600mg_generic.json.gz.png

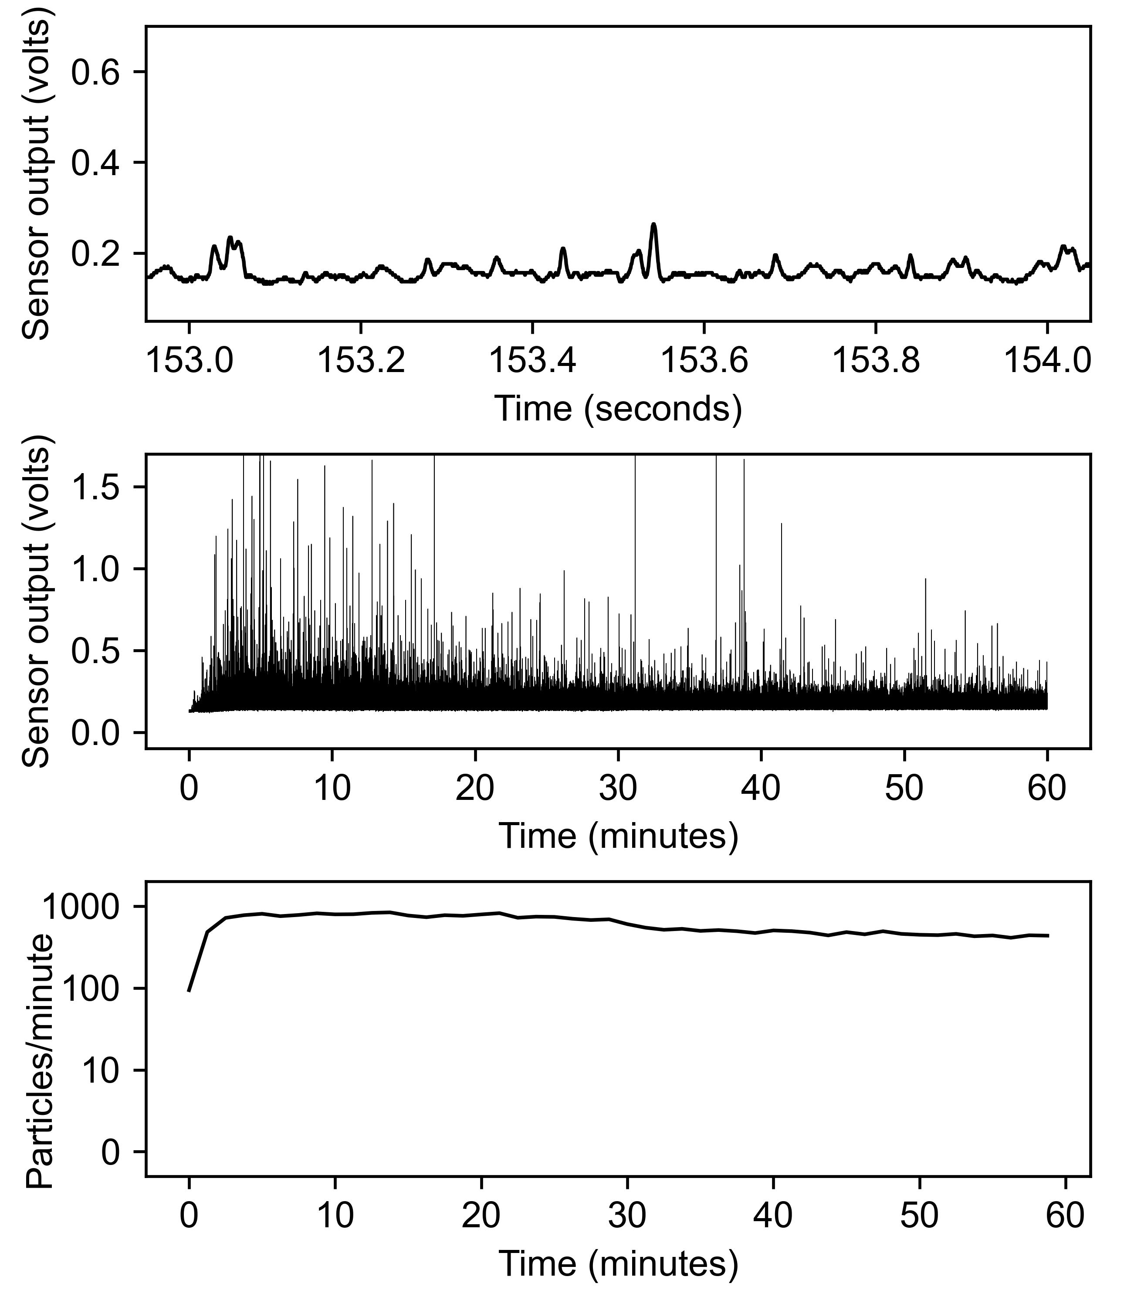
data/variety/Ibuprofen/20241118T092825_ibuprofen_600mg_generic.json.gz.png
