groverlab/disintegration-fingerprinting/data/variety/Iron complex/20241122T201813_iron_complex.json.gz.png

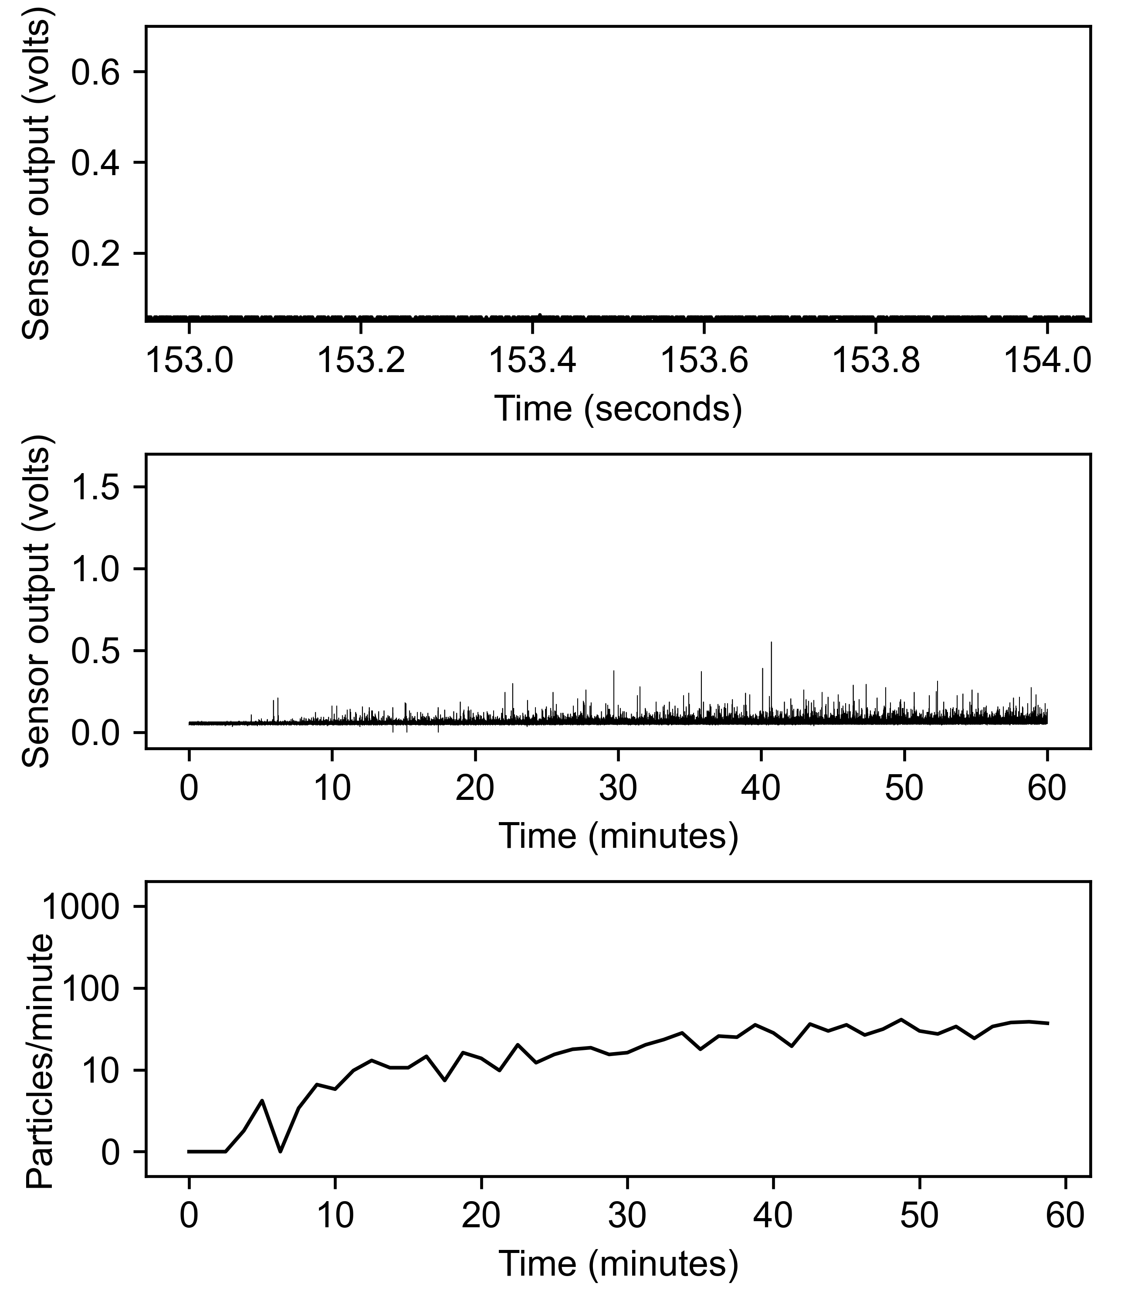
data/variety/Iron complex/20241122T201813_iron_complex.json.gz.png
