groverlab/disintegration-fingerprinting/data/variety/Iron complex/20250409T115717_iron_complex.json.gz.png

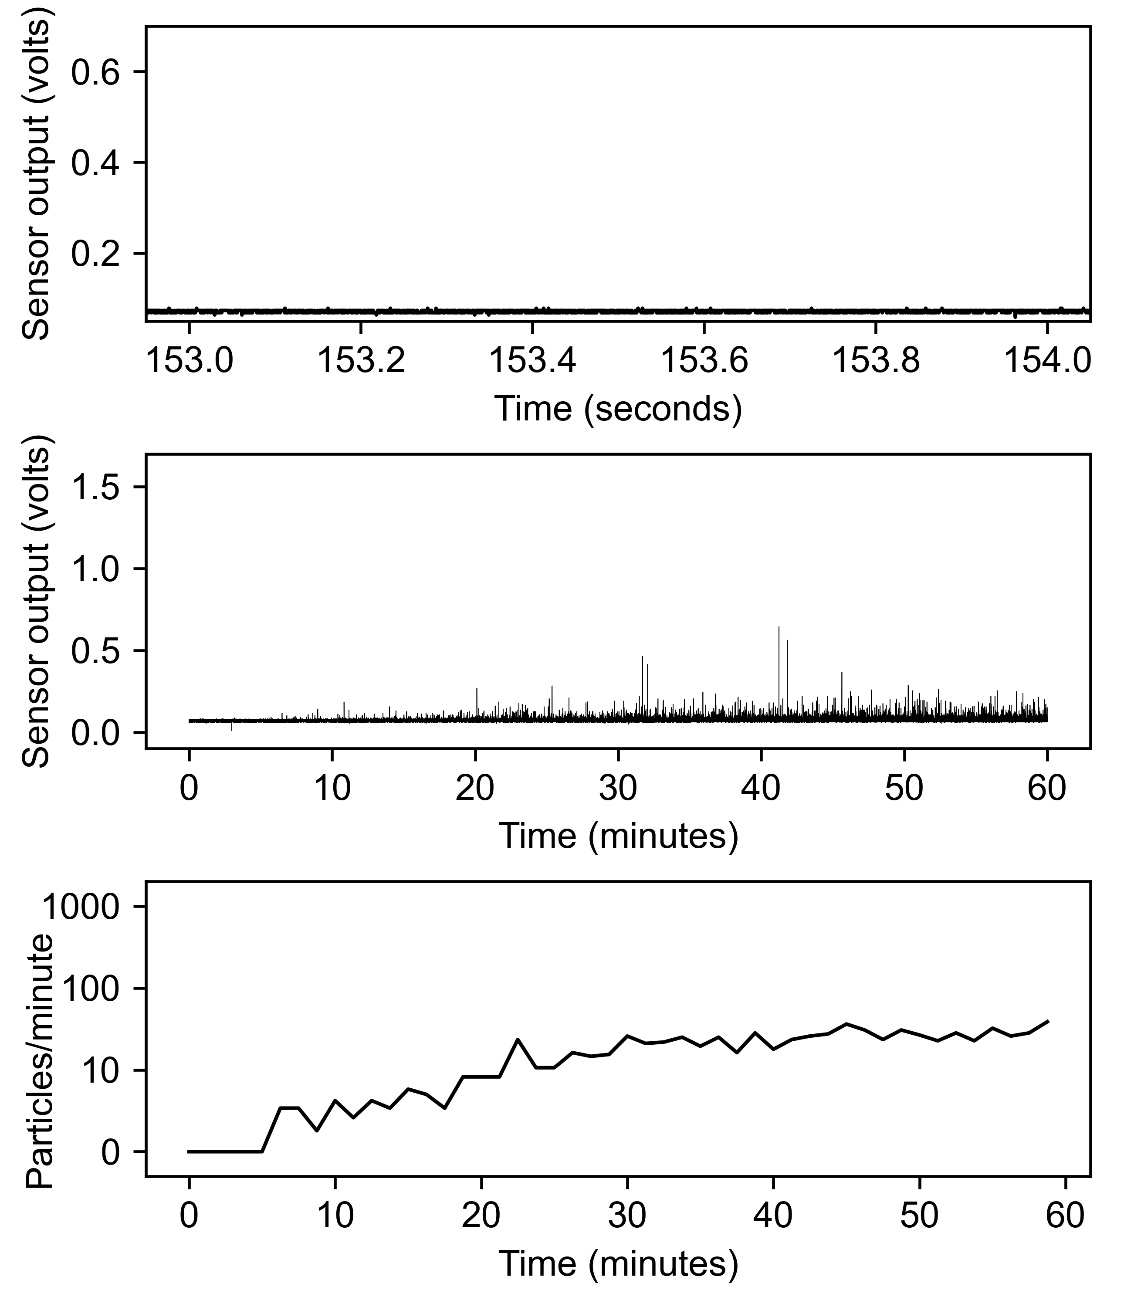
data/variety/Iron complex/20250409T115717_iron_complex.json.gz.png
