groverlab/disintegration-fingerprinting/data/variety/Iron complex/20250409T130446_iron_complex.json.gz.png

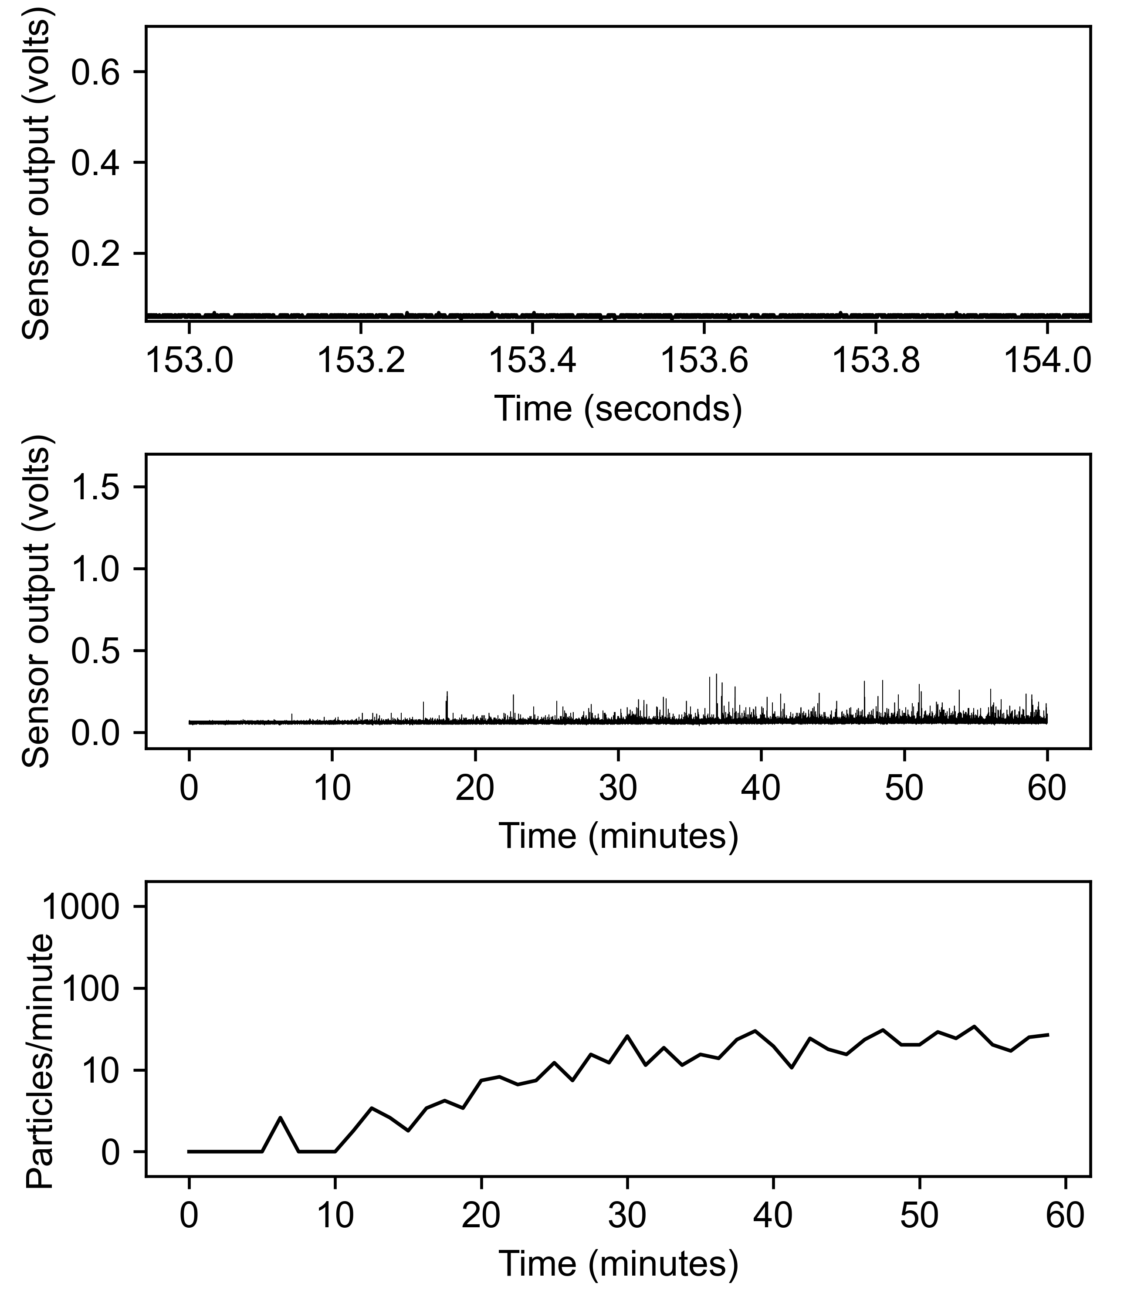
data/variety/Iron complex/20250409T130446_iron_complex.json.gz.png
