groverlab/disintegration-fingerprinting/data/variety/Lactase/20241120T111552_lactase.json.gz.png

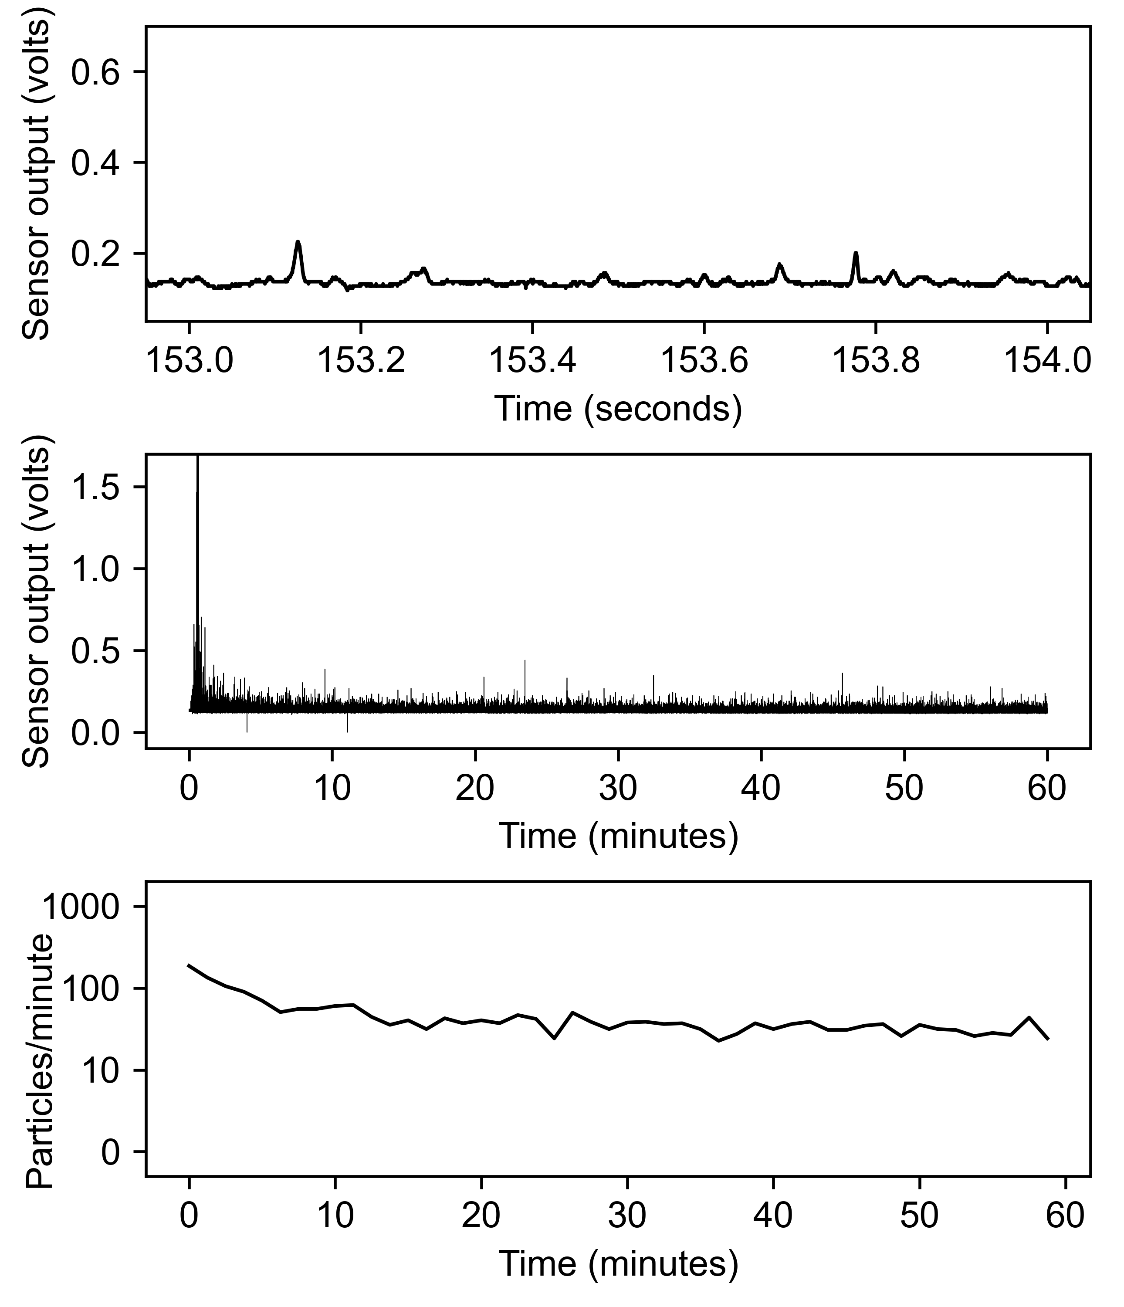
data/variety/Lactase/20241120T111552_lactase.json.gz.png
