groverlab/disintegration-fingerprinting/data/variety/Magnesium oxide chelated/20241122T212828_chelated_magnesium.json.gz.png

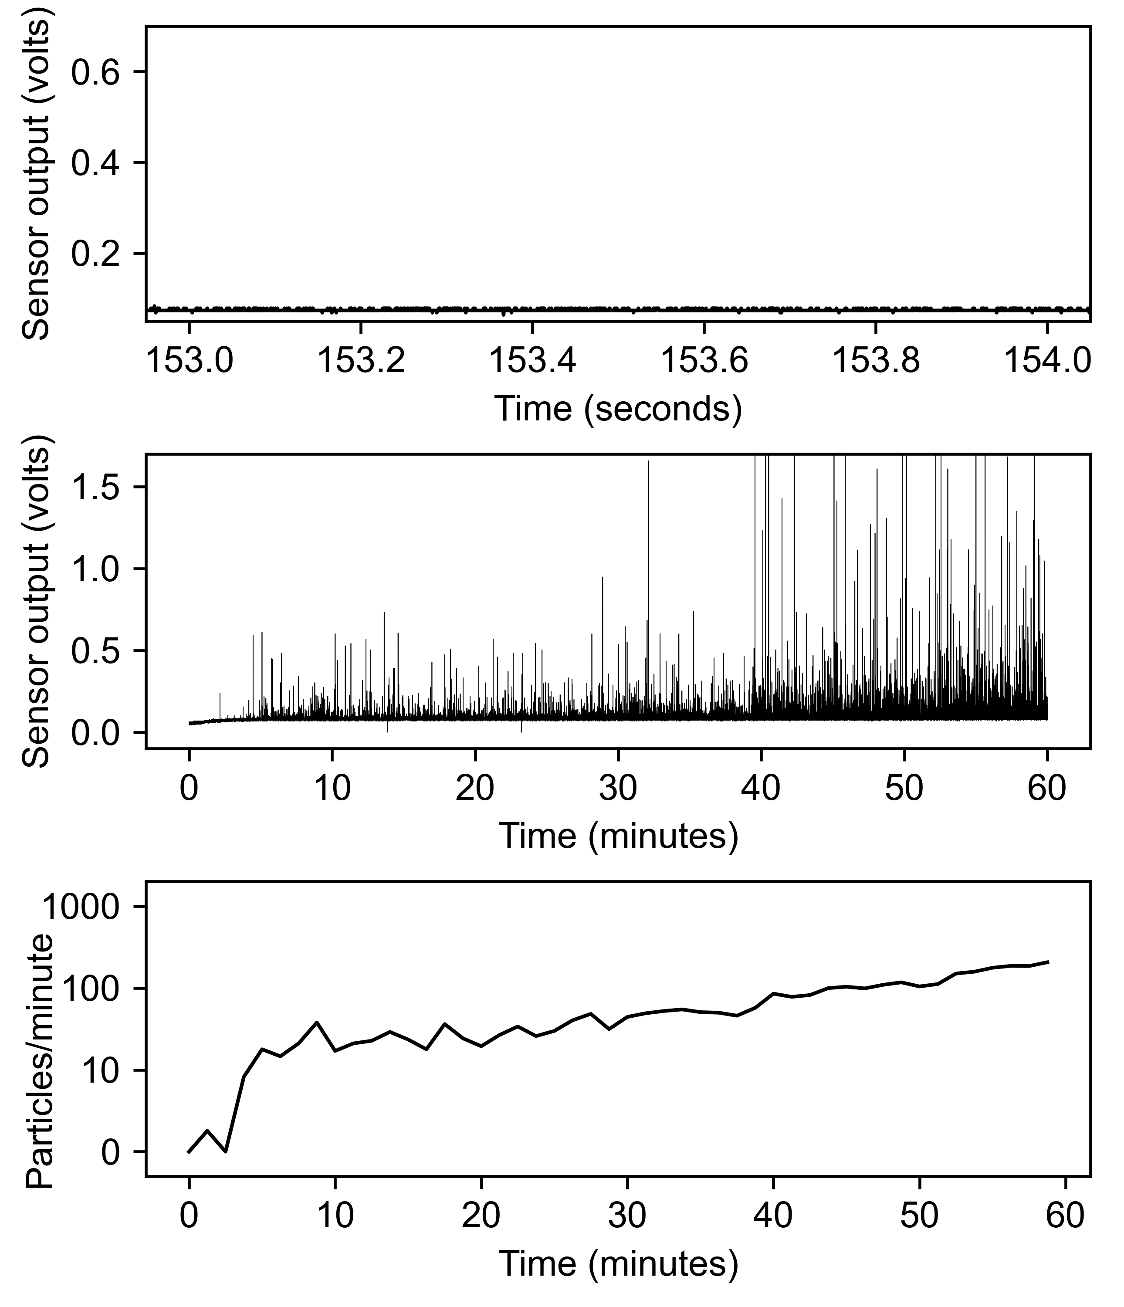
data/variety/Magnesium oxide chelated/20241122T212828_chelated_magnesium.json.gz.png
