groverlab/disintegration-fingerprinting/data/variety/Magnesium oxide chelated/20241123T082135_chelated_magnesium.json.gz.png

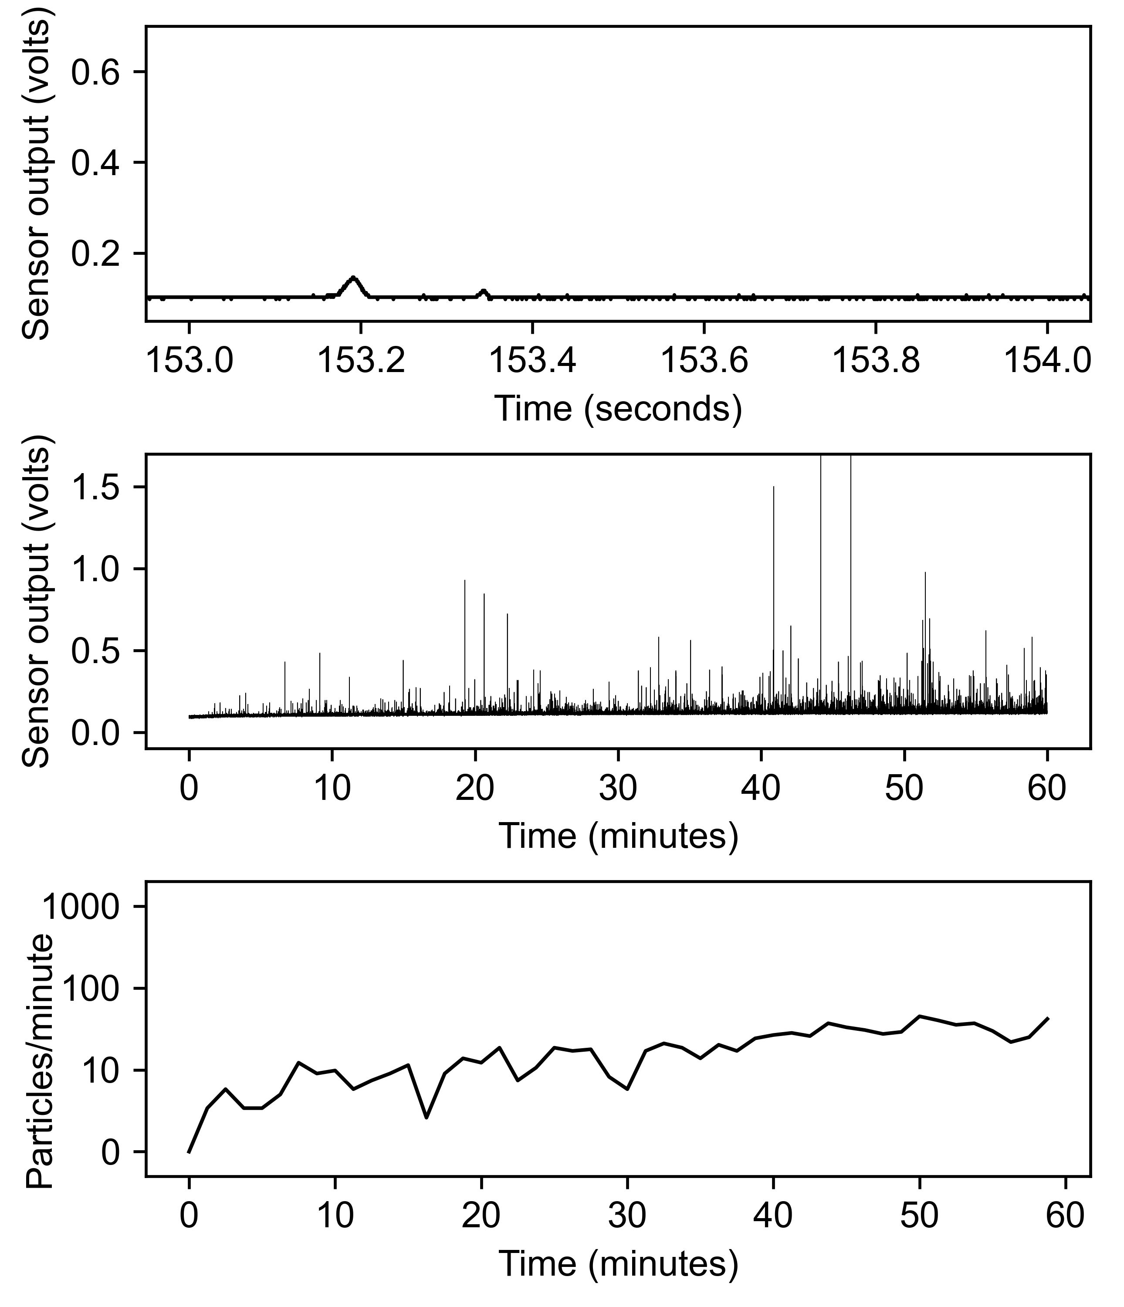
data/variety/Magnesium oxide chelated/20241123T082135_chelated_magnesium.json.gz.png
