groverlab/disintegration-fingerprinting/data/variety/Magnesium oxide/20241118T140948_magnesium_250mg.json.gz.png

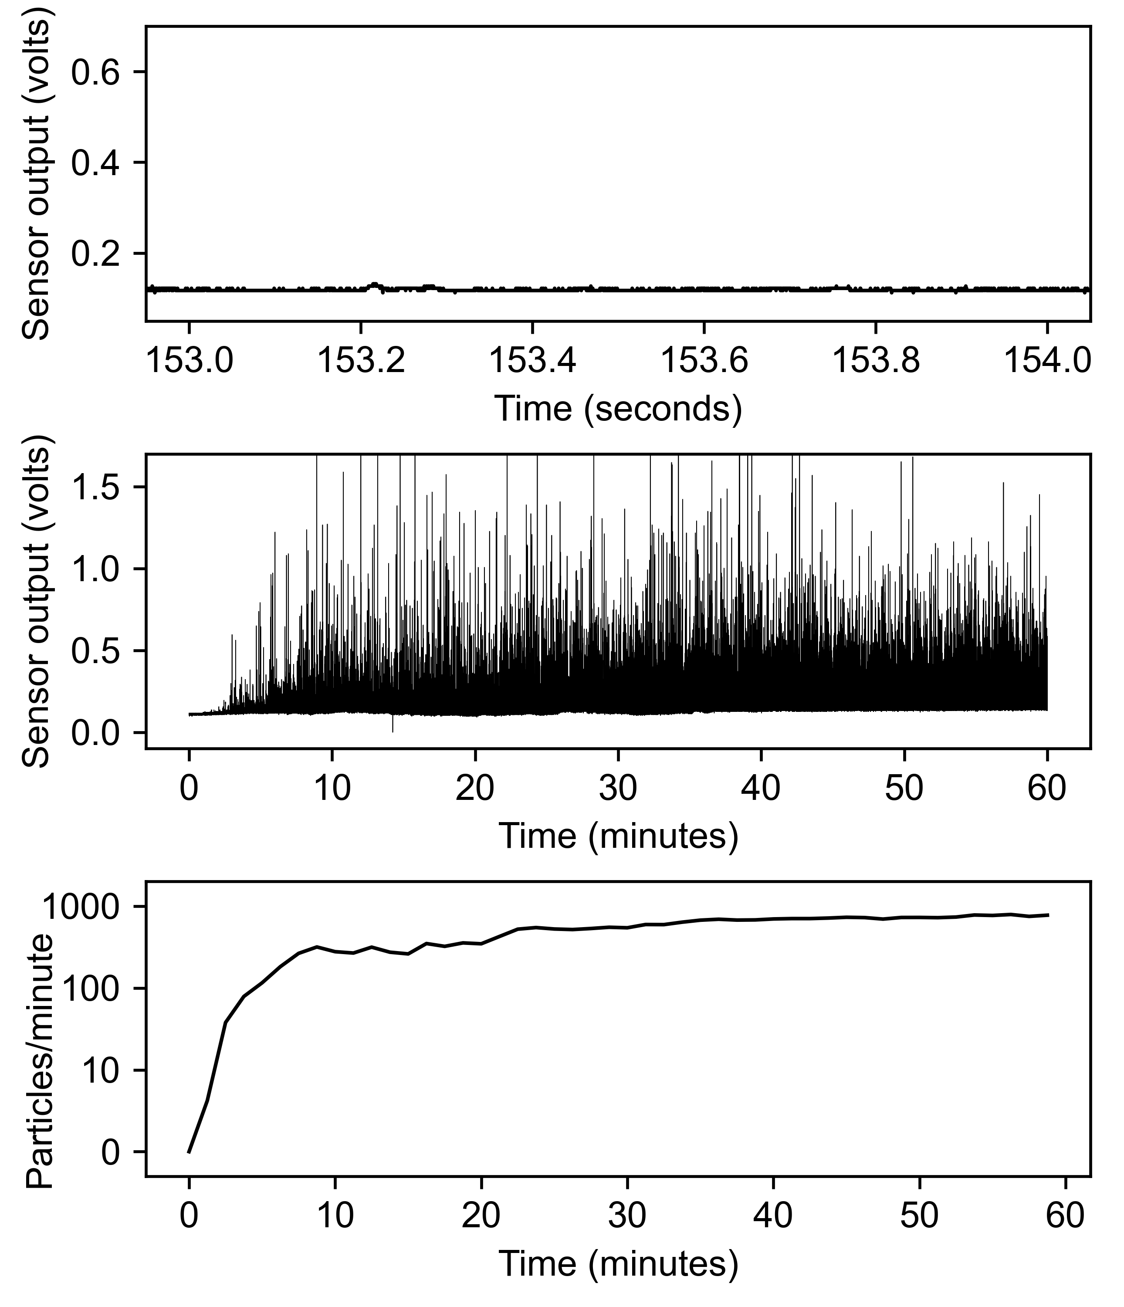
data/variety/Magnesium oxide/20241118T140948_magnesium_250mg.json.gz.png
