groverlab/disintegration-fingerprinting/data/variety/Magnesium oxide/20241118T161414_magnesium_250mg.json.gz.png

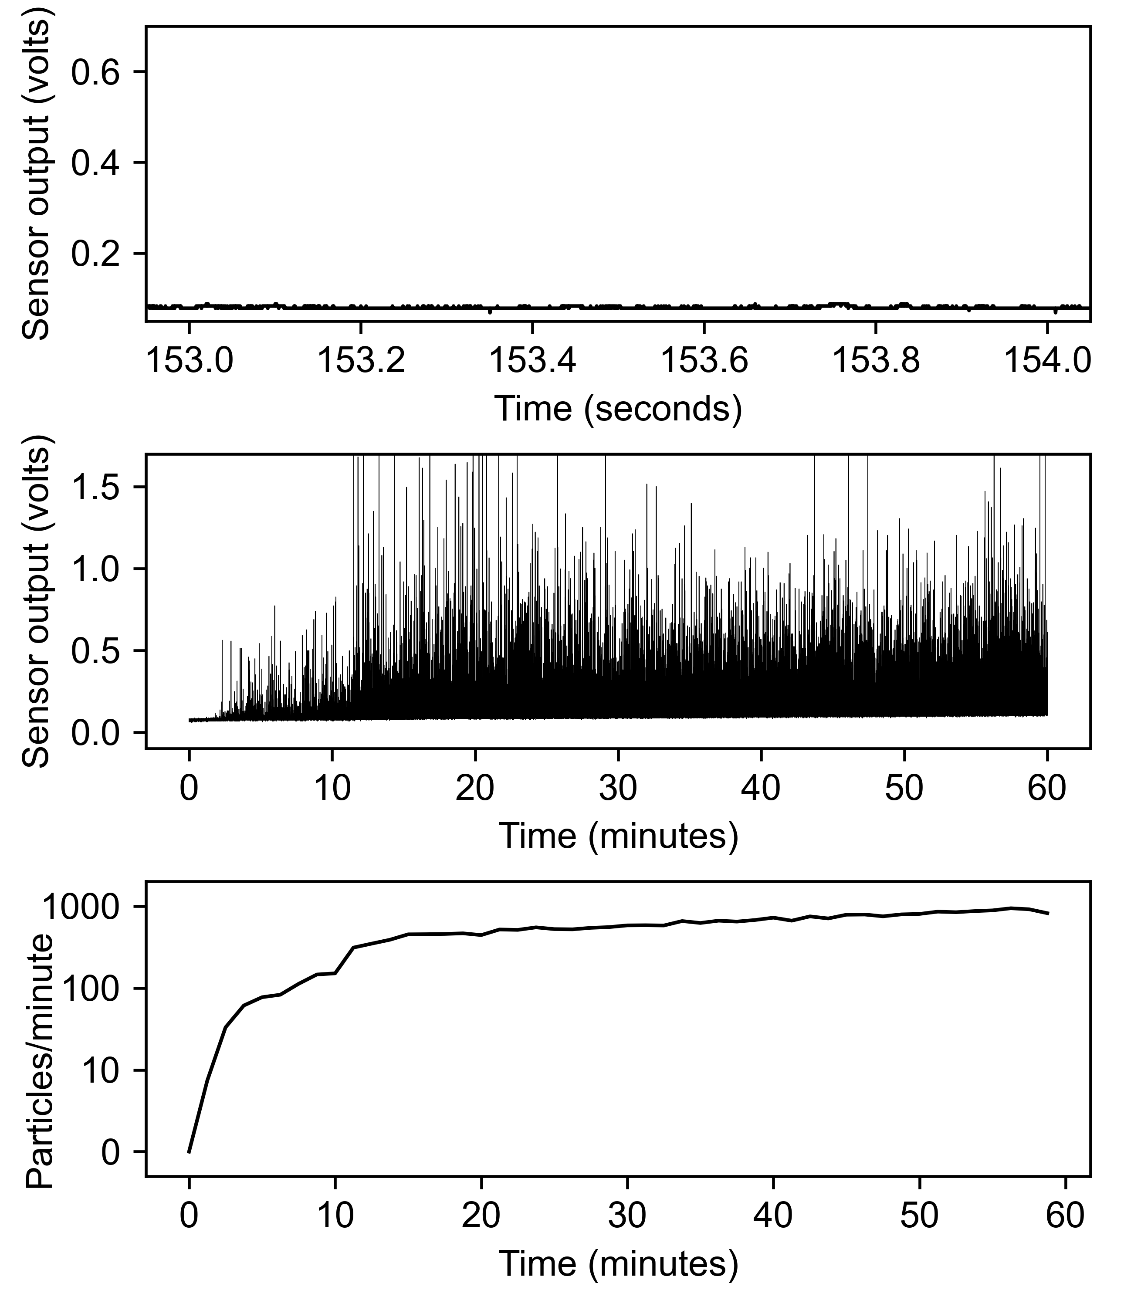
data/variety/Magnesium oxide/20241118T161414_magnesium_250mg.json.gz.png
