groverlab/disintegration-fingerprinting/data/variety/Magnesium oxide/20241118T175635_magnesium_250mg.json.gz.png

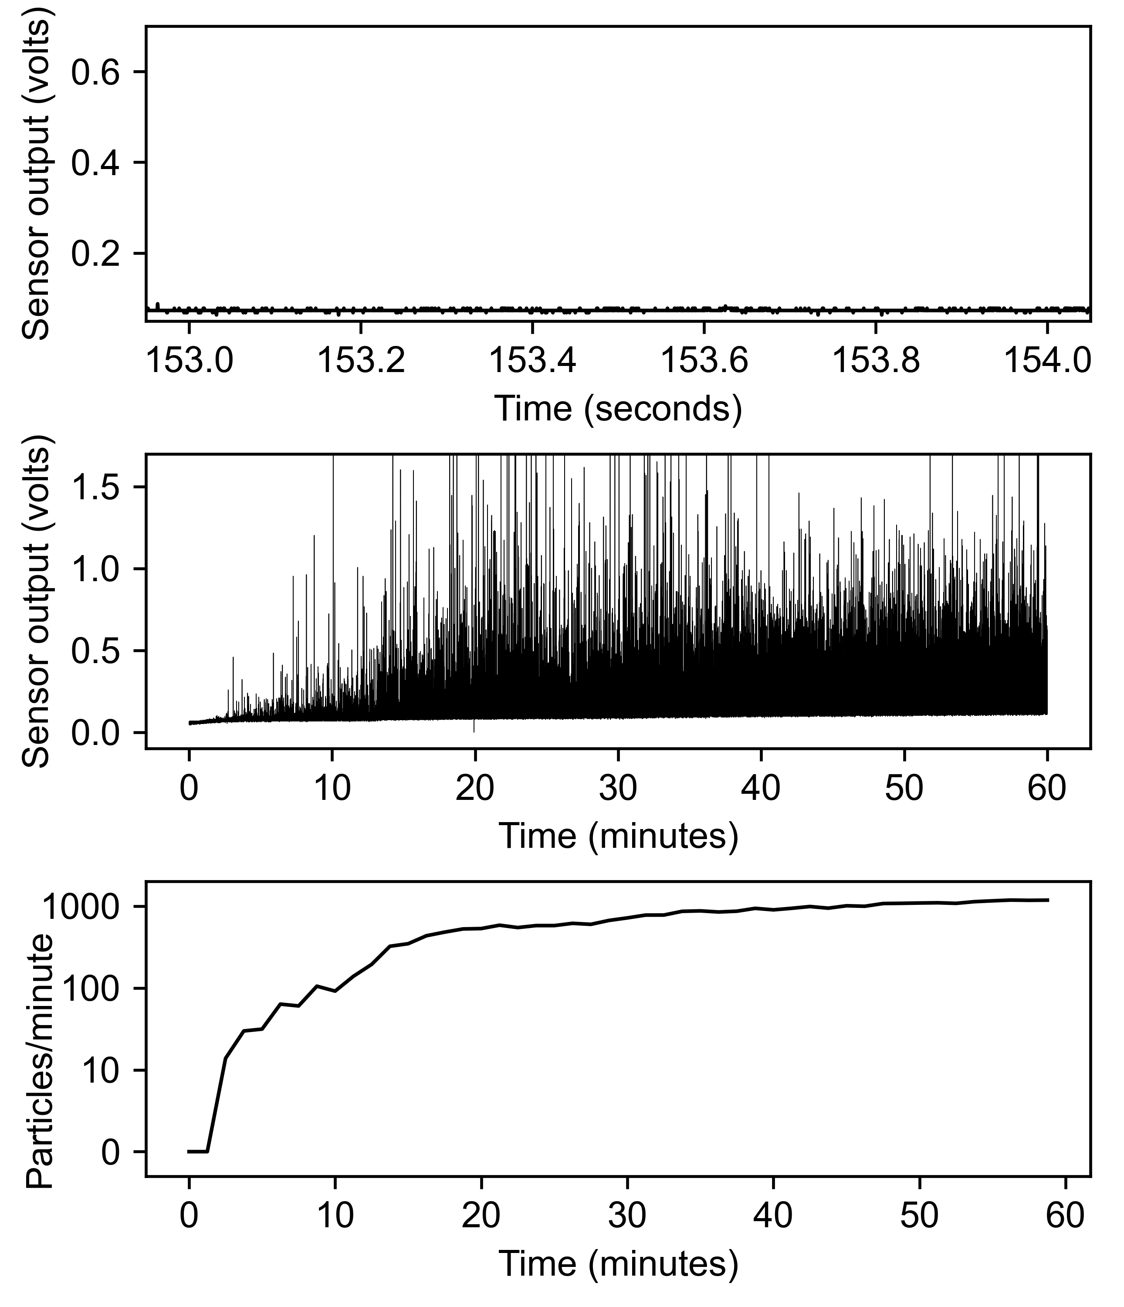
data/variety/Magnesium oxide/20241118T175635_magnesium_250mg.json.gz.png
