groverlab/disintegration-fingerprinting/data/variety/Meclizine/20241122T131011_meclizine.json.gz.png

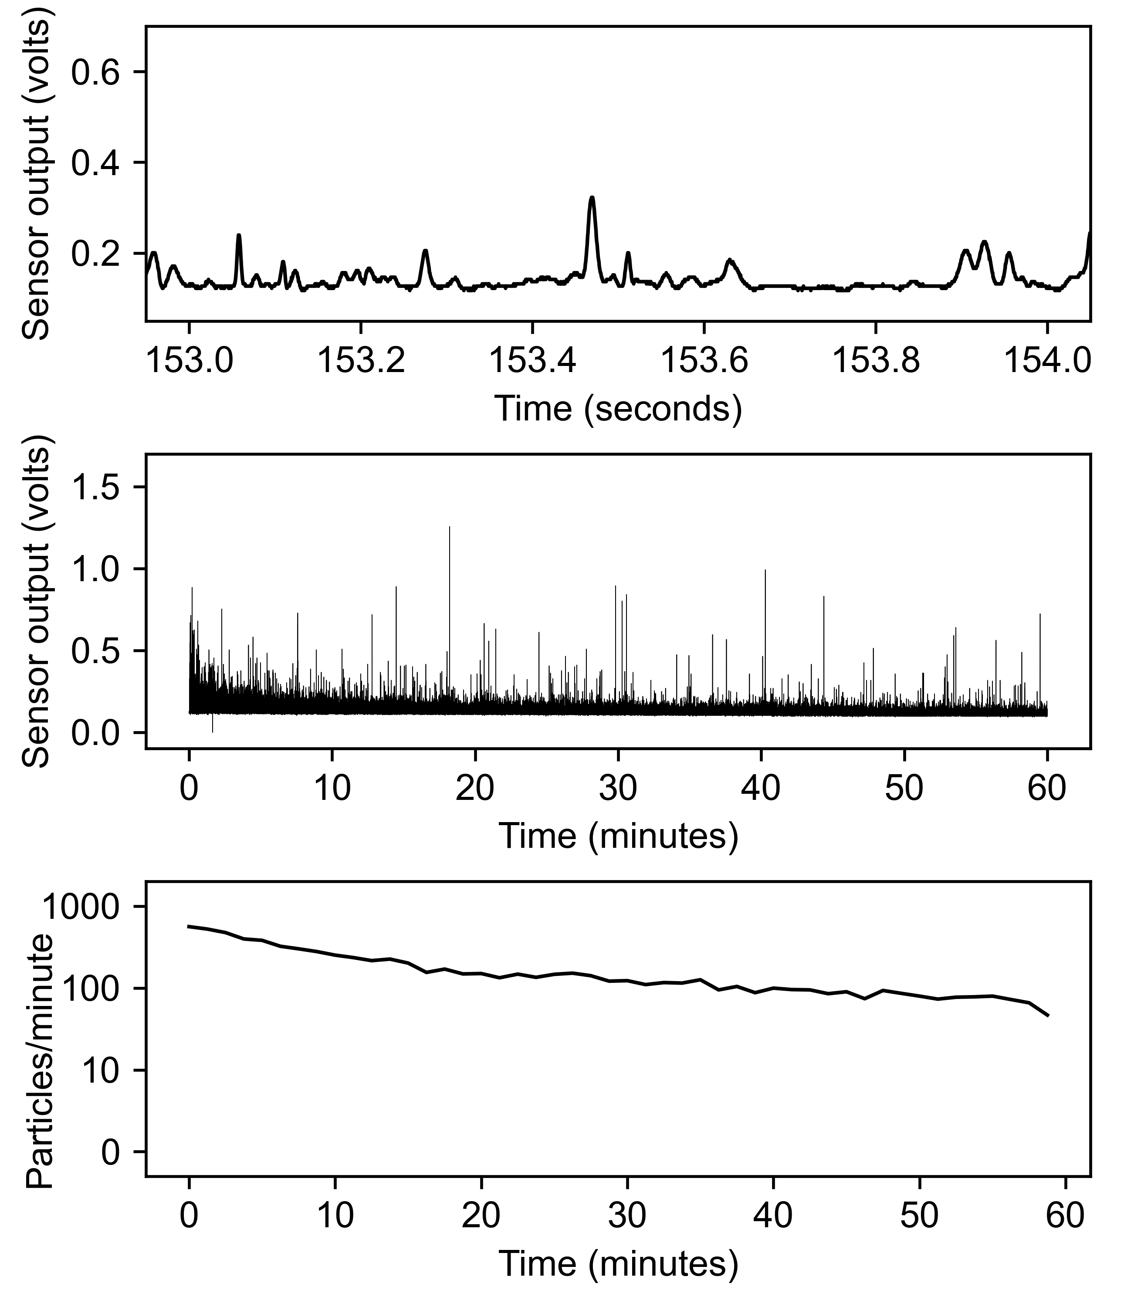
data/variety/Meclizine/20241122T131011_meclizine.json.gz.png
