groverlab/disintegration-fingerprinting/data/variety/Meclizine/20241122T141647_meclizine.json.gz.png

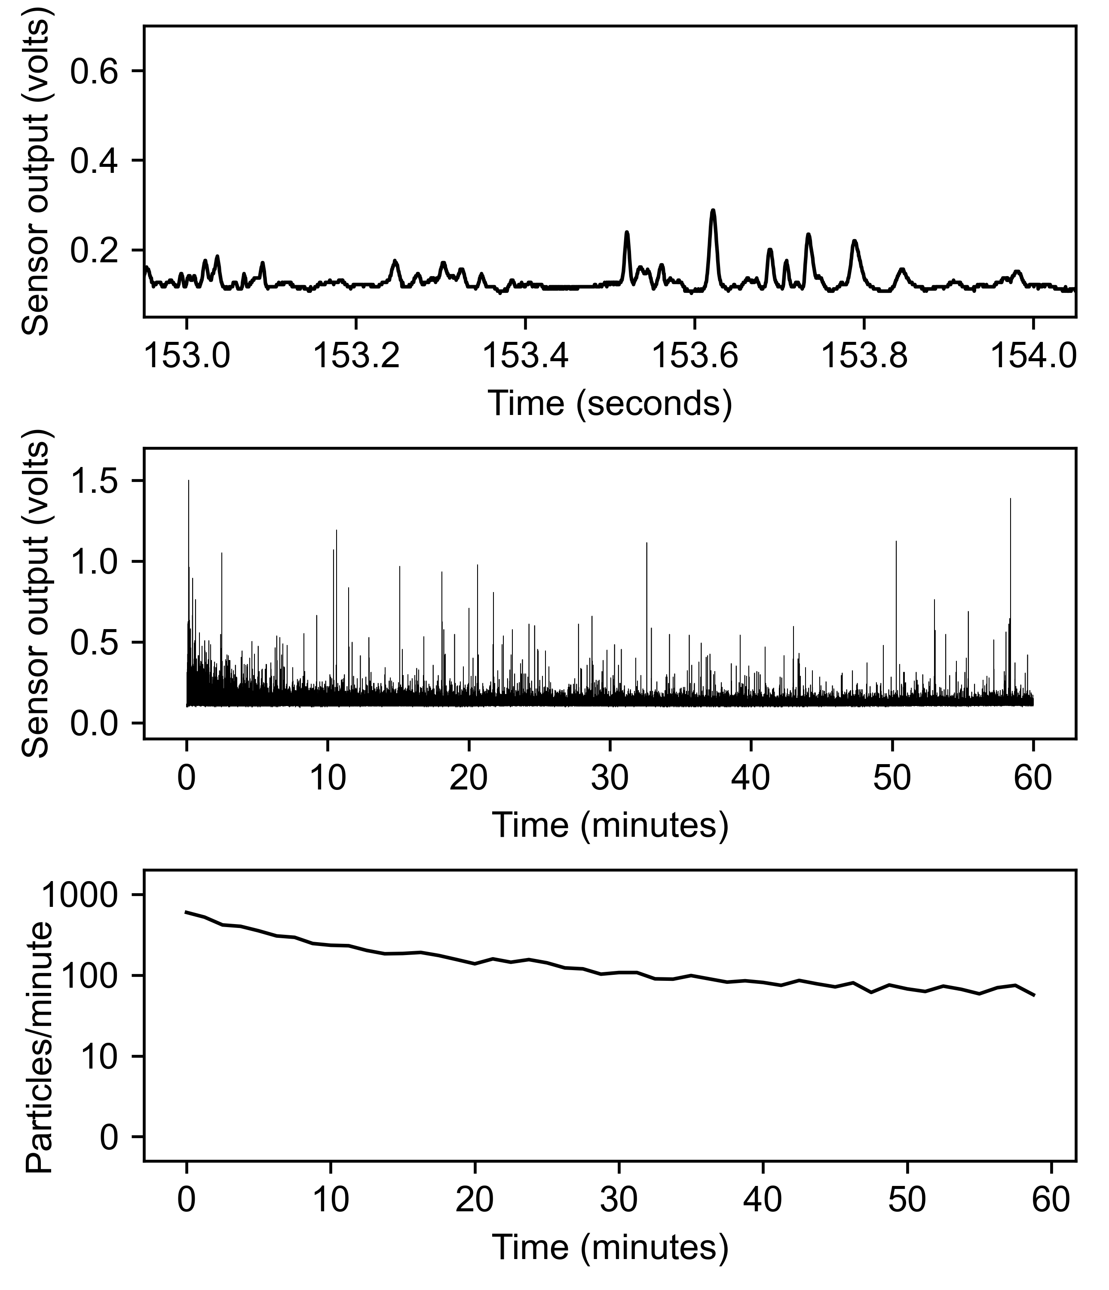
data/variety/Meclizine/20241122T141647_meclizine.json.gz.png
