groverlab/disintegration-fingerprinting/data/variety/Meclizine/20241122T152524_meclizine.json.gz.png

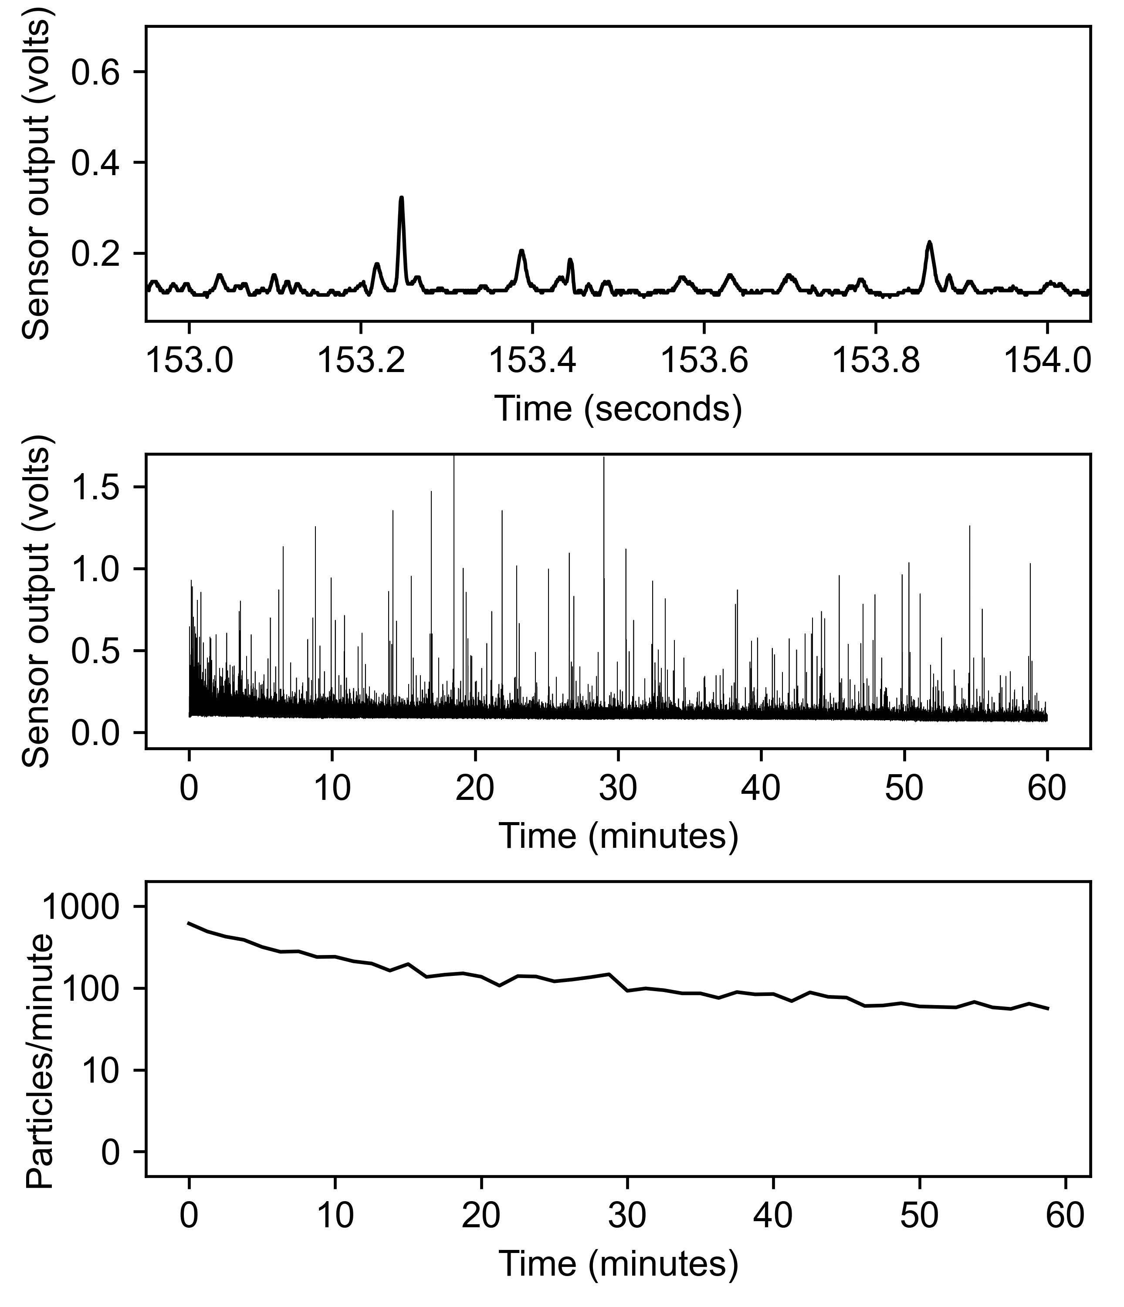
data/variety/Meclizine/20241122T152524_meclizine.json.gz.png
