groverlab/disintegration-fingerprinting/data/variety/Melatonin/20241122T165417_melatonin.json.gz.png

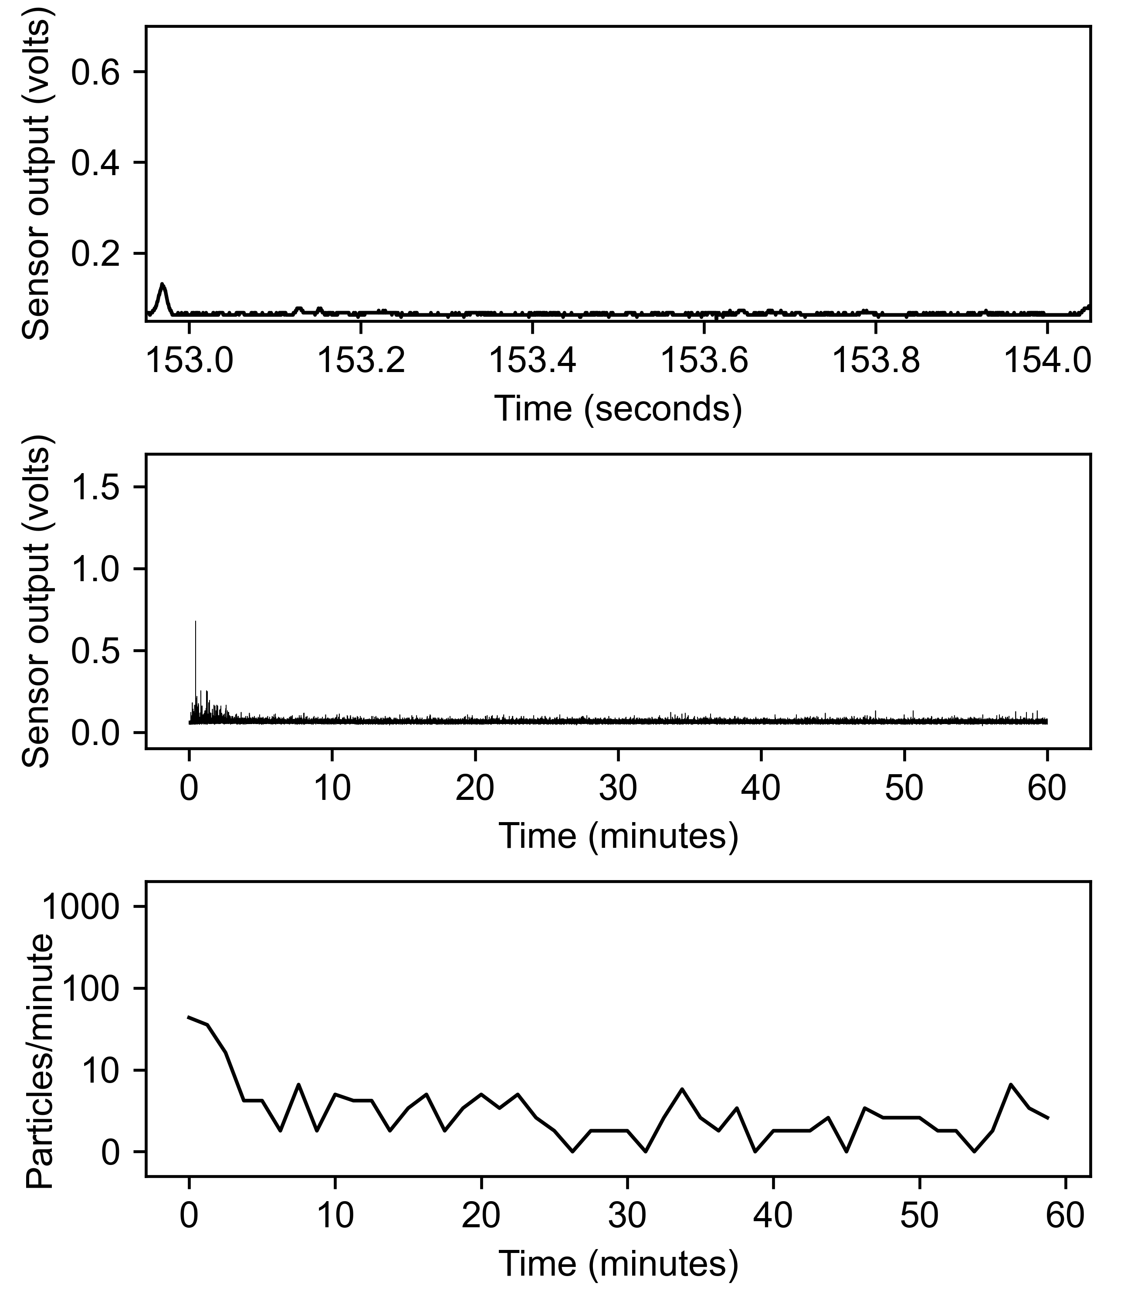
data/variety/Melatonin/20241122T165417_melatonin.json.gz.png
