groverlab/disintegration-fingerprinting/data/variety/Melatonin/20241122T191121_melatonin.json.gz.png

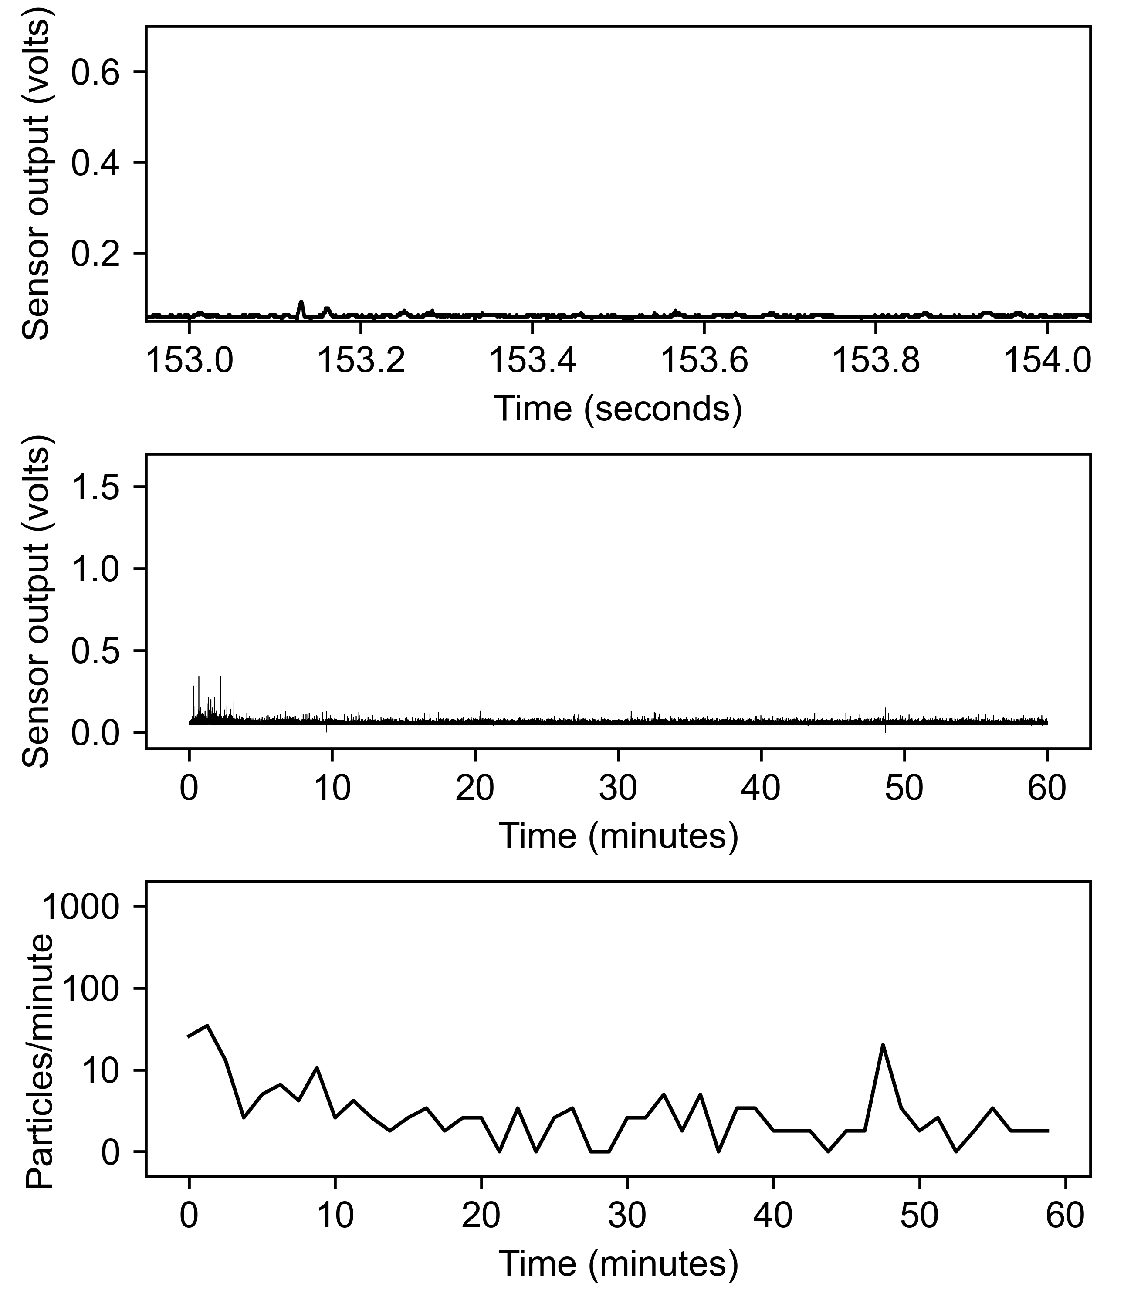
data/variety/Melatonin/20241122T191121_melatonin.json.gz.png
