groverlab/disintegration-fingerprinting/data/variety/Microgestin Fe green/20241125T132524_microgestin_fe_1.5_30_green.json.gz.png

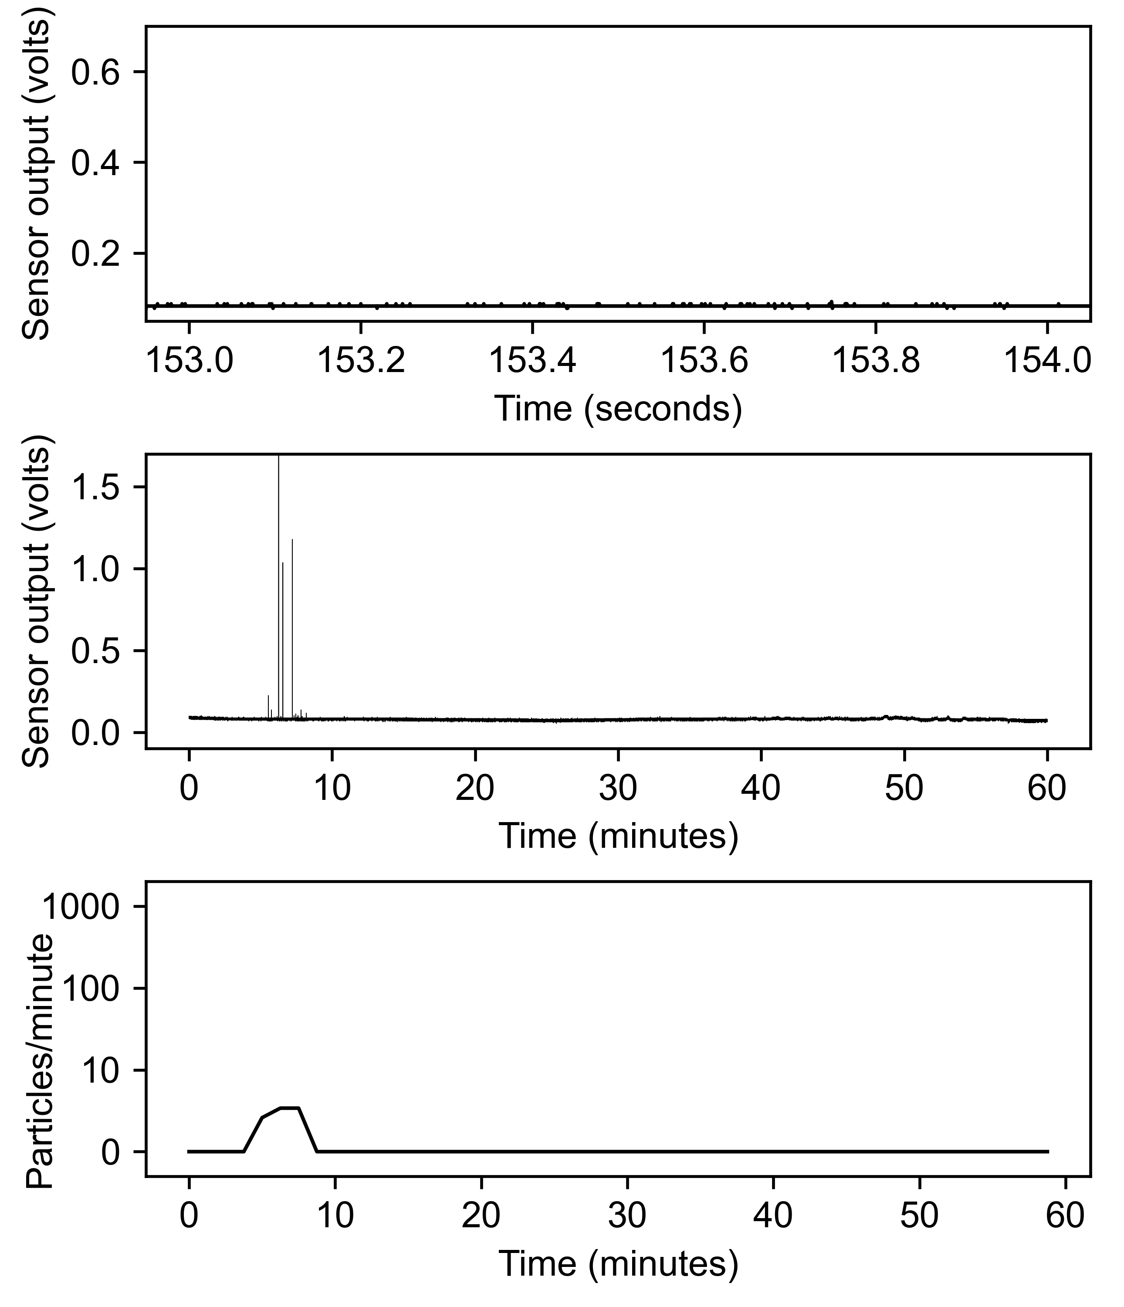
data/variety/Microgestin Fe green/20241125T132524_microgestin_fe_1.5_30_green.json.gz.png
