groverlab/disintegration-fingerprinting/data/variety/Microgestin Fe green/20250421T132354_microgestin_fe_1.5_30_green.json.gz.png

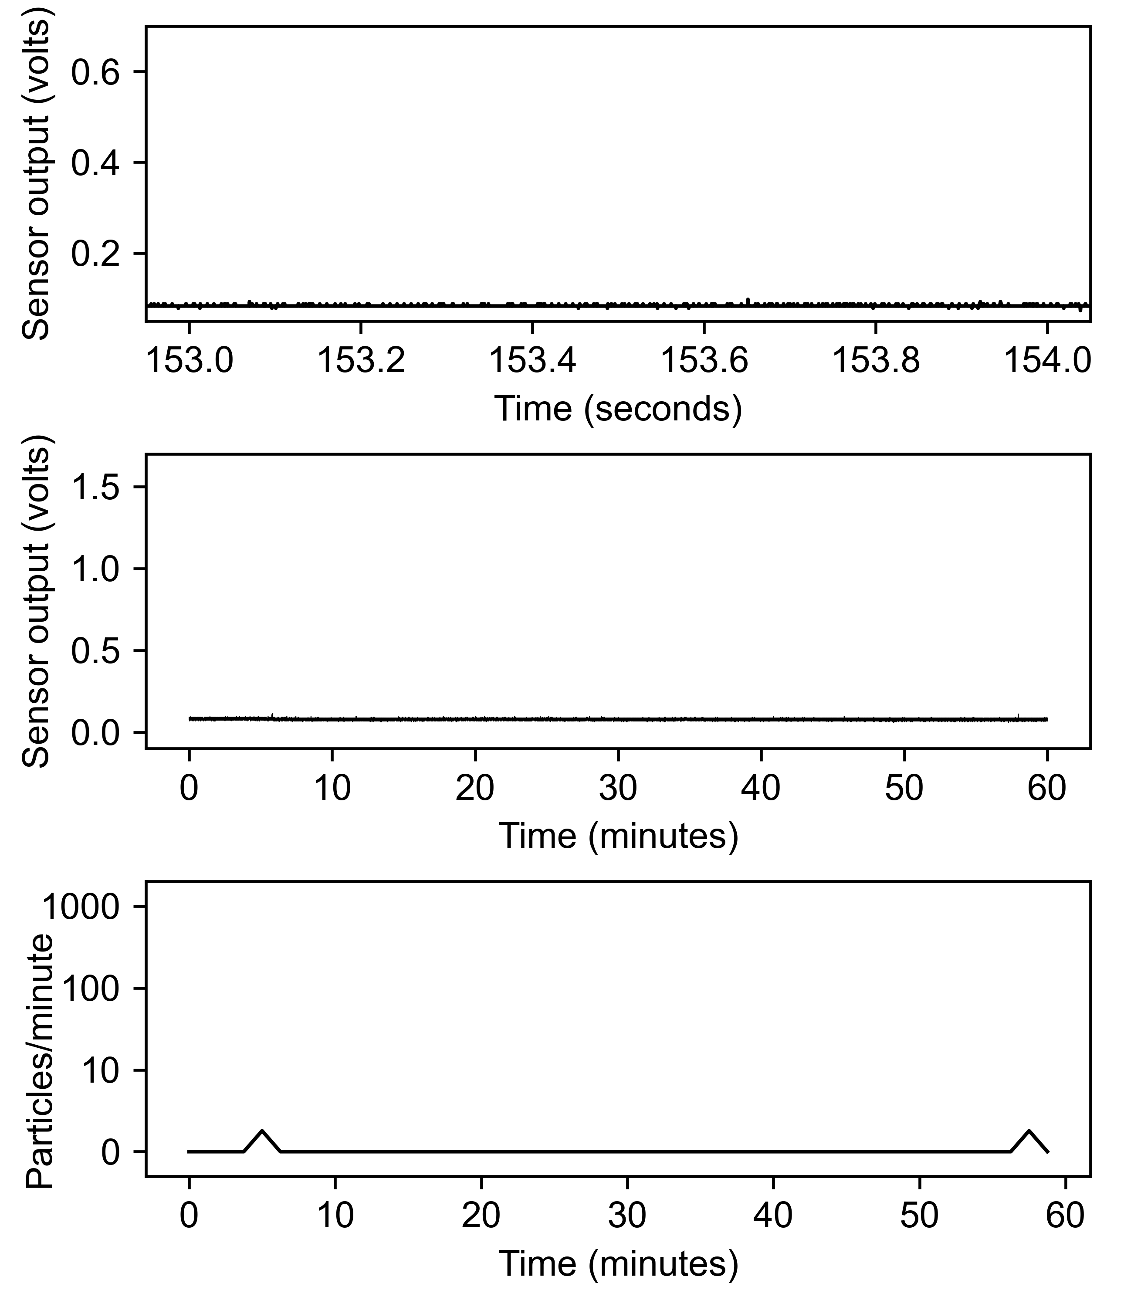
data/variety/Microgestin Fe green/20250421T132354_microgestin_fe_1.5_30_green.json.gz.png
