groverlab/disintegration-fingerprinting/data/variety/Multivitamin/20241118T103838_multivitamin_one_a_day.json.gz.png

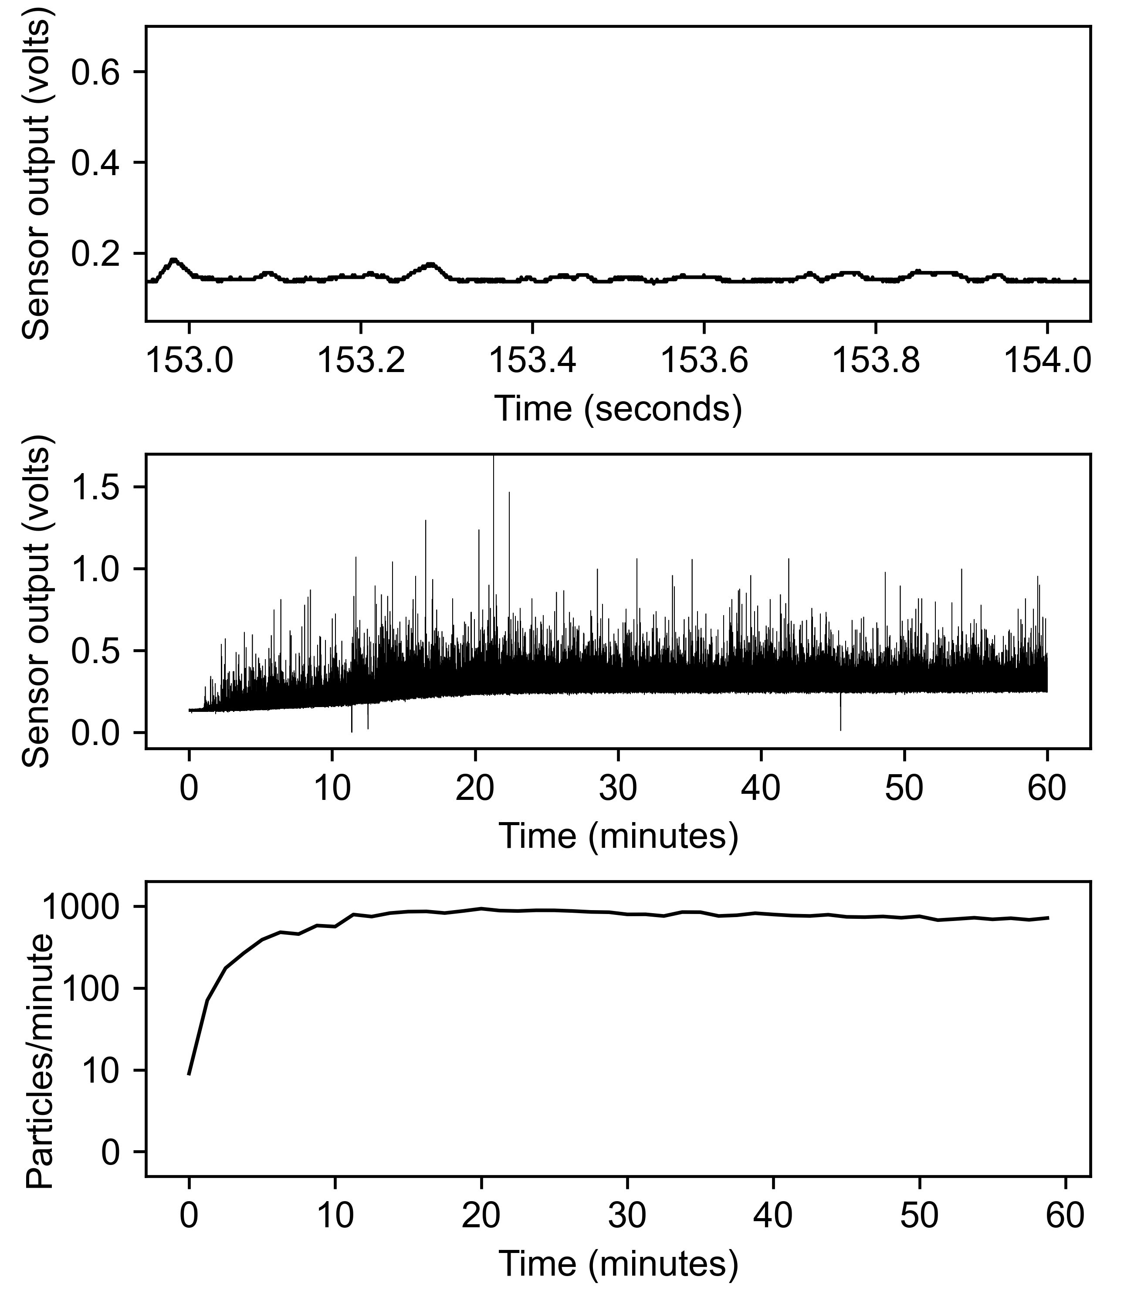
data/variety/Multivitamin/20241118T103838_multivitamin_one_a_day.json.gz.png
