groverlab/disintegration-fingerprinting/data/variety/Multivitamin/20241118T115514_multivitamin_one_a_day.json.gz.png

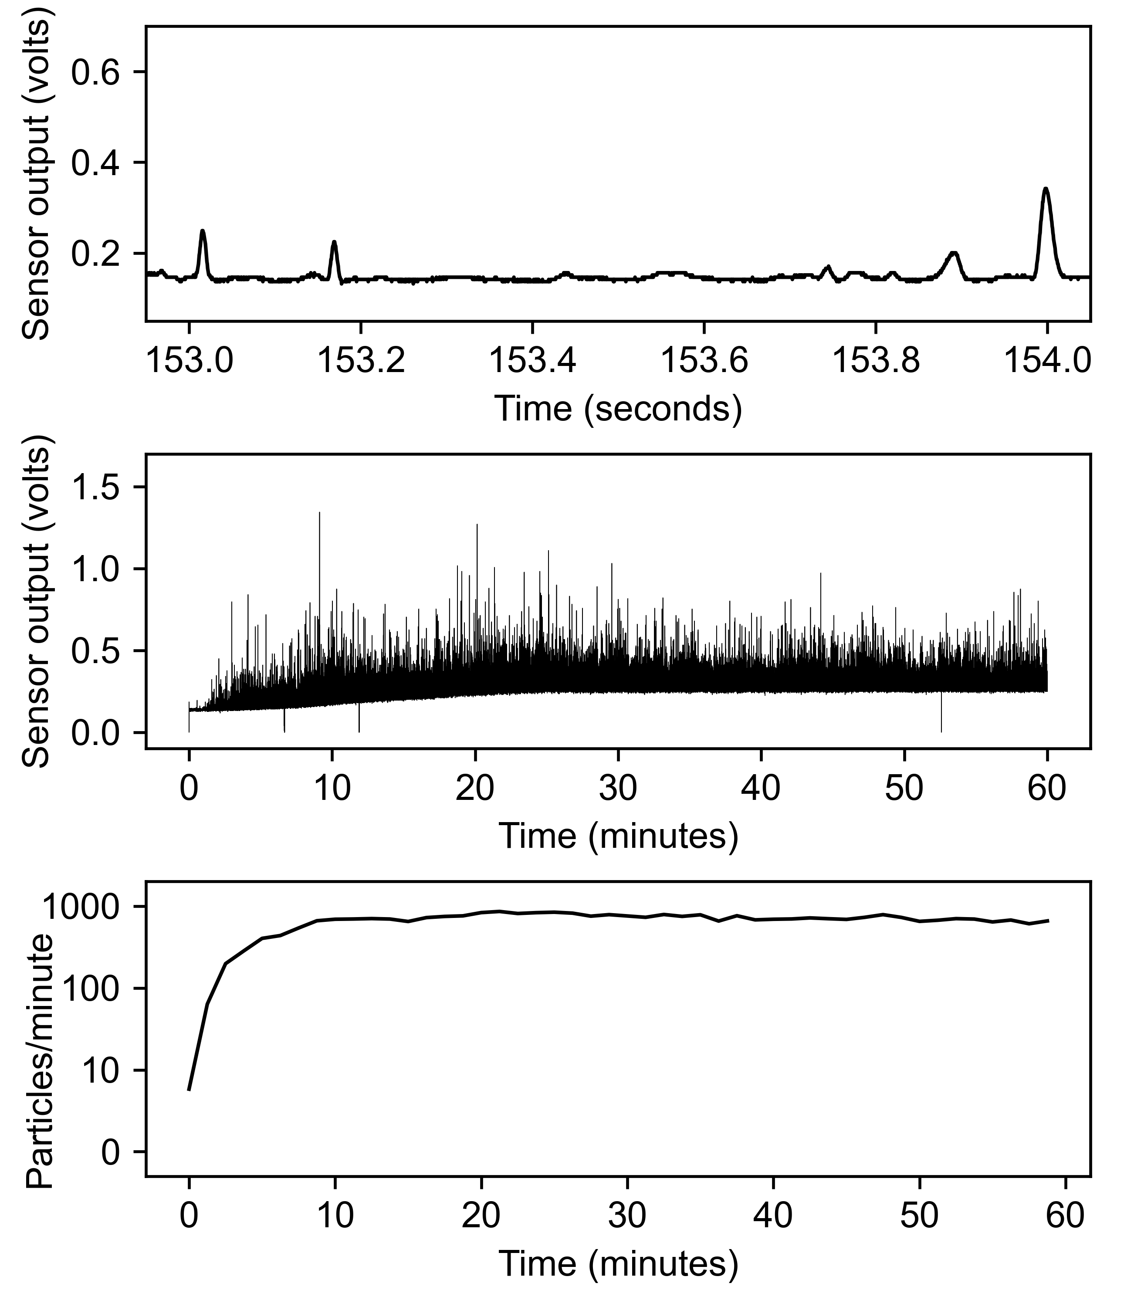
data/variety/Multivitamin/20241118T115514_multivitamin_one_a_day.json.gz.png
