groverlab/disintegration-fingerprinting/data/variety/Multivitamin/20241118T130146_multivitamin_one_a_day.json.gz.png

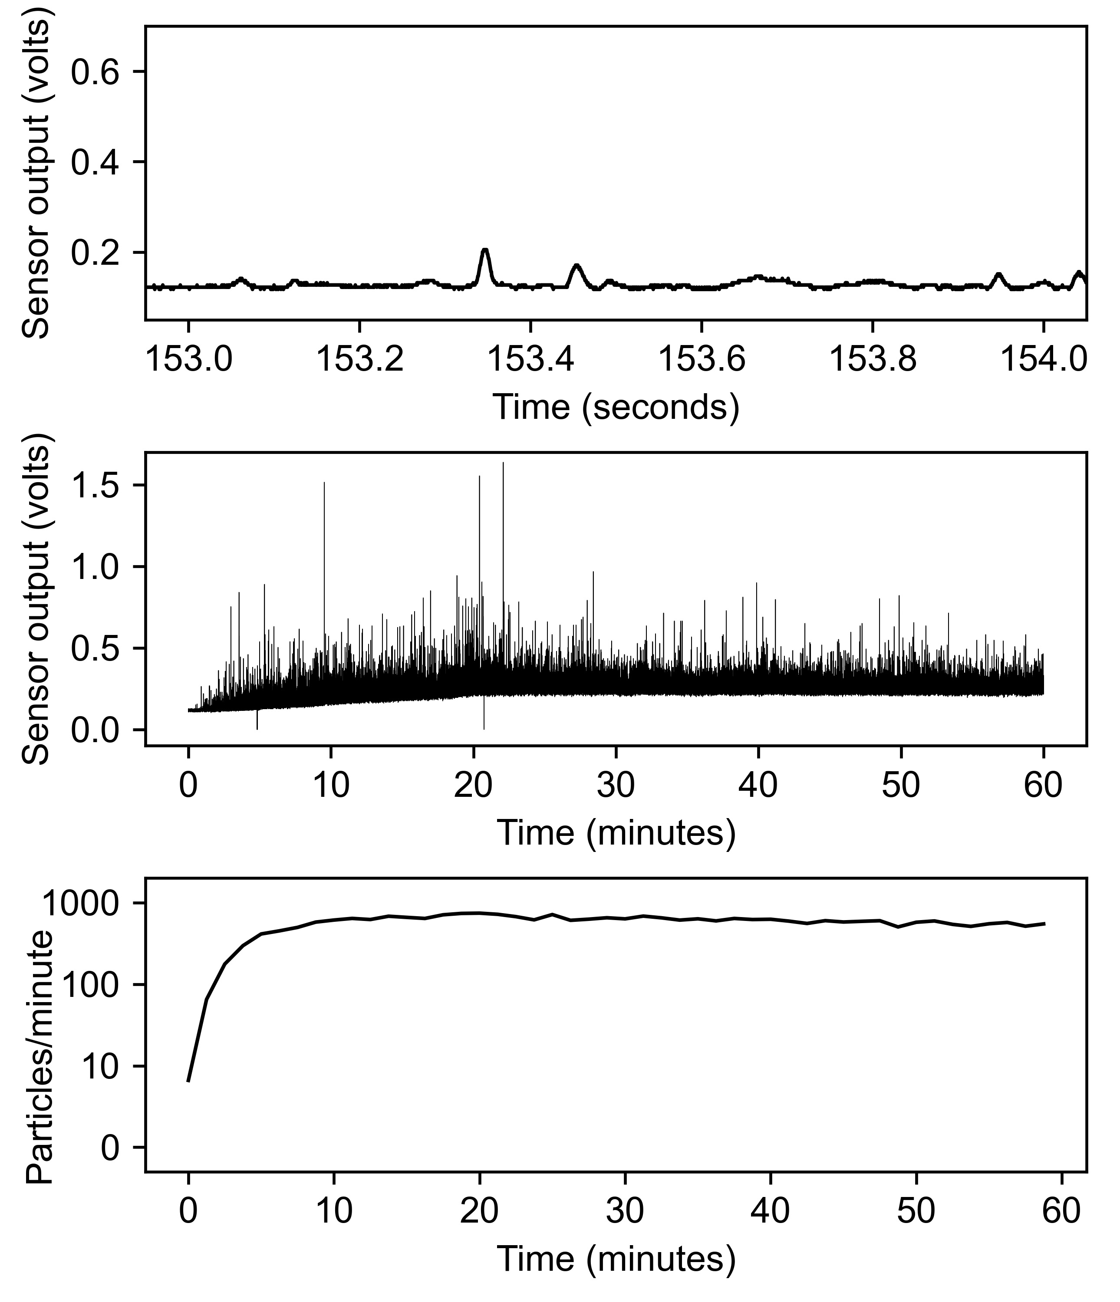
data/variety/Multivitamin/20241118T130146_multivitamin_one_a_day.json.gz.png
