groverlab/disintegration-fingerprinting/data/variety/Nabumetone/20241119T061634_nabumetone.json.gz.png

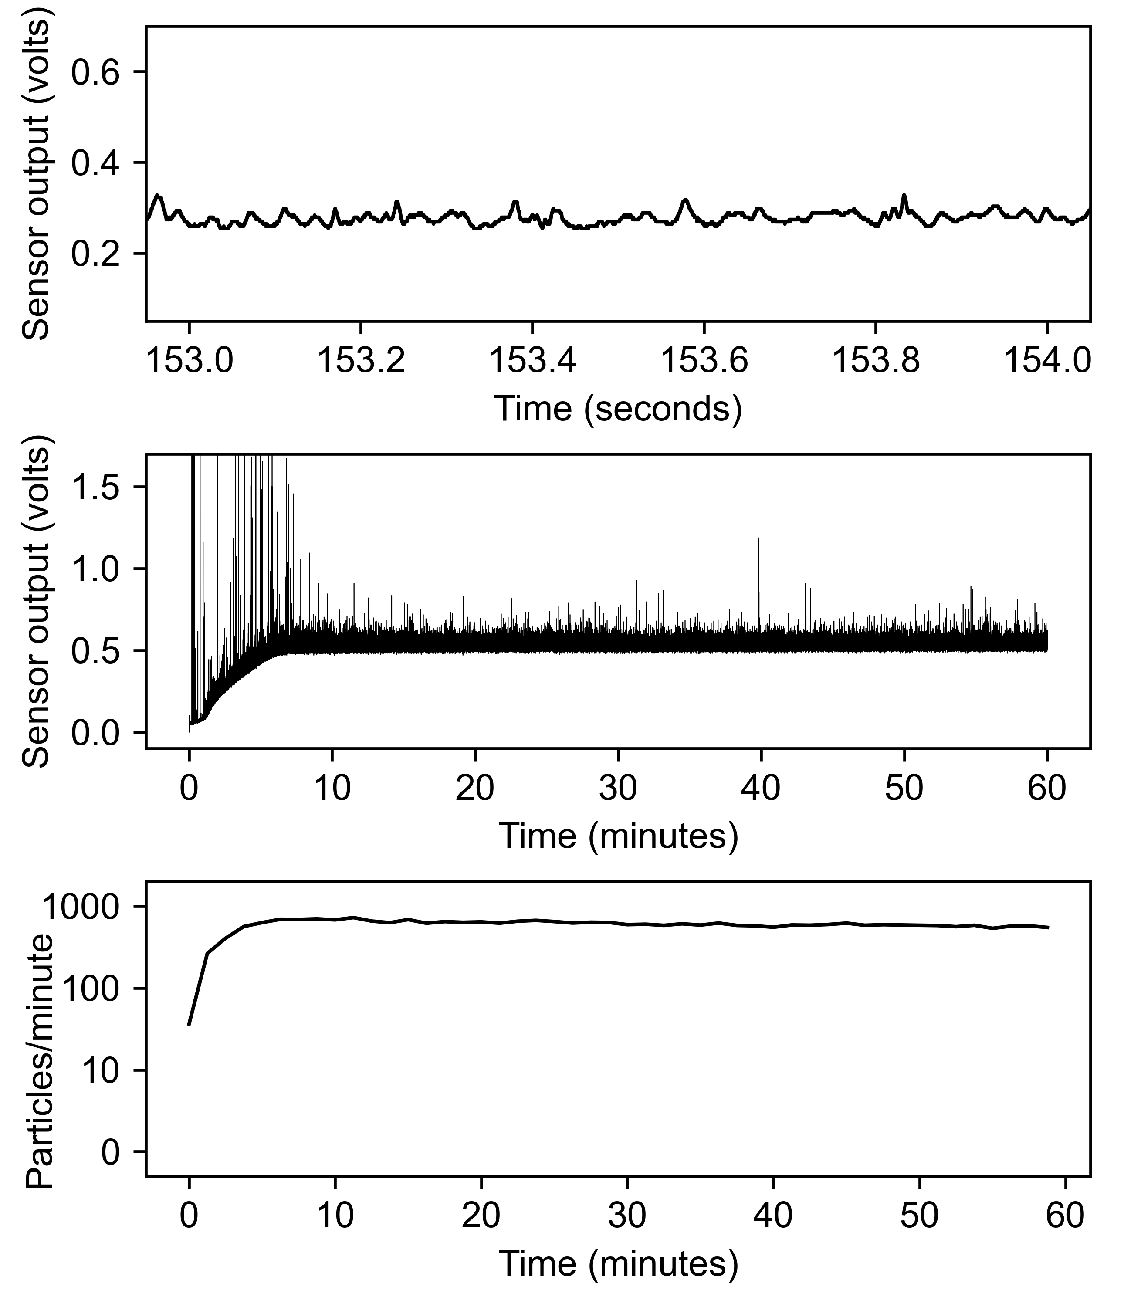
data/variety/Nabumetone/20241119T061634_nabumetone.json.gz.png
