groverlab/disintegration-fingerprinting/data/variety/Nabumetone/20241119T072652_nabumetone.json.gz.png

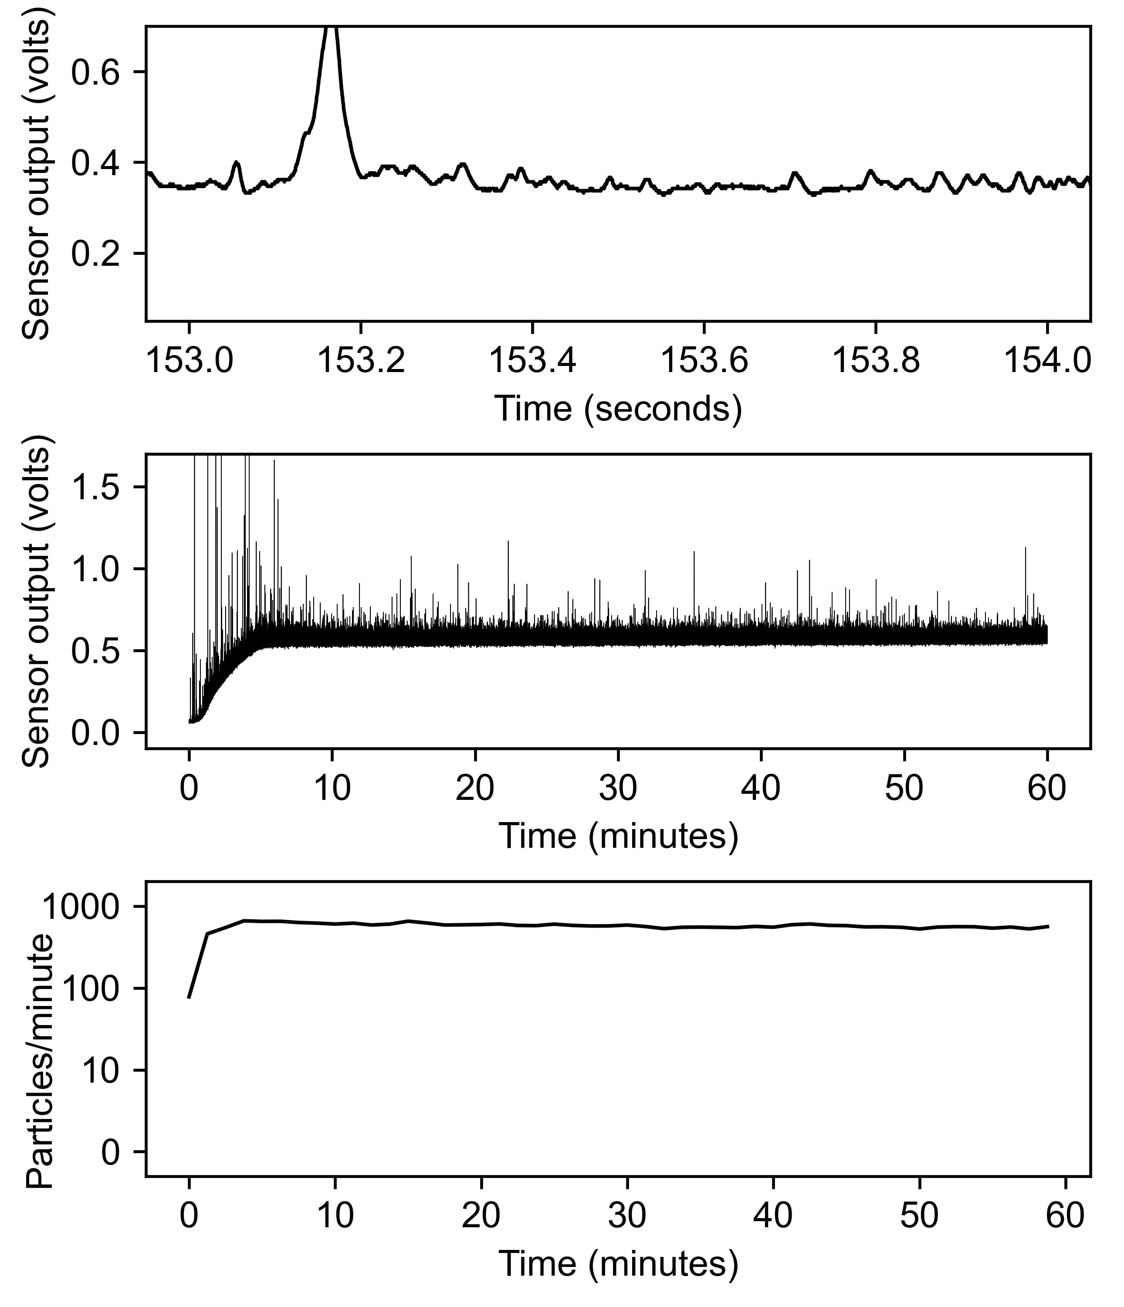
data/variety/Nabumetone/20241119T072652_nabumetone.json.gz.png
