groverlab/disintegration-fingerprinting/data/variety/Nabumetone/20241119T083335_nabumetone.json.gz.png

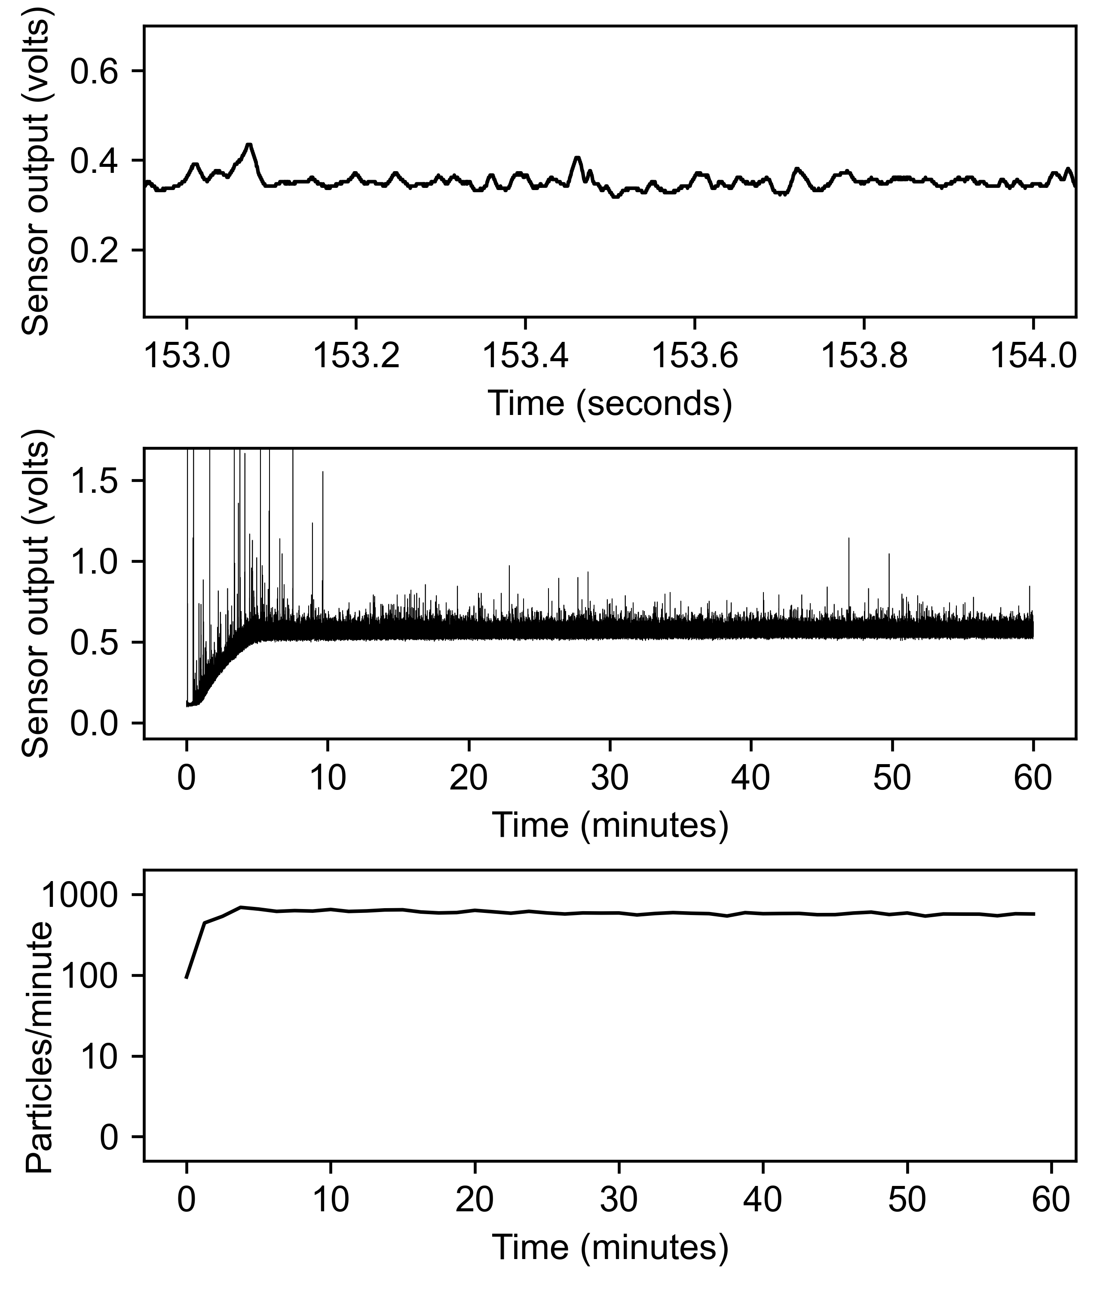
data/variety/Nabumetone/20241119T083335_nabumetone.json.gz.png
