groverlab/disintegration-fingerprinting/data/variety/Ondansetron/20250409T094032_ondansetron.json.gz.png

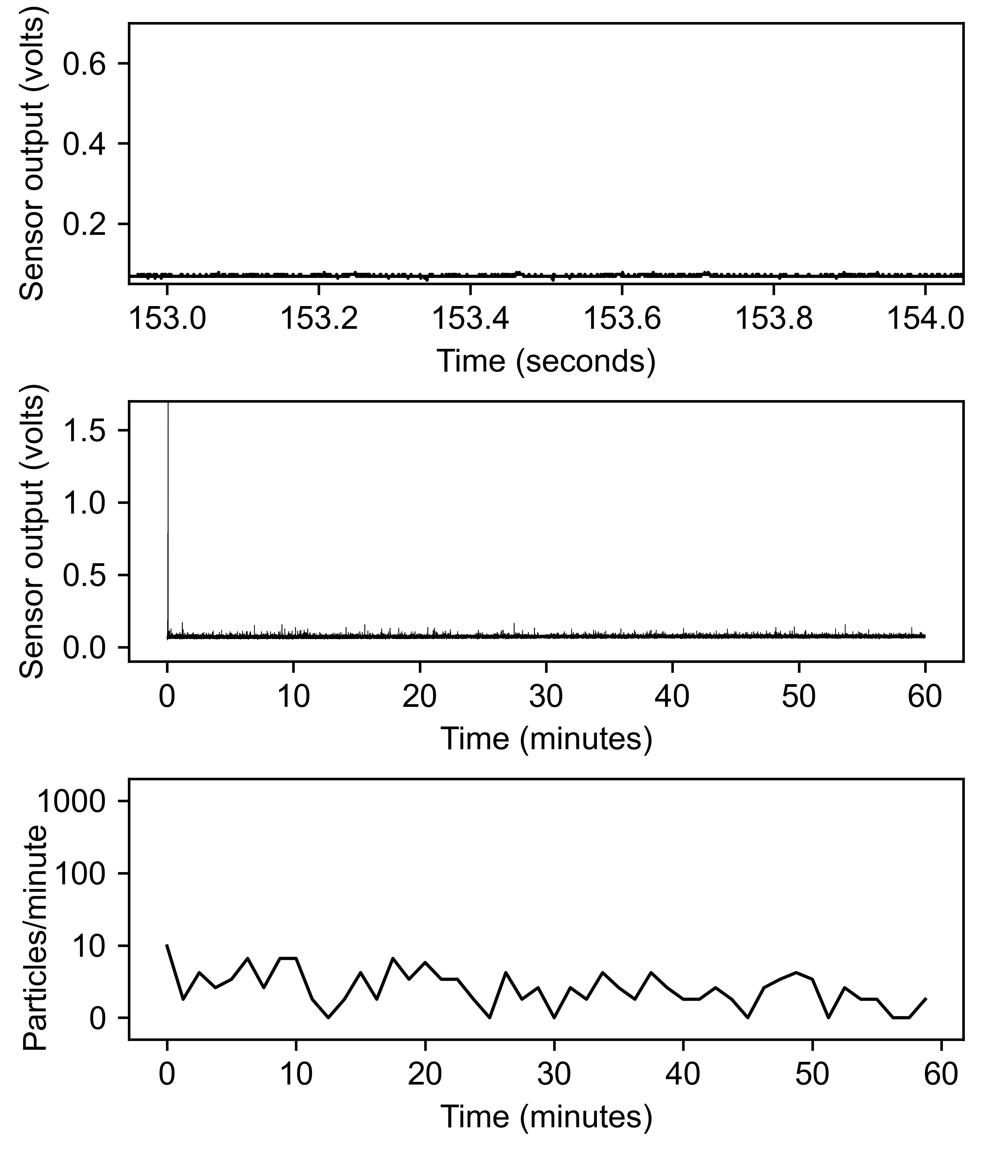
data/variety/Ondansetron/20250409T094032_ondansetron.json.gz.png
