groverlab/disintegration-fingerprinting/data/variety/Powdered milk/20241211T115744_powdered_milk.json.gz.png

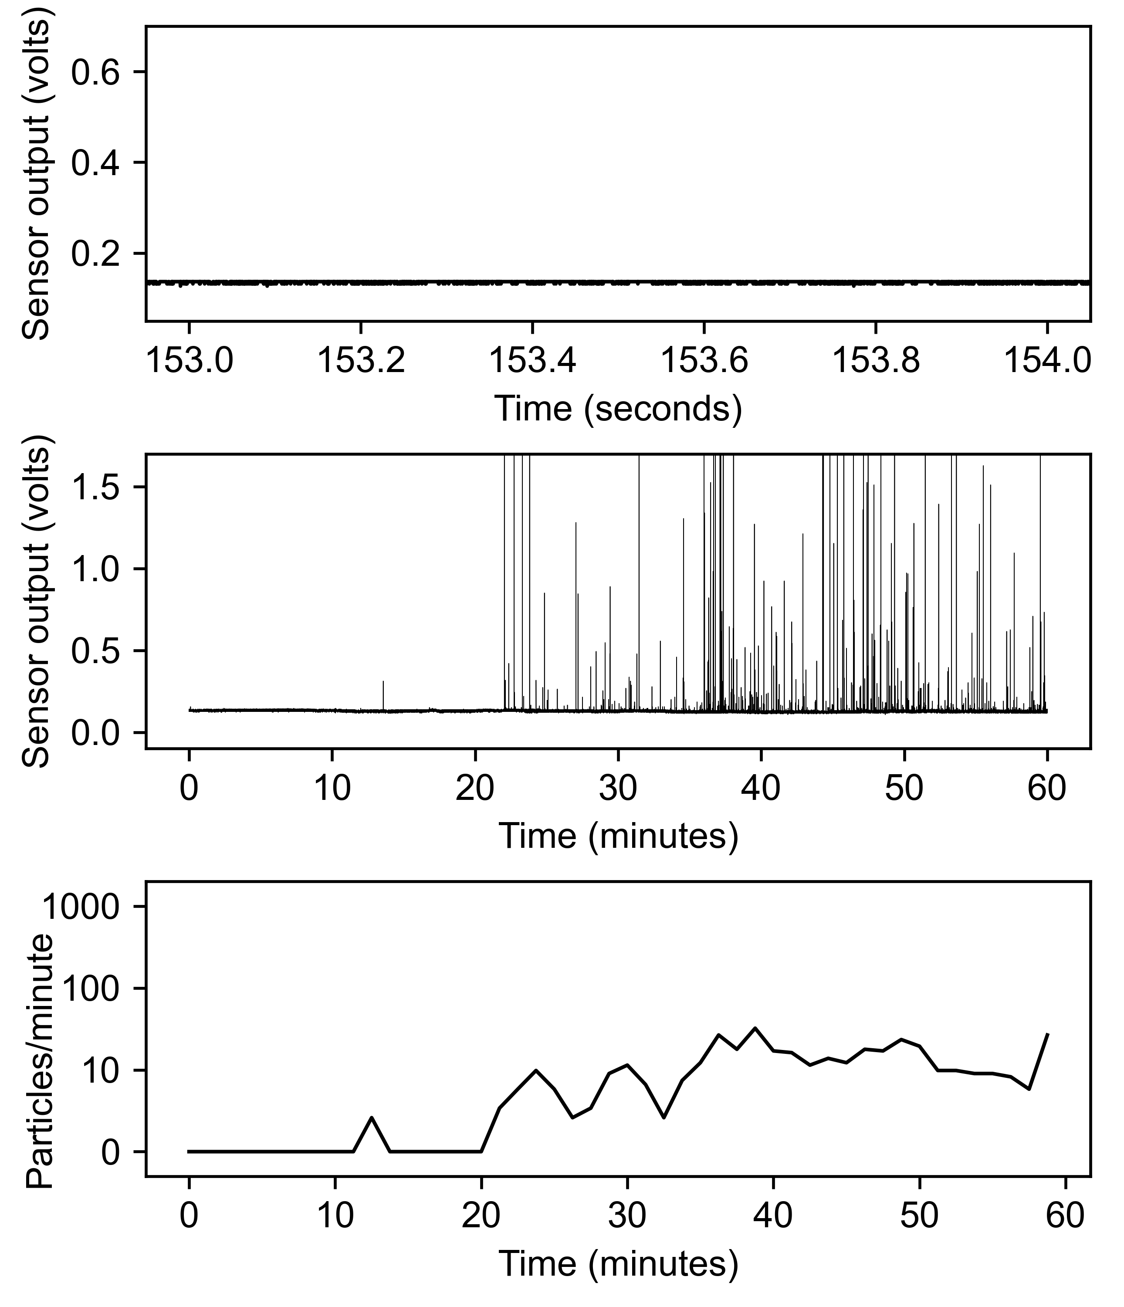
data/variety/Powdered milk/20241211T115744_powdered_milk.json.gz.png
