groverlab/disintegration-fingerprinting/data/variety/Powdered milk/20241211T131559_powdered_milk.json.gz.png

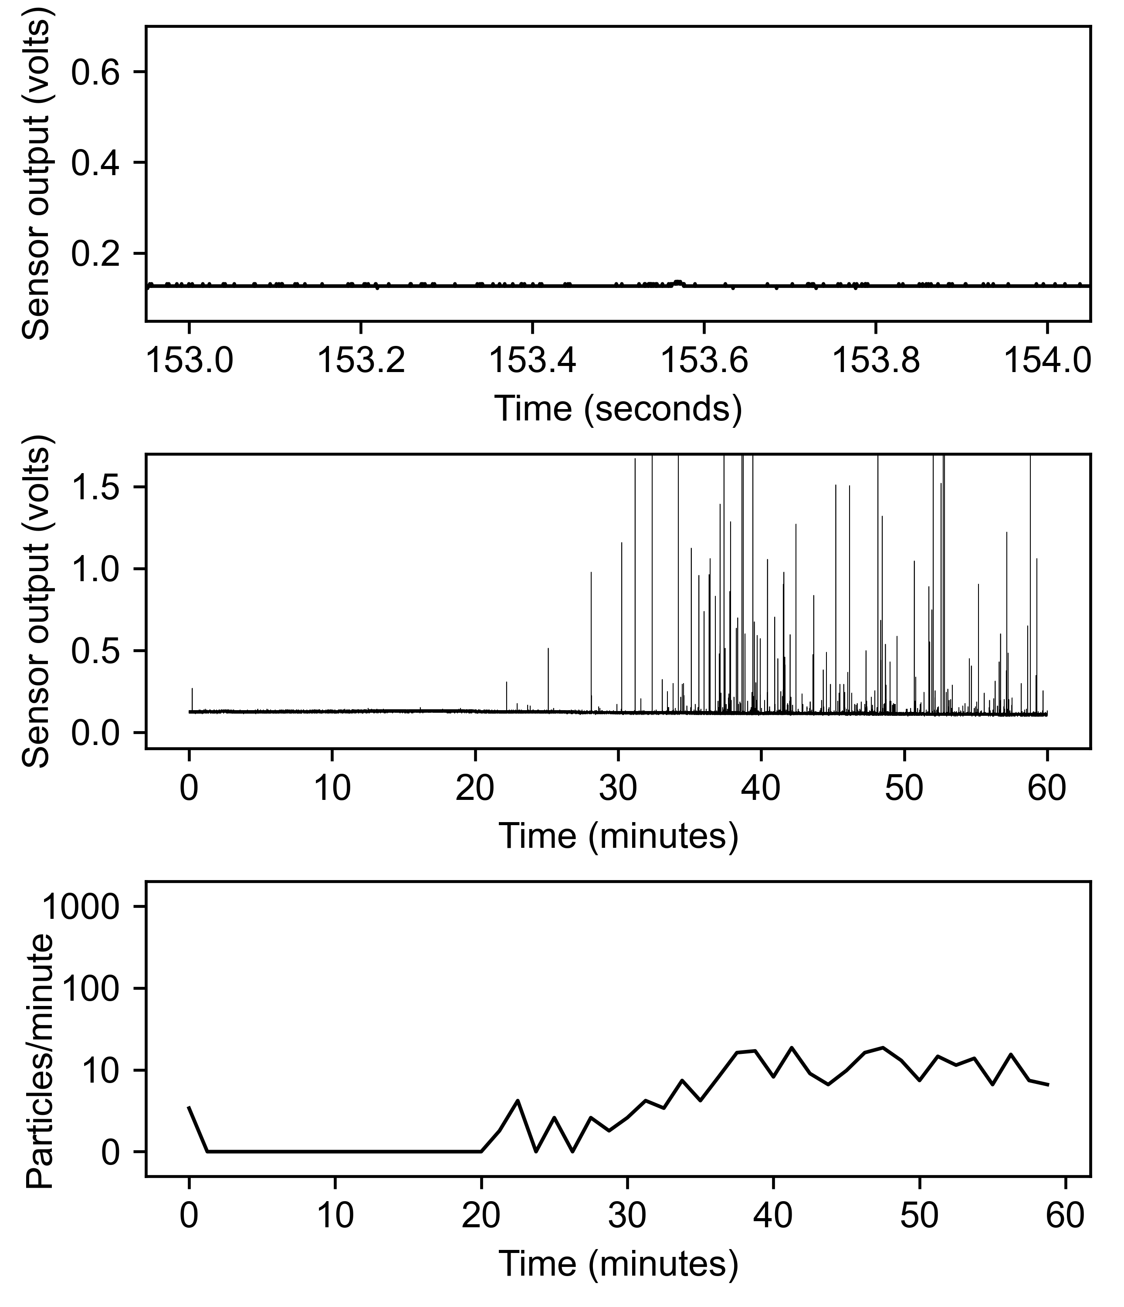
data/variety/Powdered milk/20241211T131559_powdered_milk.json.gz.png
