groverlab/disintegration-fingerprinting/data/variety/Powdered milk/20241212T141429_powdered_milk.json.gz.png

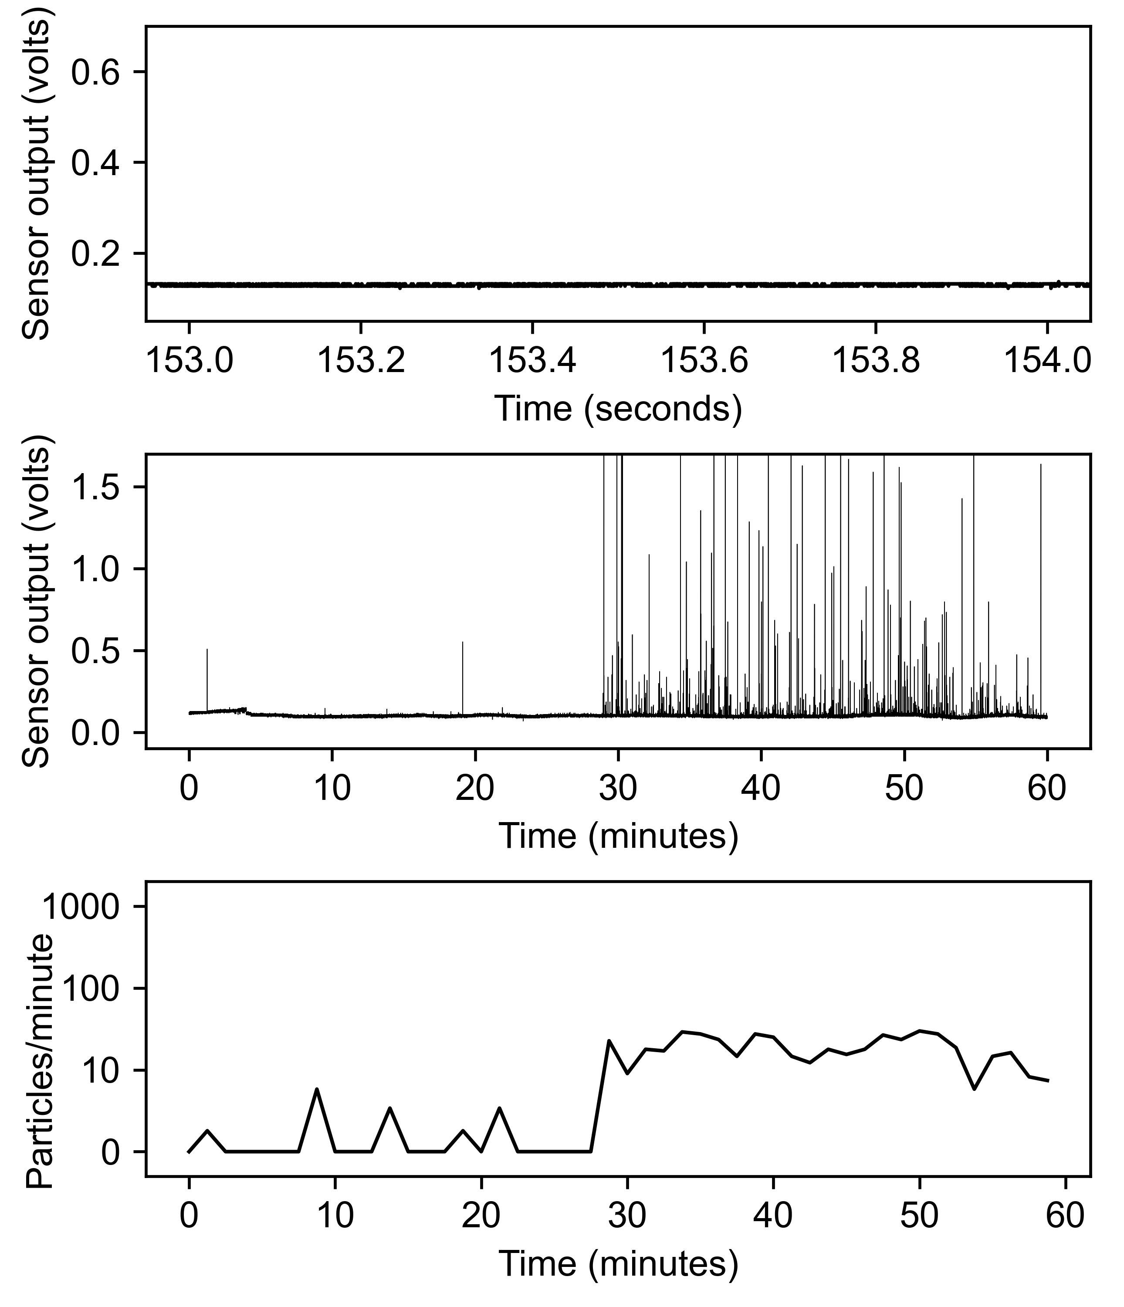
data/variety/Powdered milk/20241212T141429_powdered_milk.json.gz.png
