groverlab/disintegration-fingerprinting/data/variety/Pseudoephedrine ext. rel./20241210T081932_sudafed_sinus.json.gz.png

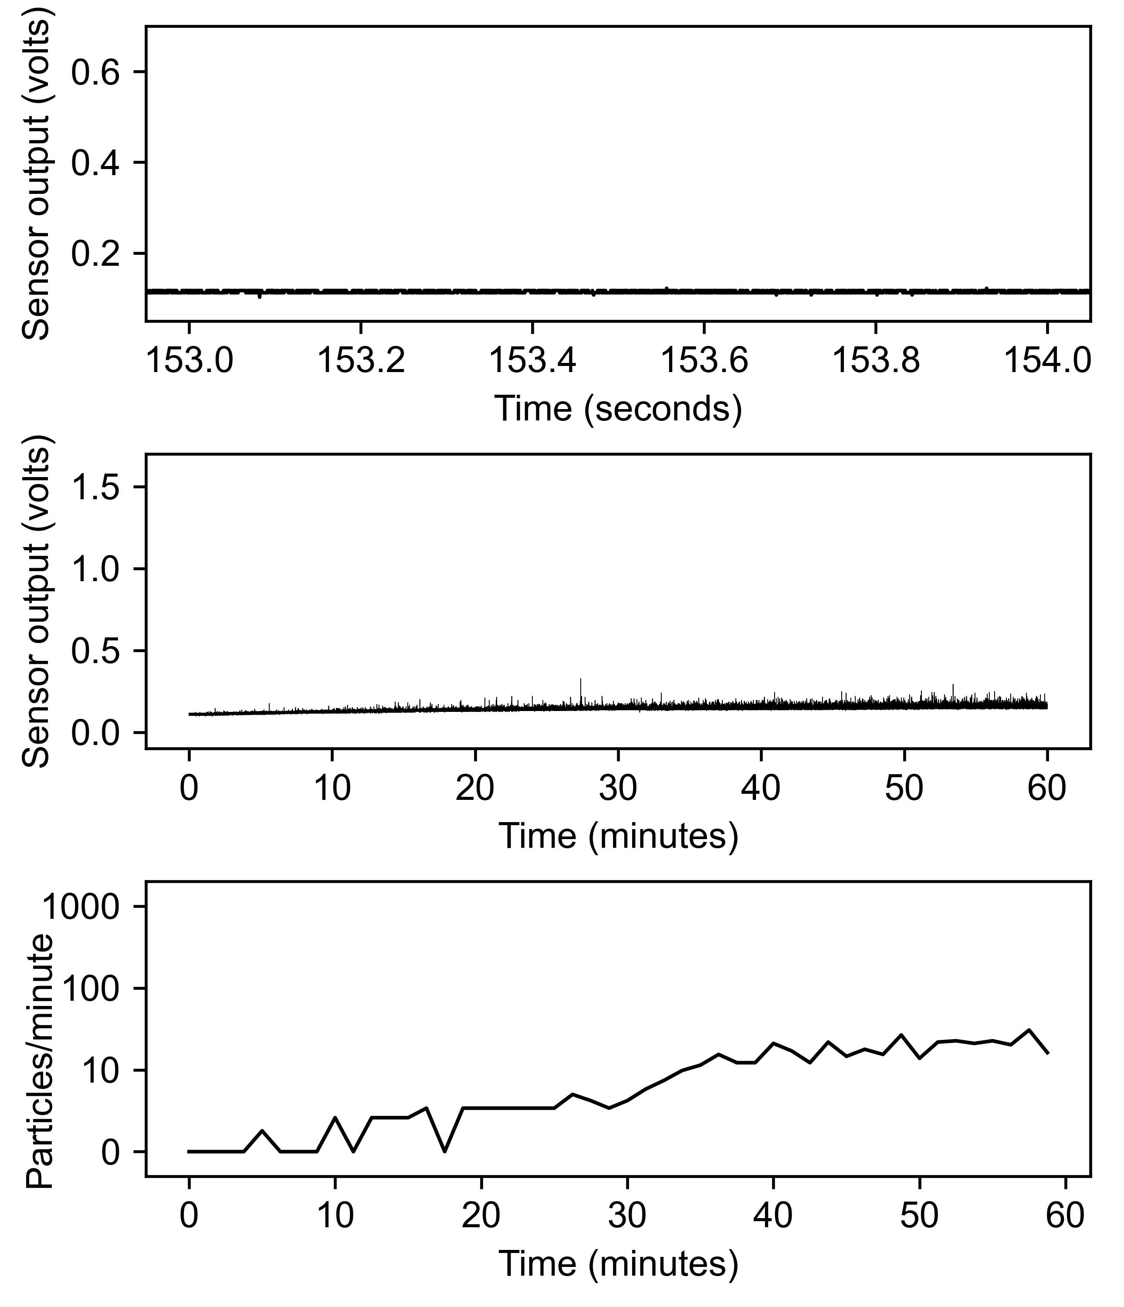
data/variety/Pseudoephedrine ext. rel./20241210T081932_sudafed_sinus.json.gz.png
