groverlab/disintegration-fingerprinting/data/variety/Pseudoephedrine/20241117T083614_pseudoephedrine_generic.json.gz.png

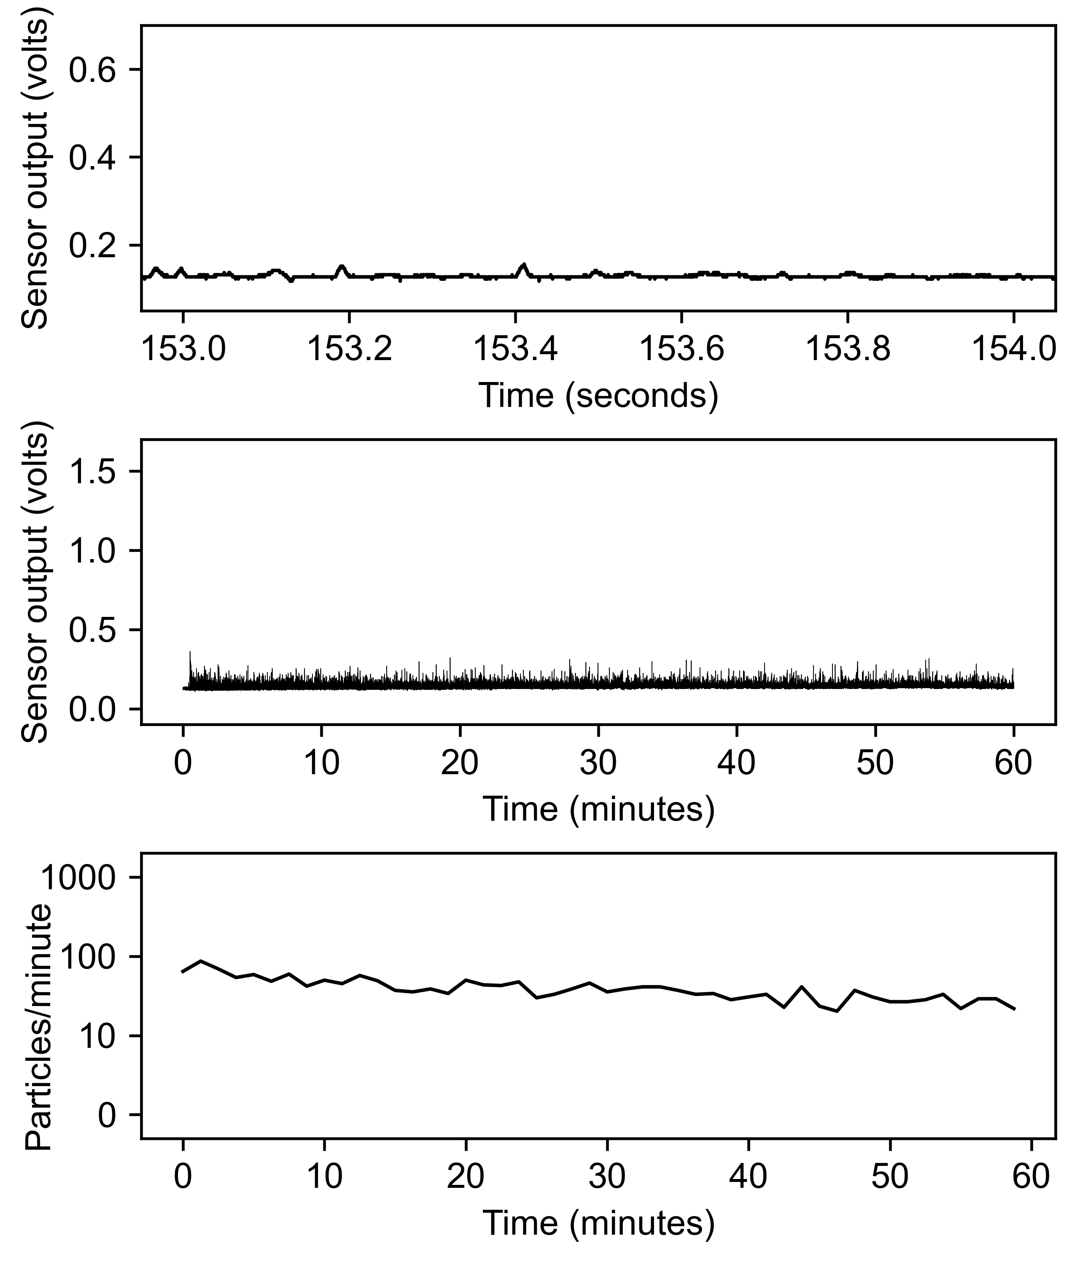
data/variety/Pseudoephedrine/20241117T083614_pseudoephedrine_generic.json.gz.png
