groverlab/disintegration-fingerprinting/data/variety/Tramadol/20241120T094124_tramadol.json.gz.png

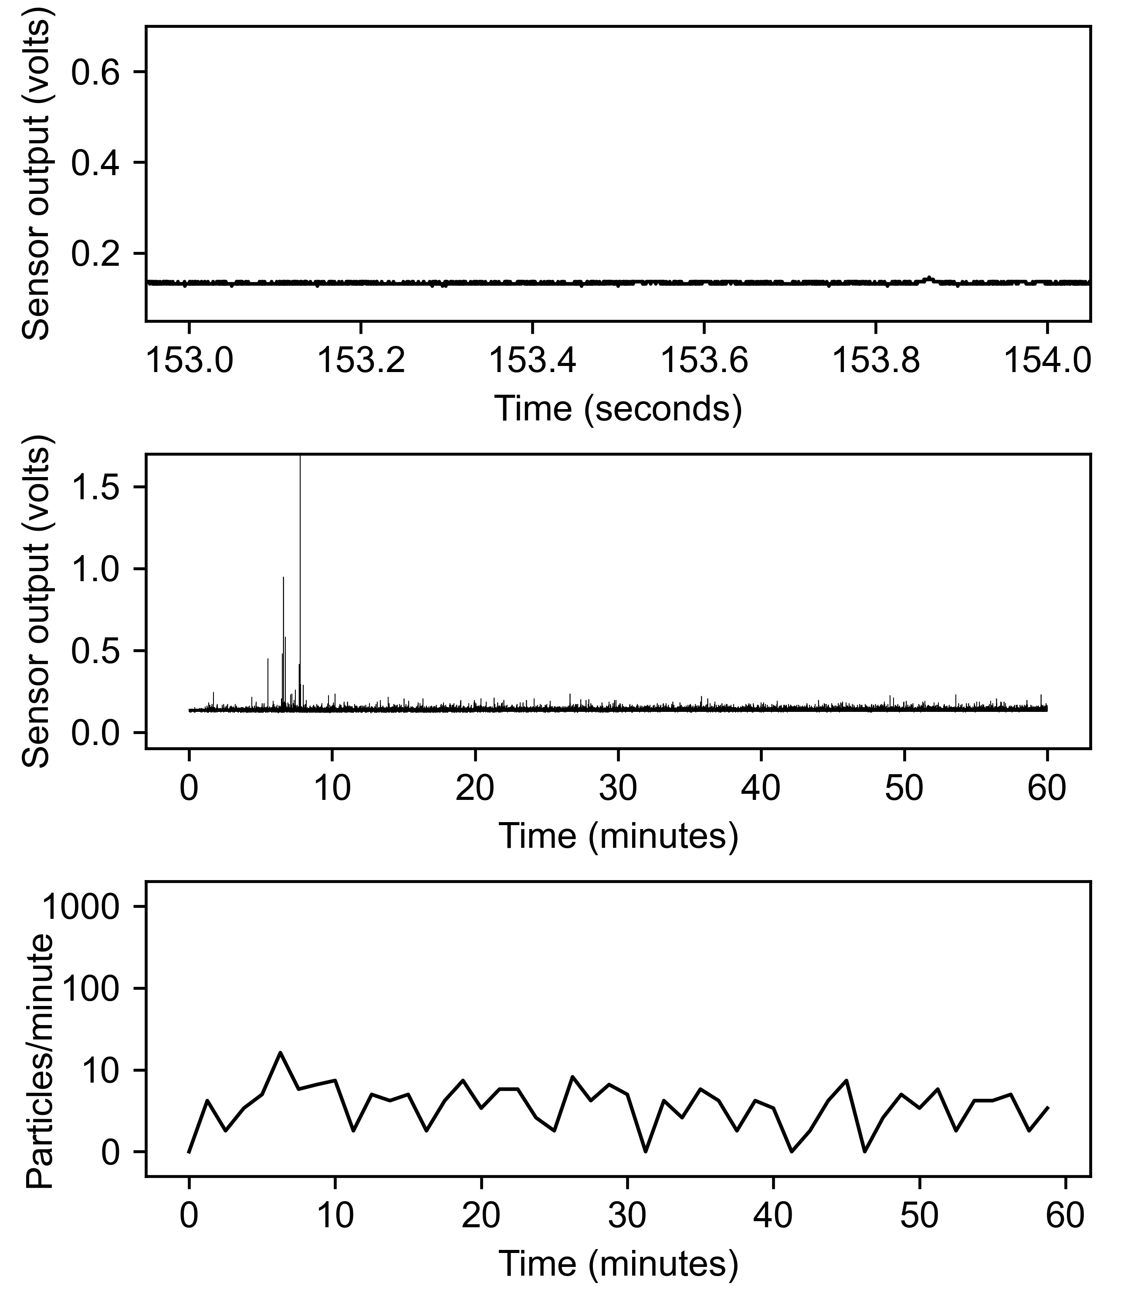
data/variety/Tramadol/20241120T094124_tramadol.json.gz.png
