groverlab/disintegration-fingerprinting/data/variety/Zinc gluconate/20241118T190508_zinc_50mg.json.gz.png

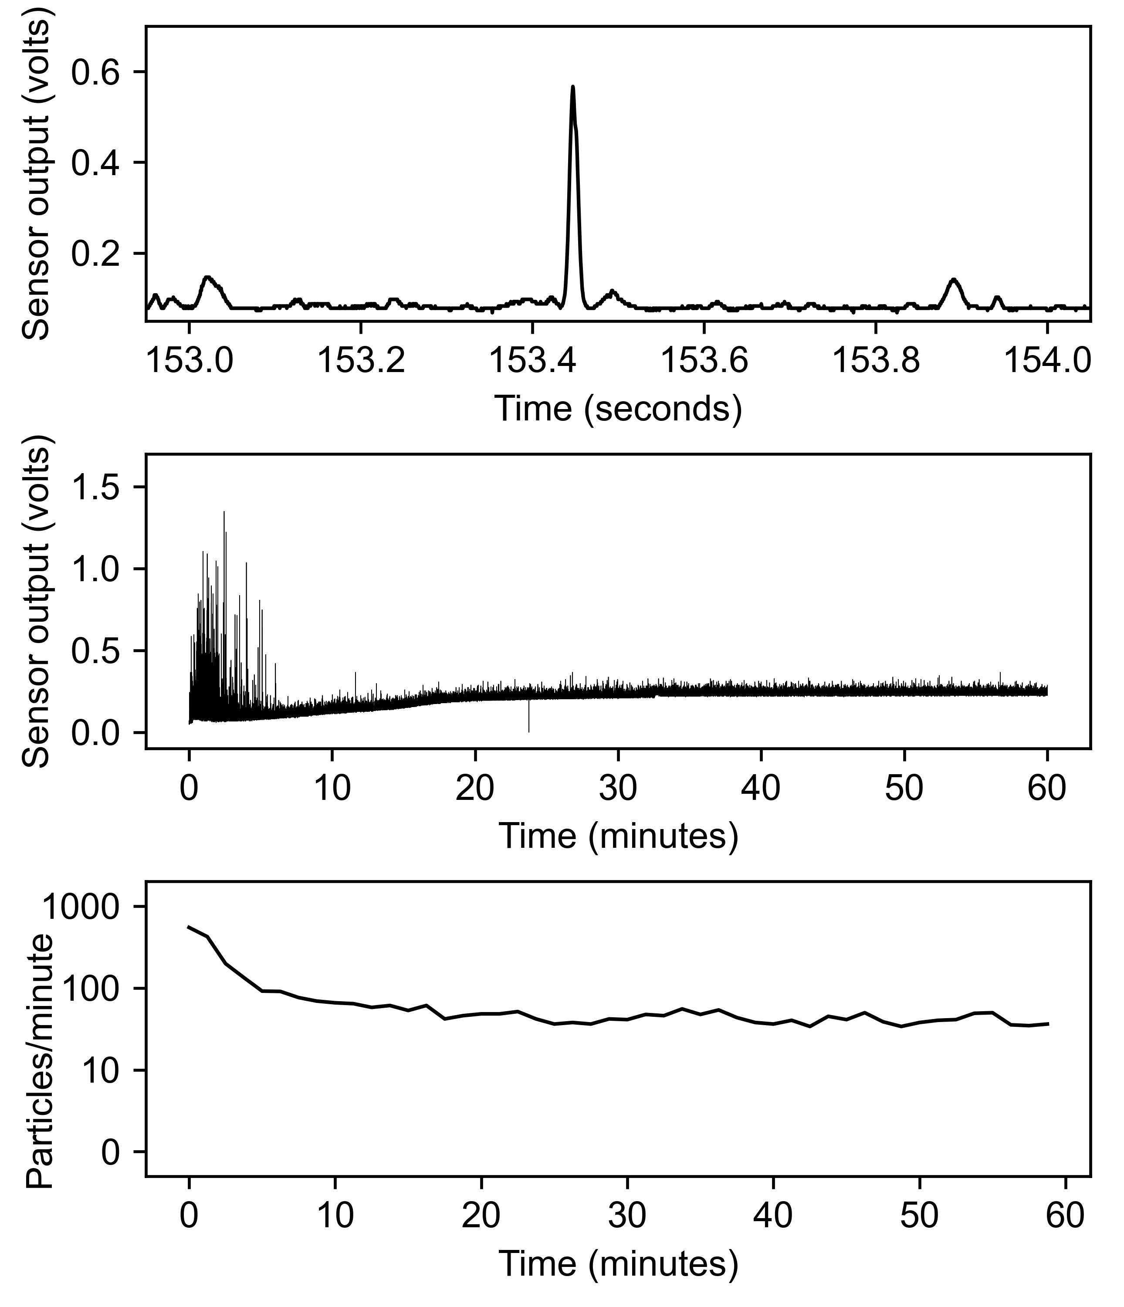
data/variety/Zinc gluconate/20241118T190508_zinc_50mg.json.gz.png
