groverlab/disintegration-fingerprinting/data/variety/Zinc gluconate/20241118T211945_zinc_50mg.json.gz.png

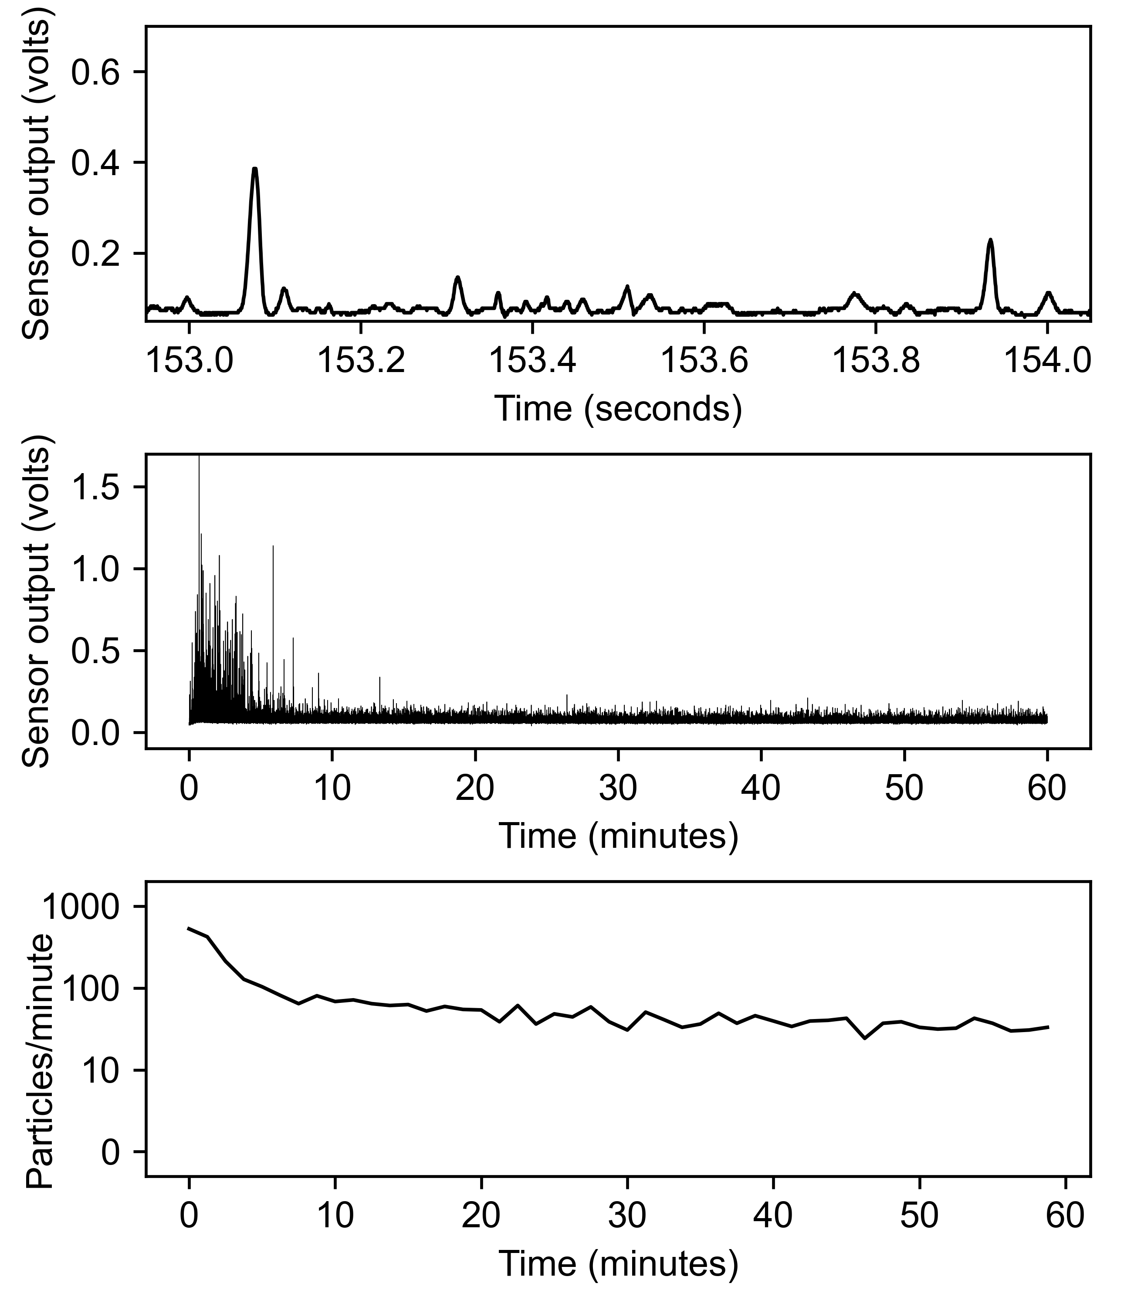
data/variety/Zinc gluconate/20241118T211945_zinc_50mg.json.gz.png
