groverlab/disintegration-fingerprinting/data/variety_heatmap.png

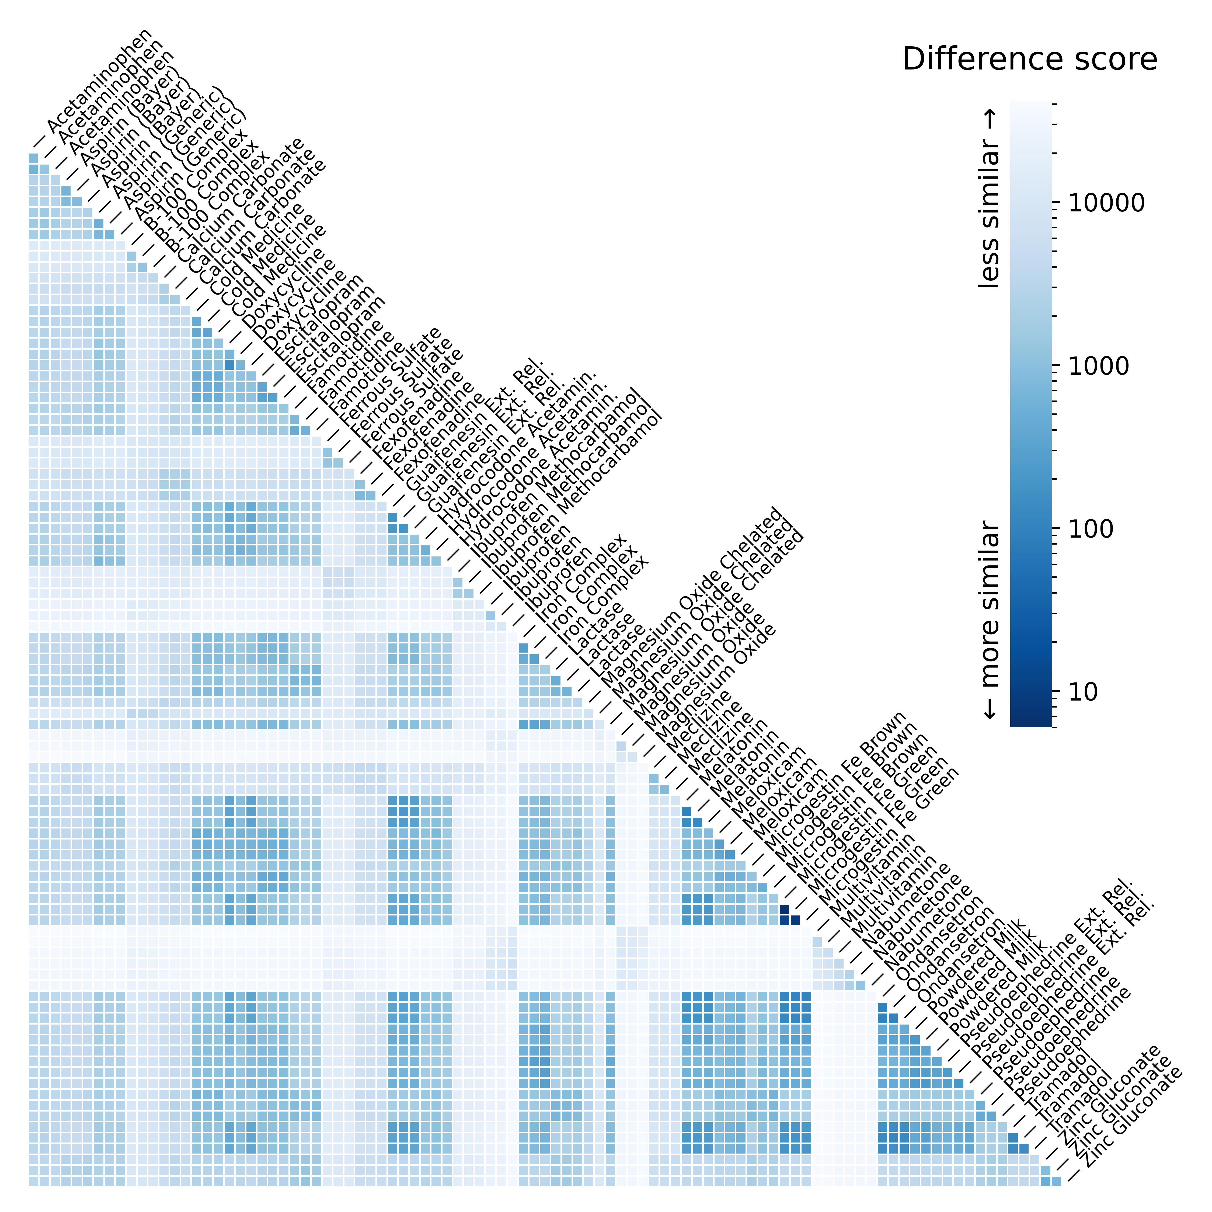
data/variety_heatmap.png
