groverlab/disintegration-fingerprinting/data/variety_significance.png

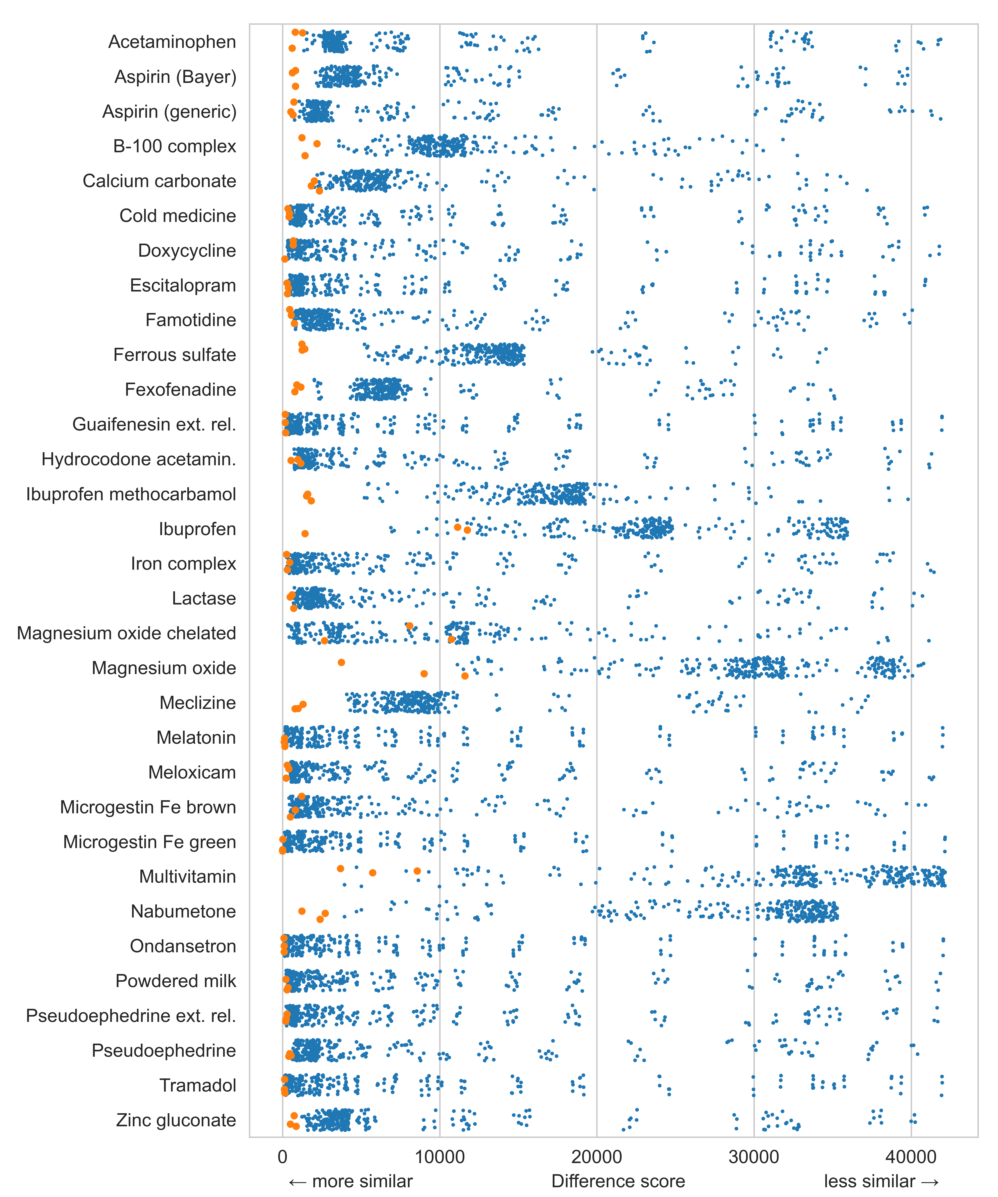
data/variety_significance.png
