groverlab/disintegration-fingerprinting/PCB/ODF_Board.pdf

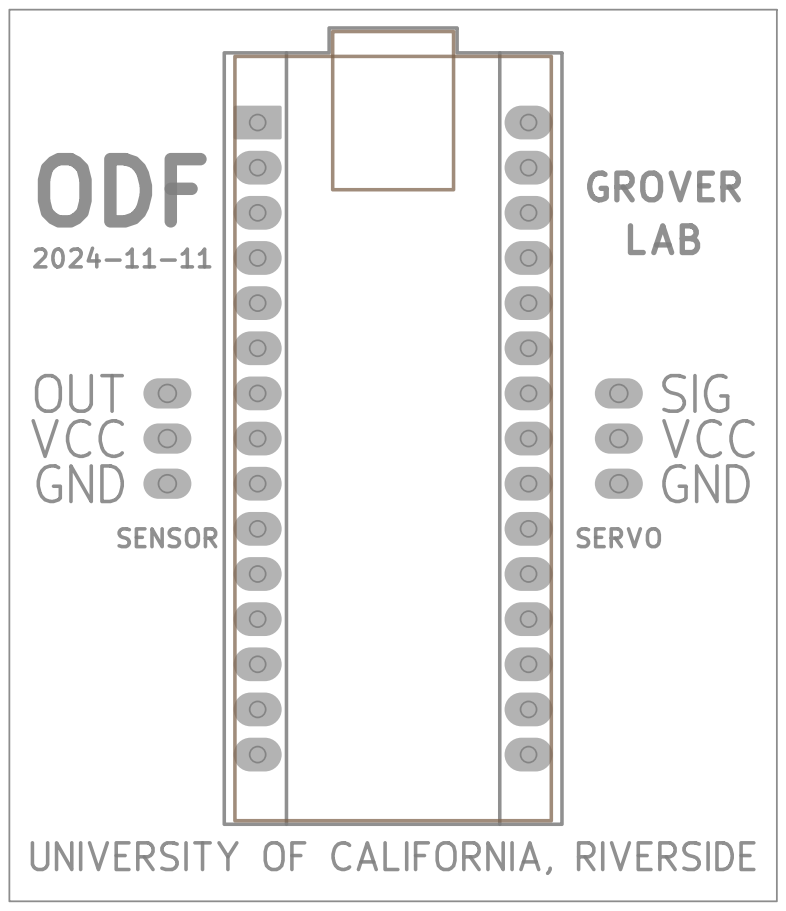
[picture p163: page 1]

UNIVERSITY OF CALIFORNIA, RIVERSIDE

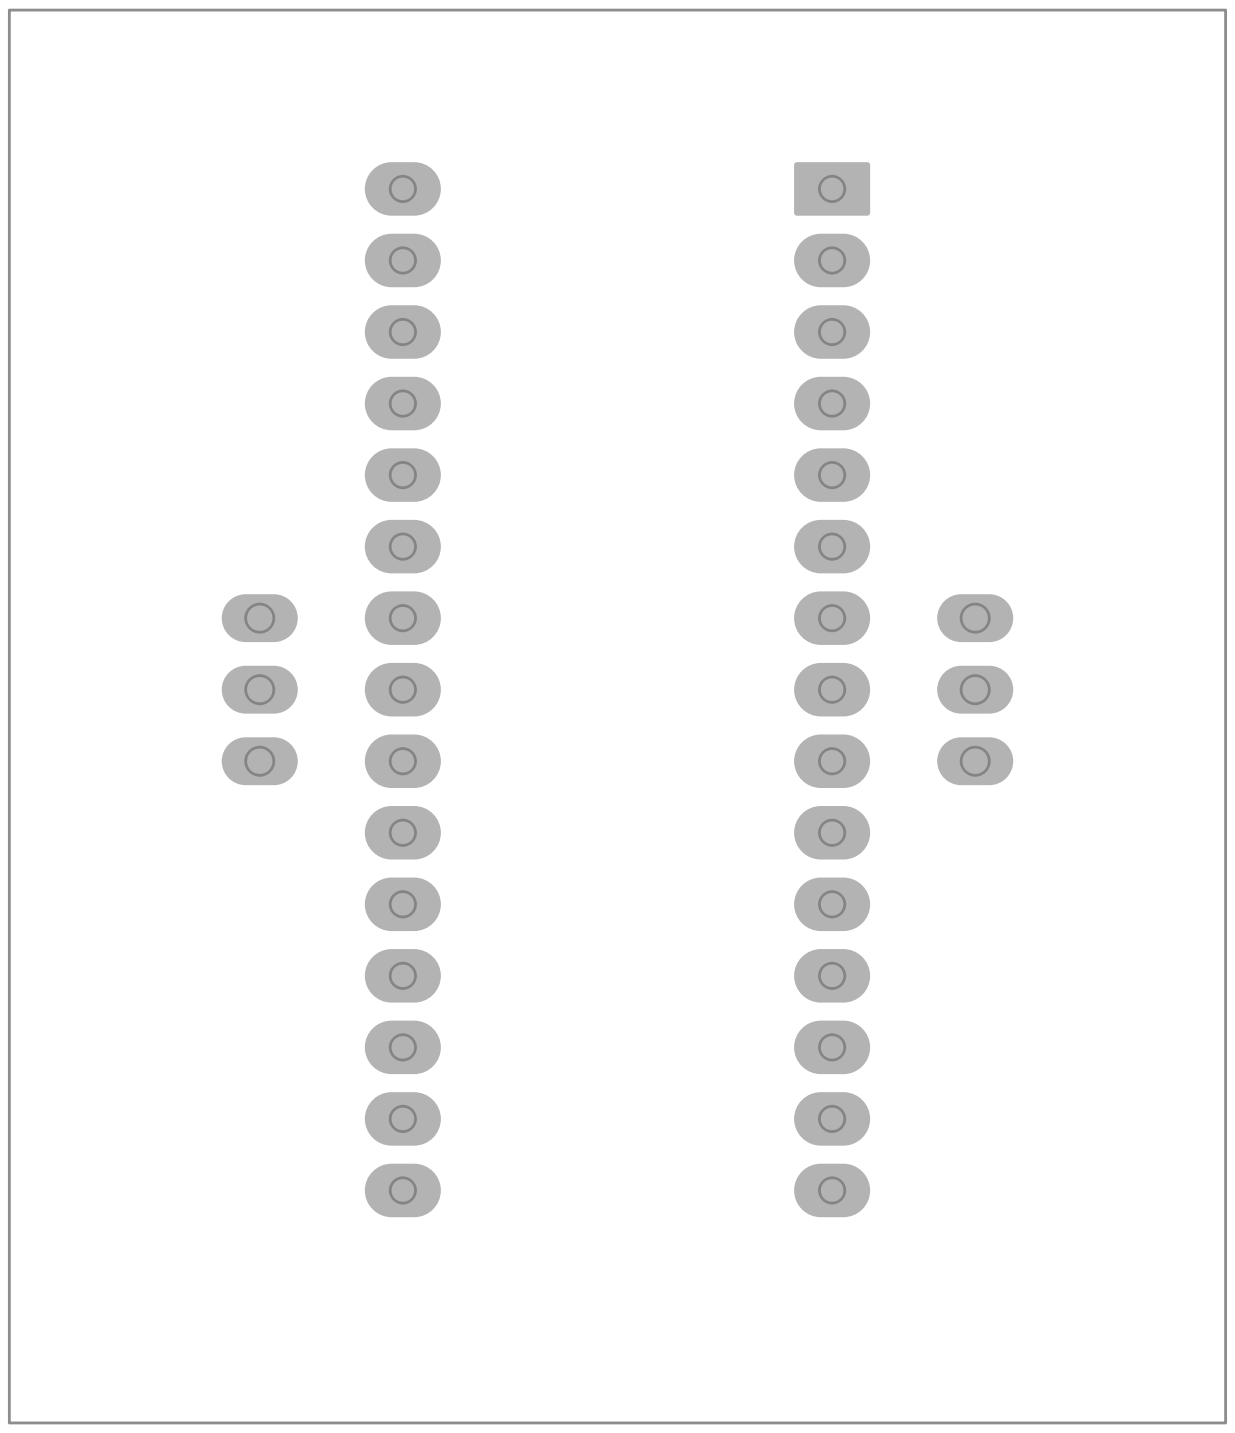
[picture p164: page 2]
