groverlab/disintegration-fingerprinting/data/bayer_tylenol/101 20251124T124538_T16one TCANADA.json.gz.pdf

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

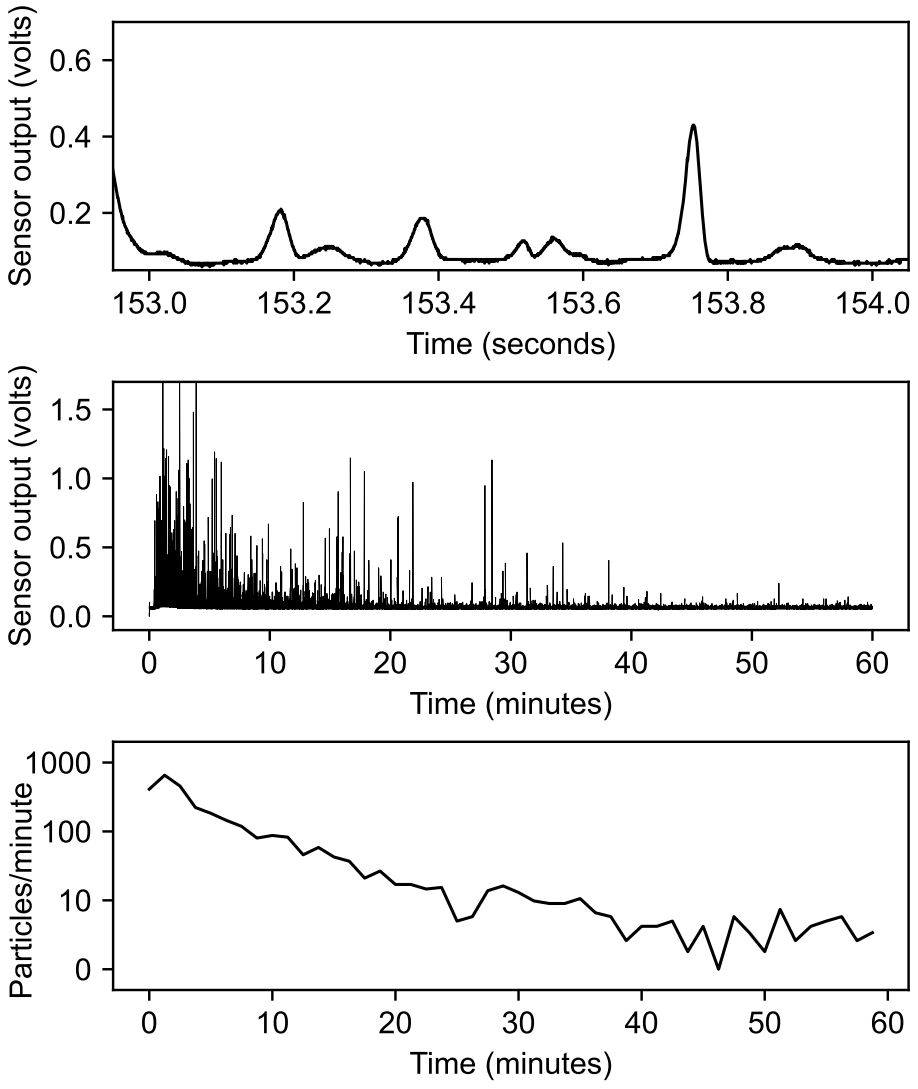
[picture p165: page 1]
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
