groverlab/disintegration-fingerprinting/data/bayer_tylenol/102 20251113T170126_T02one TRT.json.gz.pdf

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

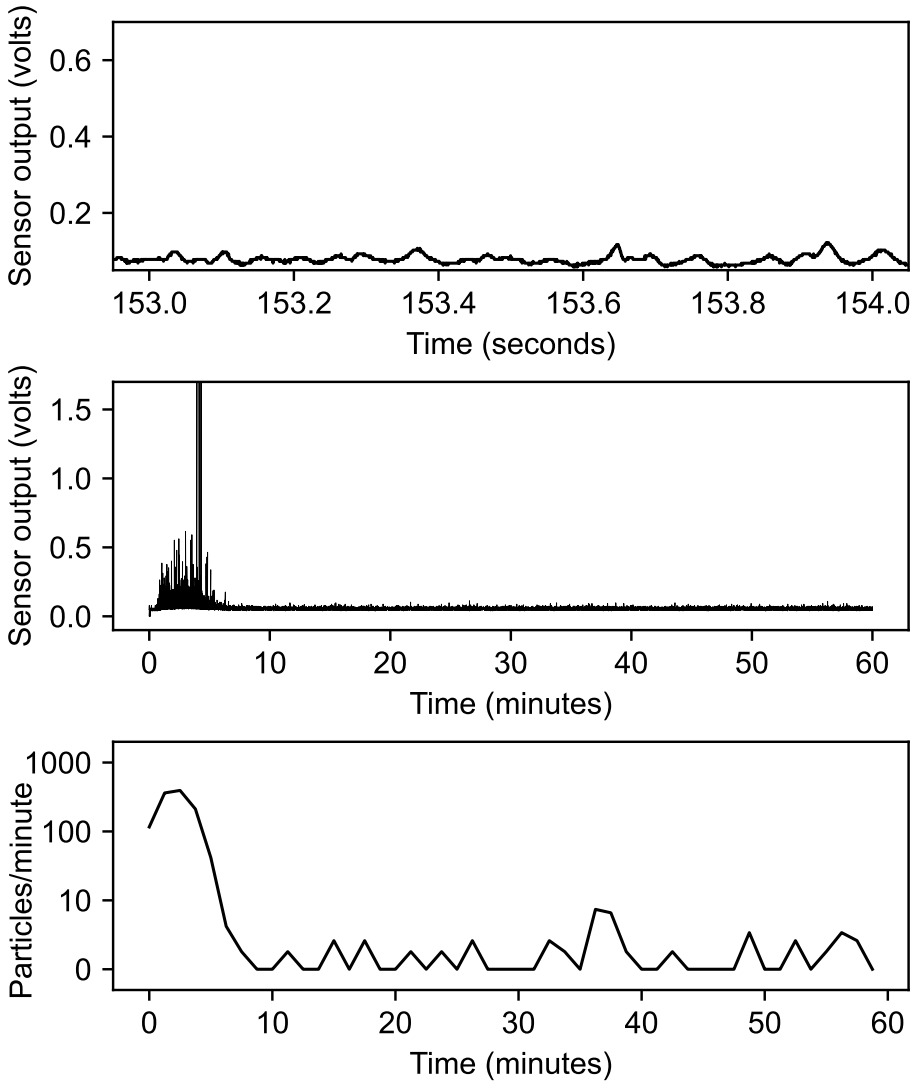
[picture p166: page 1]
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
