groverlab/disintegration-fingerprinting/data/bayer_tylenol/103 20251124T112431_T15one TRT.json.gz.pdf

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

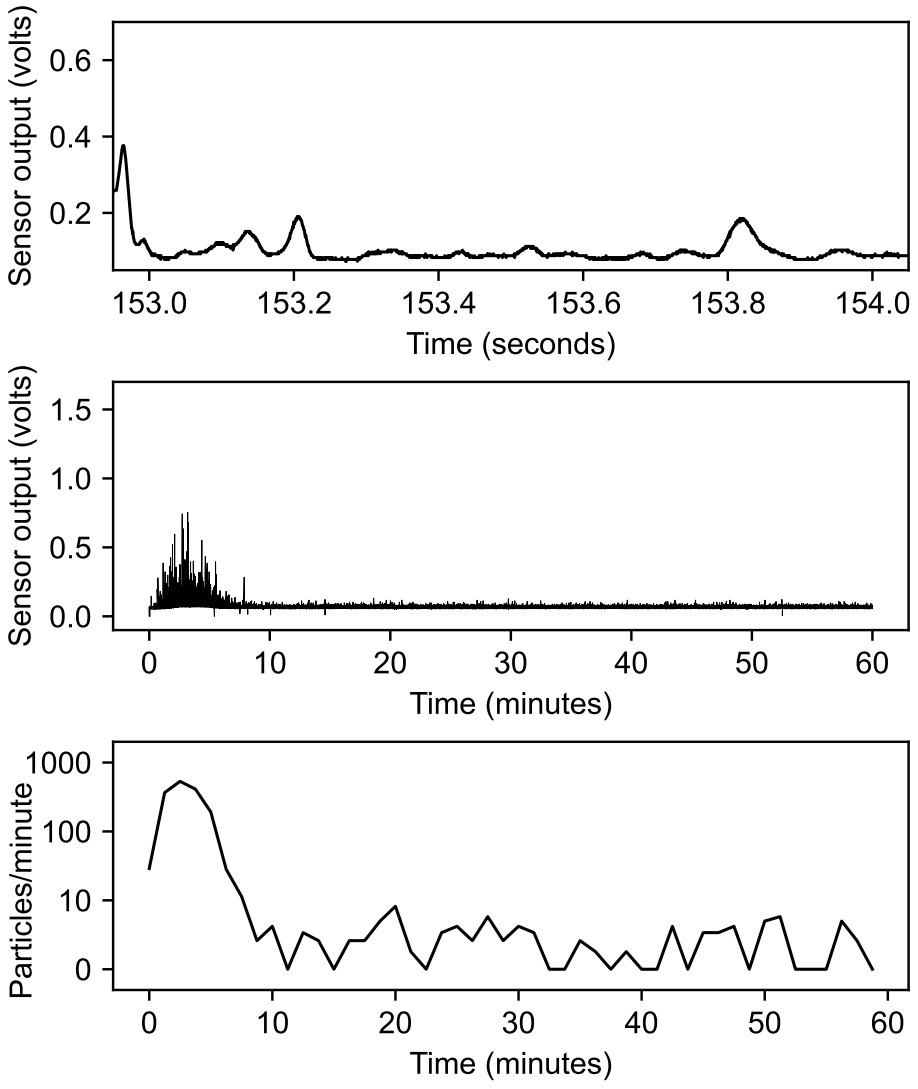
[picture p167: page 1]
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
