groverlab/disintegration-fingerprinting/data/bayer_tylenol/104 20251118T150120_T08one TRT.json.gz.pdf

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

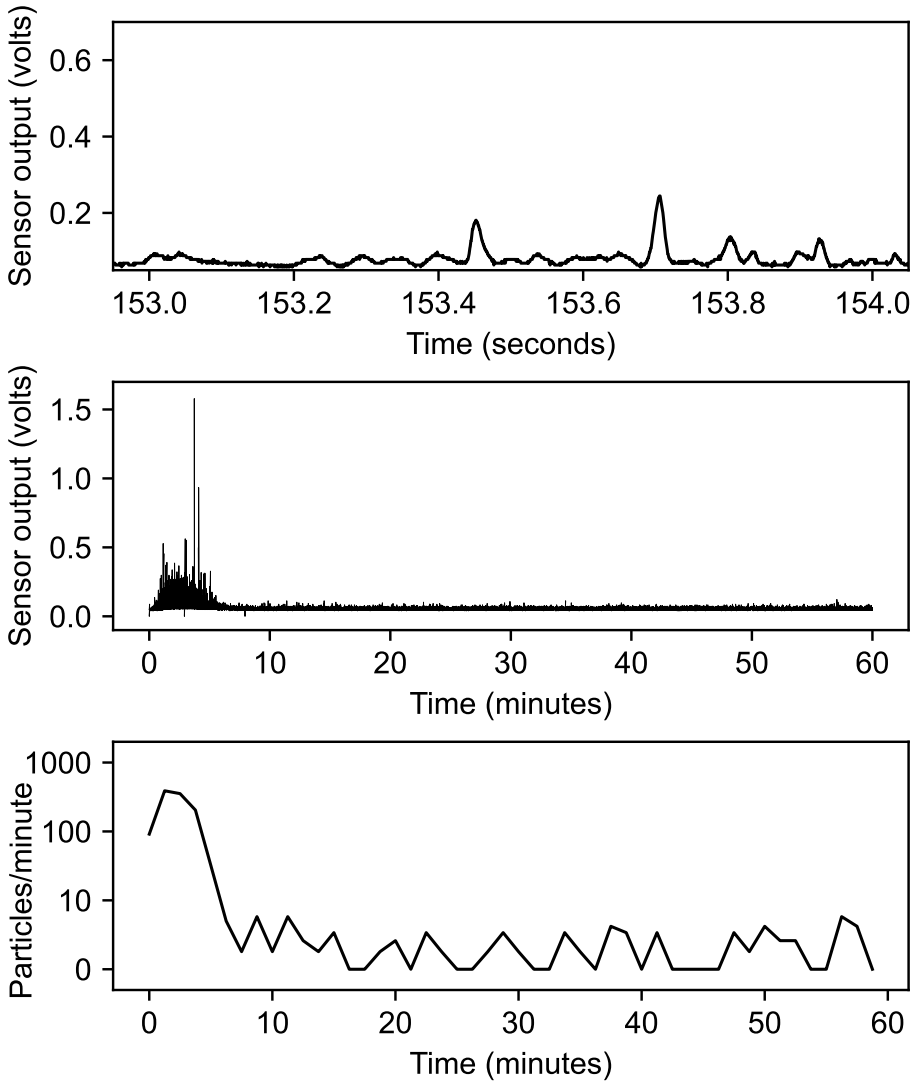
[picture p168: page 1]
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
