groverlab/disintegration-fingerprinting/data/bayer_tylenol/105 20260107T104635_T13two TRT.json.gz.pdf

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

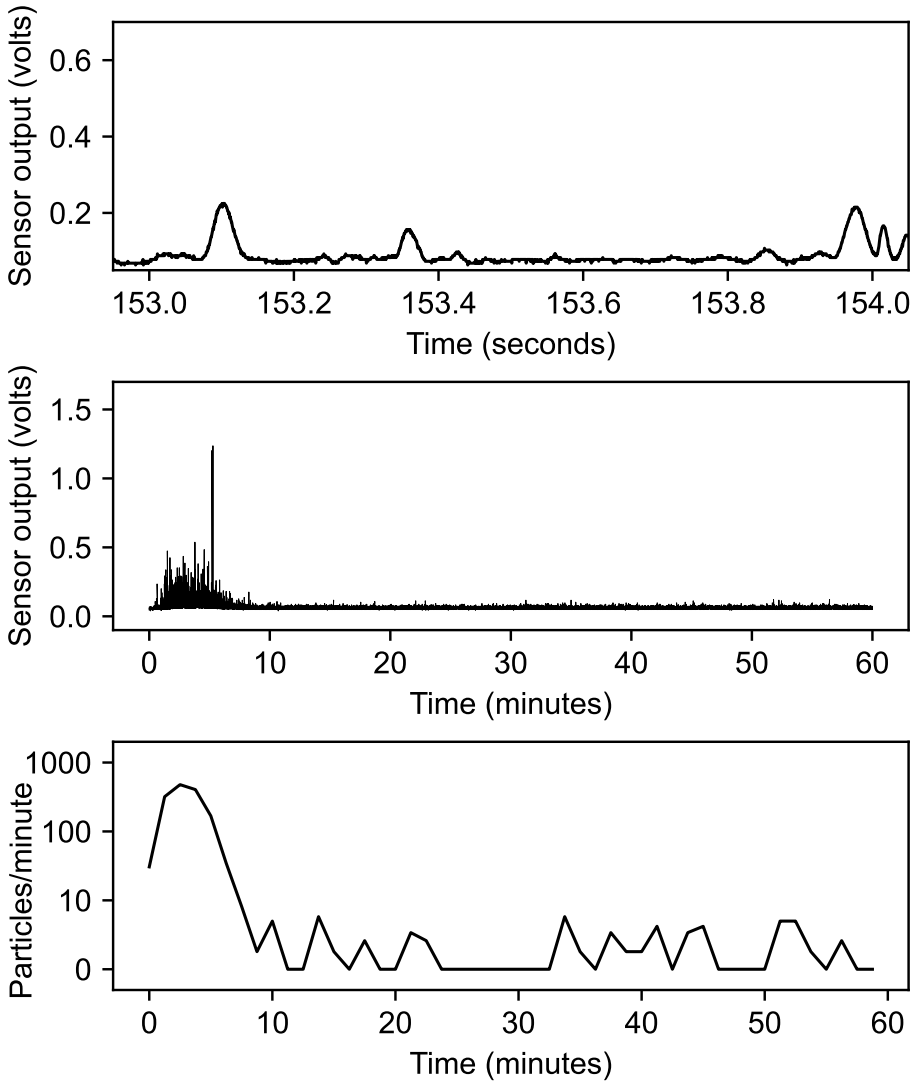
[picture p169: page 1]
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
