groverlab/disintegration-fingerprinting/data/bayer_tylenol/106 20251117T124159_T05one TRT.json.gz.pdf

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

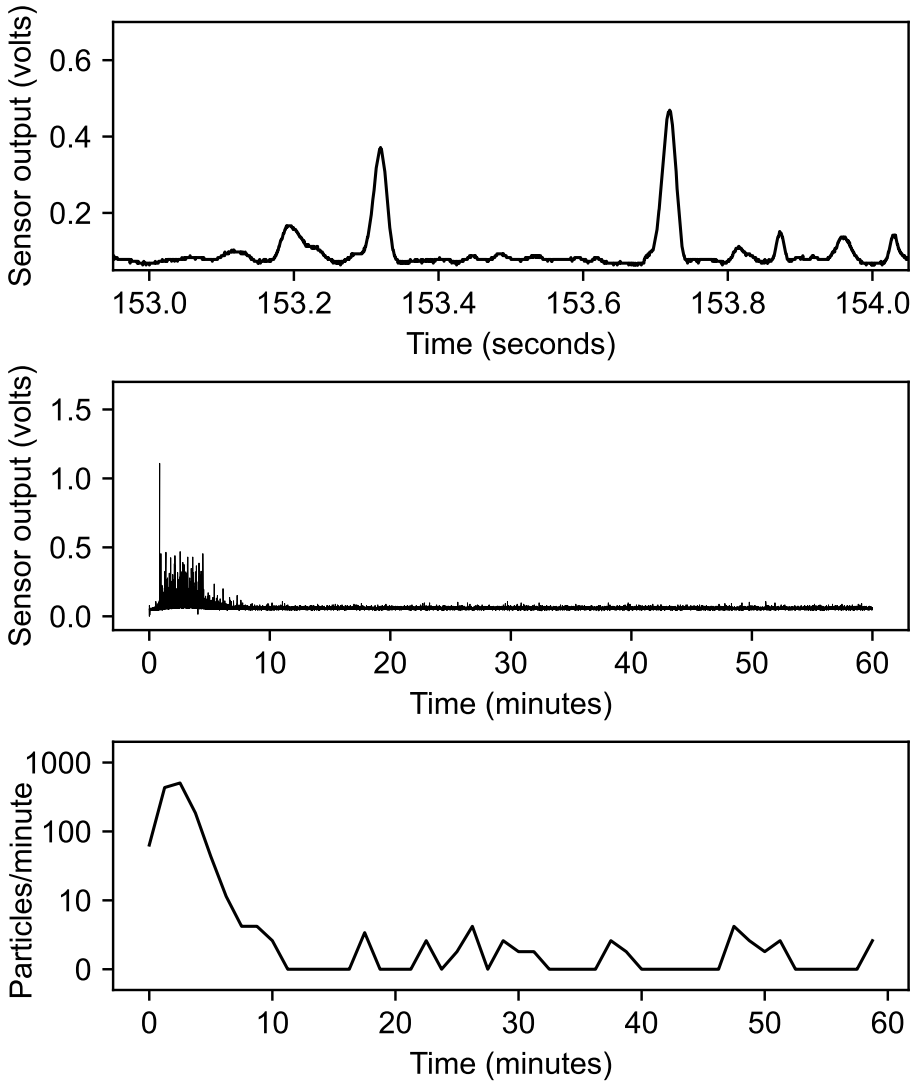
[picture p170: page 1]
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
