groverlab/disintegration-fingerprinting/data/bayer_tylenol/107 20251118T134538_T07one TRT.json.gz.pdf

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

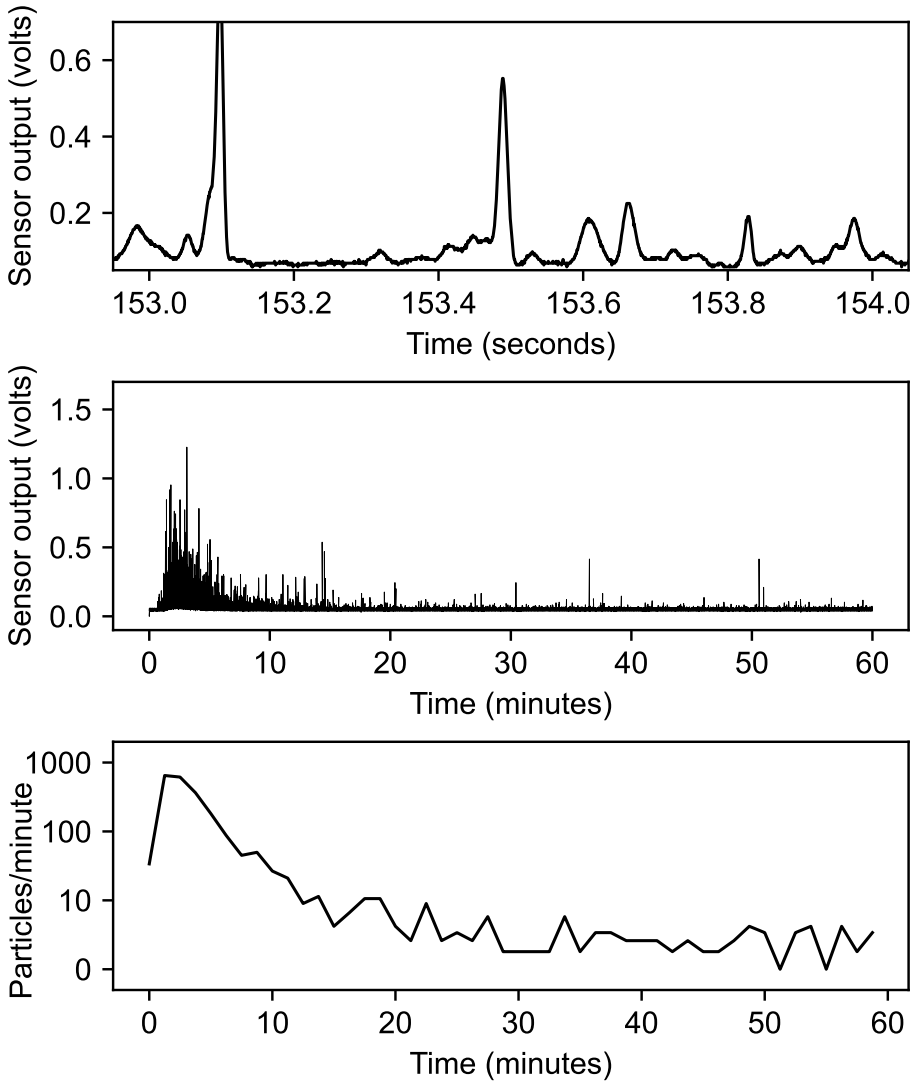
[picture p171: page 1]
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
