groverlab/disintegration-fingerprinting/data/bayer_tylenol/108 20251124T135557_T17one TCANADA.json.gz.pdf

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

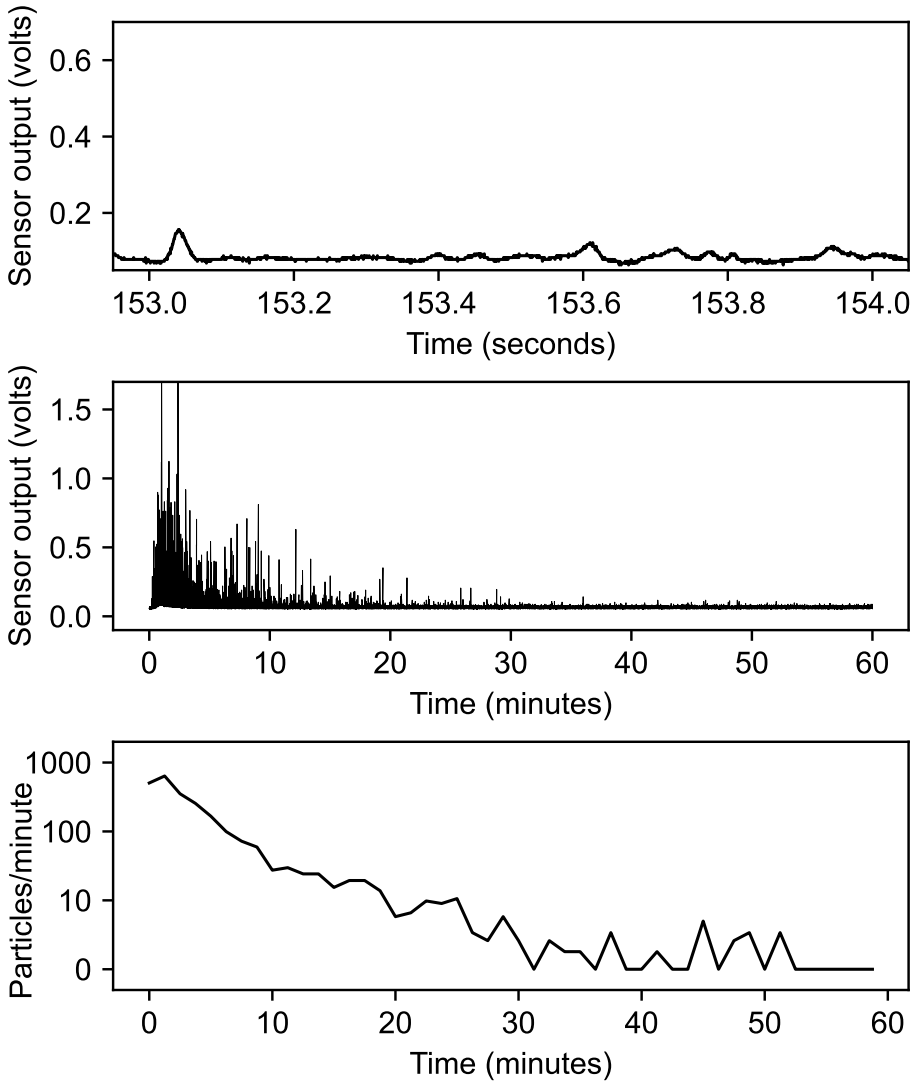
[picture p172: page 1]
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
