groverlab/disintegration-fingerprinting/data/bayer_tylenol/109 20251118T123829_T06one TRT.json.gz.pdf

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

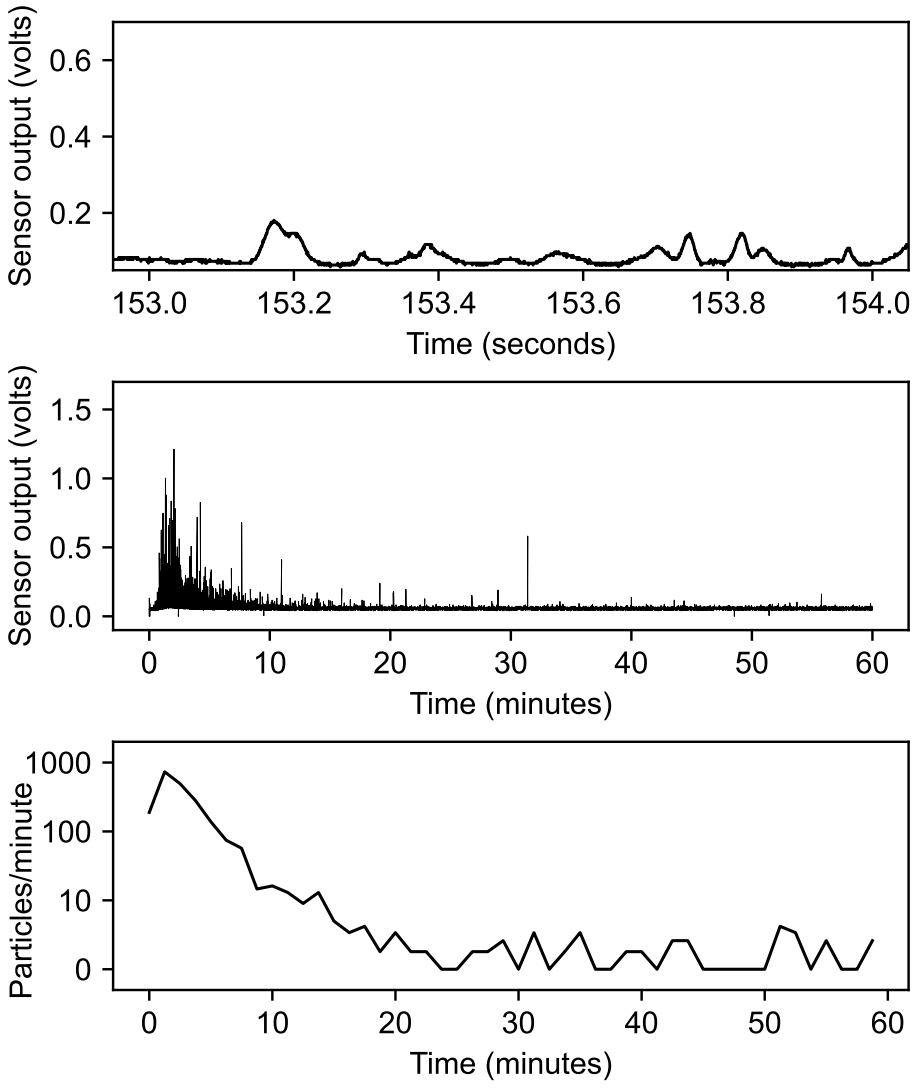
[picture p173: page 1]
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
