groverlab/disintegration-fingerprinting/data/bayer_tylenol/110 20251117T112834_T04one TRT.json.gz.pdf

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

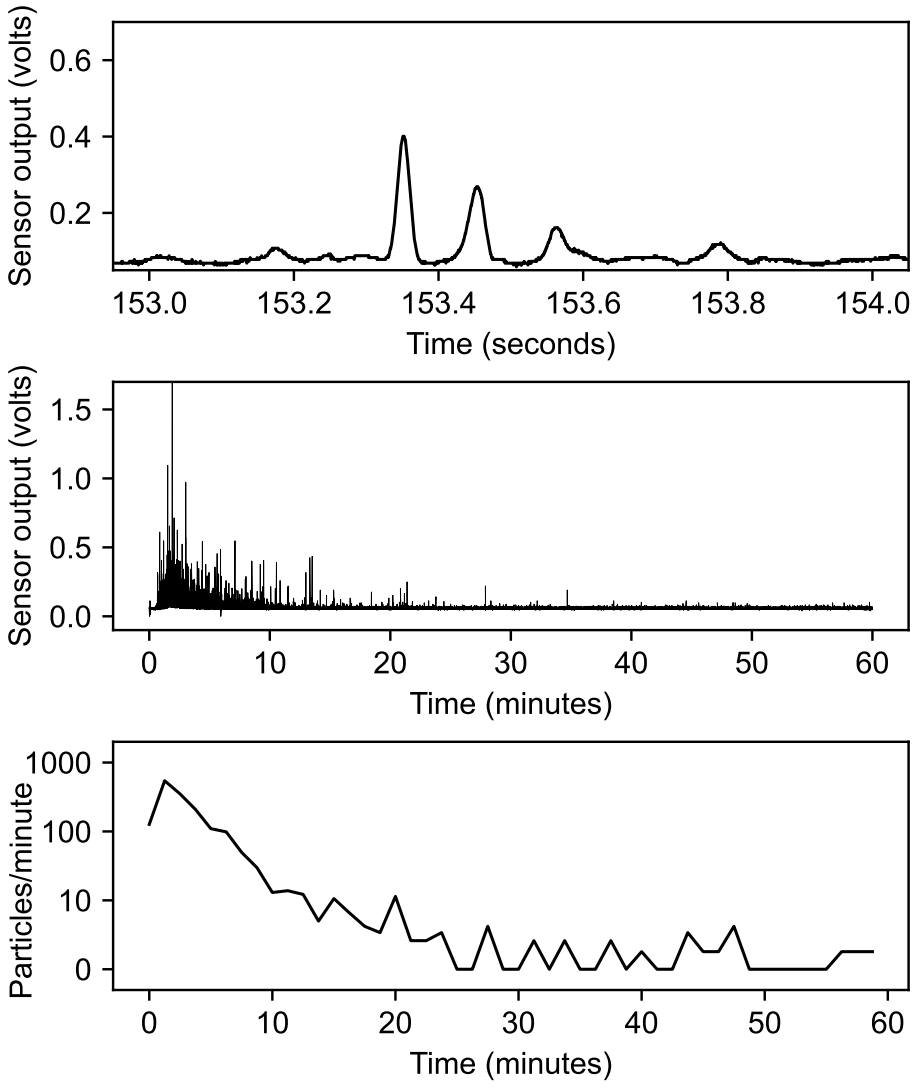
[picture p174: page 1]
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
