groverlab/disintegration-fingerprinting/data/bayer_tylenol/111 20251120T111520_T14one TRT.json.gz.pdf

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

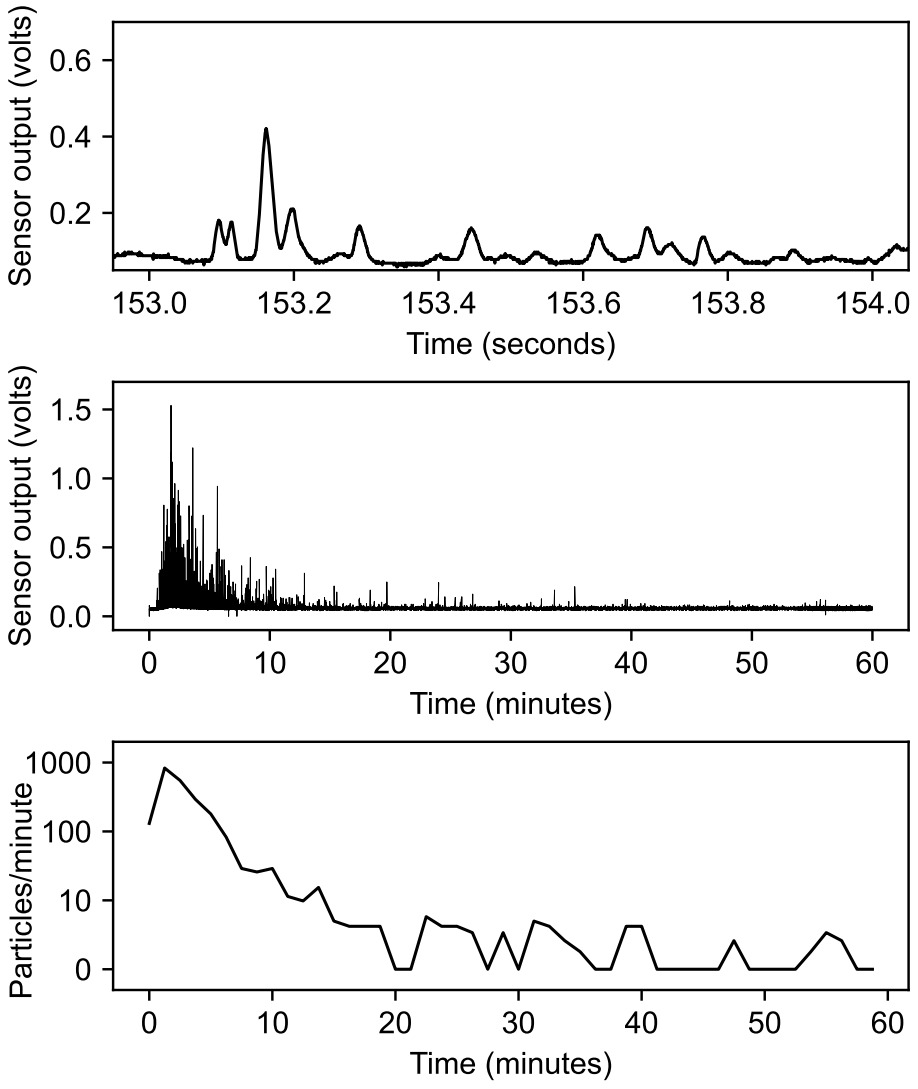
[picture p175: page 1]
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
