groverlab/disintegration-fingerprinting/data/bayer_tylenol/112 20251119T131818_T11one TRT.json.gz.pdf

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

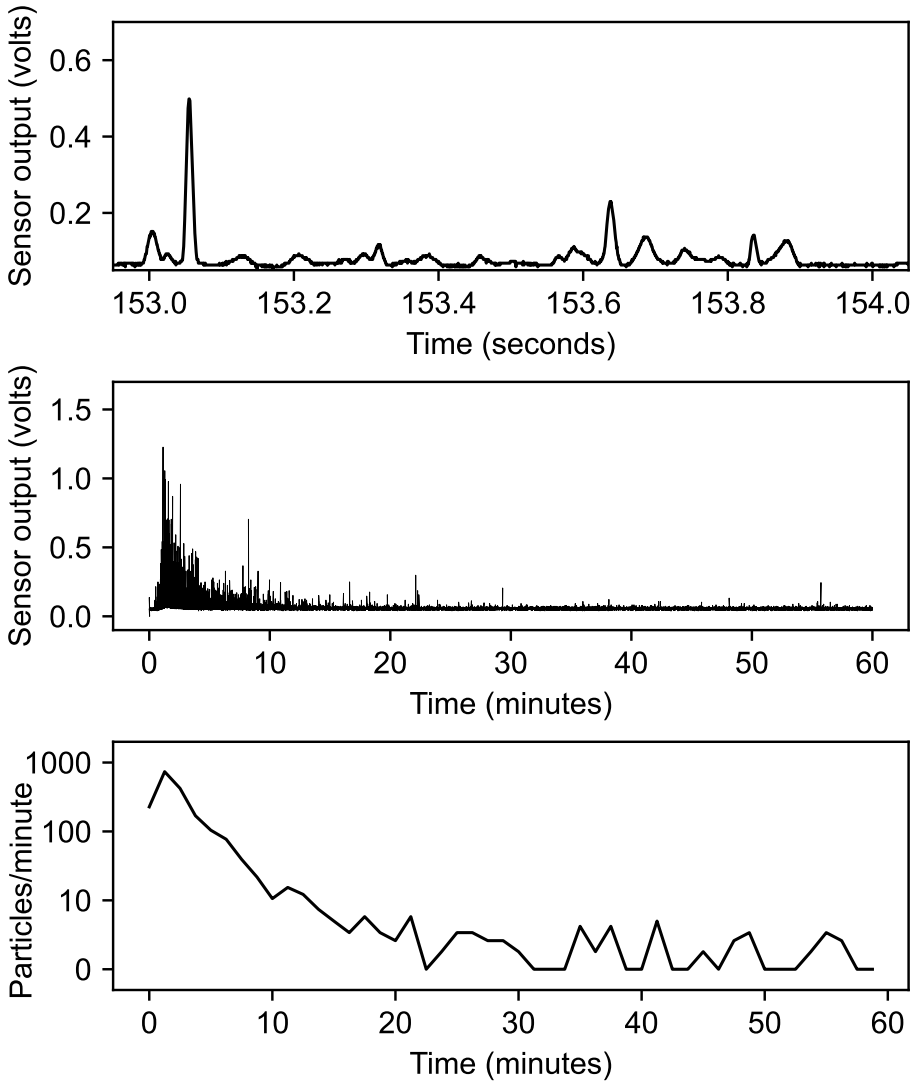
[picture p176: page 1]
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
