groverlab/disintegration-fingerprinting/data/bayer_tylenol/113 20251117T101939_T03one TRT.json.gz.pdf

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

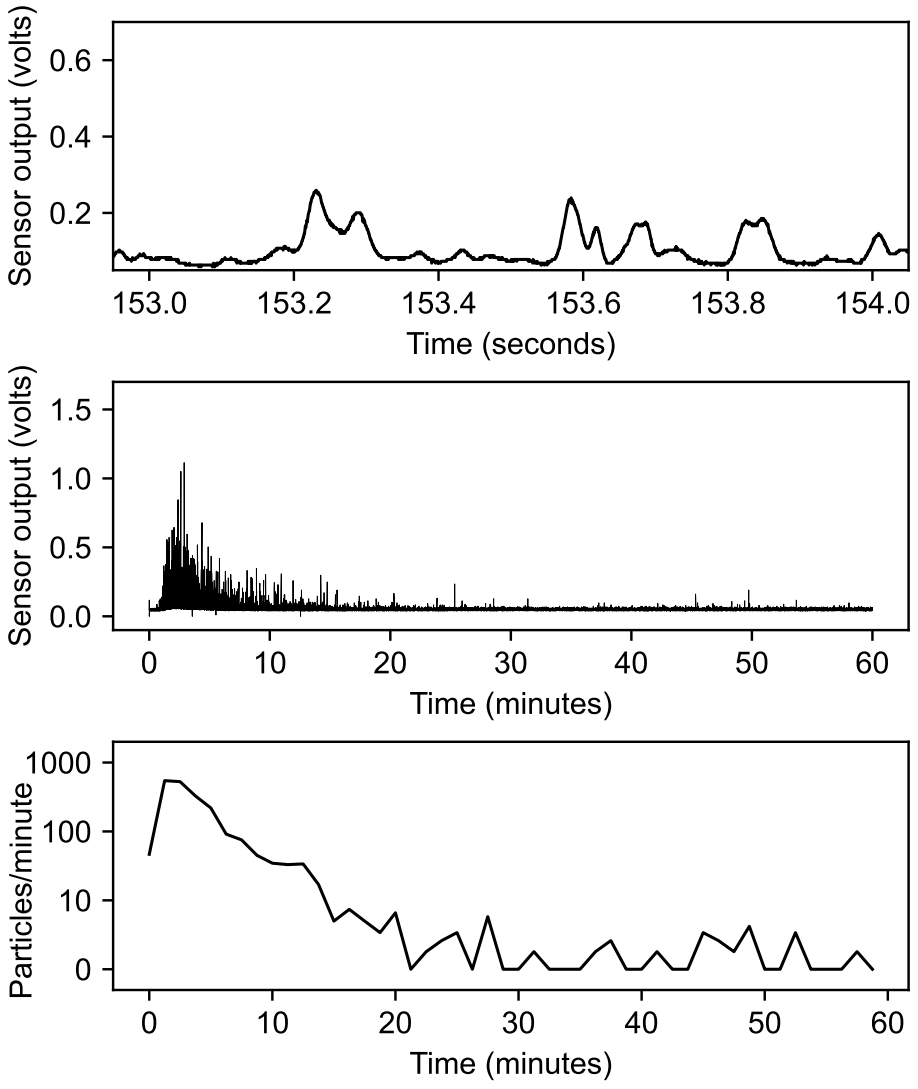
[picture p177: page 1]
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
