groverlab/disintegration-fingerprinting/data/bayer_tylenol/114 20251113T154922_T01one TRT.json.gz.pdf

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

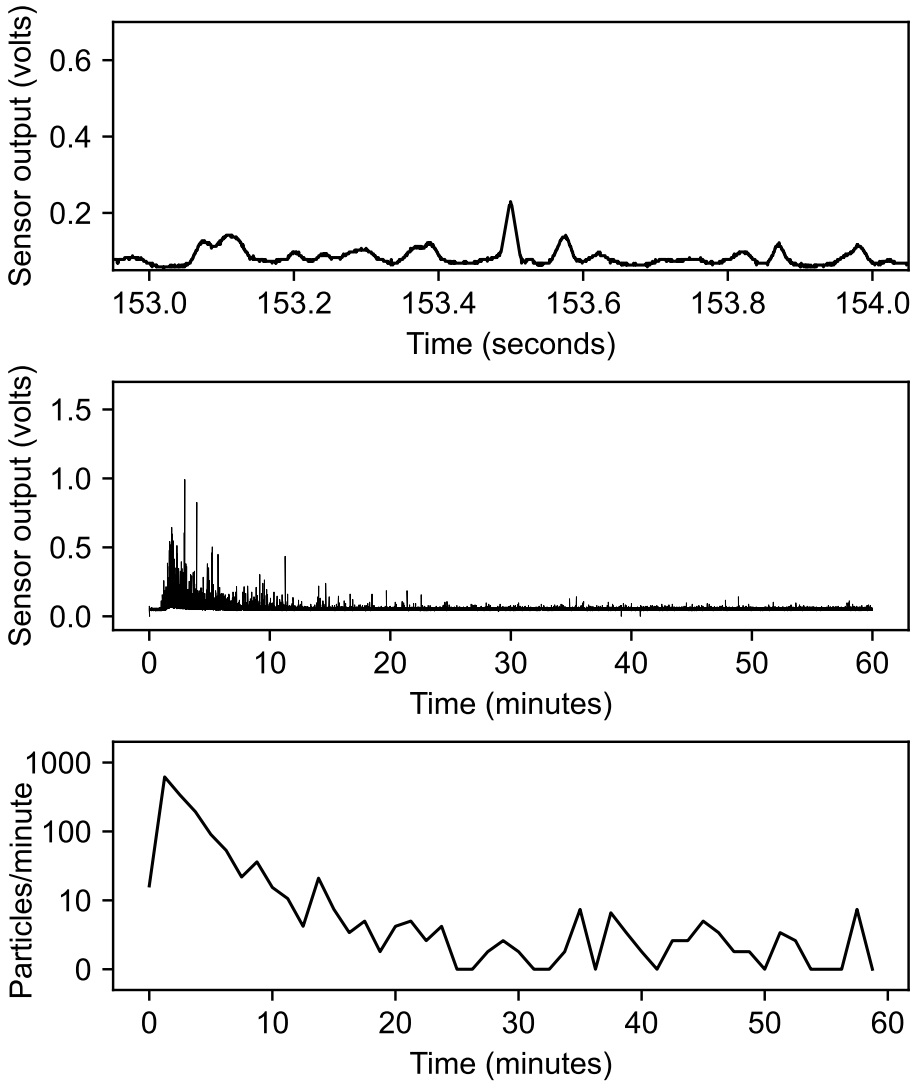
[picture p178: page 1]
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
