groverlab/disintegration-fingerprinting/data/bayer_tylenol/115 20251118T160812_T09one TRT.json.gz.pdf

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

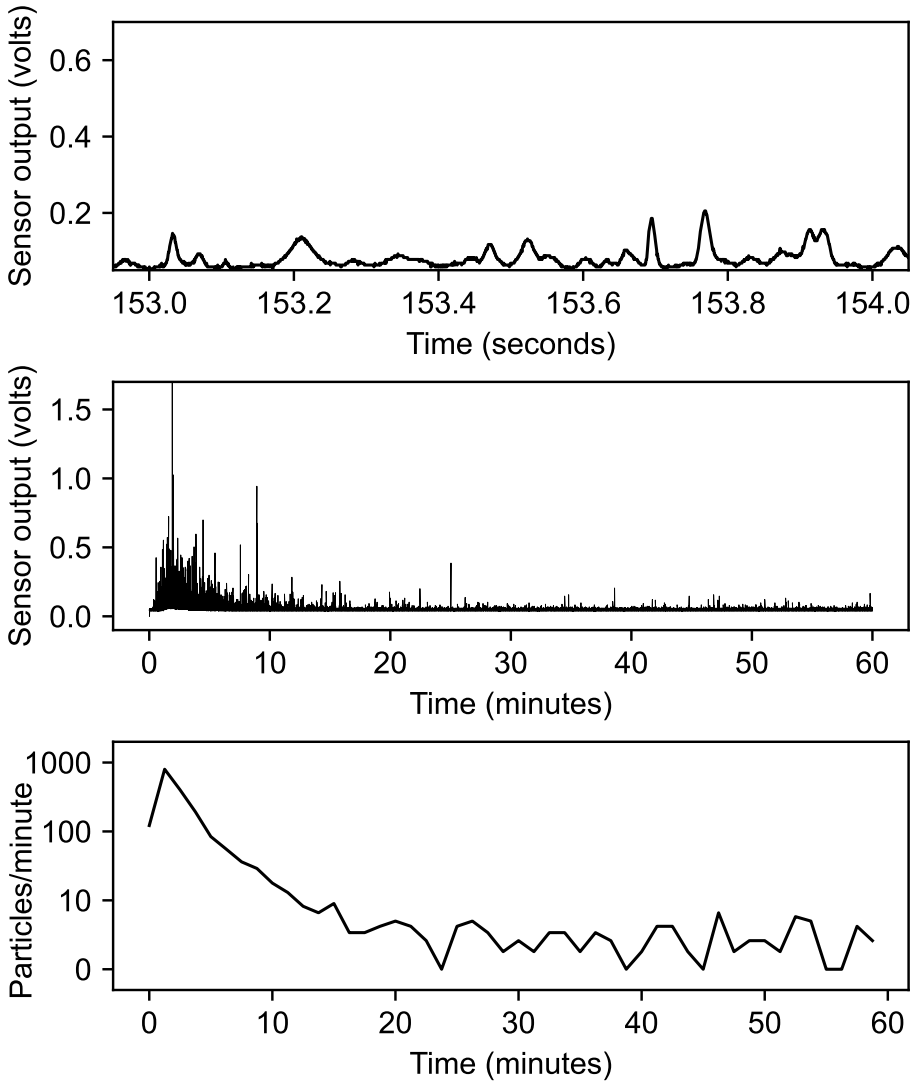
[picture p179: page 1]
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
