groverlab/disintegration-fingerprinting/data/bayer_tylenol/116 20251119T121001_T10one TRT.json.gz.pdf

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

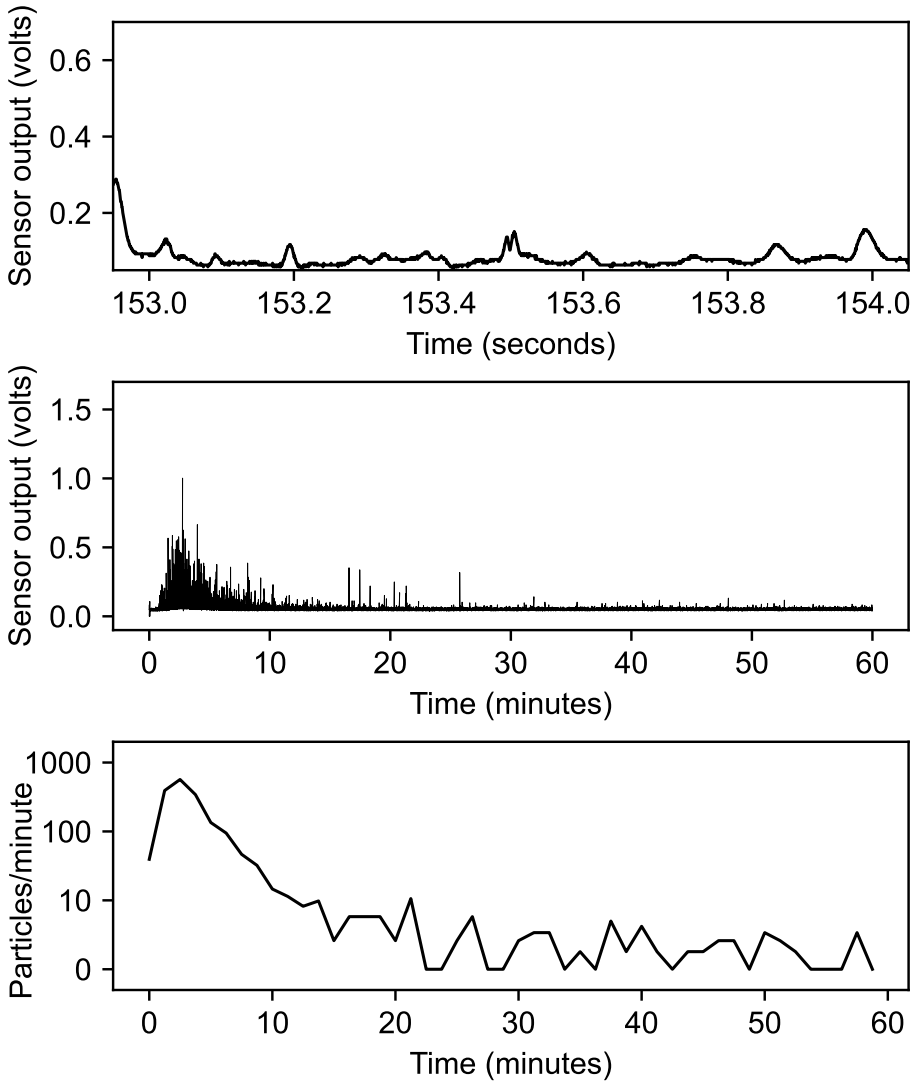
[picture p180: page 1]
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
