groverlab/disintegration-fingerprinting/data/bayer_tylenol/117 20251119T142553_T12one TRT.json.gz.pdf

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

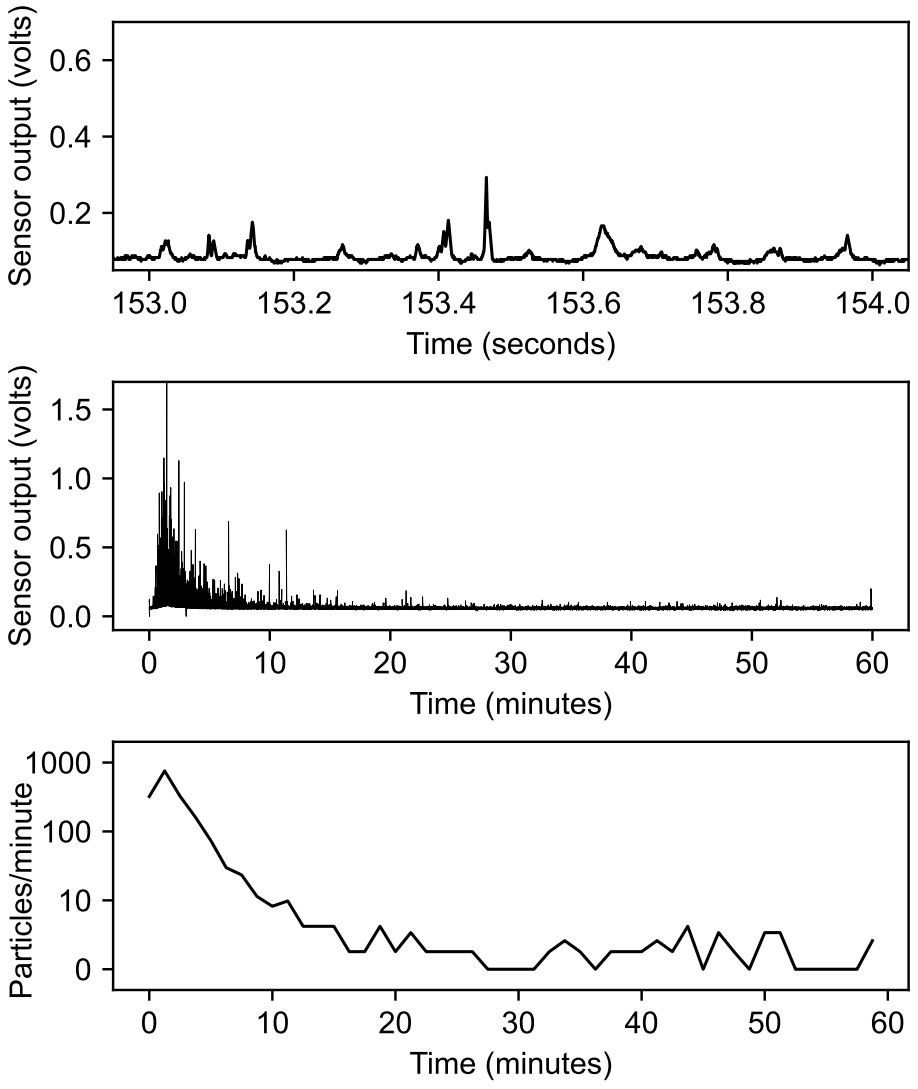
[picture p181: page 1]
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
