groverlab/disintegration-fingerprinting/data/bayer_tylenol/118 20260114T121643_T18one TRT.json.gz.pdf

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

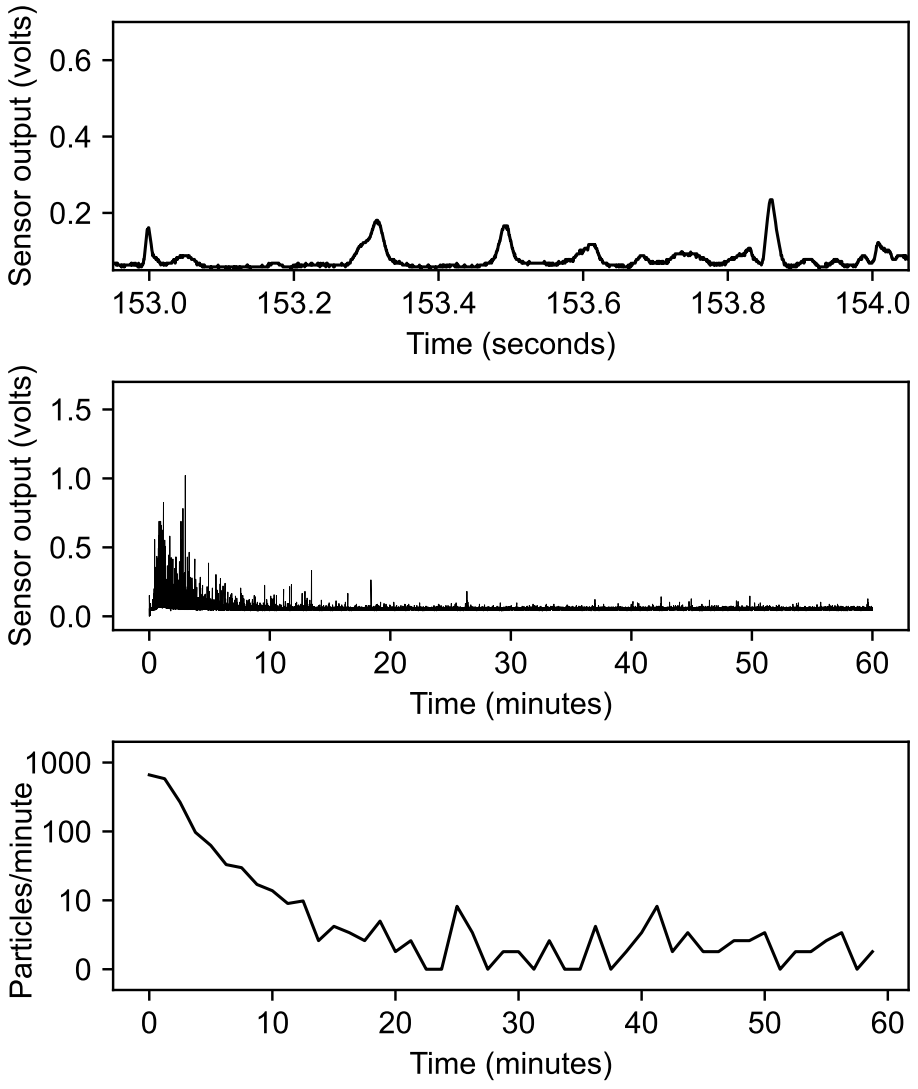
[picture p182: page 1]
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
