groverlab/disintegration-fingerprinting/data/bayer_tylenol/150 20251210T103434_T06 THOT 1.json.gz.pdf

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

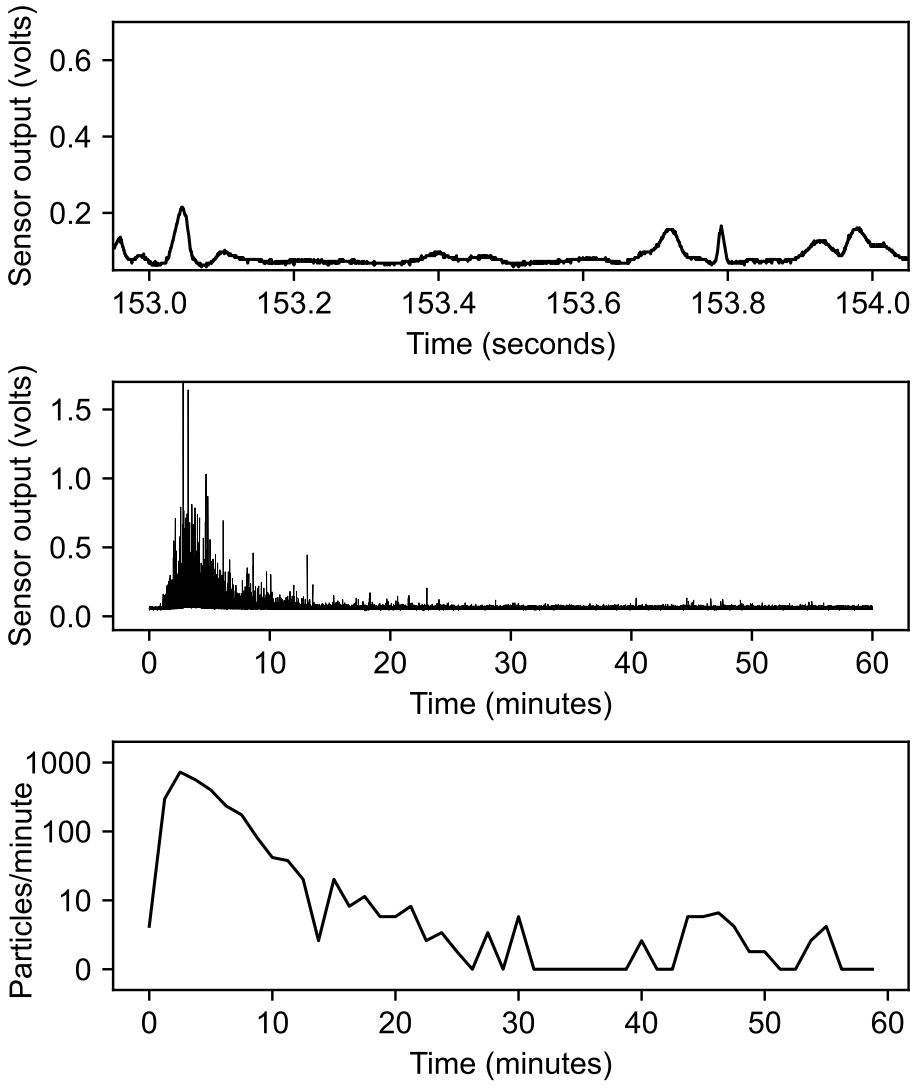
[picture p183: page 1]
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
