groverlab/disintegration-fingerprinting/data/bayer_tylenol/151 20251210T114041_T06 THOT 2.json.gz.pdf

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

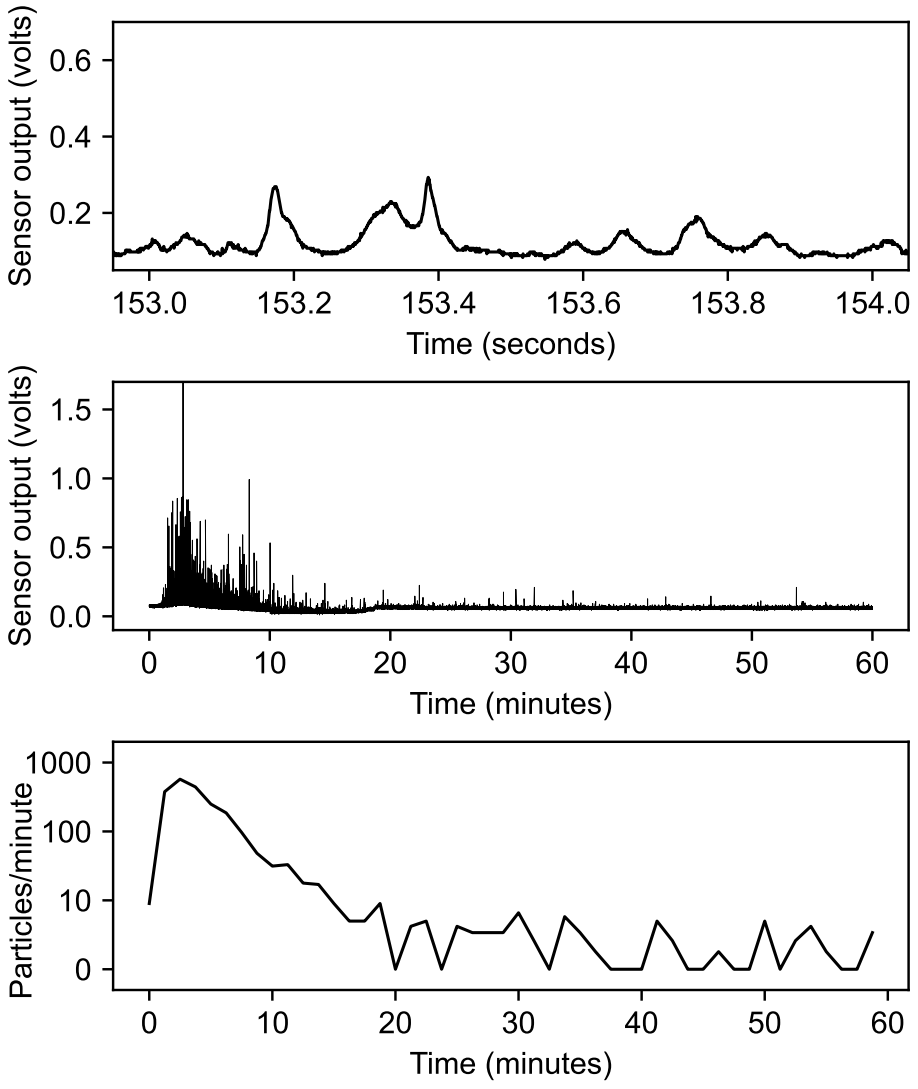
[picture p184: page 1]
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
