groverlab/disintegration-fingerprinting/data/bayer_tylenol/152 20251210T124817_T06 THOT 3.json.gz.pdf

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

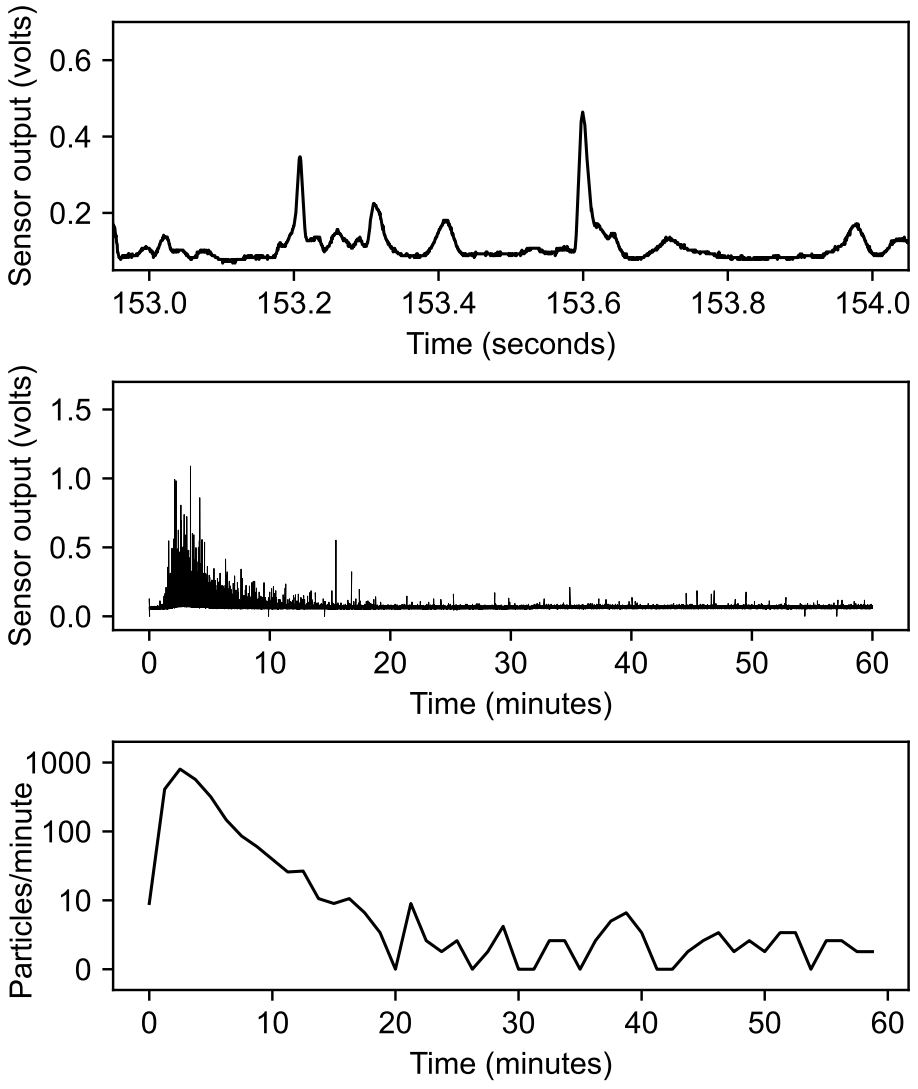
[picture p185: page 1]
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
