groverlab/disintegration-fingerprinting/data/bayer_tylenol/153 20251210T135456_T06 TCOLD 1.json.gz.pdf

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

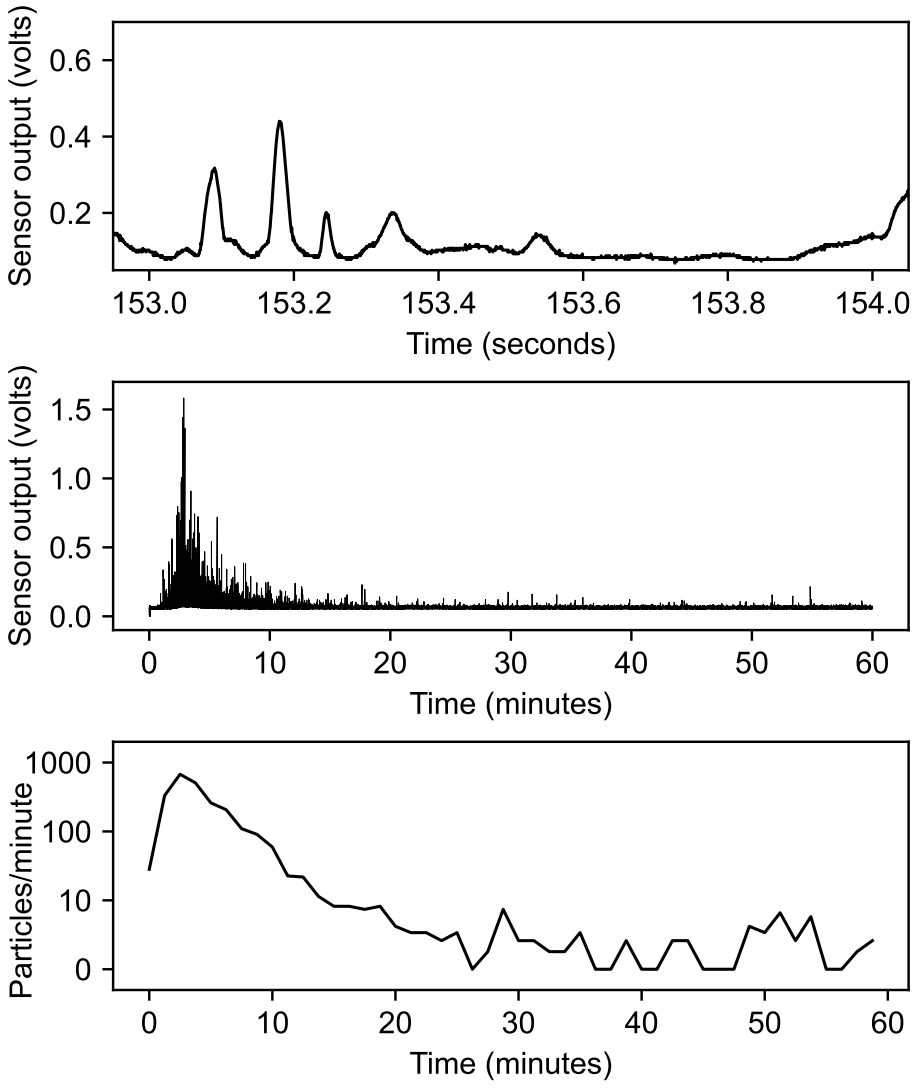
[picture p186: page 1]
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
