groverlab/disintegration-fingerprinting/data/bayer_tylenol/154 20251210T150122_T06 TCOLD 2.json.gz.pdf

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

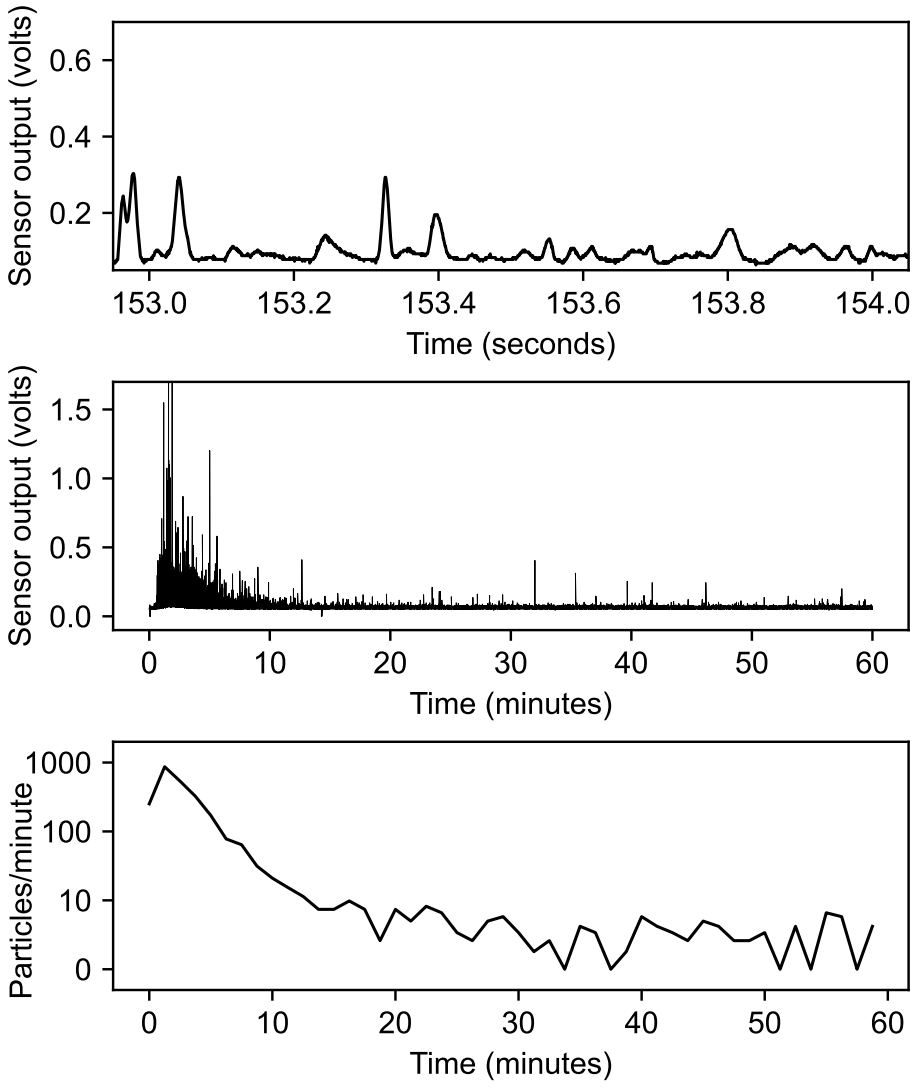
[picture p187: page 1]
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
