groverlab/disintegration-fingerprinting/data/bayer_tylenol/155 20251210T160747_T06 TCOLD 3.json.gz.pdf

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

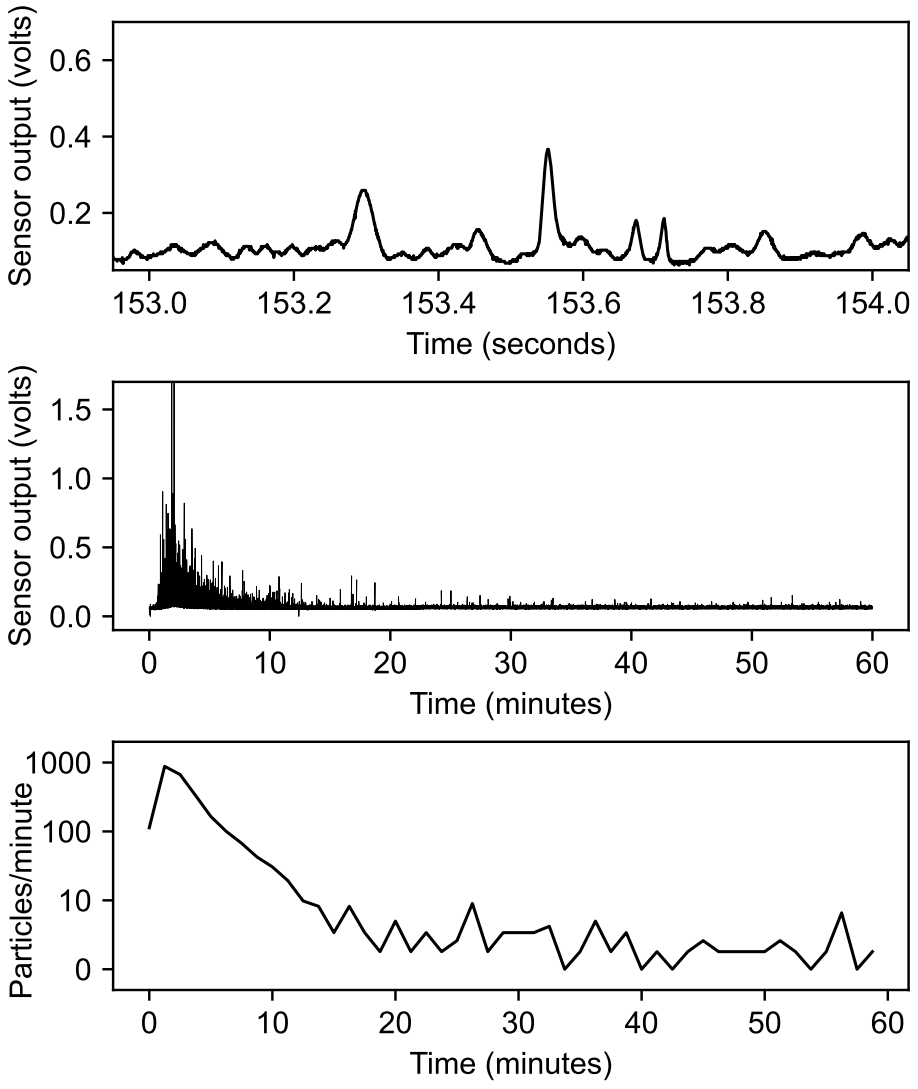
[picture p188: page 1]
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
