groverlab/disintegration-fingerprinting/data/bayer_tylenol/20241115T080902_generic_aspirin GENERICBOTTLE.json.gz.pdf

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

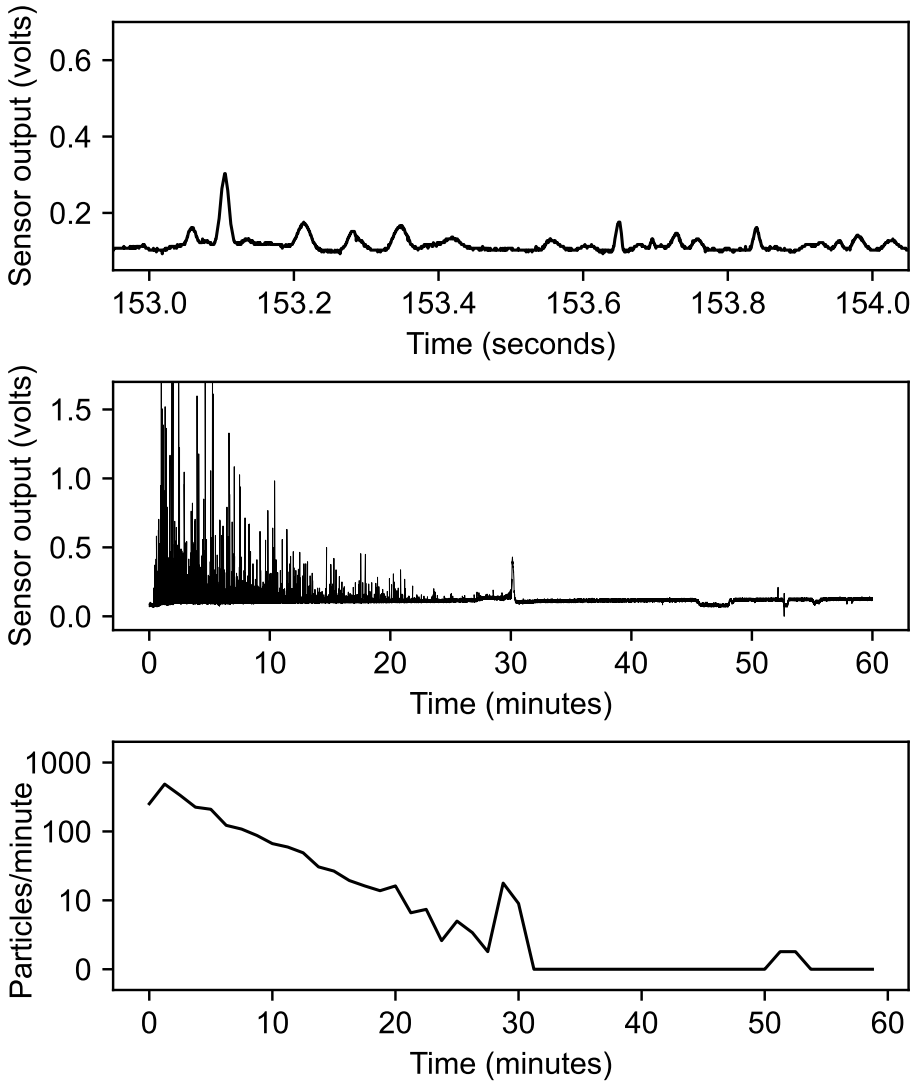
[picture p199: page 1]
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
