groverlab/disintegration-fingerprinting/data/bayer_tylenol/20241119T140627_Bayer_Aspirin BAYERBOTTLE.json.gz.pdf

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

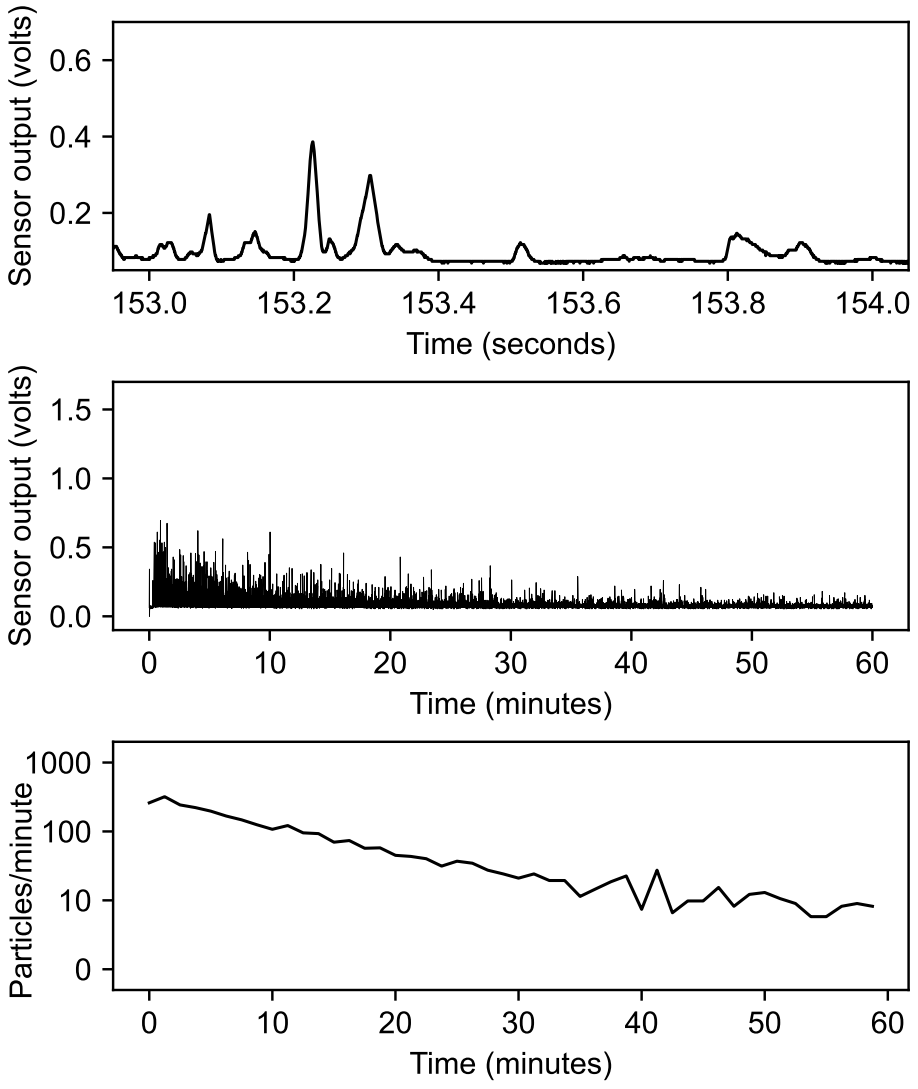
[picture p205: page 1]
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
