groverlab/disintegration-fingerprinting/data/bayer_tylenol/20241121T135122_Bayer_Aspirin BAYERBOTTLE.json.gz.pdf

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

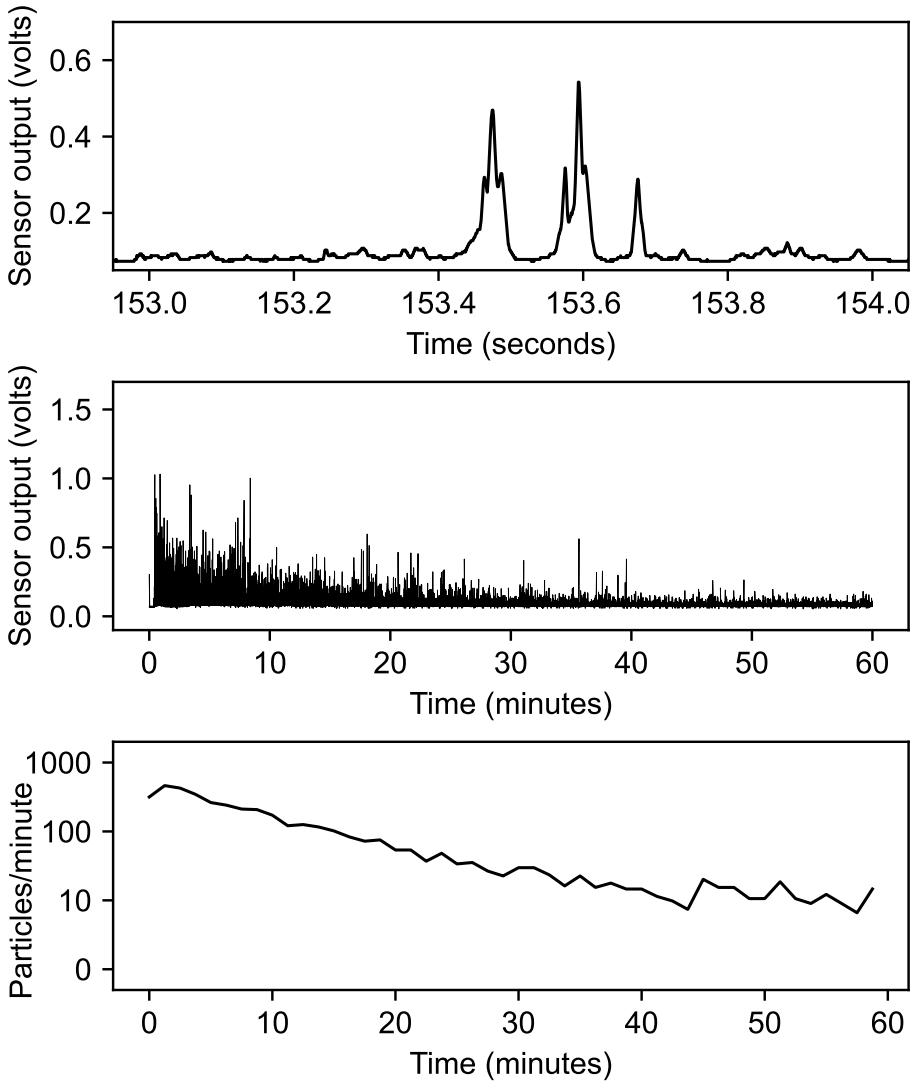
[picture p210: page 1]
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
