groverlab/disintegration-fingerprinting/data/bayer_tylenol/20241203T115945_Generic_Aspirin GENERICBOTTLE.json.gz.pdf

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

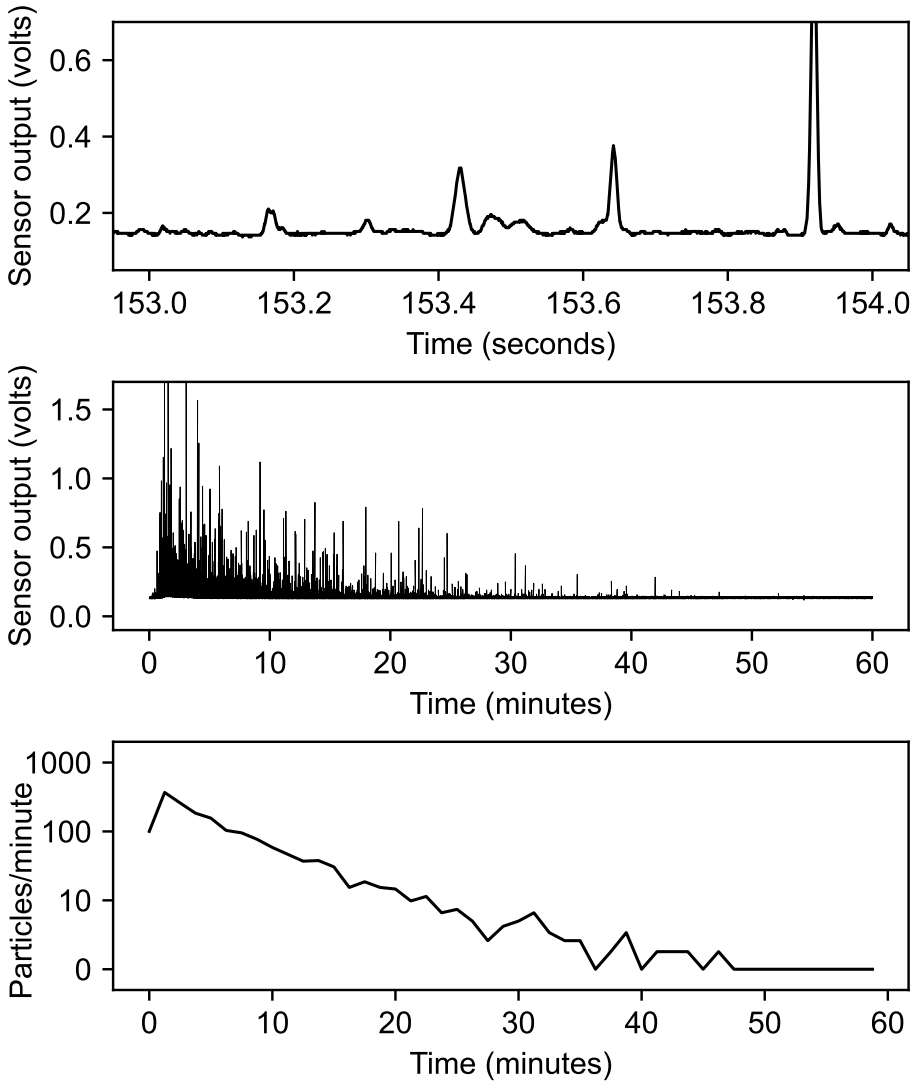
[picture p216: page 1]
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
