groverlab/disintegration-fingerprinting/data/bayer_tylenol/501 20251112T162420_A12one ART.json.gz.pdf

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

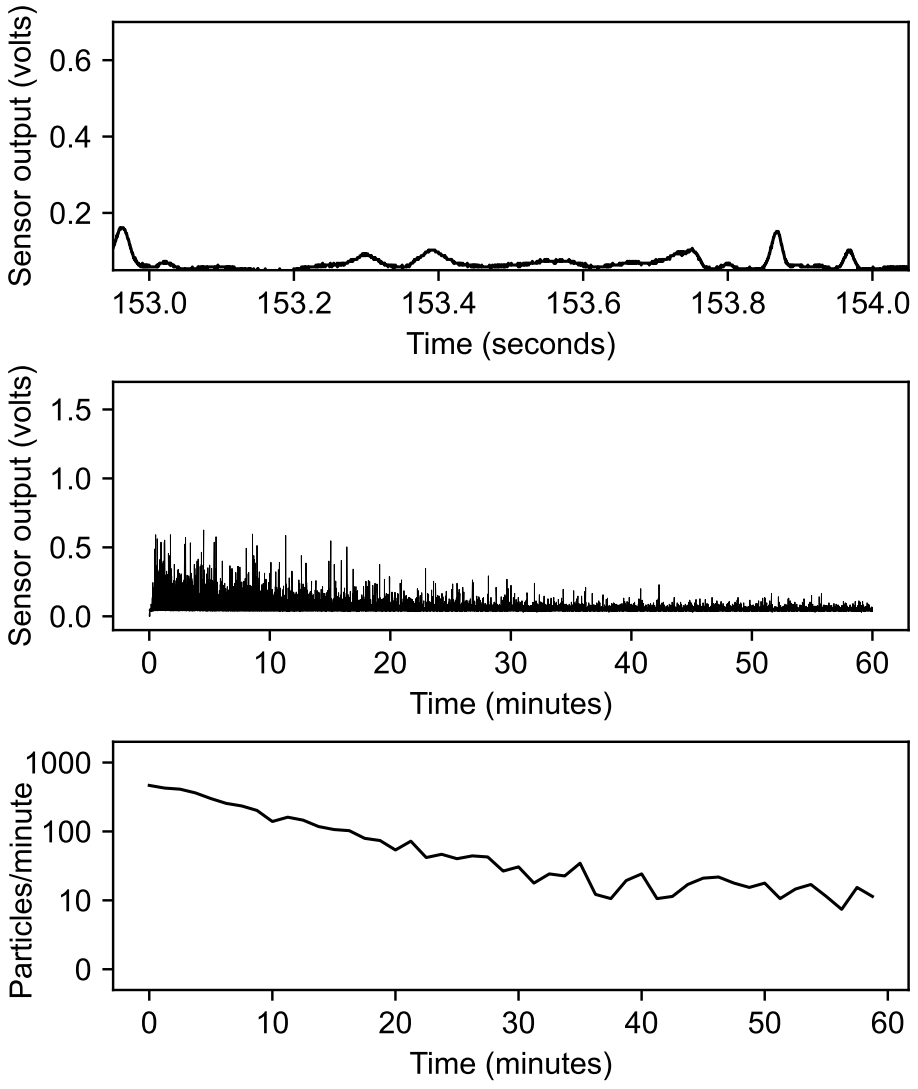
[picture p219: page 1]
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
