groverlab/disintegration-fingerprinting/data/bayer_tylenol/502 20251111T121444_A07one ART.json.gz.pdf

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

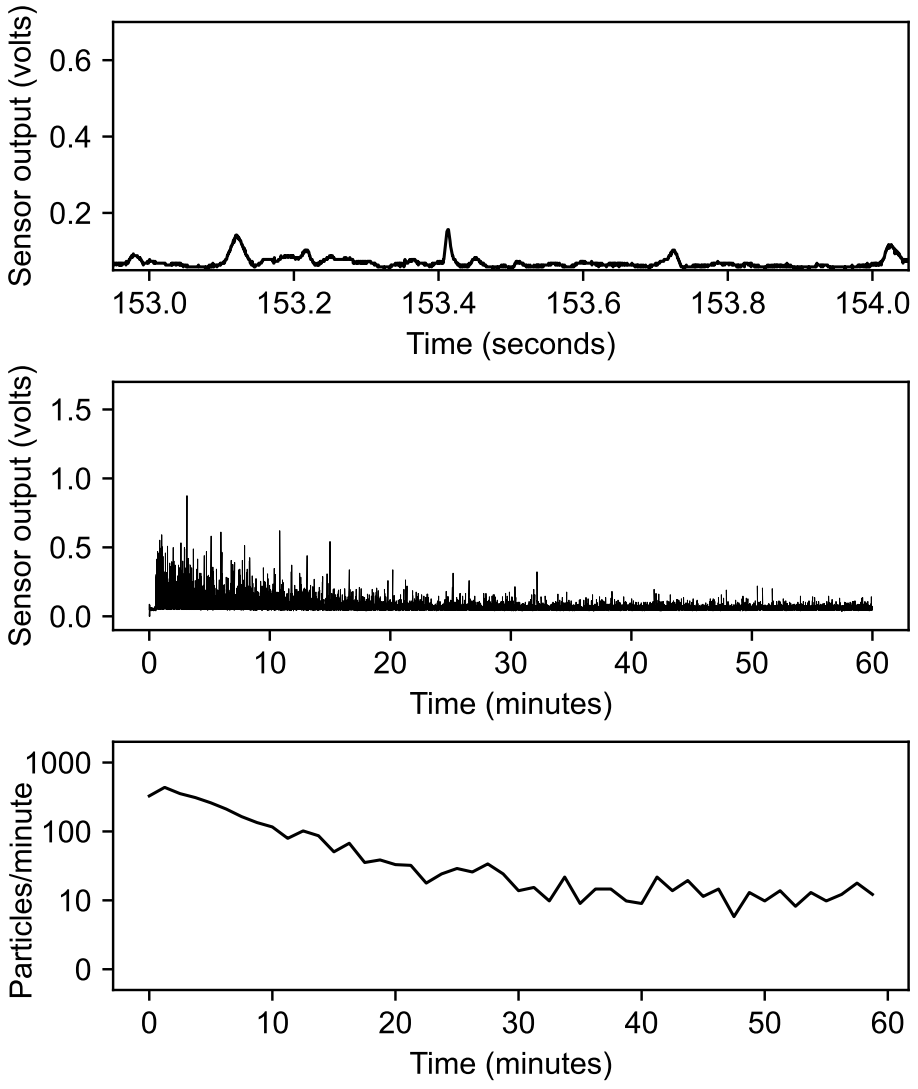
[picture p220: page 1]
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
