groverlab/disintegration-fingerprinting/data/bayer_tylenol/503 20251124T150228_A17one ACANADA.json.gz.pdf

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

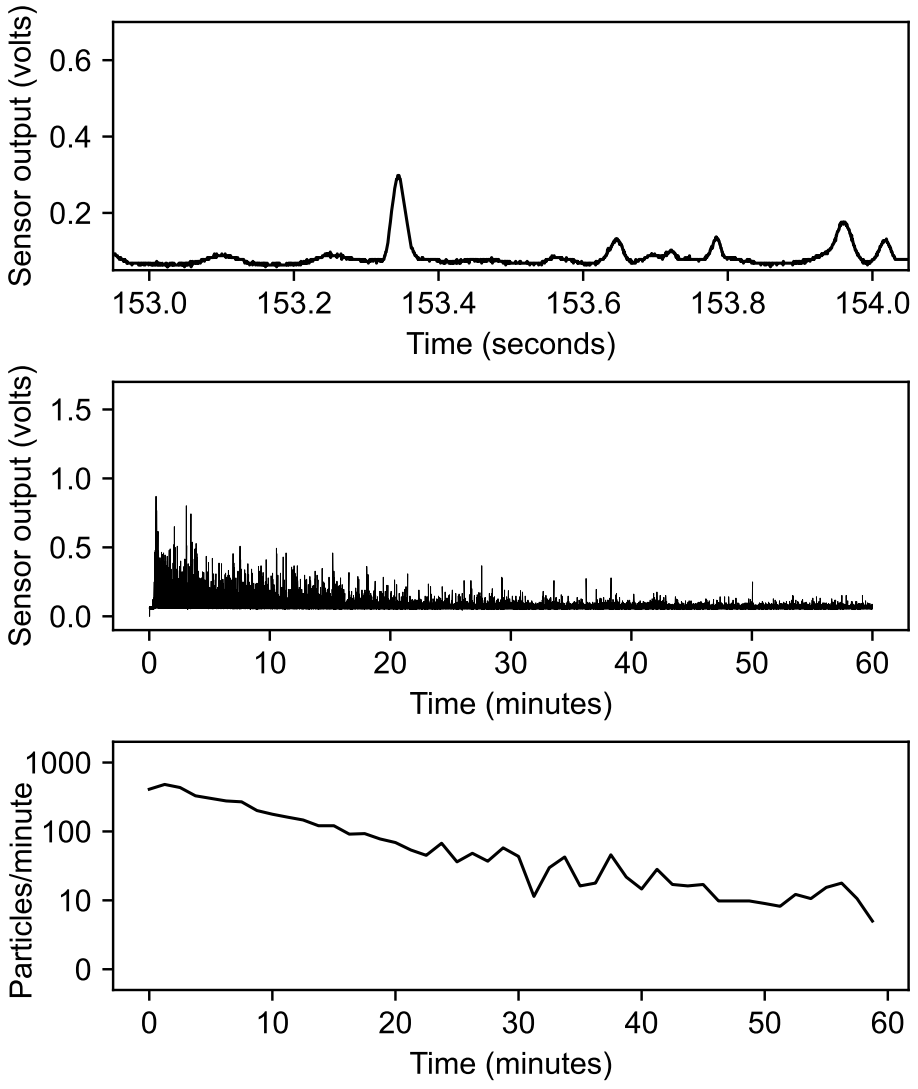
[picture p221: page 1]
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
