groverlab/disintegration-fingerprinting/data/bayer_tylenol/504 20251113T120744_A14one ART.json.gz.pdf

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

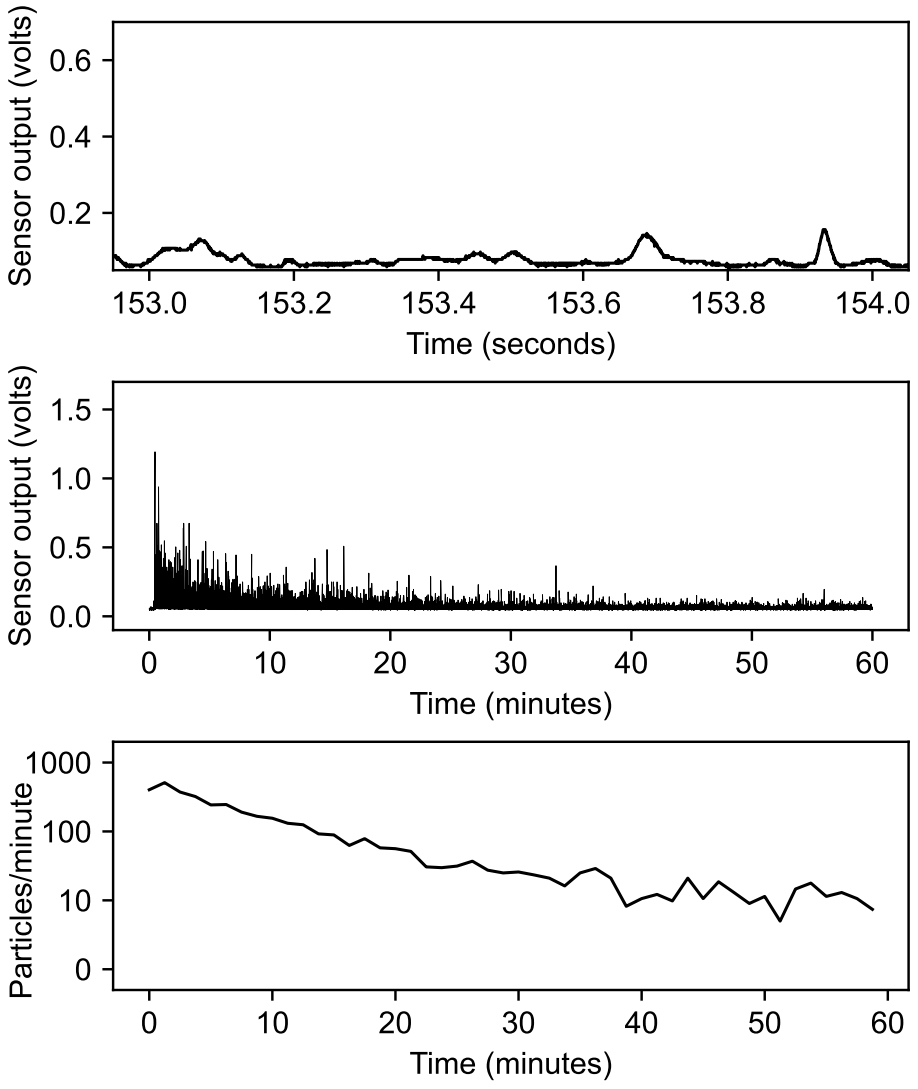
[picture p222: page 1]
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
