groverlab/disintegration-fingerprinting/data/bayer_tylenol/505 20251110T134251_A03one ART.json.gz.pdf

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

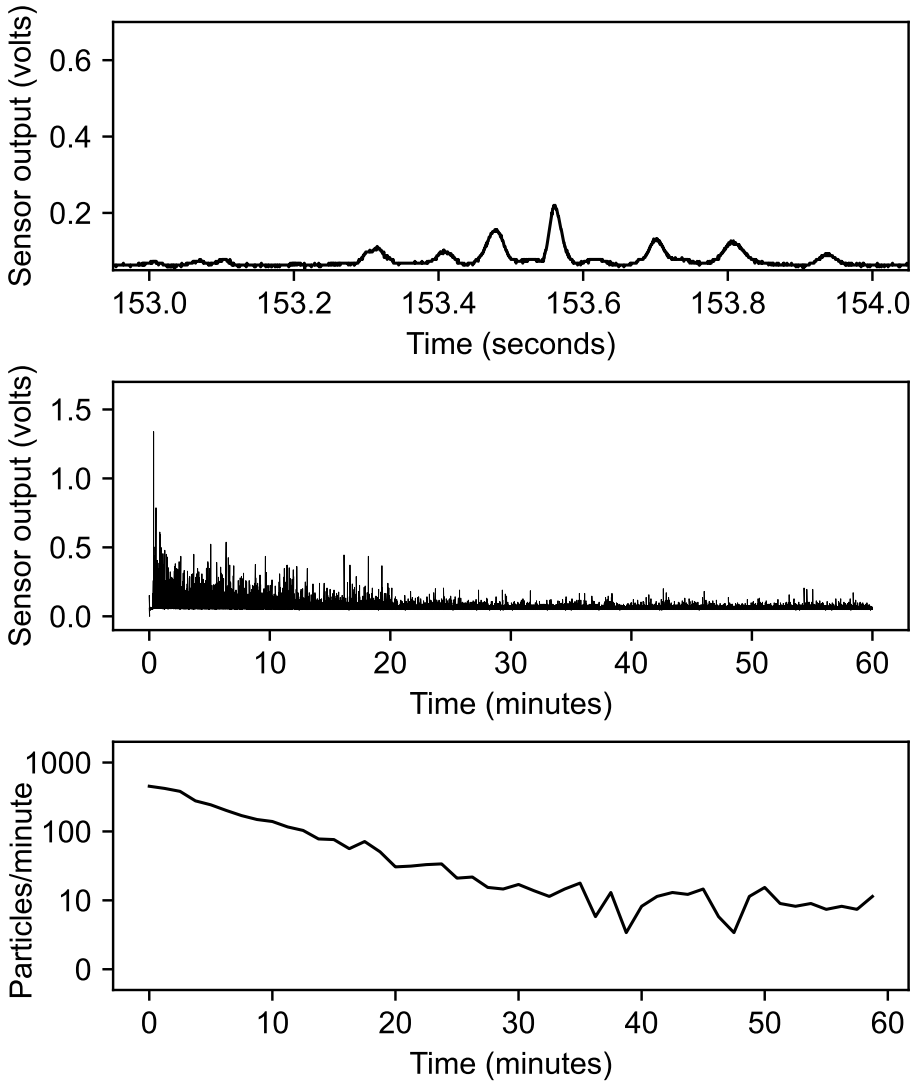
[picture p223: page 1]
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
