groverlab/disintegration-fingerprinting/data/bayer_tylenol/506 20251112T151658_A11one ART.json.gz.pdf

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

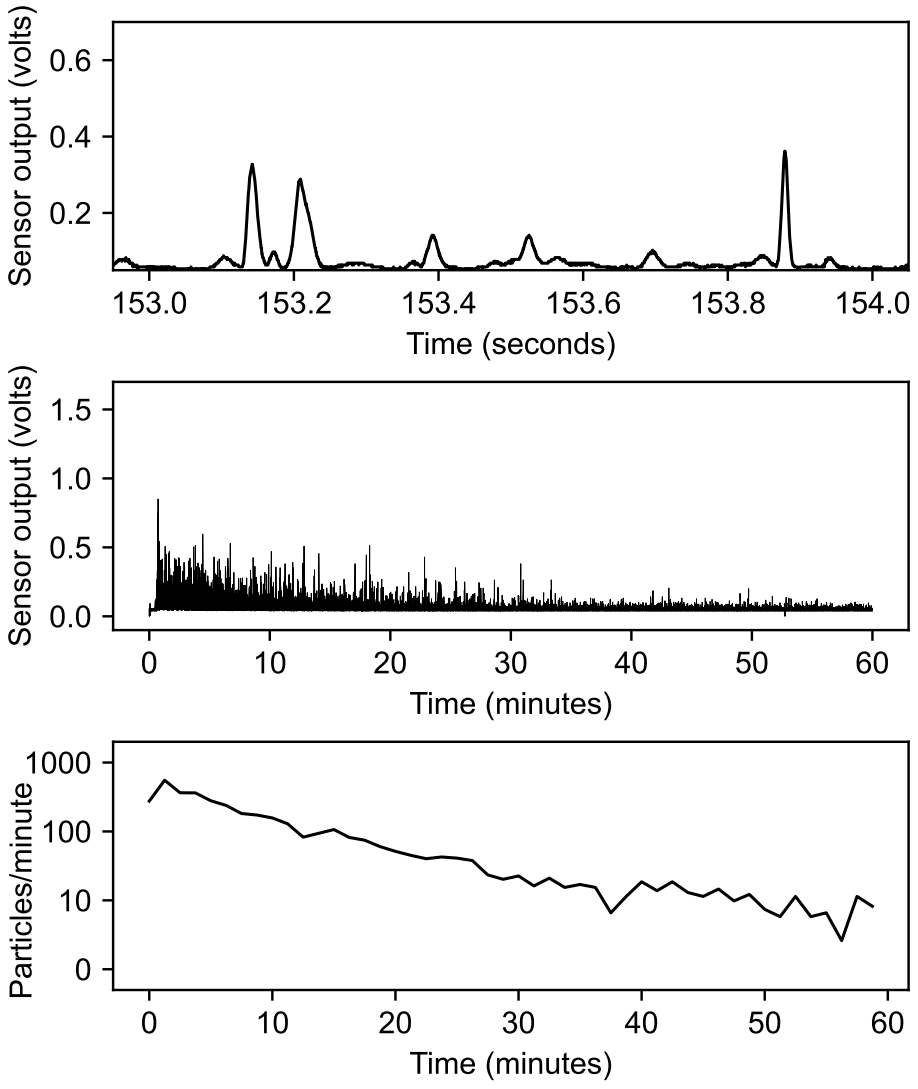
[picture p224: page 1]
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
