groverlab/disintegration-fingerprinting/data/bayer_tylenol/507 20251111T110351_A06one ART.json.gz.pdf

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

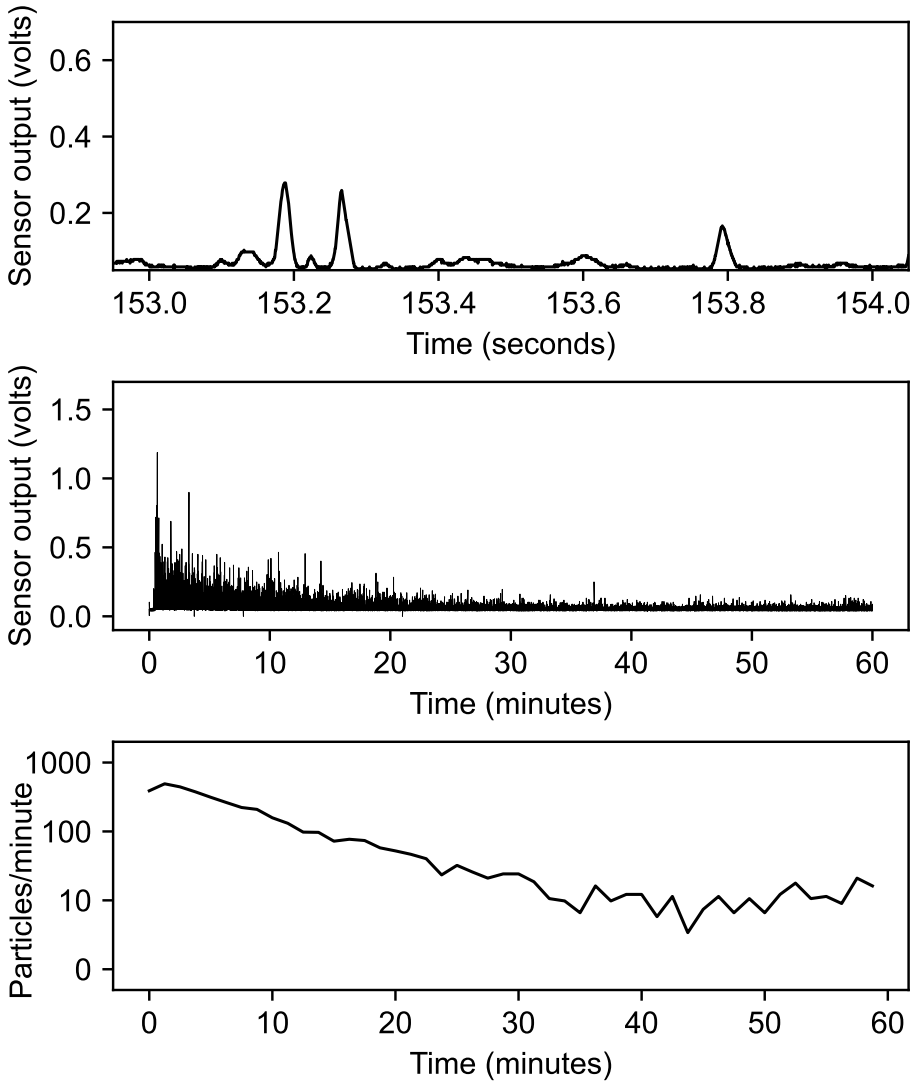
[picture p225: page 1]
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
