groverlab/disintegration-fingerprinting/data/bayer_tylenol/508 20251125T104844_A19one ACANADA.json.gz.pdf

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

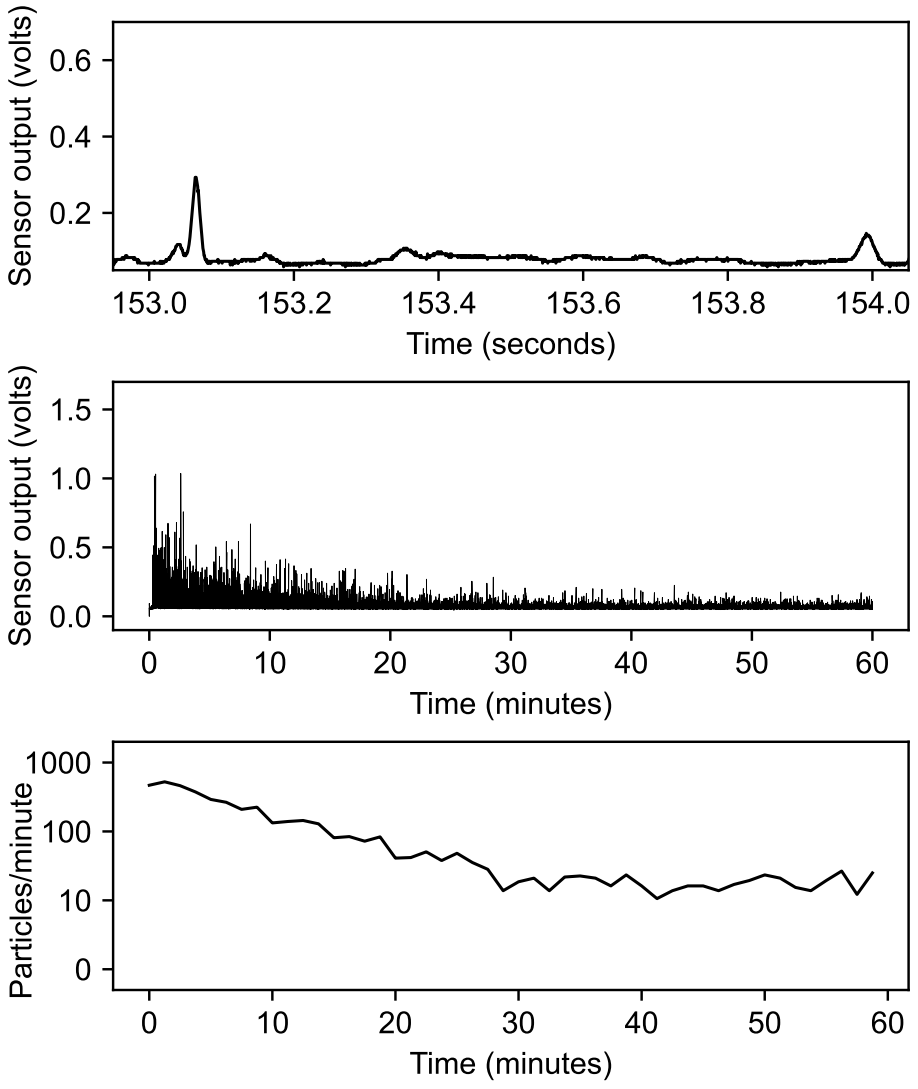
[picture p226: page 1]
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
