groverlab/disintegration-fingerprinting/data/bayer_tylenol/509 20251110T161145_A04one ART.json.gz.pdf

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

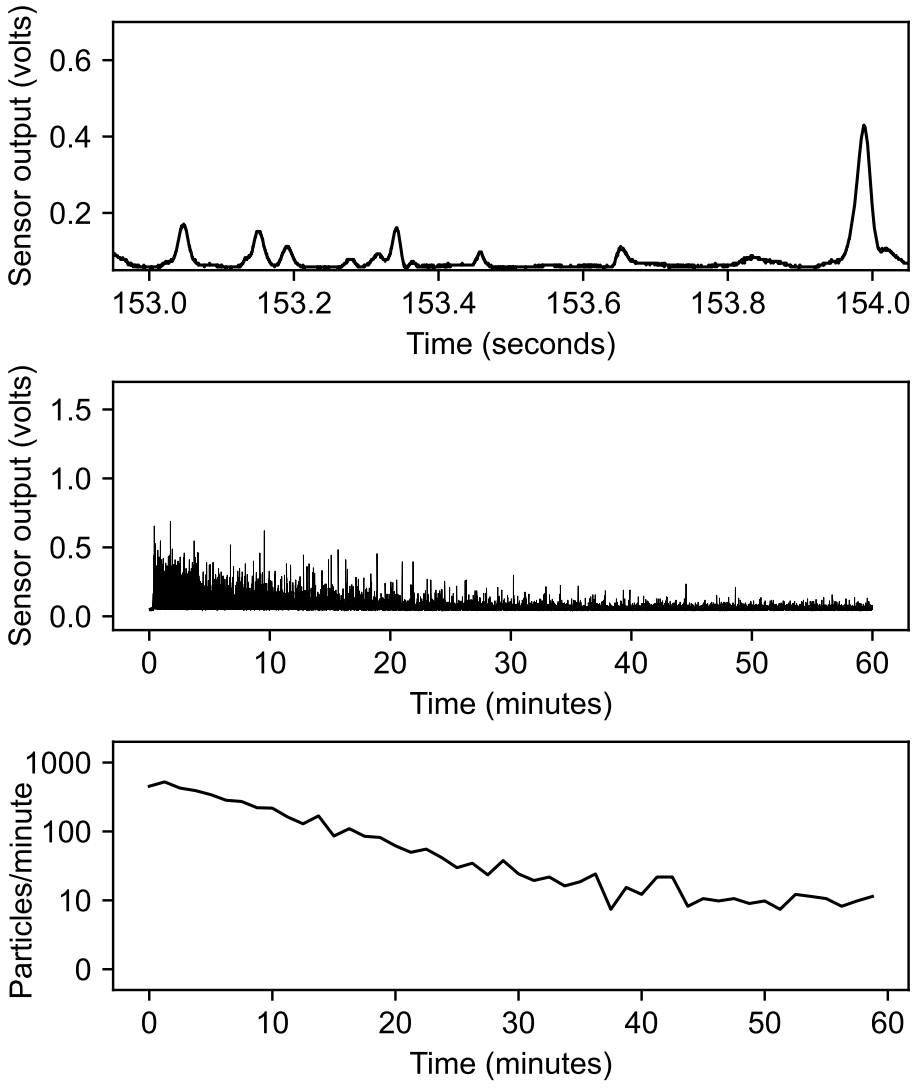
[picture p227: page 1]
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
