groverlab/disintegration-fingerprinting/data/bayer_tylenol/510 20251112T114510_A08one ART.json.gz.pdf

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

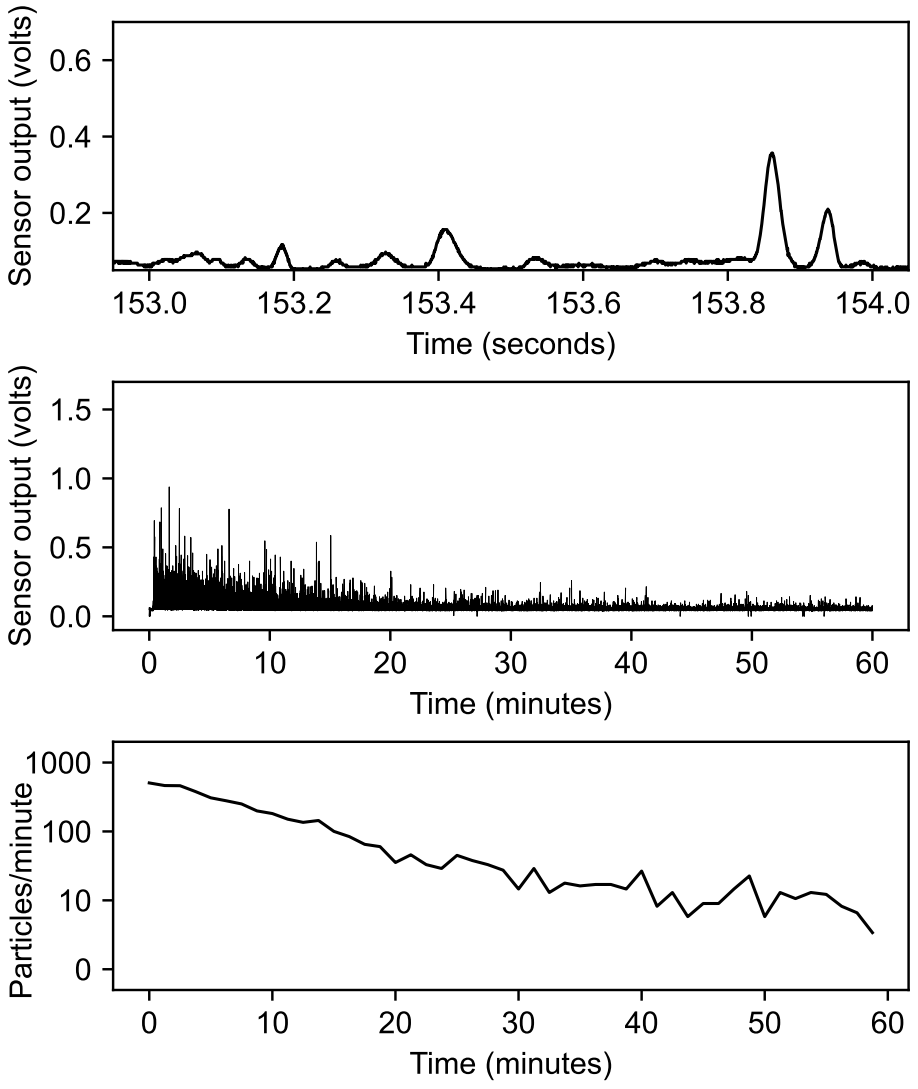
[picture p228: page 1]
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
