groverlab/disintegration-fingerprinting/data/bayer_tylenol/511 20251113T132033_A15one ART.json.gz.pdf

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

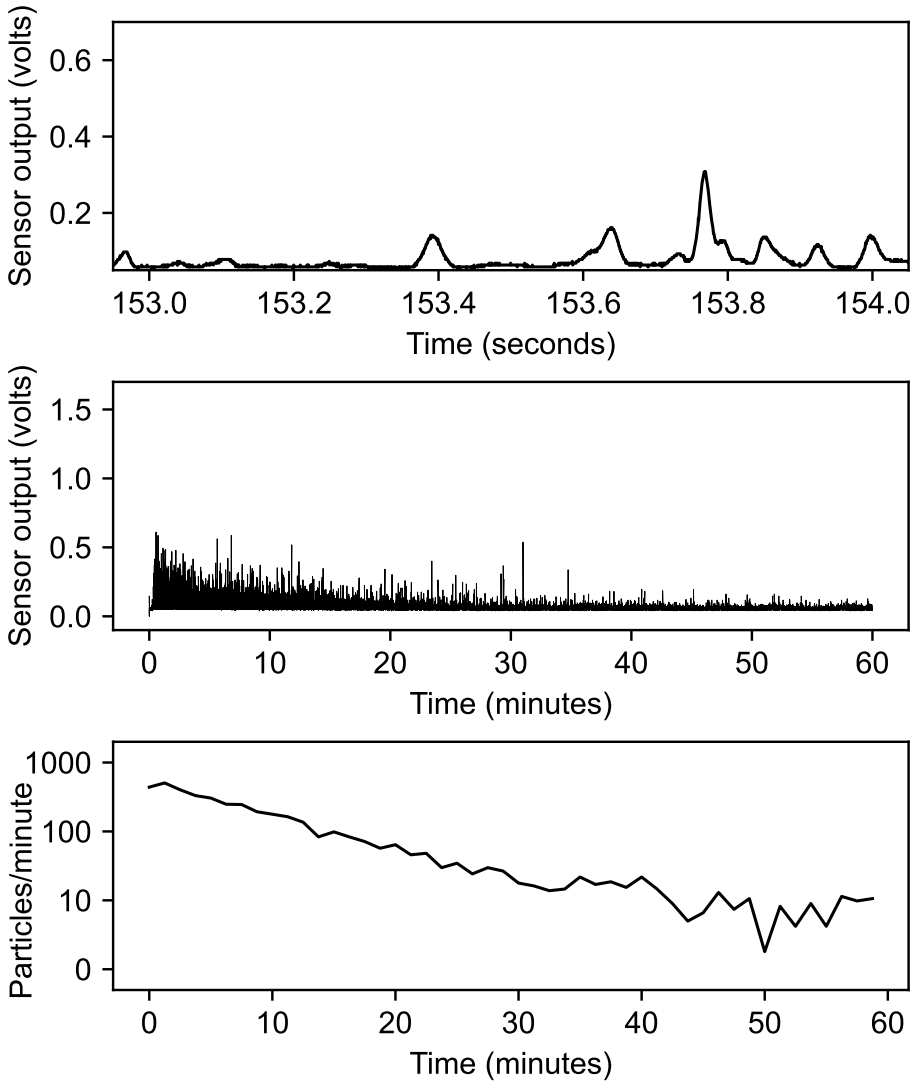
[picture p229: page 1]
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
