groverlab/disintegration-fingerprinting/data/bayer_tylenol/512 20251125T093826_A18one ART.json.gz.pdf

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

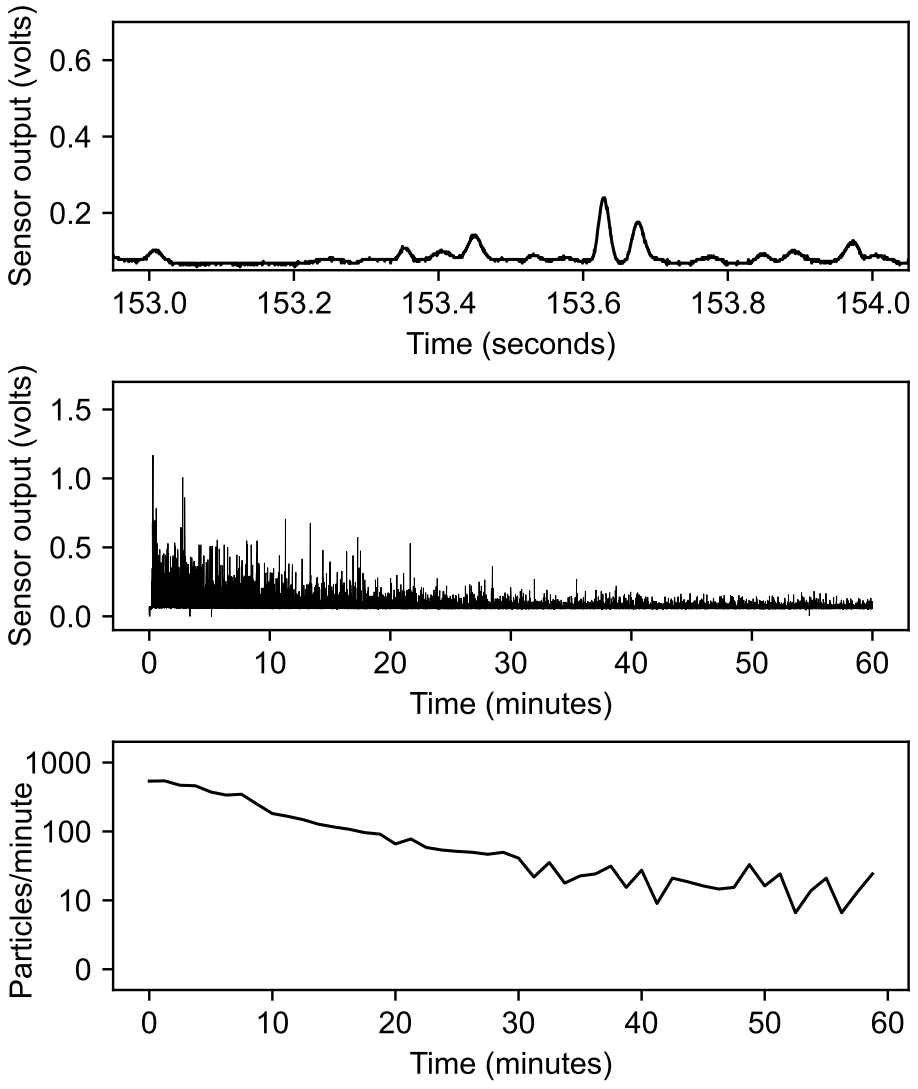
[picture p230: page 1]
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
