groverlab/disintegration-fingerprinting/data/bayer_tylenol/513 20251029T115335_A02one ART.json.gz.pdf

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

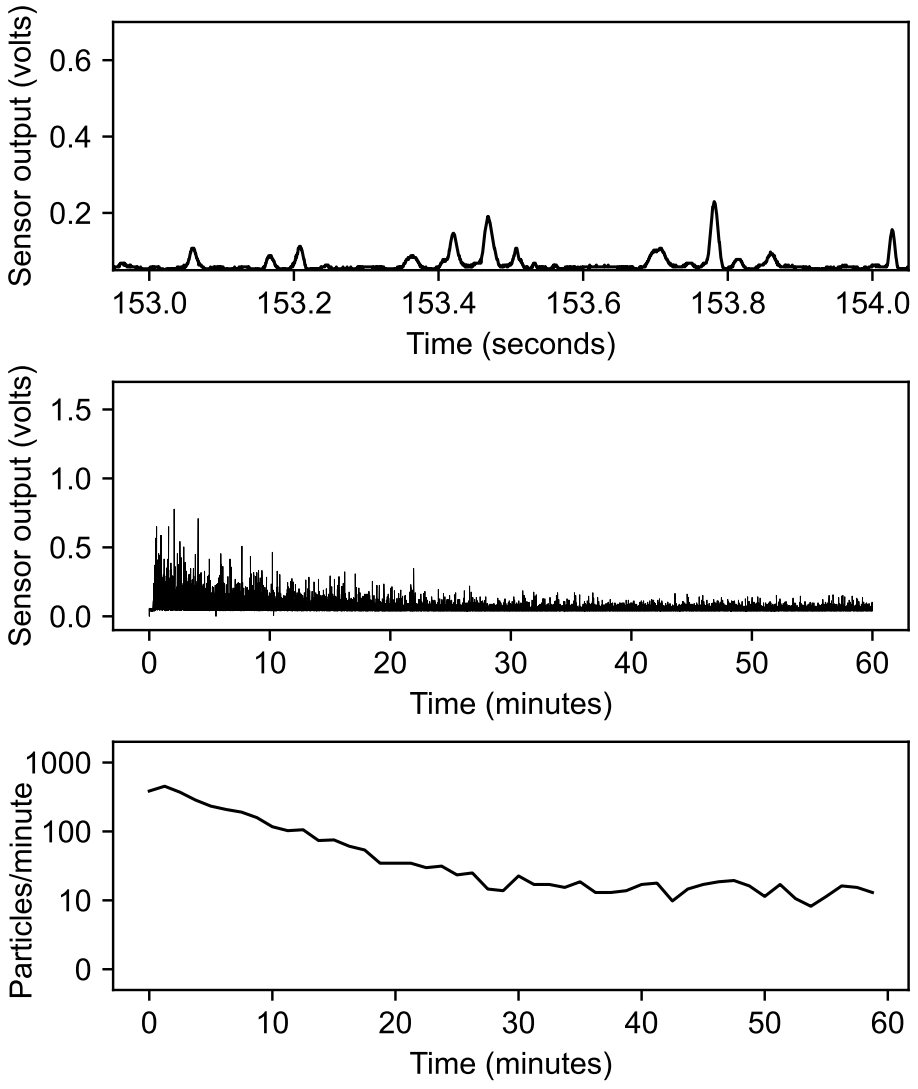
[picture p231: page 1]
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
